tomassasovsky/segno/docs/code-review/fx-design-alignment/review.md

# FX design alignment review

Base: `6646086a5be2e7c9135b4f01fd0464e316154082`.
Scope: two presentation files and six reviewed screenshot baselines, plus plan
and this record. The implementation adds nine net production lines.

Independent review read the complete source change, traced the fixed-canvas
constraints and unchanged pages, and compared all six candidate images with
the accepted Current UX Pen frames. A separate render used the complete bundled
catalogue. No actionable finding remains in this scope. Leading controls retain
their label constraints; actions reach the right inset; only the library artwork
grid is centered. Existing scroll ownership and My presets geometry remain.

Reviewed production SHA-256 values:
- `fx_page.dart`: `600ef9a996370b7b68edfea4cb823a4cc9db3b2d040eb193032fcadd9f24305c`
- `fx_library_page.dart`: `e1b4ac0d3c2e7cbb04936d7b0df2e91ceb75f2f6224945bef6ff3045594cc11a`

Validation: 81 existing FX behavior tests and all 11 author screenshot cases
pass. The complete app suite passes 2869 tests with six skips; strict analyzer,
explicit formatter and Bloc lint (789 files) are clean. Only the six inspected
baseline images changed. CI remains a separate current-head gate; author images
depend on local fonts and do not constitute appliance validation.

The campaign's requested additional Claude review remains outstanding because
its session limit prevented a verdict. Keep that review gate pending. These
results certify the bounded horizontal correction, not a theme-wide redesign.
