tomassasovsky/segno/docs/code-review/design-midi-controls-restack/review.md

# MIDI bug-focused review

## Current correction binding

The reviewed test-only correction builds on published head
`1c7c07ebbce9ed87130e9484d259aed05cc7f616`. Its independent source and five-role
review is clean; the single timing-fixture finding was fixed with deterministic
capture timestamps. All application/native bytes below are unchanged.
The effective manifest fingerprint is
`755a00187a8e6064d218fd552e9581513249d160c9108d3dcf145dc255c3f936`.
The ordinary app run passes 2,306 tests and 90.0039% coverage, with static gates
clean. The original 89.07% CI failure remains recorded; new published-head CI
must pass before readiness. See [verification](../../reviews/design-midi-controls-restack/verification.md).

## Original application/native review

Base and current Git HEAD: `1ef7fb30abd328b86ac481ec71e72c9bbc59e83c`. Reviewed the intended working diff and untracked product files, then all repair and fixture deltas. Exact hashes, fingerprint and the complete scope are in [the source report](../../reviews/design-midi-controls-restack/source-review.md#reviewed-file-binding). A later commit must be bound to these bytes.

One independent reviewer performed source inspection and the five quality roles sequentially; this is not five independent reviewers. No tests, product edits, delegation or UI automation were performed by that reviewer. Root and the independent adversary supplied execution evidence.

The local source and quality gate is **clean** for the exact 134-path manifest fingerprint `3cb49b9c0e522f35d7275b5b58a6a30095a4f8350c161796bb48f3806c2be705`. All eleven functional findings and the final future annotation are resolved; no actionable finding remains. Final app, package, native and static evidence passes. Published-head CI and final commit binding remain separate, pending gates. No ready-to-merge, merge or deployment claim is made.

## Findings

Eleven actionable functional findings were repaired and independently reread. They covered Mixer Reset ownership, ordinary writers, pending persistence, endpoint editing, capture timing, session-crossing queued work, FX activation authoring, non-held retirement, Stage navigation, stale monitor persistence and pending confirmation disposal. See [repair traces and the removed-invariant audit](../../reviews/design-midi-controls-restack/source-review.md#findings-and-repair-verification).

Completed changed-source/enclosing-function review, cross-file tracing, deleted guard/test audit, failure and lifecycle review, native/FFI parity review, reuse/simplicity review and final fixture assertion review. No functional source finding remains unresolved. No review task was delegated or failed. Scope and physical/visual limitations are explicit in the source report.

The local gate is complete at the recorded manifest. The coordinator must bind the resulting published commit to those bytes; current-head CI is separately required for ready-to-merge. M3 catalogue follow-on and later M4–M6 owners remain incomplete campaign work.
