tomassasovsky/segno/docs/reviews/design-midi-controls-restack/pr-readiness-review.md

# MIDI PR-readiness review

Base and current Git HEAD: `1ef7fb30abd328b86ac481ec71e72c9bbc59e83c`. This is a working-tree review; a later commit requires the coordinator to bind the resulting commit to these reviewed bytes. Exact intended-path hashes and scope are in [the source review](source-review.md#reviewed-file-binding).

One independent source reviewer performed the VGV, architecture, test-quality, simplicity and readiness roles sequentially. These are five review lenses, not five independent reviewers. No delegation, product edits, test execution or UI automation was performed by this reviewer. The coordinator and separate adversarial reviewer supplied execution evidence.

The local source and quality gate is **clean** for the exact 134-path manifest fingerprint `3cb49b9c0e522f35d7275b5b58a6a30095a4f8350c161796bb48f3806c2be705`. All eleven functional findings and the final future annotation are resolved; no actionable finding remains. Final app, package, native and static evidence passes. Published-head CI and final commit binding remain separate, pending gates. No ready-to-merge, merge or deployment claim is made.

## Mechanical evidence

- Source whitespace/conflict checks: `git diff --check` passed; no newly introduced debug print, TODO/FIXME/HACK or merge marker was found in reviewed changed product source.
- Format: aggregate check reports no changes; focused final fixture check also reports five files, zero changes.
- Strict analysis: final run passed with zero issues. The tracked future removed in confirmation cleanup is explicitly `unawaited`, preserving execution without awaiting itself.
- Bloc lint: final aggregate passed with zero issues and an observed positive scan of 703 files; this was not an ignored-worktree no-op.
- Tests: unchanged native/package gates pass. Final app aggregate passed 2,433 tests with six existing explicit skips and 90.857% coverage against a 90% floor. The earlier failed/stalled run was superseded. After the sole annotation-only delta, both disposal regressions passed again.
- History: current HEAD is the External predecessor and this candidate is uncommitted. Commit/PR head binding, issue/label mechanics and current-head CI are coordinator responsibilities after publication.

Transient macOS build edits are excluded/restored. Required screenshot/Pen assets are intentional, and their visual approval belongs to the coordinator's separate evidence. No merge or deployment readiness is claimed.
