tomassasovsky/segno/docs/reviews/design-midi-controls-restack/simplicity-review.md

# MIDI simplicity review

Base and current Git HEAD: `1ef7fb30abd328b86ac481ec71e72c9bbc59e83c`. This is a working-tree review; a later commit requires the coordinator to bind the resulting commit to these reviewed bytes. Exact intended-path hashes and scope are in [the source review](source-review.md#reviewed-file-binding).

One independent source reviewer performed the VGV, architecture, test-quality, simplicity and readiness roles sequentially. These are five review lenses, not five independent reviewers. No delegation, product edits, test execution or UI automation was performed by this reviewer. The coordinator and separate adversarial reviewer supplied execution evidence.

The local source and quality gate is **clean** for the exact 134-path manifest fingerprint `3cb49b9c0e522f35d7275b5b58a6a30095a4f8350c161796bb48f3806c2be705`. All eleven functional findings and the final future annotation are resolved; no actionable finding remains. Final app, package, native and static evidence passes. Published-head CI and final commit binding remain separate, pending gates. No ready-to-merge, merge or deployment claim is made.

## Assessment

The current layers earn their roles: protocol assembly decodes messages, mapping proposals retain per-control admission/cleanup, the application ledger orders accepted targets, and shared persistence projects durable Released values. Combining them would obscure independent lifetime and storage constraints. No generic framework or compatibility path was added.

The unused exported `MidiSignalLevels` duplicate was removed, with no remaining caller/export. Obsolete mapping models, default dispatch and generic Learn UI were removed as requested. Exact holder identities, epochs and pending-save receipts are necessary to prevent reproduced races; their removal would lose behavior rather than simplify it.

No further actionable redundancy or YAGNI finding remains. No LOC reduction target is proposed. Required production fakes, `AudioEngine` interfaces, generated bindings and visual assets are explicitly preserved under project authority. The final future annotation is explicit and requires no broader refactor.
