tomassasovsky/segno/docs/code-review/design-pedal-art-restack/review.md

# M3.7 pedal artwork source review

Complete for the six-file art freeze-v1, fingerprint `447437f12e2729a08b35f081f8f77c85e1871f838af4d2581433e7155ec60ed4`. Critical: 0. Important: 0. Suggestions: 0. No unresolved actionable source finding.

One independent reviewer performed the bug-focused review and all five quality roles sequentially. These are five perspectives, not five independent agents. The author and bounded adversarial reviewer are separate. No product edits, tests, builds, Git mutations or recursive delegation were performed by this reviewer.

## Scope and source binding

Baseline: `170167520c0de2d6a480637393b19a2bda6f594c`. Original PR 1034 source: `ef50473b1704289a8a0daf3178a2368efe8dcca7`. All six frozen file hashes were checked at finalization with no mismatch. The retained setup map and physical legend source match their prior independent bindings. Parent-owned Pen/golden updates and aggregate verification are a separate packet; this source review does not predeclare their result or exact-head remote CI.

Read the full painter before and after the port, the literal JavaScript art source, geometry/label provenance, README, new raster tests, enclosing map and focus/LED ownership. The four study files originally matched the independent original hashes. Final study changes are limited to fresh white RGB FFFFFF in the decorative indicator and documentation identifying the current Flutter host; geometric and label source data remain unchanged.

## Completed review angles

The executable seven paths match the accepted 84×114 study: tapered body, both curved hinges, both rolled edges, quadratic pad and trapezoid nameplate. Exact grip grid is five columns by six rows, pitch 11.6373×12, origin y=39.47, base radius 4, top radius 3.1 lifted 0.18. Hinge, pad and grip strokes and body-before-roll paint order are restored. Selected/unselected material stops and edge widths match the source values.

The existing PedalHardwareFace is the sole renderer. Cached paths are initialized once and never transformed or otherwise mutated. Cached metal and grip shaders are reused; each translated grip has a balanced canvas save/restore inside the outer scale save/restore. The selected flag remains the repaint dependency. No speculative cache framework or public test-only API is added.

The widget's existing label, AspectRatio, layout and theme-based text are retained. Production supplies its proportional 159.16×216 face box inside the larger existing slots. Dynamic numeric labels remain 1–8 in banked editing and 1–4 in physical LED editing; accessible legends remain owned by the enclosing map. Manufacturing-outline lettering parity is intentionally not claimed. Label paint after the decorative grips has no visible ordering conflict because the fitted label remains within the nameplate above the grip rows.

Map bounds remain 1720×566, rear slots 168×216 at x=451/668, y=30 and front slots 201×216 at y=350, pitch=217. Painting adds no focus, tap, controller or repository owner. Existing full-slot hit targets, availability, group selection, warning layout and separate LED pills are unchanged. Canonical activation, local palette preview and mismatched draft-bank suppression remain exclusively in the map.

Removed behavior is limited to approximate rounded hinges and repeated path/shader construction. No guard, gesture path, persistence boundary, native API, protocol or palette behavior was removed. No new dependencies or lower-layer imports appear. The change adds bounded paint work only; no callback/thread/FFI path is involved.

## Evidence and limits

Observed author raster test log: three tests pass, checking actual interior pixel colors, all 30 grip locations and selection changes. This replaces the original PR's insufficient comment-string style of proof. The builder reports clean targeted analyzer/format/whitespace. The initial image-capture stall was a test fixture async issue, retained in its original log and corrected with tester.runAsync; no production workaround was added.

The source review is clean within the six-file freeze. Independent scale/repaint/interaction probes, sensitivity evidence, final visual inspection, Pen/goldens, broader static/tests/coverage and publication-head CI remain parent-owned separate gates. No failing reviewer was substituted by this source review.

Exact raster equivalence to the browser study is not asserted: dynamic font-rendered labels are intentional, and the retained Flutter metal shader spans the art box while SVG object-bounds gradient normalization differs slightly. Geometry, material values and paint order are the bounded parity claim. Generic forced nonproportional sizing is not a new supported requirement; production uses the existing proportional box.

No new CAD accuracy, physical display comfort, hardware touch response, appliance visibility, optical/current or device validation is claimed. `autonomy:merge-gate` remains in force. This report does not authorize merge or set ready-to-merge before exact-head CI is green.

## Coordinator closeout

The final source binding and verification record are in
`docs/reviews/design-pedal-art-restack/`. The separate adversary has completed
all four groups with no findings. The coordinator verified the nine updated
goldens, running app, saved Pen component and note, and unchanged source during
the aggregate run. All local gates above passed; remote CI remains pending
on the published head. This closes the earlier parent-owned pending local
gates without claiming additional independent reviewers or hardware proof.
