tomassasovsky/segno/docs/reviews/design-pedal-art-restack/code-simplicity-review.md

# Code simplicity review

Complete for the six-file art freeze-v1, fingerprint `447437f12e2729a08b35f081f8f77c85e1871f838af4d2581433e7155ec60ed4`. Critical: 0. Important: 0. Suggestions: 0. No unresolved actionable source finding.

One independent reviewer performed the bug-focused review and all five quality roles sequentially. These are five perspectives, not five independent agents. The author and bounded adversarial reviewer are separate. No product edits, tests, builds, Git mutations or recursive delegation were performed by this reviewer.

Purpose: improve the current hardware face's fidelity to the accepted simplified study while preserving current app behavior.

One existing painter now has seven private cached paths and three cached shaders. Small paint helpers express source layering. Shared grip-local shader translation avoids thirty equivalent shader allocations per face; no cache invalidation system or speculative abstraction is added. The current dynamic label widget is retained rather than importing static manufactured outlines that cannot label bank B.

No justified removable lines or duplicate renderer were identified. Estimated removable LOC: 0. Complexity: low; the increased path data directly implements accepted outlines and remains separated from interaction. Already minimal for this scope.
