tomassasovsky/segno/docs/code-review/design-pedal-led-restack/review.md

# M3.5 source and quality review

Bound to freeze-v2 fingerprint `57dcdae120419b771c9bf8ad43d7cd9c976ccaf39ce28a7cf18e884c78ffef2c` (69 paths); base `3e67d031148f21eb9c3ee99a961f6ca4587dbc3b`, intended merge parent `424e12d0e53a969f8887089be0ea9450404be969`. All source hashes were independently compared with the frozen packet and match. One implementation-independent reviewer performed source review and all five quality roles sequentially; the roles share a reviewer and are not five independent reviews. No implementation edits, tests, builds, staging, publishing or hardware operations by this reviewer.

## Result
No unresolved actionable source findings in the frozen diff. All source angles and all five quality roles completed. Source and local software review gates are clean. All aggregate/static/coverage checks and independent adversarial probes pass on the bound frozen candidate. Exact published-head CI and merge authorization remain owned by root.

## Reviewed scope and evidence
The complete intended working-tree diff, new test/stub files, binary fixtures, screenshot goldens, surrounding state/gesture/repository callers and removed invariants were inspected. Accepted behavior§4, the pinned PR1079 renderer architecture and frozen independent oracle governed the review. Exact reviewed paths/hashes are in source-binding.json.

Line-by-line scan, removed-behavior tracing, cross-file API/serialization/UI flow, reuse, simplification, efficiency/lifetime, mechanism depth and project conventions are complete. Exact8 HELLO admission, STATE51/frame55, all-ten raw RGB plus LE16mask, old field validation, bounded parser capacity and unchanged CTRL/HELLO formats are consistent in C/Dart. No fallback or incompatible historical layout is accepted. Frame inputs are detached, physical output follows only the mask, and goodbye dominates activation.

The renderer is directly compared with PR1079 ecea3af76fdb0708ca04632e260de5aa3fde09cd. The whole40pixel sustained ring, limits, pin map, CTRL, encoder and DMA boundary are retained. Intended differences remove Song/local-contact/idle-breathe pill inference, consume host hues/mask and change firmware metadata. NeoPixelBus2.8.4 sending/editing buffer ownership was inspected directly; stack desired colors do not escape and DMA cannot read overwritten editing data. Current limiting rebuilds from source pixels and forced refresh cannot progressively dim. No audio callback/native/FFI change is in scope.

## Findings resolved during review
- Refused Custom transport actions formerly recorded completion/contact before dispatch. Actual synchronous or awaited admission now gates identity/contact, with per-button tokens preventing delayed results from attaching to another contact or invalidated configuration/session.
- Disconnection formerly published raw held contacts before clearing them. Raw/accepted contacts and clear state now clear before projection; reconnect does not replay held LEDs.
- Accepted Layout A originally lit the selected edit pill and never consumed the frame. Repository frame publication through PedalCubit now supplies the actual map, preserving selected decoration independently and guarding draft-bank mismatch.
- During admission repair, normal Undo and supported FX Stop pathways were rechecked. FX panic/binding/Restore Hold and Mute Stop now use actual outcomes for contact LEDs, including refusal tests.

## Quality roles
See vgv-review.md, architecture-review.md, test-quality-review.md, simplicity-review.md and pr-readiness-review.md. All report Critical0/Important0/Suggestion0; readiness limits are explicit. Roles share this one implementation-independent reviewer.

## Limits
This reviewer ran no tests/builds and changed no implementation. Builder/root logs and independent adversary evidence are attributed accordingly. Desktop source/tests/Arduino compilation cannot establish electrical current, real timing or optical appearance. Palette add/edit/reuse/persistence remains1032. No flash/deployment/merge is authorized by this report.

## V2 fixture rebind
The first full run exposed one obsolete positive Clear-LED fixture using an empty rig, and strict analysis found one cascade style issue in a new repository test. Reviewed exactly two test-only changes: positive Clear now has a real48000-frame track and a separate empty-rig case asserts darkness; the repository cascade preserves call order/behavior. Every production source hash is unchanged. All69v2packet paths match. Prior failures are retained in verification-v1; complete v2 gates pass. Root's native-app author journey also confirms real Layout A live state, distinct edit selection and draft-bank isolation; it is not independent hardware evidence.

## Final observed verification
Read exact result logs and independently rechecked all69frozen hashes at finalization; no drift. Root verification-v2/dart-result.json reports complete app tests exit0/semantic pass in86.7s and pedal_repository exit0/semantic pass in4.4s. Coverage-results.json records app19860/21794=91.126% against90% and pedal563/576=97.743% against96%. Static-results.json records explicit formatter, fatal-info analyzer, Bloc and whitespace checks all exit0/semantic pass; Bloc log confirms0issues across665files, with the path alias bound to the intended checkout. These were root-run, not repeated by this reviewer.

Read the separate adversary's final review and binding: one C literal executable, one actual-sketch pixel executable, two Dart codec/value tests and eight app/repository cases pass; no unresolved findings. Production hashes remain unchanged, with the two reviewed test-only amendments rebound to v2. That reviewer discloses one corrected close-await harness issue separately from product behavior. Exact source, result and receipt hashes are in source-binding.json and verification-binding.json.

The local source/software gate is clean for this packet. Current-head remote CI is not claimed before publication; merge-gate and actual hardware limits remain unchanged.

Final test totals:2346app tests passed with6existing skips;213pedal_repository tests passed. No added skip hides the changed behavior.
