tomassasovsky/segno/docs/code-review/design-custom-runtime-restack/review.md

# M3.4 complete source bug review

Base `cce88c32d03538c61bafeb64d89369b5aef708ac`; incoming intent `27efe48a9ca3871c85b4e307e3638fd20a49b604`. Reviewed the final 46-path M3.4 working candidate bound by freeze-v2 fingerprint `db724af132b964dde4e1ee883765f05b2bdc5e65022b7ffacba77339e502db12`. All paths reconciled without drift. One independent non-author reviewer performed the five quality roles and bug pass; these are not five separate reviewers. Earlier native/package authorship is outside this delta. Product source, tests and Git were not edited by this reviewer.

Verdict: no unresolved actionable findings in the bounded final source. The full bug pass is complete for this candidate.

Completed line-by-line changed-hunk review; removed-guard/invariant tracing; cross-file UI, model, gesture, mix, repository and wire caller tracing; lifecycle/error/bounds review; reuse and simplification; allocation/queue-efficiency review; fix-depth and AGENTS convention checks. No native callback or FFI change exists in this delta. The separate adversary's 16 real-pump/shared-owner cases pass and its final binding reconciles to the frozen runtime.

Candidates resolved before completion:

- Separate all-track Solo admissions could refuse later tracks. Shared coordinator queueing now submits the group together; repeated and overlapping group toggles retain parity and ordering with GUI Solo/Clear.
- Completed selected targets could remain pinned after release. Current projection retains the fired target only through contact, then resolves selection again. Transport feedback is contact-only; Hold retains its own function identity.
- Newly exposed Custom recovery actions could collide with a long header warning. Warnings now occupy the gap between pedal rows; the combined recovery regression verifies bounds and reachable actions.
- Restoring a cleared Custom map could discard later Track-controls edits. Restore now replaces only Custom assignments; the cross-context regression preserves the newer edit.

Preserved current contracts include fresh Mute/Custom defaults, explicit saved FX doors, fixed immediate Custom Exit/Bank, inert unavailable actions, fire-time bank/selected targets, current-session cancellation, exact setup Save/rollback, normal immediate transport and existing FX held-release ownership. Unsupported later functions remain unavailable. Six setup images and the saved design annotation were independently inspected; hardware and whole-product visual acceptance remain outside this source gate.
