tomassasovsky/segno/docs/reviews/shared-record-timing/raw/architecture-f1-f4-delta-v1.md

# Architecture delta review — F1–F4 and final App retry

Sequential read-only perspective by the same reviewer as the VGV/simplicity/test-quality delta reports; no distinct-person claim. Base `8749688c51912f808c3f36d4eb5bca665ede3ade`. Runtime fingerprint `f2af6a80afaaa6b13c8b0e63881d3da8c23ad121db7b686f4cb3ee1c66eeca2d`; root App/test SHA-256 `b5b3f55449a0263109823971811559f5f367210b8f65fbb0947da0a5de04d131` / `0d0860b325f8180abfd2eda1f196a7220e7a8c6e6657d190d199fef2d2edf977`. Exact private binding: `quality-f1-f4-delta-binding-v1.json`. No execution or edits.

**No new architecture violation in the changed seams.** `ControlCubit` remains the only MIDI/External dispatch ledger; `ControlCleanupPending` is a typed result of its retirement gate, not another owner or persisted state. The App interprets that result only in its Power Off orchestration: it recovers owners then requires the same controller gate again. `RecordTimingCubit` still owns storage and native settlement; F1 corrects its flush result without moving writes to presentation. `LooperRepository.record` now refuses an ineligible fresh acquisition before composing plugin state, and the native preflight remains the final callback/producer boundary. F2 changes only a native test, not native production APIs or memory ownership.

Root's toast change reads its already-owned `PowerOffCubit` phase and leaves the error logged. It neither reaches a data client from presentation nor makes toast state authoritative for the transaction. The shared App provider graph and Session lock order are unchanged by these repairs. The separately bound App source is the final v8 toast-lifecycle revision; the earlier e3b7059e App read is superseded. Its power-state subscription is disposed with the App state. Product/native test execution and published CI remain outside this source review.
