tomassasovsky/segno/docs/reviews/design-fx-surfaces-restack/raw/architecture.md

Independent reviewer: m2_fx_native. Base: a52fe34d42a719624762f7756518a7e54cf7fd0c. Bounded scope: changed lib/** and root test/**. This reviewer authored package/native work and expressly excludes all packages, generated FFI and manifests from independent-review credit. Domain/native contracts were read only to trace UI callers. No repository edits, broad test/build runs or screenshot generation were performed in this review phase.

Final source binding: final-v4-hashes.json, SHA256 731cf62a54934b392970384f4c56545bda4c700d1f0d0227560f0ca8f4cf6486. Initial, intermediate and final source snapshots/diffs are retained; all production/test deltas were reconciled. Key hashes: Bloc 24fe22ba, FxCubit eef07fb9, FxPage 9555caad, Monitor 5169080c, Event d073149b. Broad release checks and exact-head CI are root-owned and are not implied by this bounded review.

# Architecture review

Verdict: no unresolved actionable finding in the final bounded UI architecture.

FxDestination distinguishes live input, recorded lane, whole track, All tracks and output identity. Structural edits dispatch through their established Cubit/Bloc owner; the UI does not call AudioEngine. Output startup restores complete envelopes, session mapping keeps per-bus keys, and synchronization clears obsolete destinations. Structural persistence remains gated on exact recipe settlement. Stable slot IDs drive control resolution rather than falling back to a different slot index.

The Add transaction composes from the current repository chain, refuses overflow atomically, and opens only its fresh acknowledged identity after projection. Its original projected generation remains attached to the operation; the existing Bloc exposes only a boolean liveness predicate. The temporary FxCubit repository dependency and helper are removed; original page construction remains intact. No extra stream, state store or persistence owner was introduced.

Review/ack-lifecycle/result.json supplies six independent actual-pump setChain lifecycle groups. Review/append-lifecycle/result-v2.json supplies six append groups, including the unchanged formerly failing full-chain oracle and authoritative monitor-composition neighbor. Native pump remains 31ebe531...; this reviewer inspected those reports, not reran their probes. The final lifetime amendment leaves confirmed setters, append guards and recipe receipts unchanged. Exact reconstruction hashes in final-predicate-amendment.json and final-monitor-amendment.json prove this; the predicate adds a closed-Bloc guard and Monitor amendments are comments/ignores only. FxPage is byte-identical to the passing append-probe source. Final navigation source and widget cases were separately reconciled here.

Final reconciliation: root confirmed the source freeze. All bounded production/test deltas, including the new stale-at-library-open regression, were reread and final-v4-hashes.json matches current files. Root reports the live Mac journey now opens newly added single/rack editors directly and Stage returns to Mixer with the tray closed. That is root journey evidence; an earlier pre-hot-reload 91px RenderFlex warning remains separately recorded, so this report does not claim universal viewport validation. Final static evidence is complete: explicit 649-file format check, strict analyzer, actual 649-file Bloc lint and whitespace checks all pass, with no source drift. The final focused run passed 190 tests. Root's explicit full-app reuse amendment preserves the earlier 2,229 passes, six existing skips and 91.07% coverage; no rerun of that entire suite on final bytes is claimed.
