tomassasovsky/segno/docs/reviews/design-fx-surfaces-restack/raw/common-files-review.md

# M2.6 common configuration and screenshot-fixture review

Base `a52fe34d42a719624762f7756518a7e54cf7fd0c`. Read-only review of `.github/cspell.json`, `.github/workflows/main.yaml`, root dependency manifests, app engine fake and the changed root screenshot Dart fixtures. Exact hashes and removed/golden inventory are in `common-files-source.json`. No tests, screenshots or implementation edits were performed in this pass.

No actionable finding in this bounded scope. Whole-candidate readiness remains pending final app/UI review, strict static/full app gates, root visual evidence, exact commit binding and current-head remote CI.

- The new `fx-catalogue` CI job targets `packages/fx_catalogue`, uses the same Flutter version as root/domain jobs, keeps the reusable workflow and enforces 100% coverage. Disabling Bloc lint for this data-only package is consistent with the other repository jobs; no root lint/test/coverage gate is weakened. The observed catalogue v2 result is semantic pass, 21 named tests, 88/88 covered lines; saved LCOV hash matches the result. This verifies local evidence, not the not-yet-run current-head remote job.
- Root pubspec and lock add only the local catalogue dependency. The package asset declarations already reviewed include all selector/strip/footswitch/stomp directories and the nine preset families. Added spell words are narrow terms/asset slugs; no additional file exclusion or disabled spelling rule was introduced.
- The engine fake now keys all output types/counts/params/power by bus, removing the prior silent no-op for nonzero buses. Existing separate atomic-recipe fake behavior is unchanged. This improves address fidelity; the fake remains a unit-test seam, not evidence of native rendering or admission. The independent four-output PCM probe supplies that separate evidence.
- Control-center/settings fixtures replace the old master accessor with output bus 0 and supply All-tracks/per-output state. Explicit outputBusCount keeps the fixture coherent. The obsolete chainEntriesAt mock is removed; current address-specific getters remain stubbed. No assertions for surviving controls are removed in these hunks.
- Seven deleted Signal golden cases correspond to the intentionally retired Signal destination, its stage tabs and editors. New FX goldens cover Live inputs, Recorded whole track, All tracks, Outputs, direct effect editor, racks/rack editor/options/reorder, My presets and library. Current ordinary FX widget tests cover destination switching, returning to Whole track on track change, fixed All-tracks placement and empty-chain state. This is replacement surface coverage, not a claim that eleven pictures alone preserve every old behavioral test. The other independent UI reviewer owns complete removed-behavior/caller validation.
- `settleArtwork` enumerates displayed Image providers, awaits their precache futures under runAsync, collects and asserts image errors, then pumps before capture. It is used after initial surface loading and newly opened artwork-bearing editors/library/presets. It eliminates a decode-timing assumption without swallowing missing-asset errors or changing expected pixels. New screenshots remain explicitly author-machine/font-gated, like existing suites; they are not represented as portable CI visual evidence.
- Settings recording and surviving control-center golden bytes changed. This pass records those hashes but does not certify their pixels; root visual inspection/final regenerated golden evidence remains required. No screenshots were generated or viewed during this source-only task.

## Domain gate amendment

The final narrow preset decoder catch was included in `verification-domain-final/looper_repository-result.json`: exit 0, semanticPass true, 6.9 seconds; the associated raw JSON run has successful completion and no failed test result, and source-before/source-after match. The earlier failing malformed-row probe remains preserved, followed by the unchanged passing independent replay. The package subset review may now reuse this current-input Looper aggregate. Other packages still require the root's explicit dependency/input reconciliation after the model amendment; no blanket unchanged-input claim is made here.
