tomassasovsky/segno/docs/plan/2026-10-06-feat-pitch-time-core-plan.md

# Pitch and time core: Speed, Transpose, Audio & tempo follow, import Adapt

<!-- cspell:ignore varispeed lerp lbuf wdub Signalsmith signalsmith numer SCHED untransposed sidelobe retiming Retiming retimes retimed retime reclock regrid halfband Neoverse milli fmod crossfades hujm YMPRG Bmpo -->

Status: approved with required review edits E1-E15, which are applied in this
text (the review is kept at the owner's evidence store,
`claude-published-review/1179-plan-review/review.md`). Part 1 is a measured
CPU spike whose numbers gate the rest.
Tracking: #1179 (parent #1026; gap inventory E4-1, serving E6-4 Speed, E6-5
Transpose, E4-2 Audio & tempo, E7-9 import Adapt), `autonomy:merge-gate`.
Source baseline: `origin/claude/segno-integration` at `c3714abc2`. Every
`file:line` below is on that head unless a branch is named.
Precedents: Foot Fade ([plan](2026-10-04-feat-foot-fade-plan.md)), Foot
Reverse (`origin/claude/reverse-plan-1162:docs/plan/2026-10-05-feat-foot-reverse-plan.md`),
the whole-track render boundary
(`docs/design/2026-09-10-whole-track-pre-render.md`), the stem provenance plan
(`2026-10-05-feat-stem-history-replay-plan.md`), the engine reopen plan
(`2026-10-05-feat-engine-reopen-plan.md`), and the July stretch spike
(`2026-07-22-time-stretch-spike-findings.md`).
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
