tomassasovsky/segno/assets/brand/segno-lockup.png

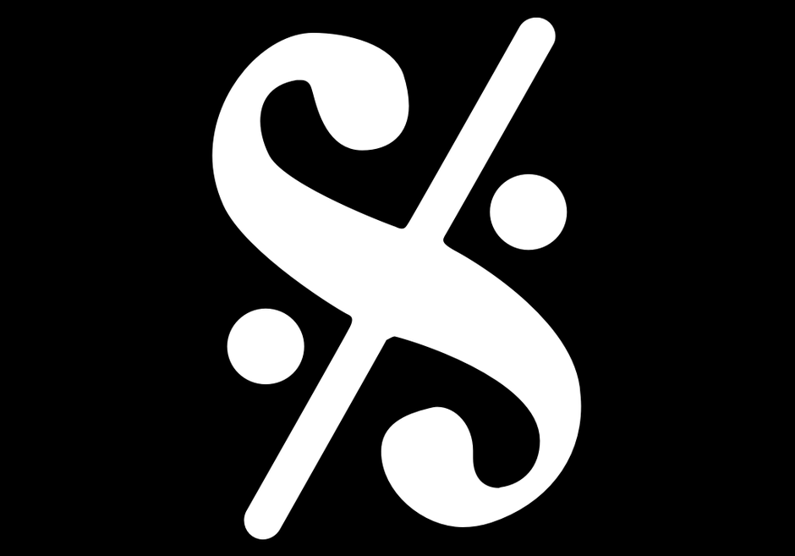
assets/brand/segno-lockup.png
