tomassasovsky/segno/assets/settings/device.png

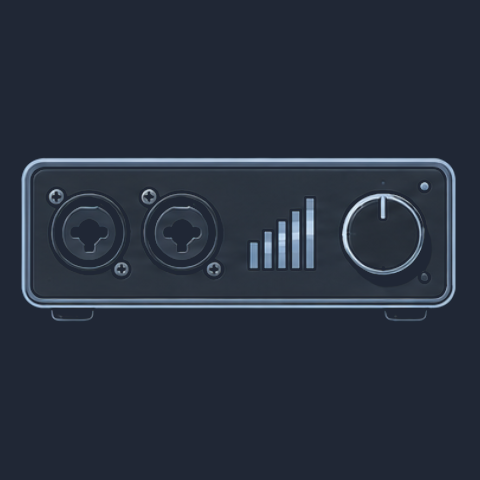
assets/settings/device.png
