tomassasovsky/segno/assets/settings/displays.png

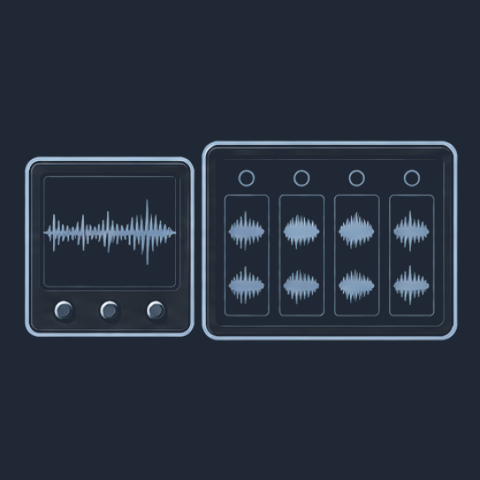
assets/settings/displays.png
