tomassasovsky/segno/assets/settings/effects.png

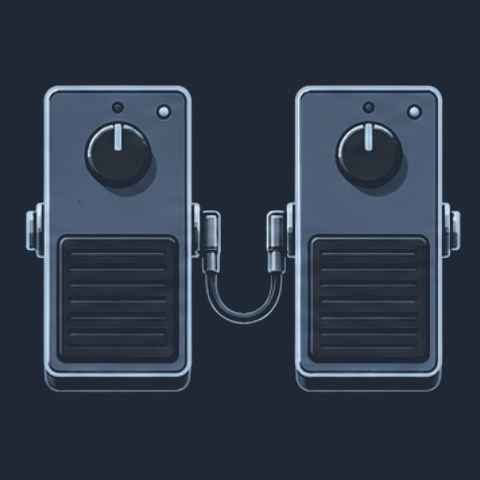
assets/settings/effects.png
