tomassasovsky/segno/assets/settings/loop.png

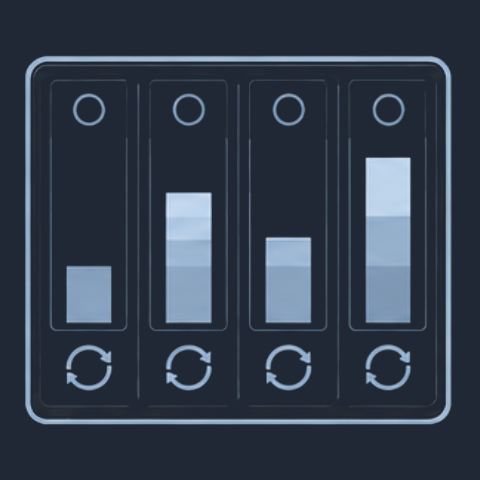
assets/settings/loop.png
