tomassasovsky/segno/assets/settings/midi.png

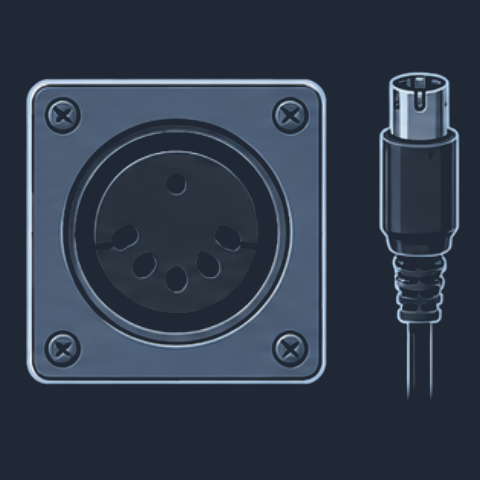
assets/settings/midi.png
