tomassasovsky/segno/assets/settings/network.png

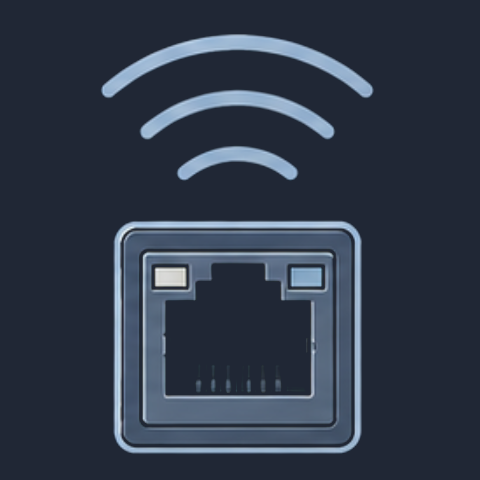
assets/settings/network.png
