tomassasovsky/segno/assets/settings/pedals.png

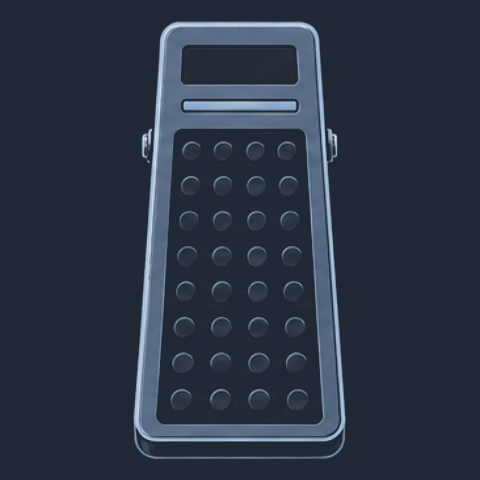
assets/settings/pedals.png
