tomassasovsky/segno/assets/settings/routing.png

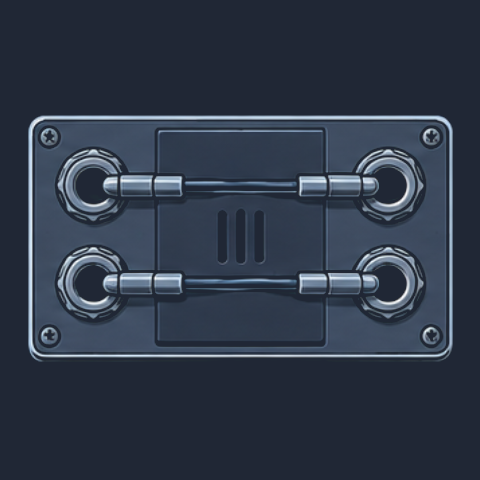
assets/settings/routing.png
