tomassasovsky/segno/assets/settings/storage.png

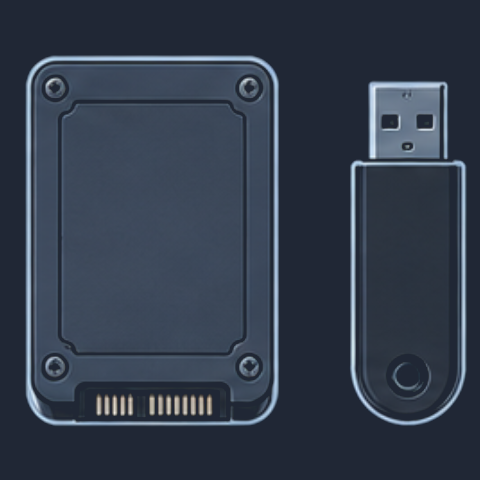
assets/settings/storage.png
