tomassasovsky/segno/assets/settings/updates.png

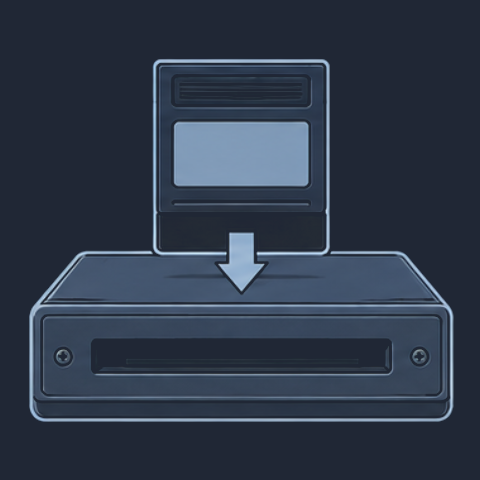
assets/settings/updates.png
