tomassasovsky/segno/docs/design/native-record-start/recording_pedal_off.png

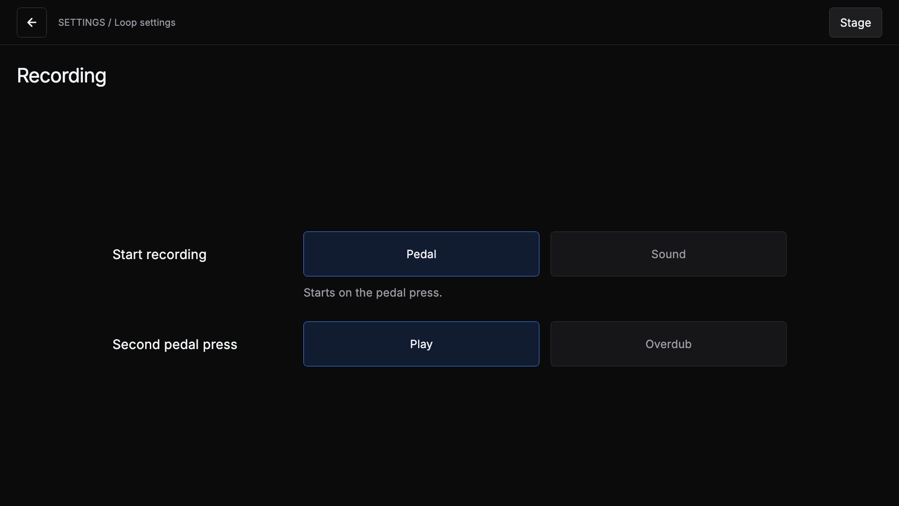
docs/design/native-record-start/recording_pedal_off.png
