tomassasovsky/segno/packages/fx_catalogue/assets/images/footswitch/drum.png

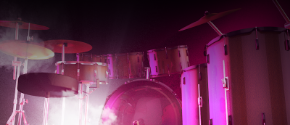
packages/fx_catalogue/assets/images/footswitch/drum.png
