tomassasovsky/segno/packages/fx_catalogue/assets/images/footswitch/dub.png

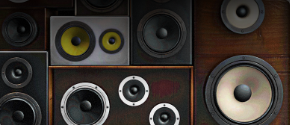
packages/fx_catalogue/assets/images/footswitch/dub.png
