tomassasovsky/segno/packages/fx_catalogue/assets/images/footswitch/edsguitar.png

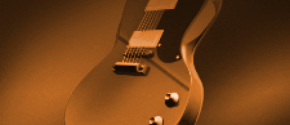
packages/fx_catalogue/assets/images/footswitch/edsguitar.png
