tomassasovsky/segno/packages/fx_catalogue/assets/images/footswitch/guitar.png

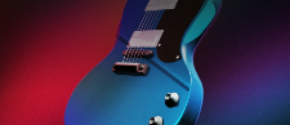
packages/fx_catalogue/assets/images/footswitch/guitar.png
