tomassasovsky/segno/packages/fx_catalogue/assets/images/footswitch/lo-fi.png

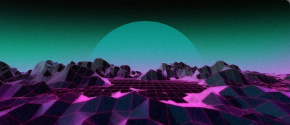
packages/fx_catalogue/assets/images/footswitch/lo-fi.png
