tomassasovsky/segno/packages/fx_catalogue/assets/images/footswitch/rhythmic.png

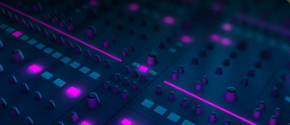
packages/fx_catalogue/assets/images/footswitch/rhythmic.png
