tomassasovsky/segno/packages/fx_catalogue/assets/images/footswitch/studio.png

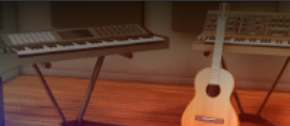
packages/fx_catalogue/assets/images/footswitch/studio.png
