tomassasovsky/segno/packages/fx_catalogue/assets/images/footswitch/vocal.png

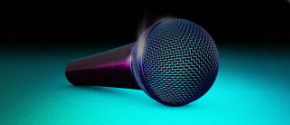
packages/fx_catalogue/assets/images/footswitch/vocal.png
