tomassasovsky/segno/packages/fx_catalogue/assets/images/footswitch/vocaltuner.png

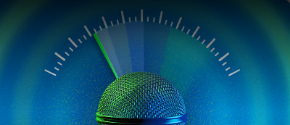
packages/fx_catalogue/assets/images/footswitch/vocaltuner.png
