tomassasovsky/segno/packages/fx_catalogue/assets/images/selector/drum.png

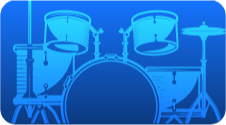
packages/fx_catalogue/assets/images/selector/drum.png
