tomassasovsky/segno/packages/fx_catalogue/assets/images/selector/dub.png

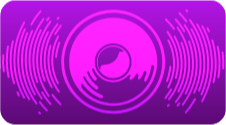
packages/fx_catalogue/assets/images/selector/dub.png
