tomassasovsky/segno/packages/fx_catalogue/assets/images/selector/edsguitar.png

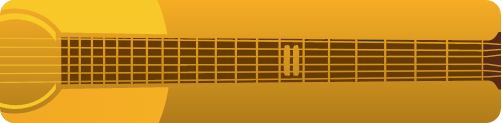
packages/fx_catalogue/assets/images/selector/edsguitar.png
