tomassasovsky/segno/packages/fx_catalogue/assets/images/selector/guitar.png

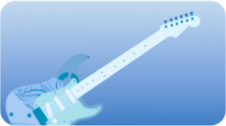
packages/fx_catalogue/assets/images/selector/guitar.png
