tomassasovsky/segno/packages/fx_catalogue/assets/images/selector/lo-fi.png

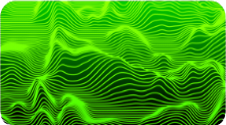
packages/fx_catalogue/assets/images/selector/lo-fi.png
