tomassasovsky/segno/packages/fx_catalogue/assets/images/selector/my-presets.png

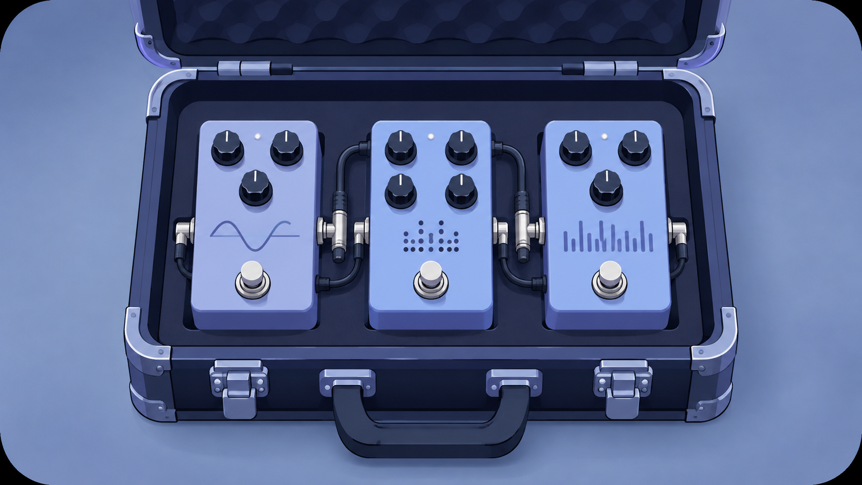
packages/fx_catalogue/assets/images/selector/my-presets.png
