tomassasovsky/segno/packages/fx_catalogue/assets/images/selector/rhythmic.png

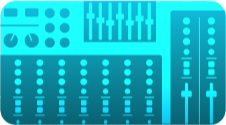
packages/fx_catalogue/assets/images/selector/rhythmic.png
