tomassasovsky/segno/packages/fx_catalogue/assets/images/selector/singlefx.png

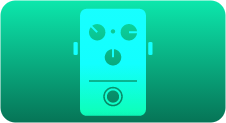
packages/fx_catalogue/assets/images/selector/singlefx.png
