tomassasovsky/segno/packages/fx_catalogue/assets/images/selector/studio.png

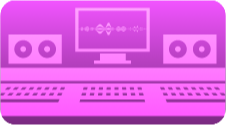
packages/fx_catalogue/assets/images/selector/studio.png
