tomassasovsky/segno/packages/fx_catalogue/assets/images/selector/vocal.png

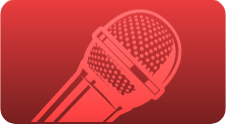
packages/fx_catalogue/assets/images/selector/vocal.png
