tomassasovsky/segno/packages/fx_catalogue/assets/images/selector/vocaltuner.png

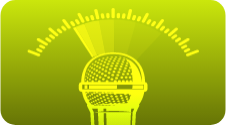
packages/fx_catalogue/assets/images/selector/vocaltuner.png
