tomassasovsky/segno/packages/fx_catalogue/assets/images/stomps/AmbiVerb2.png

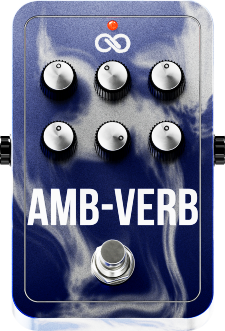
packages/fx_catalogue/assets/images/stomps/AmbiVerb2.png
