tomassasovsky/segno/packages/fx_catalogue/assets/images/stomps/Amp4.png

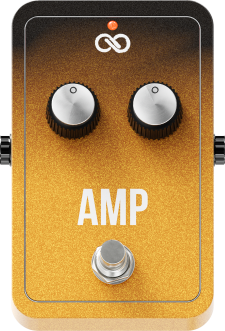
packages/fx_catalogue/assets/images/stomps/Amp4.png
