tomassasovsky/segno/packages/fx_catalogue/assets/images/stomps/Chorus3.png

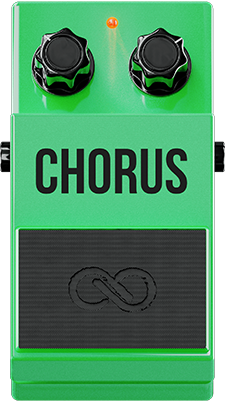
packages/fx_catalogue/assets/images/stomps/Chorus3.png
