tomassasovsky/segno/packages/fx_catalogue/assets/images/stomps/Compressor2.png

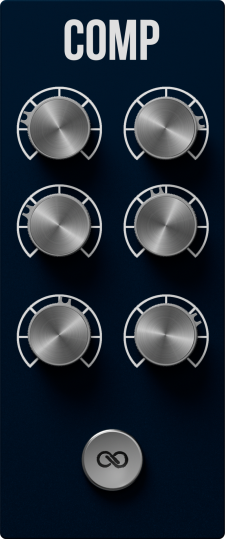
packages/fx_catalogue/assets/images/stomps/Compressor2.png
