tomassasovsky/segno/packages/fx_catalogue/assets/images/stomps/Degrade3.png

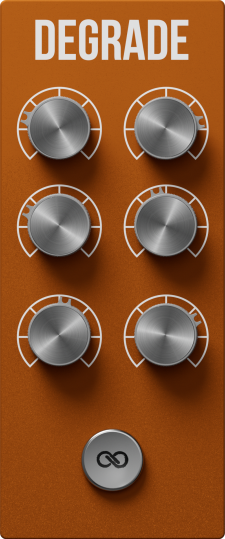
packages/fx_catalogue/assets/images/stomps/Degrade3.png
