tomassasovsky/segno/packages/fx_catalogue/assets/images/stomps/Delay6.png

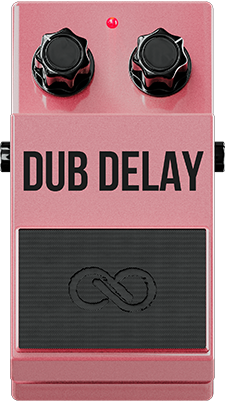
packages/fx_catalogue/assets/images/stomps/Delay6.png
