tomassasovsky/segno/packages/fx_catalogue/assets/images/stomps/Distort1.png

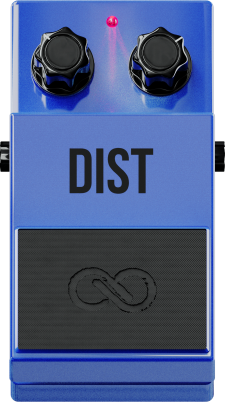
packages/fx_catalogue/assets/images/stomps/Distort1.png
