tomassasovsky/segno/packages/fx_catalogue/assets/images/stomps/Distort2.png

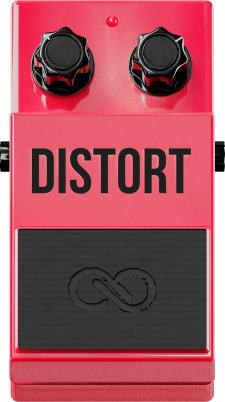
packages/fx_catalogue/assets/images/stomps/Distort2.png
