tomassasovsky/segno/packages/fx_catalogue/assets/images/stomps/Doubler1.png

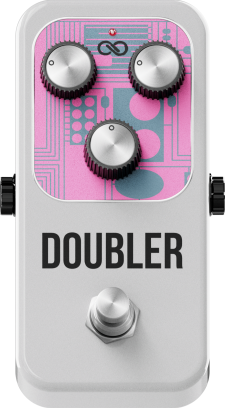
packages/fx_catalogue/assets/images/stomps/Doubler1.png
