tomassasovsky/segno/packages/fx_catalogue/assets/images/stomps/EQ4.png

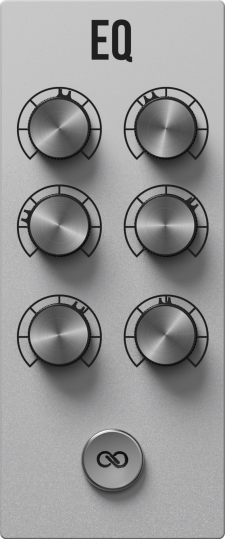
packages/fx_catalogue/assets/images/stomps/EQ4.png
