tomassasovsky/segno/packages/fx_catalogue/assets/images/stomps/EQ5.png

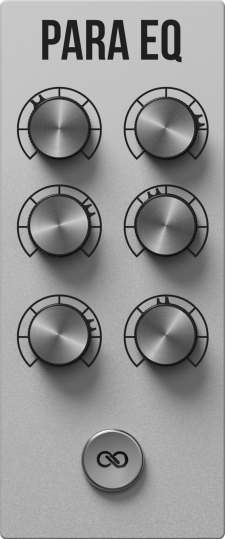
packages/fx_catalogue/assets/images/stomps/EQ5.png
