tomassasovsky/segno/packages/fx_catalogue/assets/images/stomps/Harmonise20.png

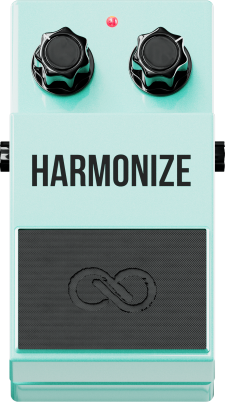
packages/fx_catalogue/assets/images/stomps/Harmonise20.png
