tomassasovsky/segno/packages/fx_catalogue/assets/images/stomps/HPFGate2.png

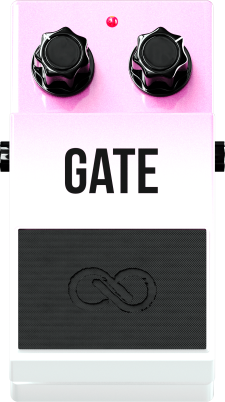
packages/fx_catalogue/assets/images/stomps/HPFGate2.png
