tomassasovsky/segno/packages/fx_catalogue/assets/images/stomps/LPF2.png

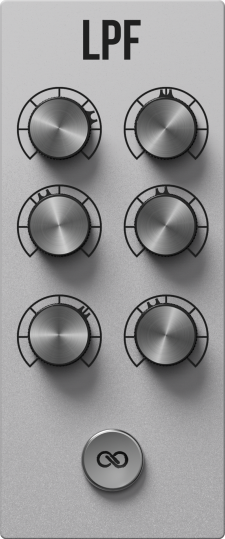
packages/fx_catalogue/assets/images/stomps/LPF2.png
