tomassasovsky/segno/packages/fx_catalogue/assets/images/stomps/Mod3.png

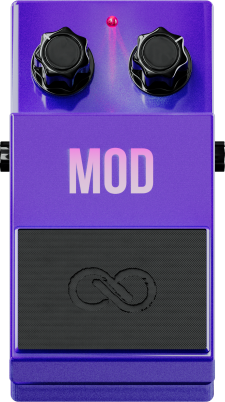
packages/fx_catalogue/assets/images/stomps/Mod3.png
