tomassasovsky/segno/packages/fx_catalogue/assets/images/stomps/Octaver3.png

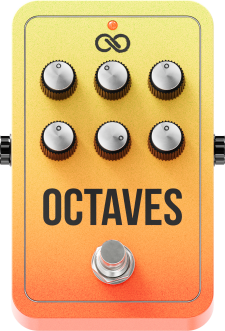
packages/fx_catalogue/assets/images/stomps/Octaver3.png
