tomassasovsky/segno/packages/fx_catalogue/assets/images/stomps/Overdrive2.png

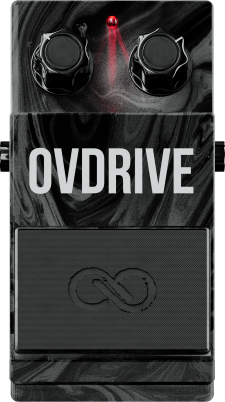
packages/fx_catalogue/assets/images/stomps/Overdrive2.png
