tomassasovsky/segno/packages/fx_catalogue/assets/images/stomps/PitchShift2.png

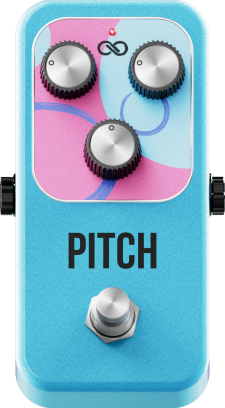
packages/fx_catalogue/assets/images/stomps/PitchShift2.png
