tomassasovsky/segno/packages/fx_catalogue/assets/images/stomps/Pumper2.png

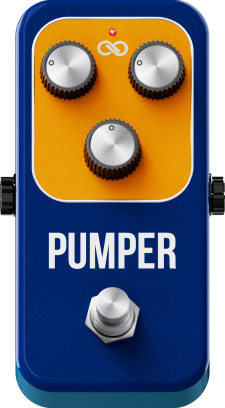
packages/fx_catalogue/assets/images/stomps/Pumper2.png
