tomassasovsky/segno/packages/fx_catalogue/assets/images/stomps/Reverb2.png

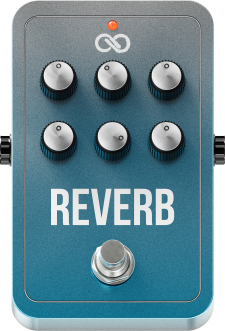
packages/fx_catalogue/assets/images/stomps/Reverb2.png
