tomassasovsky/segno/packages/fx_catalogue/assets/images/stomps/Slicer2.png

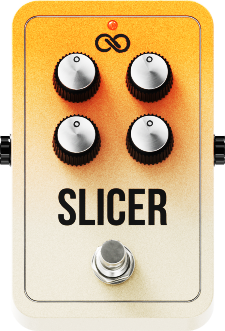
packages/fx_catalogue/assets/images/stomps/Slicer2.png
