tomassasovsky/segno/packages/fx_catalogue/assets/images/stomps/SpringRev2.png

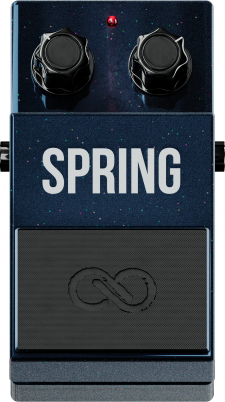
packages/fx_catalogue/assets/images/stomps/SpringRev2.png
