tomassasovsky/segno/packages/fx_catalogue/assets/images/stomps/Transient3.png

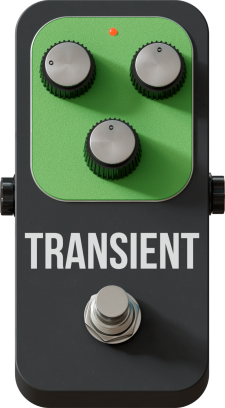
packages/fx_catalogue/assets/images/stomps/Transient3.png
