tomassasovsky/segno/packages/fx_catalogue/assets/images/stomps/Vinyl4.png

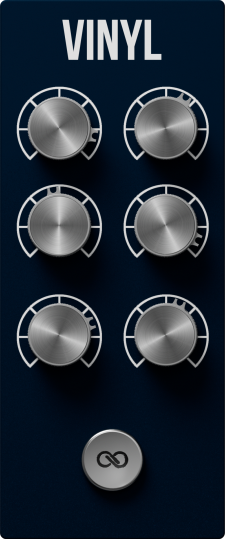
packages/fx_catalogue/assets/images/stomps/Vinyl4.png
