tomassasovsky/segno/packages/fx_catalogue/assets/images/stomps/Wah1.png

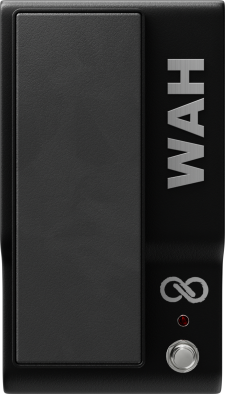
packages/fx_catalogue/assets/images/stomps/Wah1.png
