tomassasovsky/segno/packages/fx_catalogue/assets/images/stomps/Wham2.png

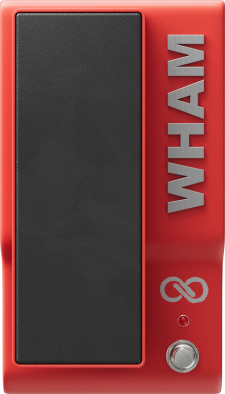
packages/fx_catalogue/assets/images/stomps/Wham2.png
