tomassasovsky/segno/packages/fx_catalogue/assets/images/strip/drum.png

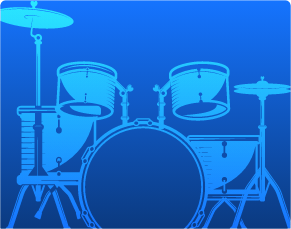
packages/fx_catalogue/assets/images/strip/drum.png
