tomassasovsky/segno/packages/fx_catalogue/assets/images/strip/dub.png

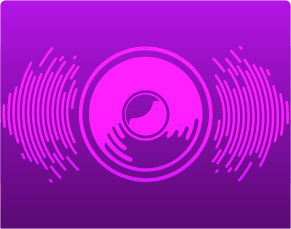
packages/fx_catalogue/assets/images/strip/dub.png
