tomassasovsky/segno/packages/fx_catalogue/assets/images/strip/edsguitar.png

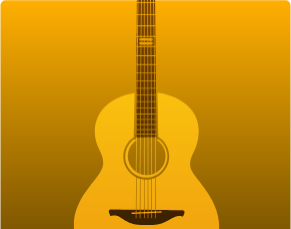
packages/fx_catalogue/assets/images/strip/edsguitar.png
