tomassasovsky/segno/packages/fx_catalogue/assets/images/strip/guitar.png

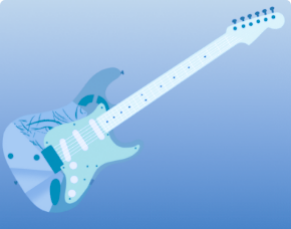
packages/fx_catalogue/assets/images/strip/guitar.png
