tomassasovsky/segno/packages/fx_catalogue/assets/images/strip/lo-fi.png

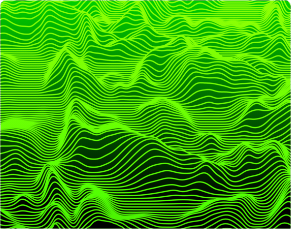
packages/fx_catalogue/assets/images/strip/lo-fi.png
