tomassasovsky/segno/packages/fx_catalogue/assets/images/strip/rhythmic.png

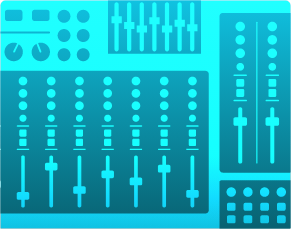
packages/fx_catalogue/assets/images/strip/rhythmic.png
