tomassasovsky/segno/packages/fx_catalogue/assets/images/strip/studio.png

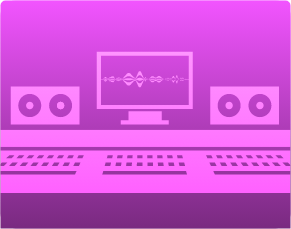
packages/fx_catalogue/assets/images/strip/studio.png
