tomassasovsky/segno/packages/fx_catalogue/assets/images/strip/vocal.png

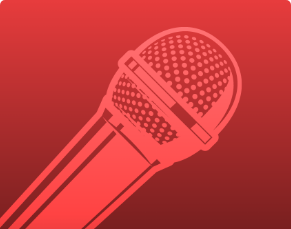
packages/fx_catalogue/assets/images/strip/vocal.png
