tomassasovsky/segno/test/screenshots/goldens/storage_overview.png

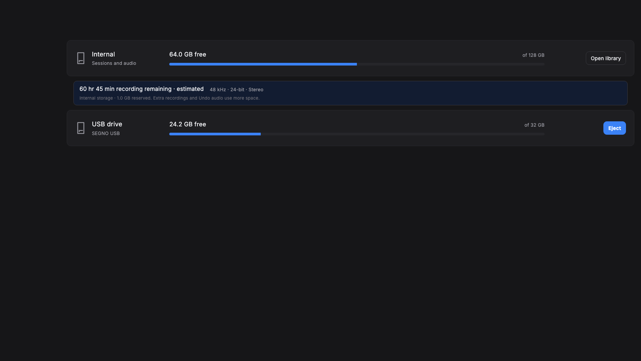
test/screenshots/goldens/storage_overview.png
