tomassasovsky/segno/hardware/enclosure/out/segno_pedal_tile_TRACK2.step

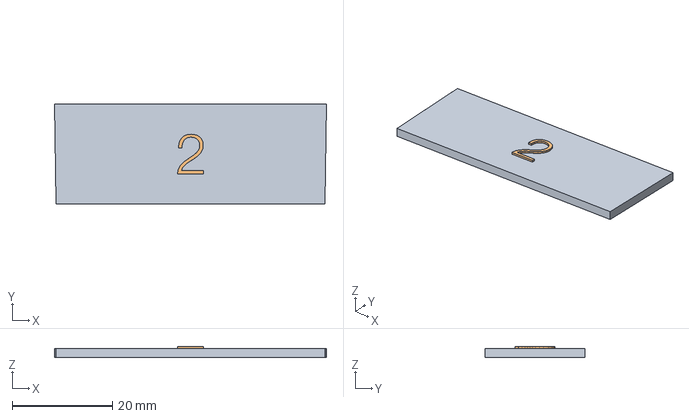
[picture p88: CAD file, 2026-09-04]
hardware/enclosure/out/segno_pedal_tile_TRACK2.step
54.4 x 19.9 x 2.20 mm
