tomassasovsky/segno/hardware/enclosure/out/segno_pedal_tile_CLEAR.step

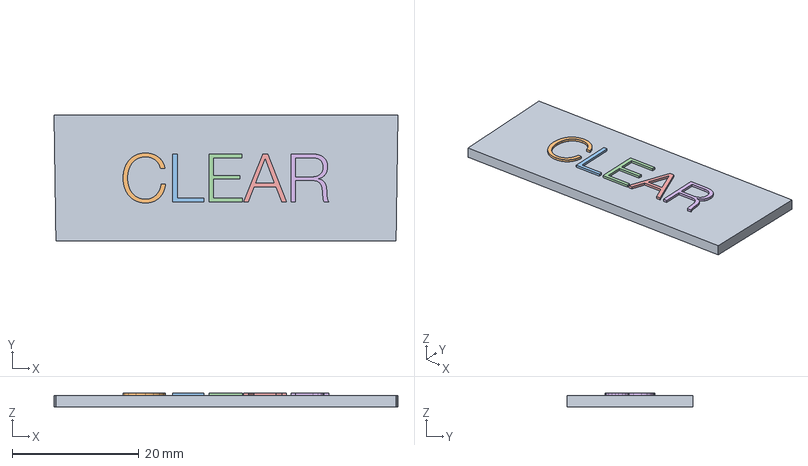
[picture p89: CAD file, 2026-09-04]
hardware/enclosure/out/segno_pedal_tile_CLEAR.step
54.4 x 19.9 x 2.20 mm
