tomassasovsky/segno/hardware/enclosure/out/segno_mini_console_tray.step

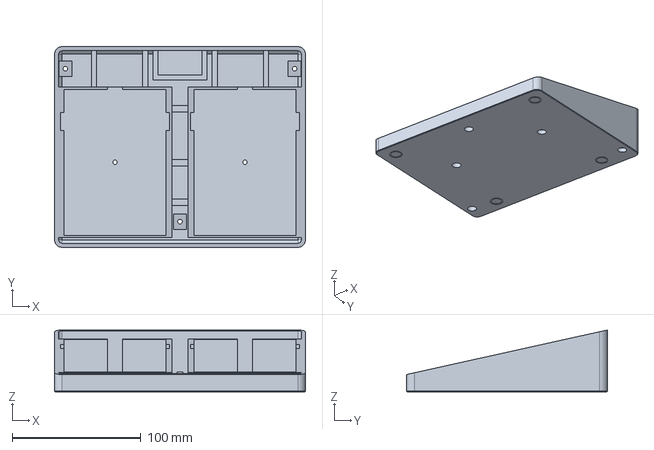
[picture p90: CAD file, 2026-09-04]
hardware/enclosure/out/segno_mini_console_tray.step
195.3 x 156.2 x 48.2 mm
