tomassasovsky/segno/hardware/enclosure/out/segno_screen16_stand_L.step

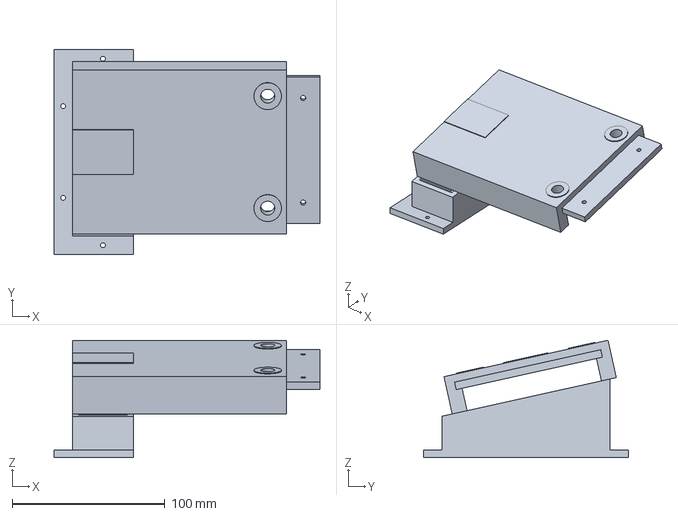
[picture p91: CAD file, 2026-09-04]
hardware/enclosure/out/segno_screen16_stand_L.step
174.0 x 134.0 x 76.8 mm
