tomassasovsky/segno/hardware/enclosure/out/segno_ring_diffuser.step

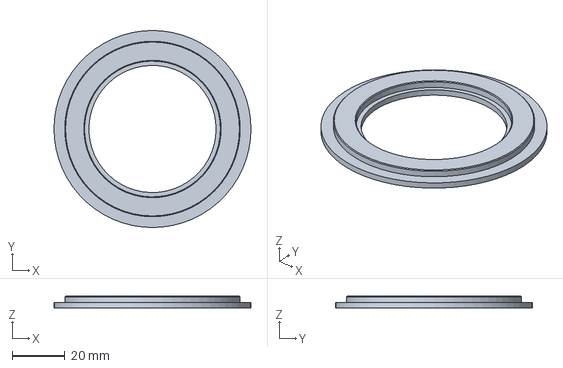
[picture p92: CAD file, 2026-09-04]
hardware/enclosure/out/segno_ring_diffuser.step
75.0 x 75.0 x 4.40 mm
