tomassasovsky/segno/hardware/enclosure/out/segno_mini_console_lid.step

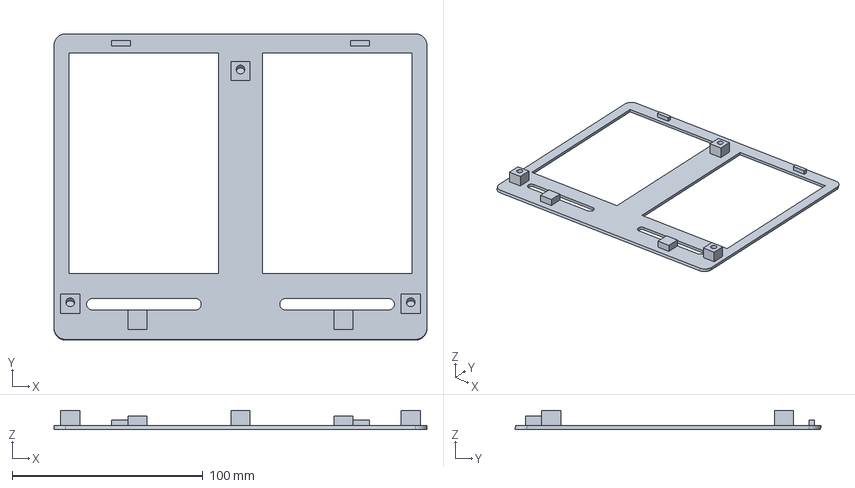
[picture p93: CAD file, 2026-09-04]
hardware/enclosure/out/segno_mini_console_lid.step
195.3 x 160.4 x 10.0 mm
