tomassasovsky/segno/hardware/enclosure/out/segno_pedal_tile_TRACK1.step

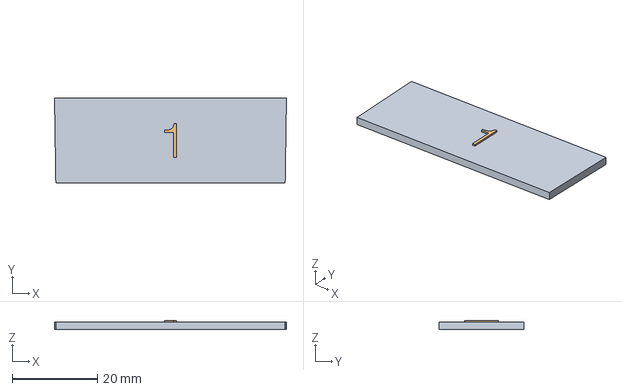
[picture p94: CAD file, 2026-09-04]
hardware/enclosure/out/segno_pedal_tile_TRACK1.step
54.4 x 19.9 x 2.20 mm
