tomassasovsky/segno/hardware/enclosure/out/segno_post.step

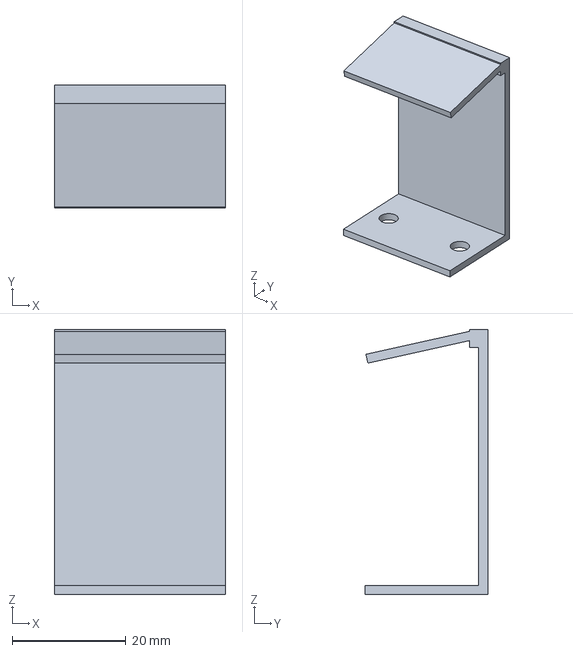
[picture p95: CAD file, 2026-09-04]
hardware/enclosure/out/segno_post.step
30.1 x 21.6 x 46.7 mm
