tomassasovsky/segno/hardware/enclosure/out/segno_ring_disc.step

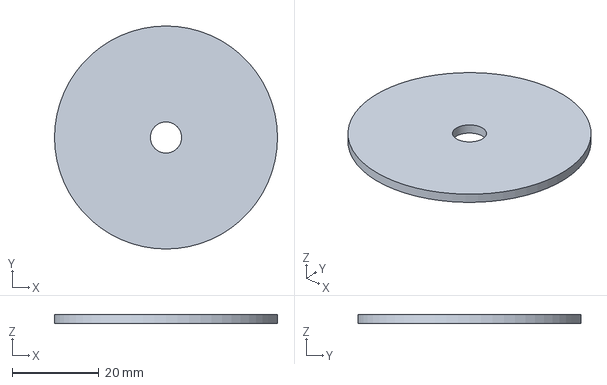
[picture p96: CAD file, 2026-09-04]
hardware/enclosure/out/segno_ring_disc.step
51.5 x 51.5 x 2.00 mm
