tomassasovsky/segno/hardware/enclosure/out/segno_encoder_knob.step

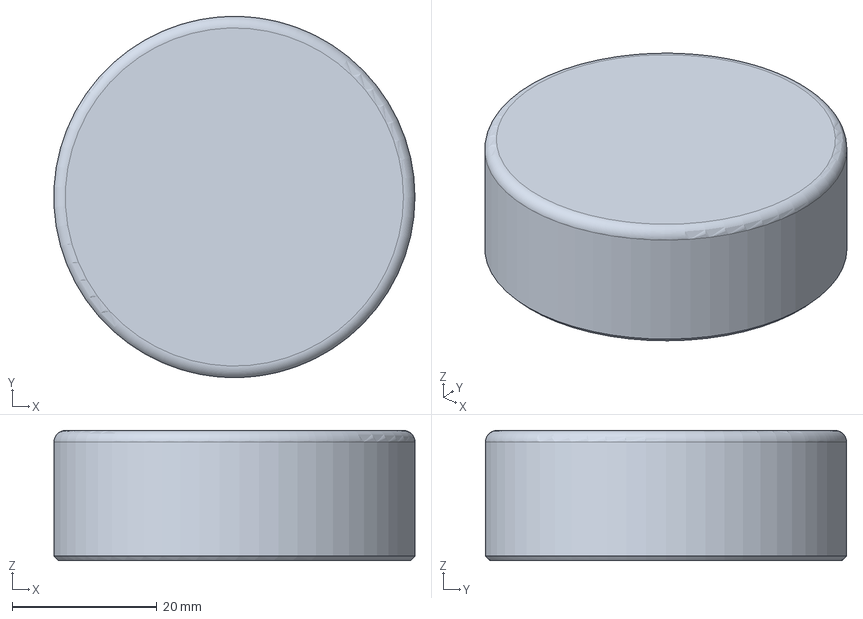
[picture p97: CAD file, 2026-09-04]
hardware/enclosure/out/segno_encoder_knob.step
50.0 x 50.0 x 18.0 mm
