tomassasovsky/segno/hardware/enclosure/out/segno_screen16_stand_R.step

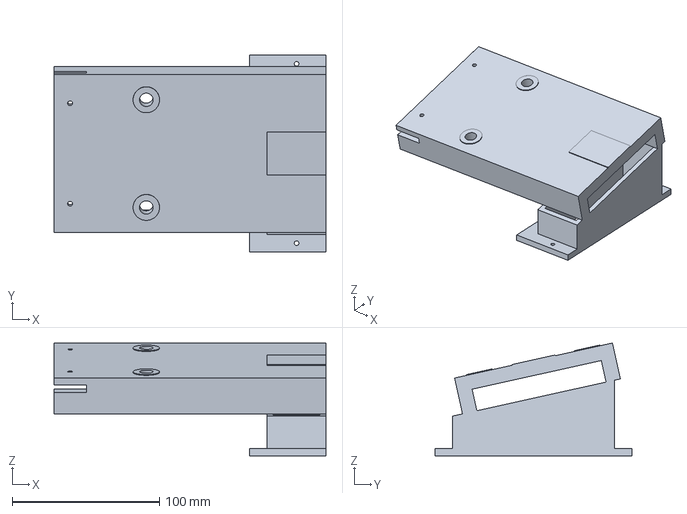
[picture p98: CAD file, 2026-09-04]
hardware/enclosure/out/segno_screen16_stand_R.step
185.0 x 134.0 x 76.8 mm
