tomassasovsky/segno/hardware/enclosure/out/segno_screen7_tower.step

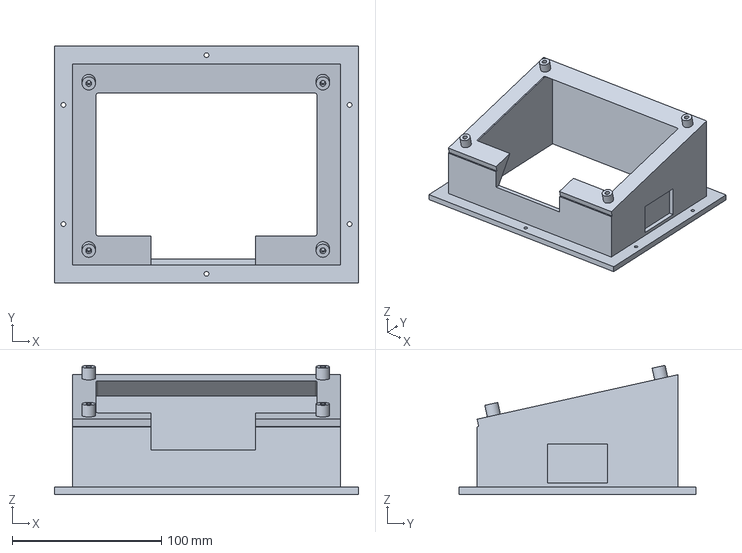
[picture p99: CAD file, 2026-09-04]
hardware/enclosure/out/segno_screen7_tower.step
204.0 x 158.7 x 86.8 mm
