tomassasovsky/segno/hardware/enclosure/out/segno_mini_console_sled.step

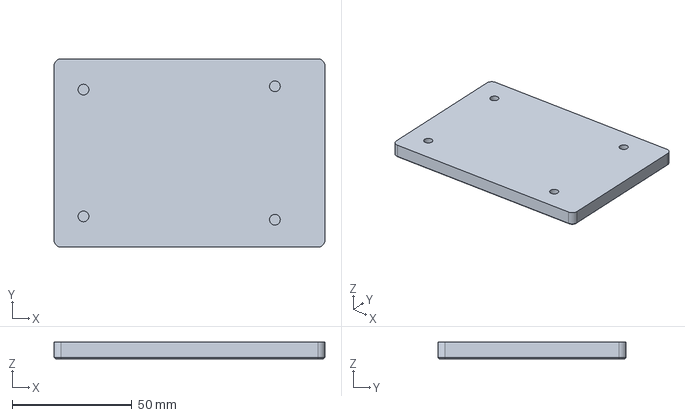
[picture p100: CAD file, 2026-09-04]
hardware/enclosure/out/segno_mini_console_sled.step
113.3 x 78.8 x 7.00 mm
