tomassasovsky/segno/hardware/enclosure/out/segno_led_diffuser.step

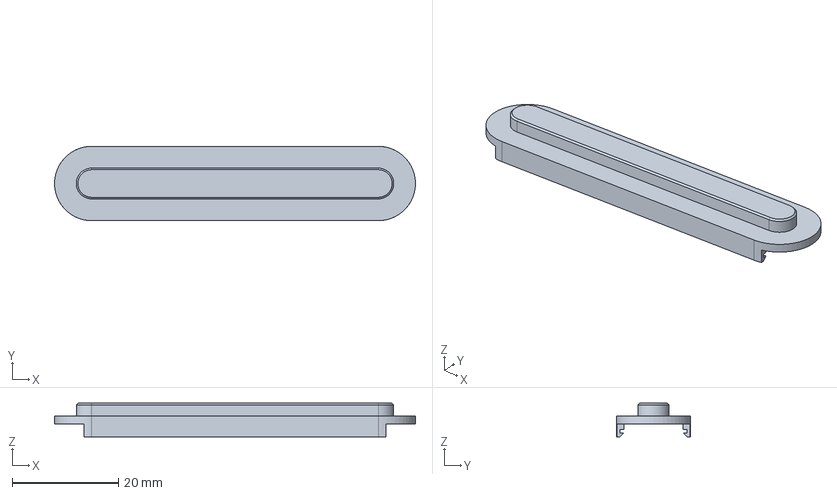
[picture p101: CAD file, 2026-09-04]
hardware/enclosure/out/segno_led_diffuser.step
68.0 x 14.0 x 6.33 mm
