tomassasovsky/segno/hardware/enclosure/out/segno_platform_mid_ring.step

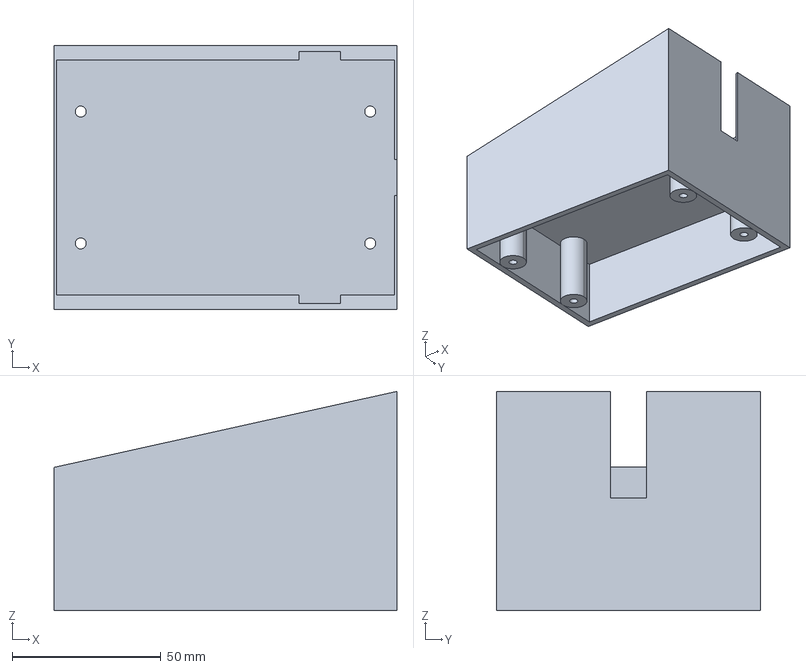
[picture p102: CAD file, 2026-09-04]
hardware/enclosure/out/segno_platform_mid_ring.step
115.4 x 88.8 x 73.7 mm
