tomassasovsky/segno/hardware/enclosure/out/segno_platform_sled.step

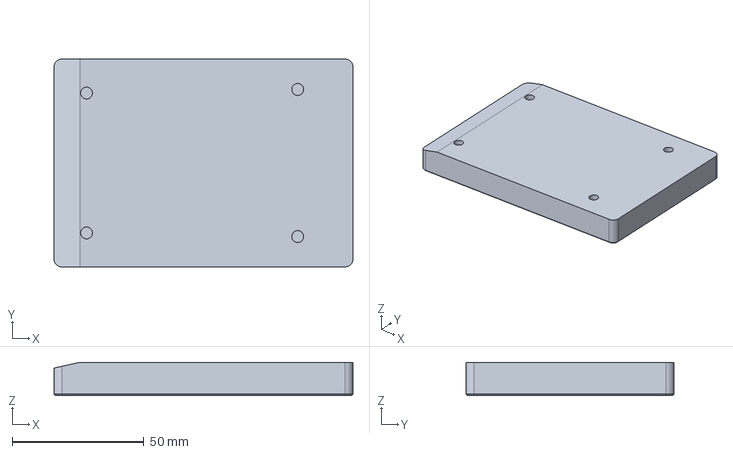
[picture p103: CAD file, 2026-09-04]
hardware/enclosure/out/segno_platform_sled.step
113.3 x 78.8 x 12.6 mm
