tomassasovsky/segno/hardware/enclosure/out/segno_platform_front_ring.step

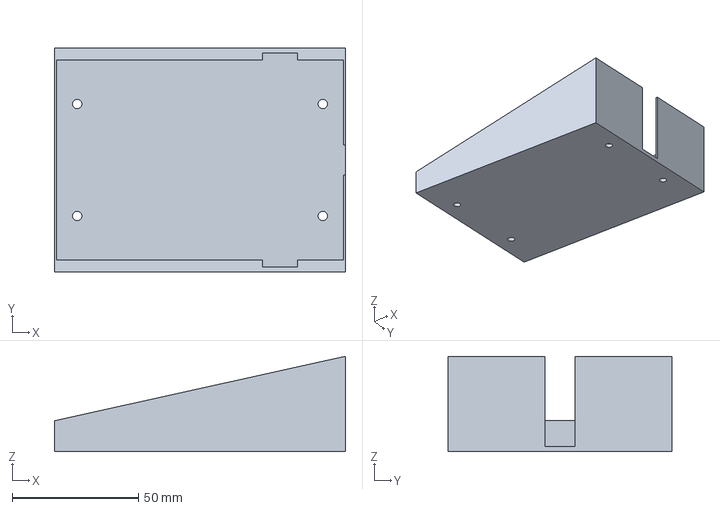
[picture p104: CAD file, 2026-09-04]
hardware/enclosure/out/segno_platform_front_ring.step
115.4 x 88.8 x 37.9 mm
