tomassasovsky/segno/hardware/enclosure/out/segno_faceplate.step

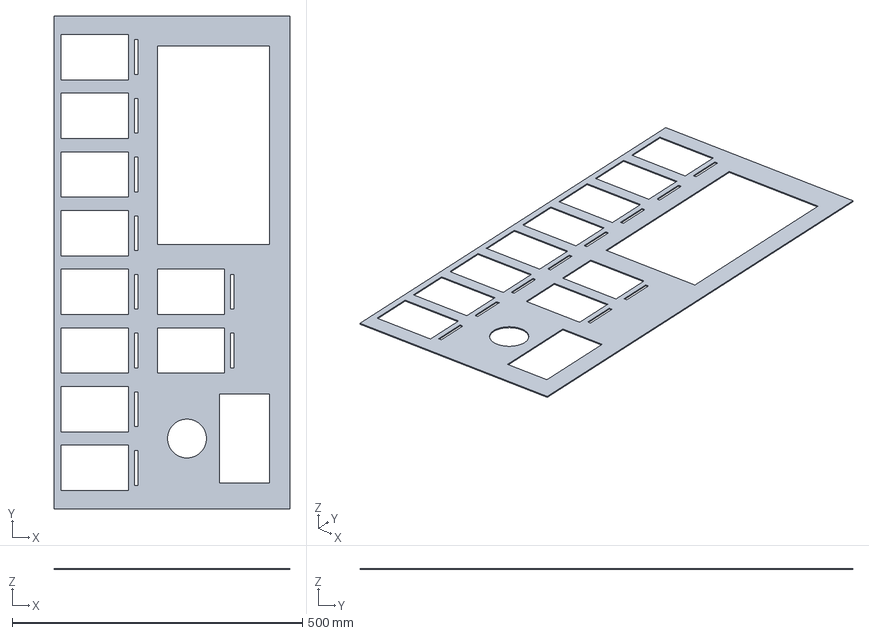
[picture p105: CAD file, 2026-09-04]
hardware/enclosure/out/segno_faceplate.step
406.6 x 849.8 x 2.00 mm
