tomassasovsky/segno/hardware/enclosure/out/segno_pedal_base_gauge.dxf

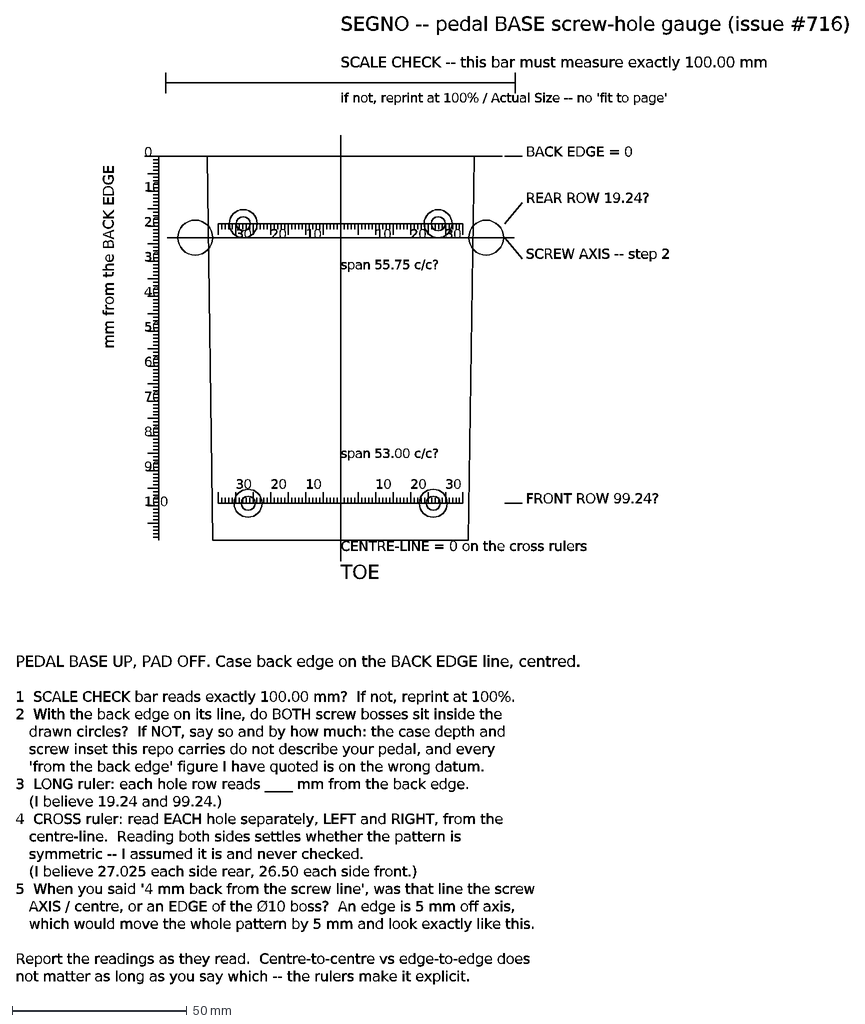
[picture p106: CAD file, 2026-08-18]
hardware/enclosure/out/segno_pedal_base_gauge.dxf
SEGNO -- pedal BASE screw-hole gauge (issue #716)
SCALE CHECK -- this bar must measure exactly 100.00 mm
if not, reprint at 100% / Actual Size -- no 'fit to page'
BACK EDGE = 0
CENTRE-LINE = 0 on the cross rulers
TOE
SCREW AXIS -- step 2
0
10
20
30
40
50
60
70
80
90
100
mm from the BACK EDGE
REAR ROW 19.24?
span 55.75 c/c?
FRONT ROW 99.24?
span 53.00 c/c?
PEDAL BASE UP, PAD OFF. Case back edge on the BACK EDGE line, centred.
1 SCALE CHECK bar reads exactly 100.00 mm? If not, reprint at 100%.
2 With the back edge on its line, do BOTH screw bosses sit inside the
drawn circles? If NOT, say so and by how much: the case depth and
screw inset this repo carries do not describe your pedal, and every
'from the back edge' figure I have quoted is on the wrong datum.
3 LONG ruler: each hole row reads ____ mm from the back edge.
(I believe 19.24 and 99.24.)
4 CROSS ruler: read EACH hole separately, LEFT and RIGHT, from the
centre-line. Reading both sides settles whether the pattern is
symmetric -- I assumed it is and never checked.
(I believe 27.025 each side rear, 26.50 each side front.)
5 When you said '4 mm back from the screw line', was that line the screw
AXIS / centre, or an EDGE of the Ø10 boss? An edge is 5 mm off axis,
which would move the whole pattern by 5 mm and look exactly like this.
Report the readings as they read. Centre-to-centre vs edge-to-edge does
not matter as long as you say which -- the rulers make it explicit.
