tomassasovsky/segno/hardware/enclosure/out/segno_pedal_base_fit_test.step

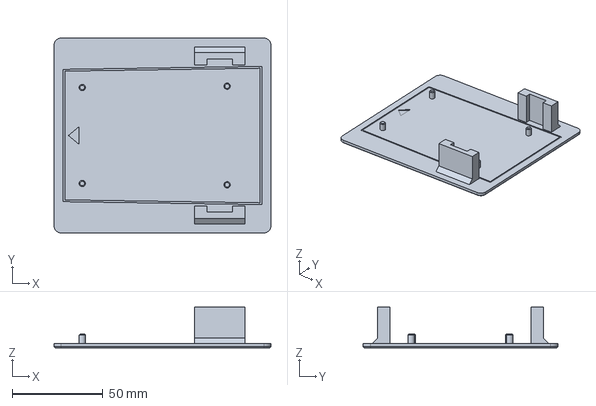
[picture p107: CAD file, 2026-08-18]
hardware/enclosure/out/segno_pedal_base_fit_test.step
119.9 x 107.7 x 22.4 mm
