tomassasovsky/segno/test/screenshots/goldens/audio_routing_input_setup.png

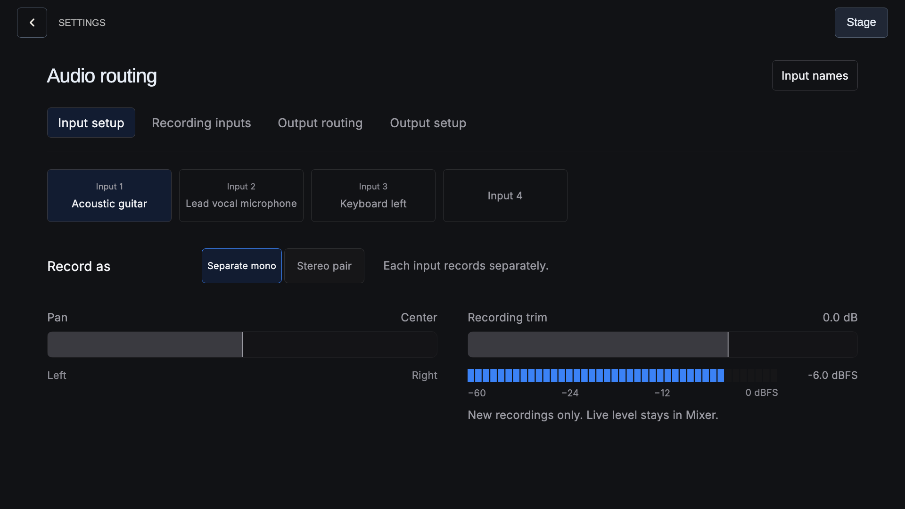
test/screenshots/goldens/audio_routing_input_setup.png
