tomassasovsky/segno/test/screenshots/goldens/audio_routing_output_setup.png

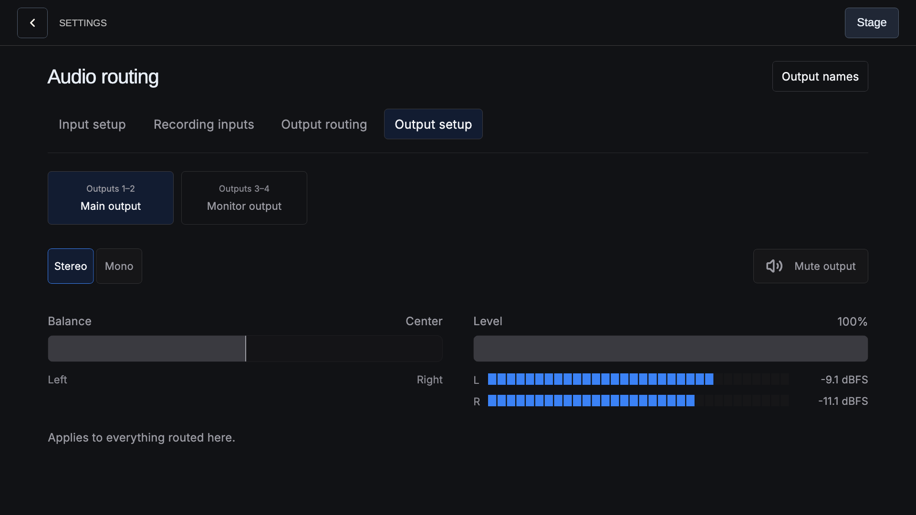
test/screenshots/goldens/audio_routing_output_setup.png
