tomassasovsky/segno/test/screenshots/goldens/pedal_setup_clear.png

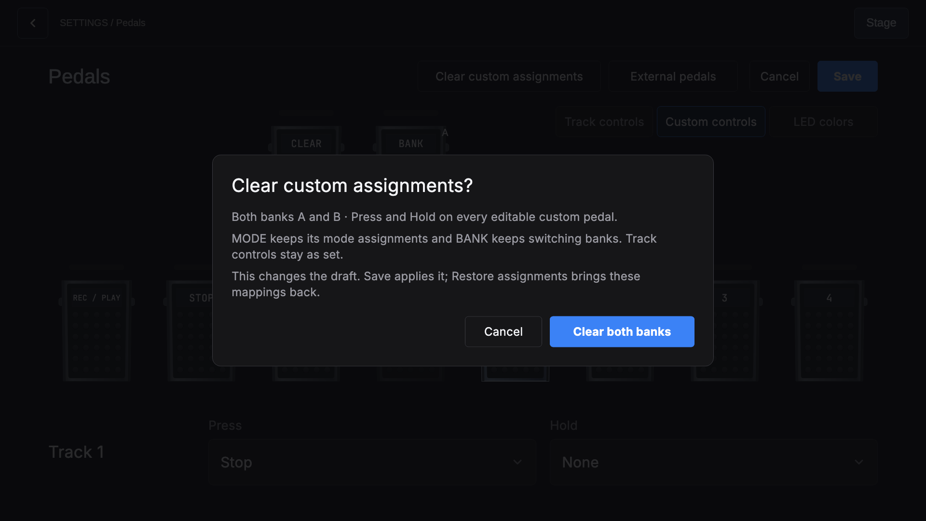
test/screenshots/goldens/pedal_setup_clear.png
