tomassasovsky/segno/test/screenshots/goldens/pedal_setup_color_editor.png

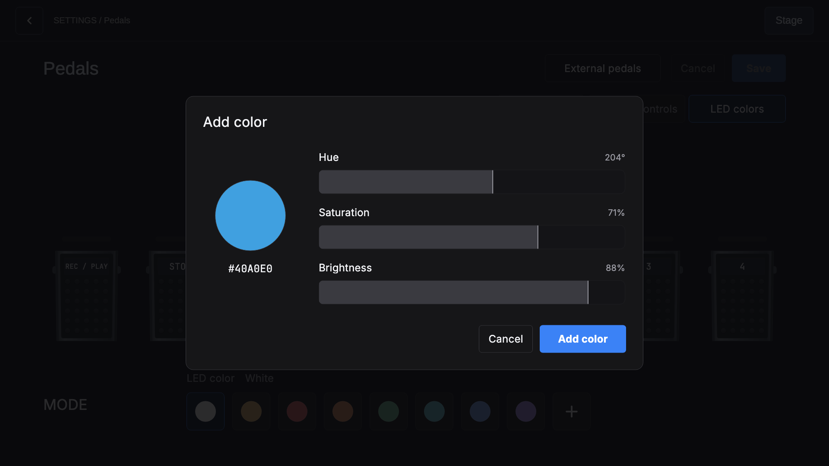
test/screenshots/goldens/pedal_setup_color_editor.png
