tomassasovsky/segno/test/screenshots/goldens/pedal_setup_custom_bank_b.png

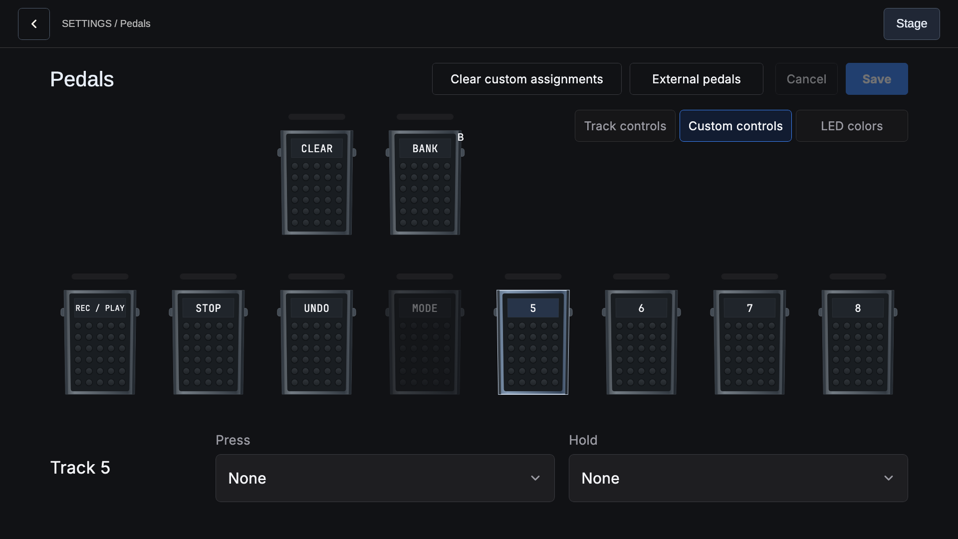
test/screenshots/goldens/pedal_setup_custom_bank_b.png
