tomassasovsky/segno/test/screenshots/goldens/pedal_setup_leds.png

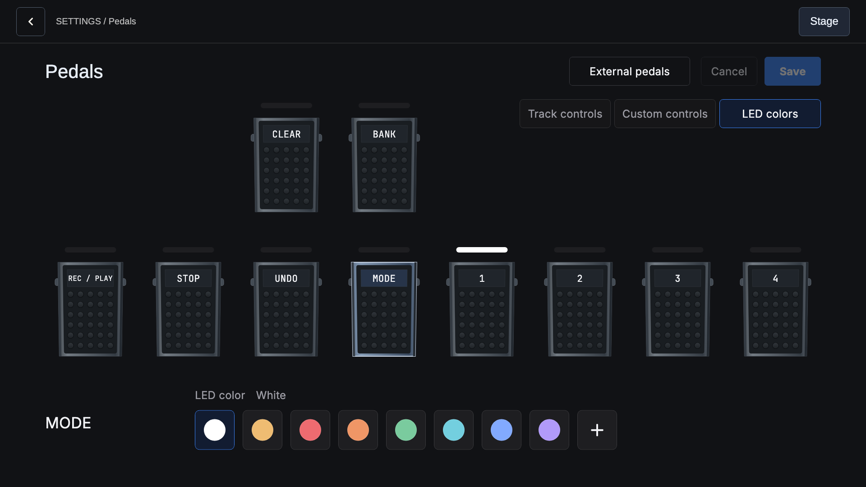
test/screenshots/goldens/pedal_setup_leds.png
