tomassasovsky/segno/test/screenshots/goldens/pedal_setup_picker.png

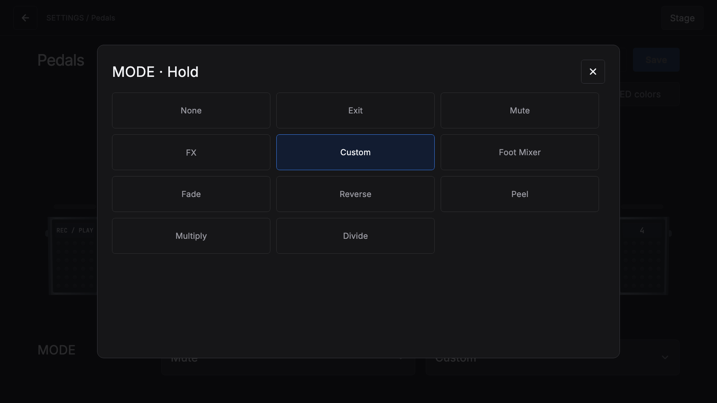
test/screenshots/goldens/pedal_setup_picker.png
