tomassasovsky/segno/test/screenshots/goldens/pedal_setup_tracks.png

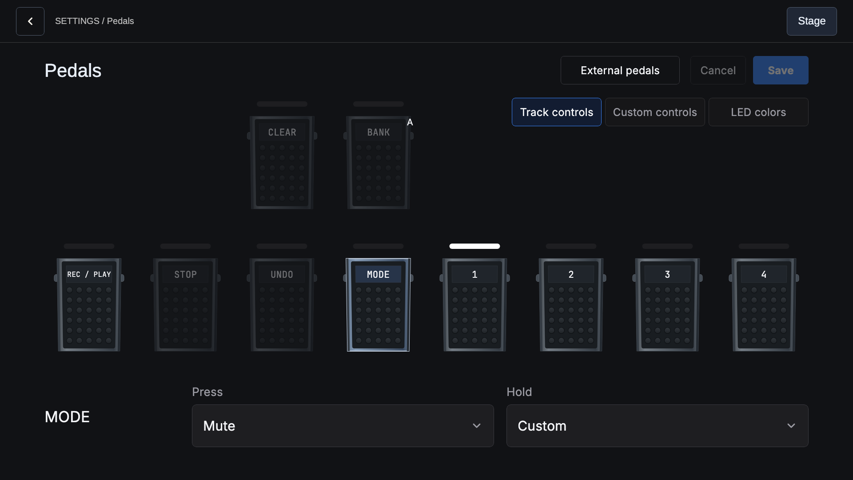
test/screenshots/goldens/pedal_setup_tracks.png
