tomassasovsky/segno/test/screenshots/goldens/pedal_setup_tracks_group.png

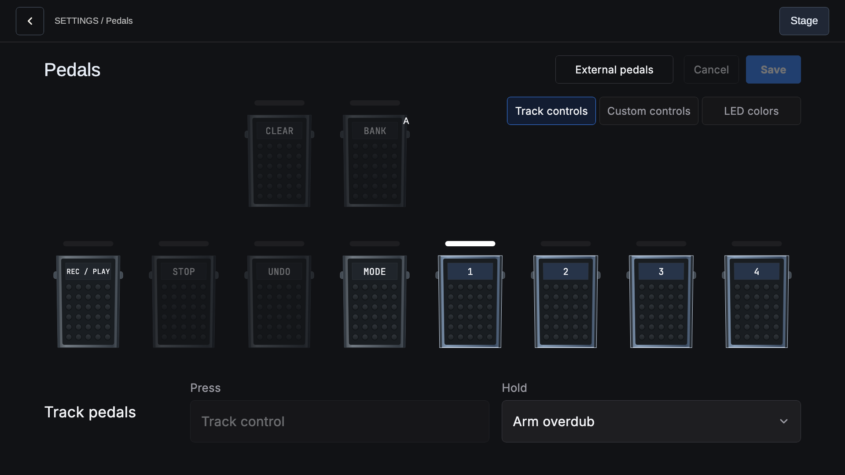
test/screenshots/goldens/pedal_setup_tracks_group.png
