tomassasovsky/segno/docs/reviews/design-midi-controls-restack/test-quality-review.md

# MIDI test-quality review

Base and current Git HEAD: `1ef7fb30abd328b86ac481ec71e72c9bbc59e83c`. This is a working-tree review; a later commit requires the coordinator to bind the resulting commit to these reviewed bytes. Exact intended-path hashes and scope are in [the source review](source-review.md#reviewed-file-binding).

One independent source reviewer performed the VGV, architecture, test-quality, simplicity and readiness roles sequentially. These are five review lenses, not five independent reviewers. No delegation, product edits, test execution or UI automation was performed by this reviewer. The coordinator and separate adversarial reviewer supplied execution evidence.

The local source and quality gate is **clean** for the exact 134-path manifest fingerprint `3cb49b9c0e522f35d7275b5b58a6a30095a4f8350c161796bb48f3806c2be705`. All eleven functional findings and the final future annotation are resolved; no actionable finding remains. Final app, package, native and static evidence passes. Published-head CI and final commit binding remain separate, pending gates. No ready-to-merge, merge or deployment claim is made.

## Behavioral coverage

The reviewed tests cover protocol boundaries and reset, immutable mapping validation and overlap, native callback epochs, rapid contact edges, accepted/refused target ownership, queued session/device replacement, delayed native timestamps, audible state after retirement, durable Released projection, shutdown waits, editor ownership and stale pickers, explicit Off recovery, malformed configuration and both Stage routes.

Failure injection uses real repository/store or native-pump boundaries where practical. Projection-only tests supplement the dispatch integration tests rather than proving dispatch themselves. R11 tests hold a real asynchronous confirmation seam, close the Cubit, verify cancellation and verify closure waits for its receipt. Root demonstrated both tests fail on the old code and 17 relevant cases pass after repair.

The final fixture repairs preserve assertions. Missing messages/getters/session stubs represent actual dependencies; the tracks fixture now carries its known sample rate. The app test explicitly removes its widget tree before disposing a borrowed device repository, avoiding a teardown deadlock instead of skipping the test.

## Supplied execution evidence

Nine relevant package suites pass. Reported package coverage is controller 82.53% (floor 82%), MIDI client 96.38%, MIDI device 91.24%, settings 89.58%, looper 95.87% (95%), engine 69.82%, session 95.77% (89%), performance 99.33% (99%) and FX catalogue 100% (100%). A missing configured floor is not invented. Native normal/ASAN/telemetry-off pass. The separate adversary reports 18 passes and a failing required negative control. The final fixture subset reports 306 passes and six explicit skips.

The final app aggregate passes: 2,433 tests, six existing explicit skips, and 90.857% coverage (23,314/25,660 lines; floor 90%) under the repository's configured coverage exclusions. The only source delta after that aggregate was an explicit `unawaited` annotation with unchanged execution; both affected disposal tests passed again and final strict checks passed. The coordinator's final binding confirms unchanged package/native inputs. Native-pump cases explicitly skip without their library; only supplied non-skipped runs support those claims. Author screenshot tests require fonts and remain separate from CI visual proof. No test was executed by this reviewer.
