tomassasovsky/segno/docs/reviews/design-fx-surfaces-restack/raw/test-quality.md

Independent reviewer: m2_fx_native. Base: a52fe34d42a719624762f7756518a7e54cf7fd0c. Bounded scope: changed lib/** and root test/**. This reviewer authored package/native work and expressly excludes all packages, generated FFI and manifests from independent-review credit. Domain/native contracts were read only to trace UI callers. No repository edits, broad test/build runs or screenshot generation were performed in this review phase.

Final source binding: final-v4-hashes.json, SHA256 731cf62a54934b392970384f4c56545bda4c700d1f0d0227560f0ca8f4cf6486. Initial, intermediate and final source snapshots/diffs are retained; all production/test deltas were reconciled. Key hashes: Bloc 24fe22ba, FxCubit eef07fb9, FxPage 9555caad, Monitor 5169080c, Event d073149b. Broad release checks and exact-head CI are root-owned and are not implied by this bounded review.

# Test-quality review

Verdict: no unresolved actionable test-quality finding in the bounded UI/root-test delta.

Reviewed behavioral coverage for destination selection, remembered strips, placement/rack boundaries, channel tuples, capacity, preset save/recall, cancellation and new-instance identity. Regression cases exercise a pedal parameter change while Reorder is open, refusal retaining the editor without success feedback, disabled chain projection, singleton rack persistence, cleared replacement art and storage refusal preserving confirmed state. Add cases assert exact new identity, no opening before receipt, refusal, late receipt under a newer route, old engine life and live-input opening. The capacity regression asserts false and no repository setter call when the current chain is already full.

Mocked Bloc event receipts prove the widget contract only. Independent actual-pump probes supply admission/acknowledgment evidence separately: six existing lifecycle groups and six append groups passed, including a fixed pre-repair failing oracle and stale-monitor projection preservation. No fixture correction weakened the capacity expectation. This review does not count authored package tests as independent evidence.

The settings_tray UART change replaces the removed transport constructor with NoopPedalLink and drops obsolete keepAliveInterval; all assertions are preserved. Its standalone log records 43 passing. fx-add-capacity-final-focused.log records 244 passing; this is inspected builder evidence at the pre-lifetime-predicate freeze, with the final lifetime amendment covered by a further 190 passing focused tests. Root reports full-app 2229 pass, six existing skips and 91.07% coverage before that amendment. Exact final focused/static evidence is bound by root and passes; no full-app rerun on final bytes is invented.

Final reconciliation: root confirmed the source freeze. All bounded production/test deltas, including the new stale-at-library-open regression, were reread and final-v4-hashes.json matches current files. Root reports the live Mac journey now opens newly added single/rack editors directly and Stage returns to Mixer with the tray closed. That is root journey evidence; an earlier pre-hot-reload 91px RenderFlex warning remains separately recorded, so this report does not claim universal viewport validation. Final static evidence is complete: explicit 649-file format check, strict analyzer, actual 649-file Bloc lint and whitespace checks all pass, with no source drift. The final focused run passed 190 tests. Root's explicit full-app reuse amendment preserves the earlier 2,229 passes, six existing skips and 91.07% coverage; no rerun of that entire suite on final bytes is claimed.
