tomassasovsky/segno/docs/reviews/design-edits-restack/validation.md

# Reversible edits reconstruction: final validation

Date: 2026-09-15. Reviewed base: `09c8e9c2` (Tracks/UART reconstruction).
Incoming original slice parent: `6cdfb9fb`. Issue: #1060, part of #1012.

The accepted recovery refusal, grouped recovery and final sibling-cancellation
repair are included in every aggregate result below. Earlier checkpoint
counts in the raw reports are historical, not the final validation result.

## Observed checks

- Full app: **2,255 passed**, six existing skipped legacy toast/banner tests
  tracked separately in #453.
- All 20 package suites: **1,610 passed** using the final rebuilt native
  library. Looper repository: 460; engine package: 282. No native-dependent
  package tests were counted as passing while skipped.
- Normal native engine, MIDI and host tests: all five suites passed.
  Address-sanitizer and telemetry-disabled runs: all five suites passed.
  Thread-sanitizer race suite passed. Each run used an isolated temporary
  directory. The runner's C sanitizer flags do not cover plugin C++ tests.
- All 150 generated lookup symbols exist in the full host library. Symbol
  checker self-tests and the non-Clang C++ atomics-shim compilation passed.
  Bindings were regenerated and explicitly formatted.
- Fatal Dart analysis: no issues. Bloc lint: 599 files, zero issues. Format:
  598 files, zero changes. Test-generated analyzer exclusions were removed
  before these final checks. Markdown spelling and diff whitespace passed.
- Independent public C and Dart regressions cover incompatible retained
  audio, pending clock/cancellation, group ordering, unchanged refusal and
  exact audio recovery after explicit Free selection.

## Coverage

Existing workflow exclusions and floors were preserved.

| Suite | Covered / measured lines | Coverage | Required |
| --- | --- | --- | --- |
| root | 15823 / 16895 | 93.65% | 90% |
| looper repository | 2097 / 2142 | 97.90% | 95% |
| session repository | 491 / 546 | 89.93% | 89% |
| performance repository | 450 / 450 | 100.00% | 99% |
| pedal repository | 512 / 524 | 97.71% | 96% |
| controller repository | 286 / 317 | 90.22% | 82% |
| daw export | 421 / 421 | 100.00% | 100% |

## Review and boundaries

All five review roles are complete with no unresolved actionable findings.
Test quality and PR readiness share a reviewer; that reviewer's authored
bridge was independently checked by the simplicity reviewer. Native changes
were independently reviewed by reviewers other than their author. Repository
and UI changes received independent review. Final aggregate validation and
temporary-file cleanup close the coordinator-owned gates in the raw reports.

No device deployment, firmware flashing, physical pedal timing test or
interface-level recording measurement was performed. This stacked PR has no
full remote CI run until its base permits the repository workflow. Local
validation and a clean review do not grant merge authority or replace CI.
