tomassasovsky/segno/docs/reviews/shared-record-timing/raw/test-quality-f1-f4-delta-v1.md

# Test-quality delta review — F1–F4 and final App retry

Sequential read-only perspective by the same reviewer as the VGV/architecture/simplicity delta reports. Base `8749688c51912f808c3f36d4eb5bca665ede3ade`; runtime freeze fingerprint `f2af6a80afaaa6b13c8b0e63881d3da8c23ad121db7b686f4cb3ee1c66eeca2d`, supplemental F2 native-test freeze and separate App/test hashes `b5b3f55449a0263109823971811559f5f367210b8f65fbb0947da0a5de04d131` / `0d0860b325f8180abfd2eda1f196a7220e7a8c6e6657d190d199fef2d2edf977` were checked on disk. Full private binding: `quality-f1-f4-delta-binding-v1.json`. This reviewer ran no test or build process.

**No new actionable test-quality finding in this delta.** The previous report's inert-image regression is closed: `test_engine_core.c:32027–32086` now supplies a nonempty Drive lane recipe, proves an allowed acquisition actually prepares/adopts it (`pending_fx_edits`, recording state and changed FX fingerprint), then proves an ineligible acquisition leaves preparation count, plugin edits, posted commands, shadows, arm and fingerprint unchanged. The author's focused native log reports PASS. The independent native matrix had already exercised a real recipe and mutant; this new test makes the behavior durable in source/CI.

F1's literal compensated-refusal test (`record_timing_cubit_test.dart:223–244`) first failed on the old owner, then passes with the edit result still rejected, exact empty checkpoint, confirmed owner readiness, clean flush and retained failure signal. F3's MIDI/External cases in `record_timing_dispatch_test.dart:330–410` had two expected red failures and then verify owed live value, durable Released value, no stop, and explicit retry settlement. The Click neighbor `click_dispatch_test.dart:506–540` asserts the exact `ControlCleanupPending` type for both input families. Root's real App cases (`app_test.dart:1230–1342`) exercise the actual provider graph and Power Off dialog: refused held release before or during shutdown keeps power on with durable Released value, hides the competing toast, leaves Retry hit-testable, then accepts the lower value before goodbye/halt. The existing Keep playing case asserts the unresolved recovery banner returns on idle. The coordinator's v8 JSONL reports `done.success=true`; this reviewer did not rerun it.

F4's repository regression (`record_timing_receipt_test.dart:41–75`) failed before the early guard because `pluginStateGet`/`preparePlugin`/record were called, then proves all are absent while timing is unsettled and present on an allowed fresh acquisition after settlement. The native F2 test supplies the lower-level real-recipe counterpart, so the repository call-list assertion is not being used alone as audible/native proof. F1/F3/F4 focused green logs and scoped static results are reported in the v3 manifest; they do not replace the final full suites after those deltas.

The final App test covers both prior-to-shutdown and during-shutdown refused releases, and the existing Keep playing recovery-banner assertion remains intact. `debugAppToastActive` checks the live toast manager and `.hitTestable()` verifies the actual Retry target, rather than only finding its key. Pending external gates: root full App/Looper aggregate, adversary 34-case matrix, final head-bound CI/static/coverage, and native appliance interaction. The model/editor tests authored by this reviewer and unchanged runtime/native areas are outside this delta read set.
