tomassasovsky/segno/docs/reviews/shared-mixer-controls/raw/test-quality-model.md

# Test quality review — model and UI

Review basis: base `06633b2b537efba4c59108e38764e58c0b2c542e` plus the exact 19 file hashes in the original model review source manifest (fingerprint `854620d05942b5d8bd5a971e4095d5a38b882ff6d46e56e3e5537861207da3ff`). One Astra reviewer applied five role definitions sequentially; these are five perspectives, not five independent people. This reviewer authored runtime/coordinator/session changes and does not independently certify them. The reviewed model, resolver, catalogue, labels, endpoint UI and tests were authored by Sol. No tests, product edits, Git changes or delegation were performed during this review.

## Result

No unresolved actionable test-quality finding in scope. Tests exercise strict target identity and malformed coordinates, live availability, excluded pair members, catalogue ordering and view units. Conversion tests include physical literal vectors: silence, half travel approximately 0.04472135955 gain, unity travel approximately 0.90880725226, and maximum gain 2; these prevent an internally consistent but wrong linear-gain reinterpretation. Bipolar boundaries and output level are covered. Existing audible expectations are not weakened to fit the corrected normalized range.

The no-FX enumeration/one-state-read assertion is appropriate for the specific snapshot-cost regression. Most other tests assert observable target lists, normalized reads, labels, drafts and saved mappings rather than source text. No new skips or mock-only production seams were introduced. Raw writer tests were removed together with the unused bypass API.

## Resolved gap and observed evidence

M310-5 was missed by the earlier isolated readout test because its endpoint callback did nothing: Escape could restore local semantics while the real parent draft remained changed. New actual page regressions press Enter/arrow/Escape, verify the parent-provided slider value and then Save. The button restores 0.4 instead of saving 0.41. Expression saves zero after cancellation and separately keeps a later committed 0.01 edit. MIDI also checks confirmed state and Save after cancellation/focus loss.

I inspected `endpoint-cancel-red.log` (prior failure), `endpoint-cancel-green-v1.log` (74 PASS), `model-freeze-v2.log` (30 PASS) and scoped clean analyzer output. Earlier frozen model/UI evidence remains in the preflight records; no reviewer test run was added. These focused results do not substitute for root aggregate coverage, independent runtime probes or published-head CI.

The separately documented live-owner session-load invariant failure reproduces on parent 06633 and is deferred to M5. The runtime author's isolated persisted-value tests are not proof that this preexisting live-owner transition works; no such claim is made here.
