tomassasovsky/segno/docs/reviews/design-pedal-art-restack/test-quality-review.md

# Test quality review

Complete for the six-file art freeze-v1, fingerprint `447437f12e2729a08b35f081f8f77c85e1871f838af4d2581433e7155ec60ed4`. Critical: 0. Important: 0. Suggestions: 0. No unresolved actionable source finding.

One independent reviewer performed the bug-focused review and all five quality roles sequentially. These are five perspectives, not five independent agents. The author and bounded adversarial reviewer are separate. No product edits, tests, builds, Git mutations or recursive delegation were performed by this reviewer.

The author test renders the actual widget into image bytes, samples literal measured interior points for hinges/rolled edges/pad/nameplate, checks all 30 grip locations against pad pixels, and compares selected material/plate output with unchanged rolled-edge colors. Three tests pass in the observed final log. The tests do not merely mirror comments or inspect constants.

This bounded authored suite does not independently establish every quadratic point, arbitrary scaling, repaint stability, hit-target edge, focus route or meaningful mutation sensitivity. Those additional oracle checks belong to the separate adversarial reviewer and parent visual/aggregate packet; no result is presumed. Existing map/page/palette tests are retained and need their normal root gate. The initial fixture capture stall and corrected tester.runAsync path are honestly retained.

No actionable test defect found within the agreed layered verification plan. Physical display comfort and CAD/metrology claims are outside these raster tests.
