tomassasovsky/segno/docs/reviews/design-external-controls-restack/test-quality-review.md

# Test quality review

Complete with no unresolved actionable finding at the [source binding and
review disclosure](source-review.md). This is one of five roles performed by
the same independent source reviewer; execution was separately owned.

Reviewed assertions cover typed round trips, immutability, whole-payload
rejection, public UI actions, persisted payloads, full-byte events, actual
sketch output and real native admission/settlement. Repair tests distinguish
accepted from refused reacquisition, retain unrelated cleanup, exercise a later
genuine release, and preserve valid unavailable identities while rejecting
structural aliases. The MIDI neighbor uses a busy recipe and same-trigger
repress rather than a source-text assertion.

All 54 final independent probes pass with stable bindings; the three previously
failing probes retain their original assertions. Six aggregate suites and
required coverage floors pass. [Verification](verification.md) carries counts,
skips and execution conditions; [adversarial review](adversarial-review.md)
records fixture corrections and bounded coverage. Screenshot checks and
historical sensitivity evidence remain distinct from current independent
behavioral execution and published-head CI.
