tomassasovsky/segno/packages/fx_catalogue/assets/images/stomps/SmartTune2.png

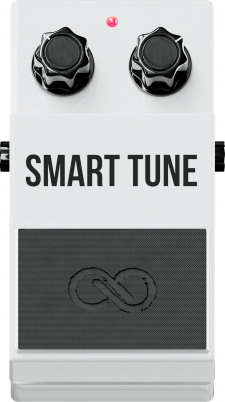
packages/fx_catalogue/assets/images/stomps/SmartTune2.png
