tomassasovsky/segno/test/screenshots/goldens/audio_routing_input_names.png

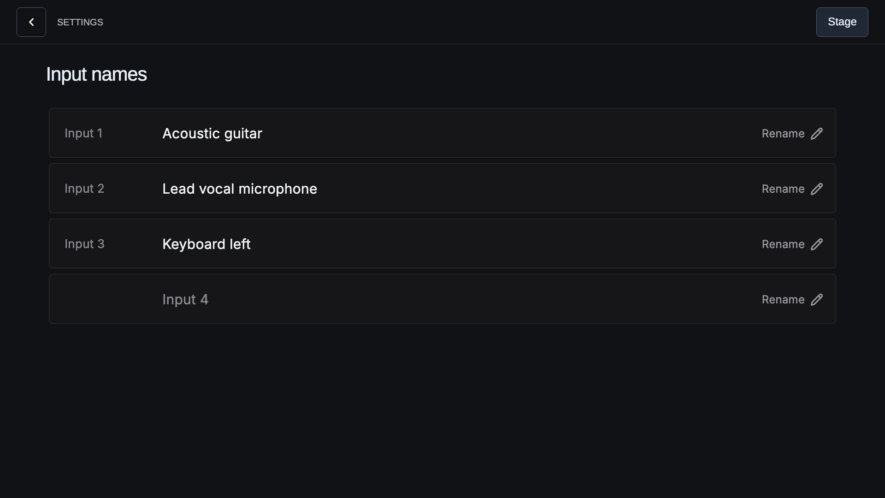
test/screenshots/goldens/audio_routing_input_names.png
