tomassasovsky/segno/test/screenshots/goldens/audio_routing_output_routing.png

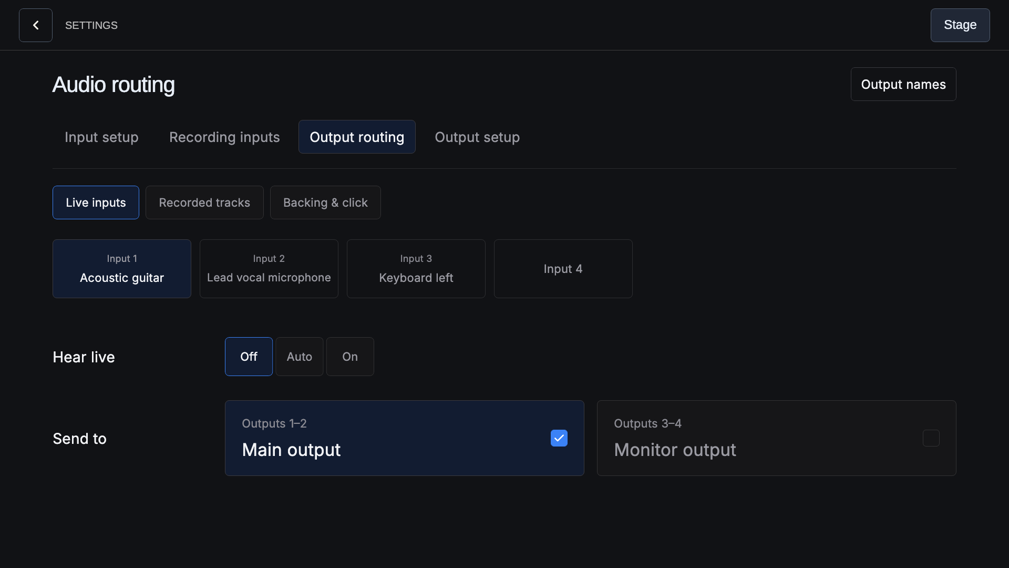
test/screenshots/goldens/audio_routing_output_routing.png
