tomassasovsky/segno/test/screenshots/goldens/audio_routing_recording_inputs.png

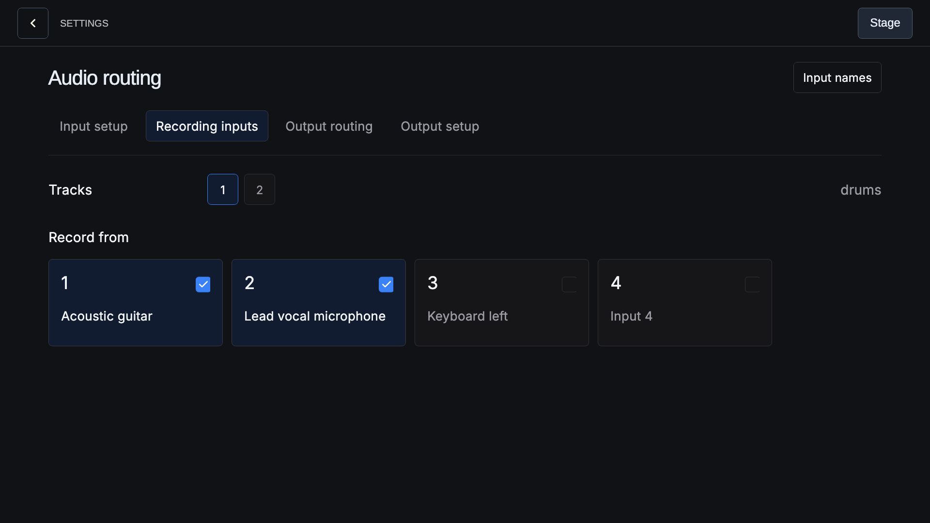
test/screenshots/goldens/audio_routing_recording_inputs.png
