tomassasovsky/segno/test/screenshots/goldens/connect_usb_sheet.png

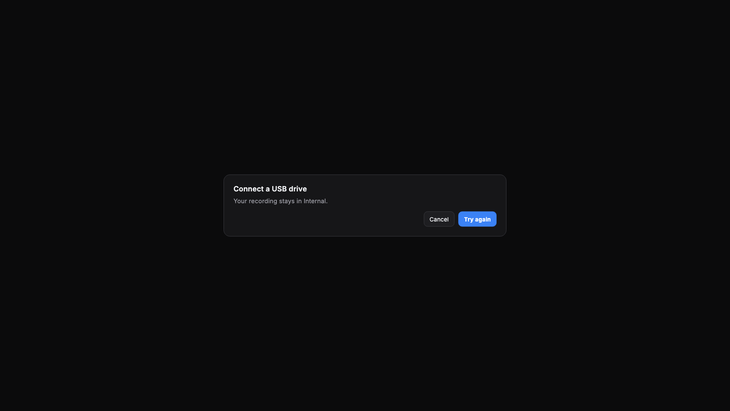
test/screenshots/goldens/connect_usb_sheet.png
