tomassasovsky/segno/test/screenshots/goldens/external_pedals_click_held_released.png

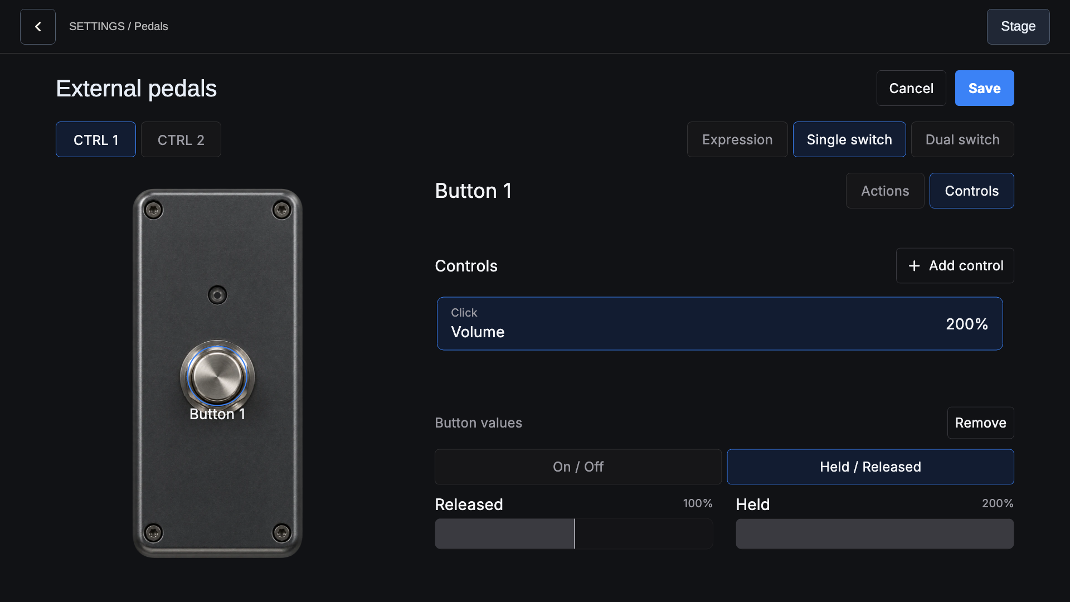
test/screenshots/goldens/external_pedals_click_held_released.png
