tomassasovsky/segno/test/screenshots/goldens/external_pedals_controls.png

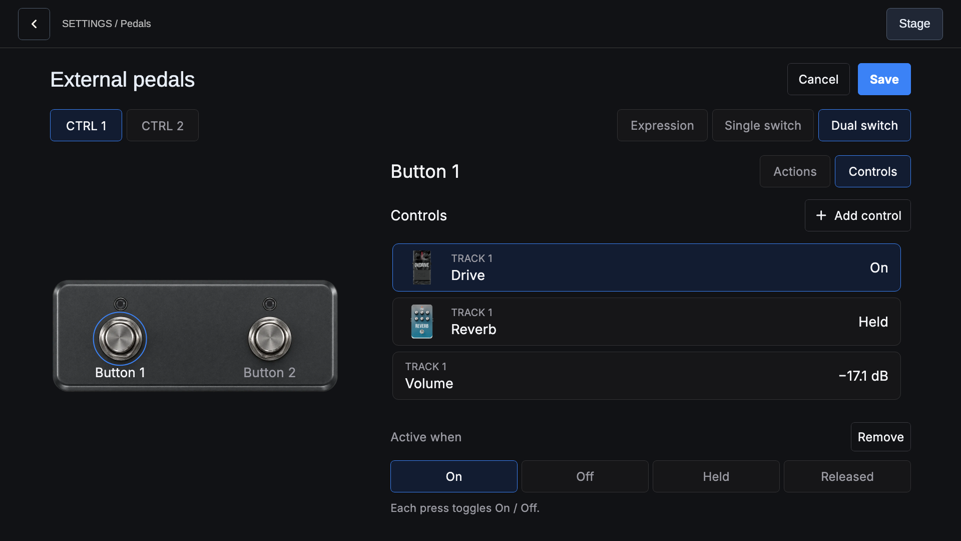
test/screenshots/goldens/external_pedals_controls.png
