tomassasovsky/segno/test/screenshots/goldens/external_pedals_controls_parameter.png

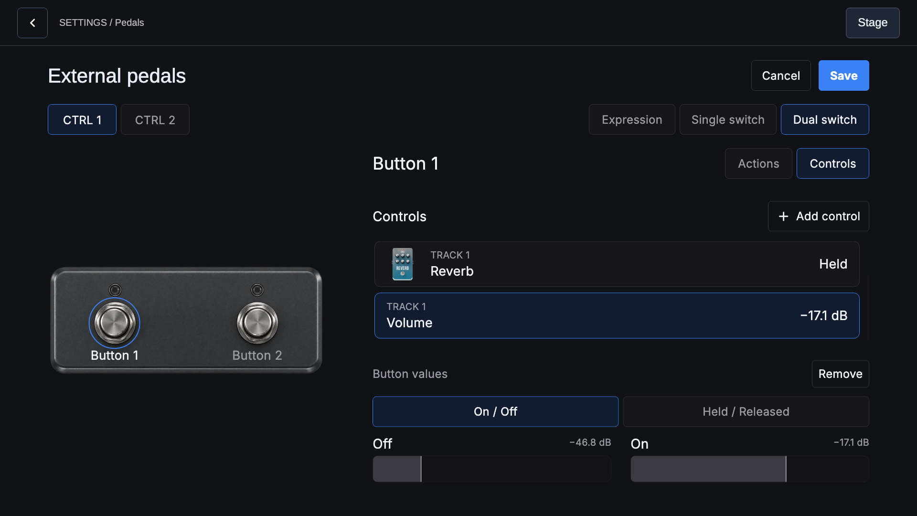
test/screenshots/goldens/external_pedals_controls_parameter.png
