tomassasovsky/segno/test/screenshots/goldens/external_pedals_controls_pick.png

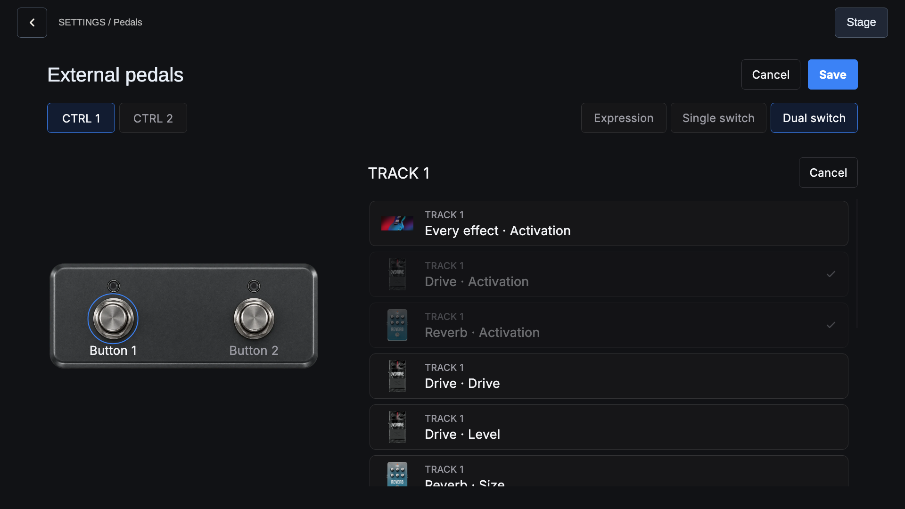
test/screenshots/goldens/external_pedals_controls_pick.png
