tomassasovsky/segno/test/screenshots/goldens/external_pedals_count_in_expression.png

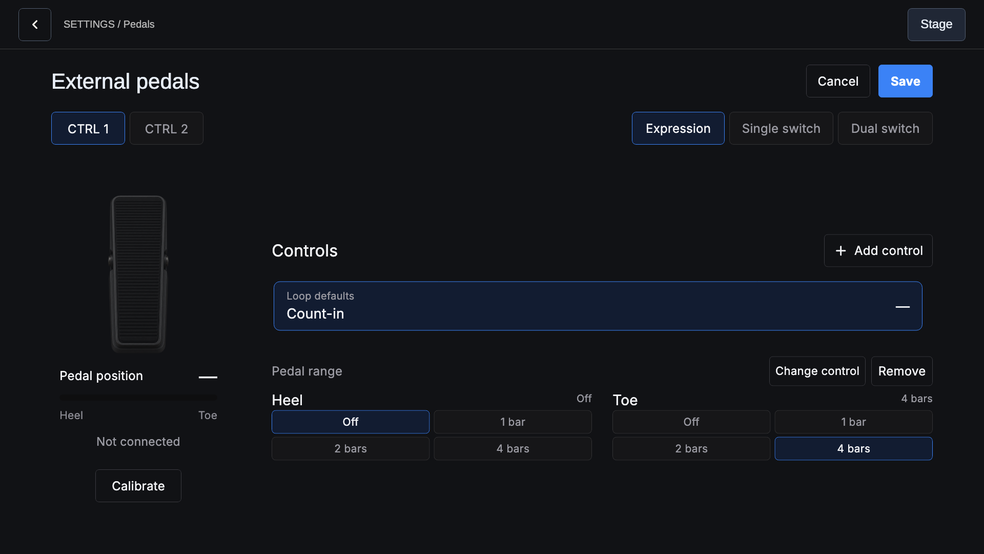
test/screenshots/goldens/external_pedals_count_in_expression.png
