tomassasovsky/segno/test/screenshots/goldens/external_pedals_count_in_held_released.png

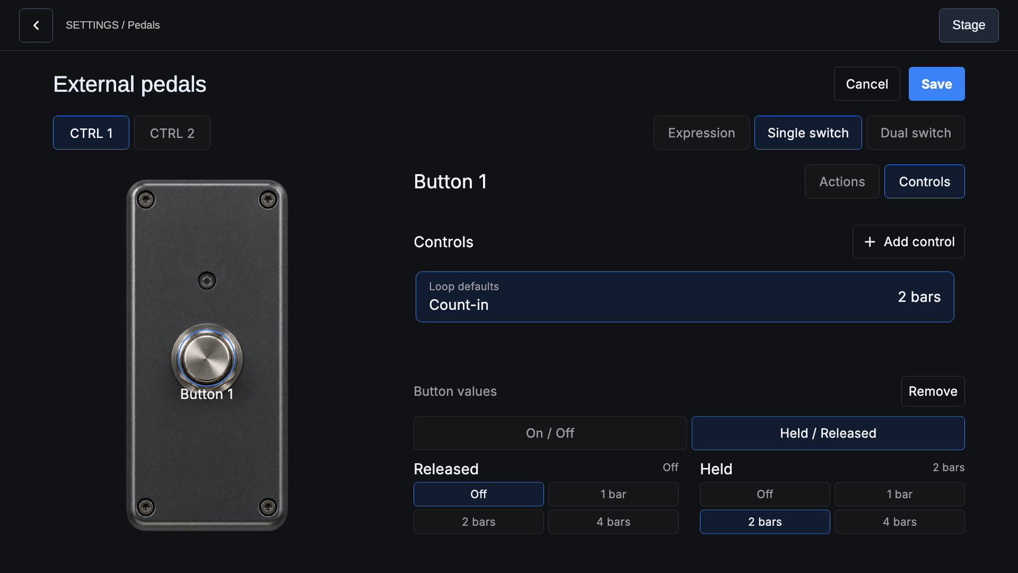
test/screenshots/goldens/external_pedals_count_in_held_released.png
