tomassasovsky/segno/test/screenshots/goldens/external_pedals_dual.png

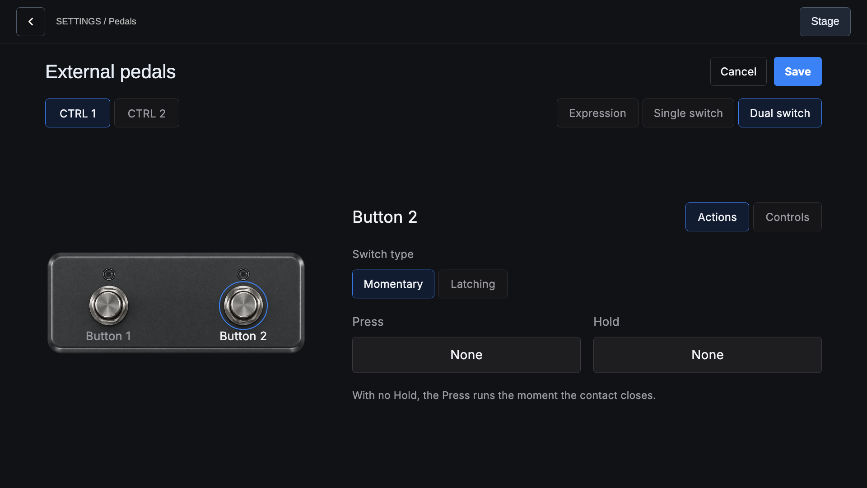
test/screenshots/goldens/external_pedals_dual.png
