tomassasovsky/segno/test/screenshots/goldens/external_pedals_expression.png

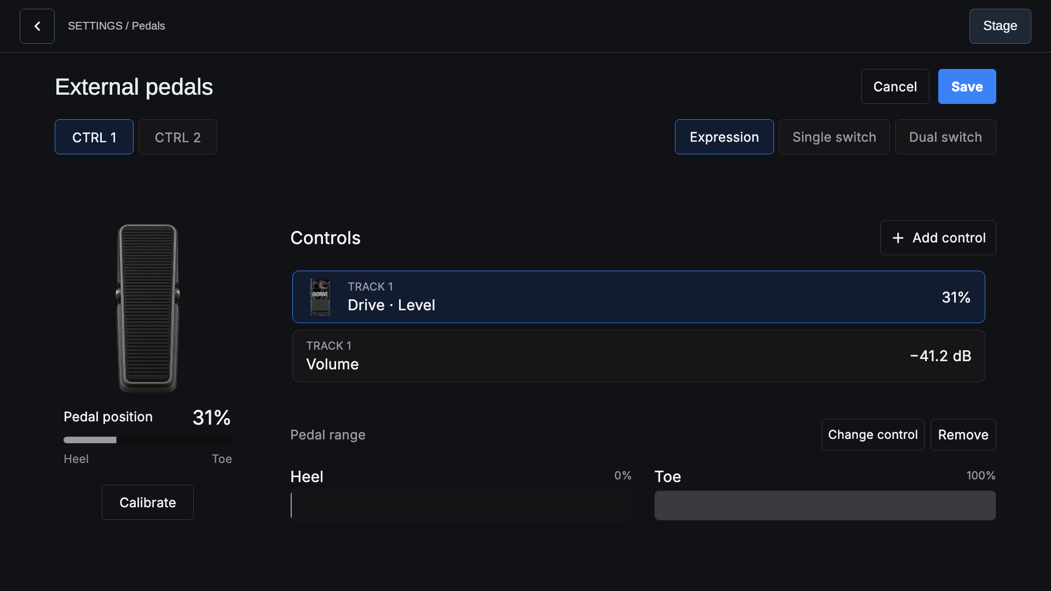
test/screenshots/goldens/external_pedals_expression.png
