tomassasovsky/segno/test/screenshots/goldens/external_pedals_expression_calibrate.png

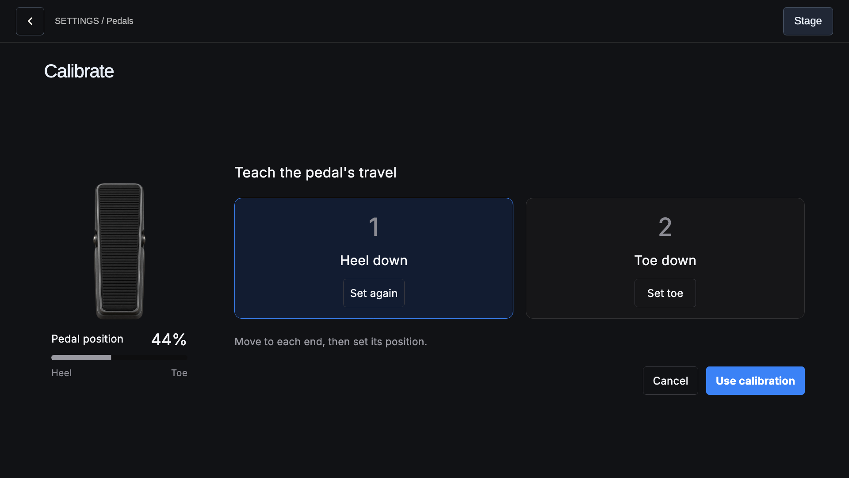
test/screenshots/goldens/external_pedals_expression_calibrate.png
