tomassasovsky/segno/test/screenshots/goldens/external_pedals_expression_controls.png

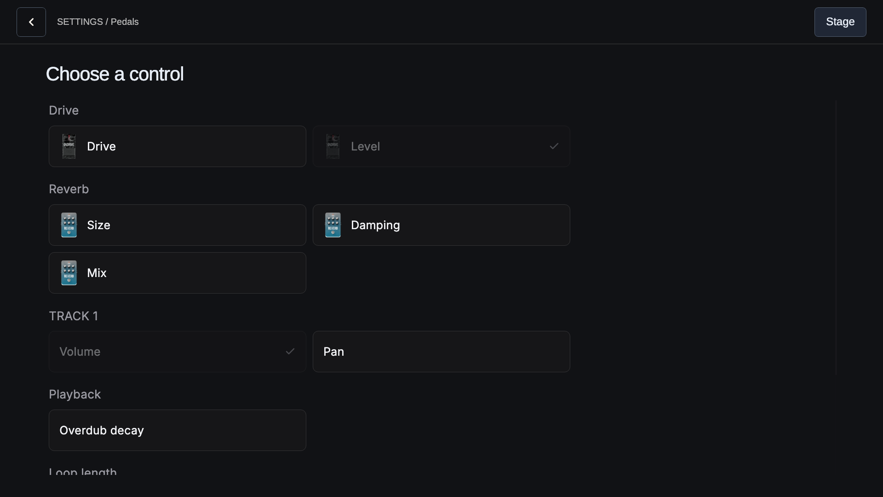
test/screenshots/goldens/external_pedals_expression_controls.png
