tomassasovsky/segno/test/screenshots/goldens/external_pedals_expression_destinations.png

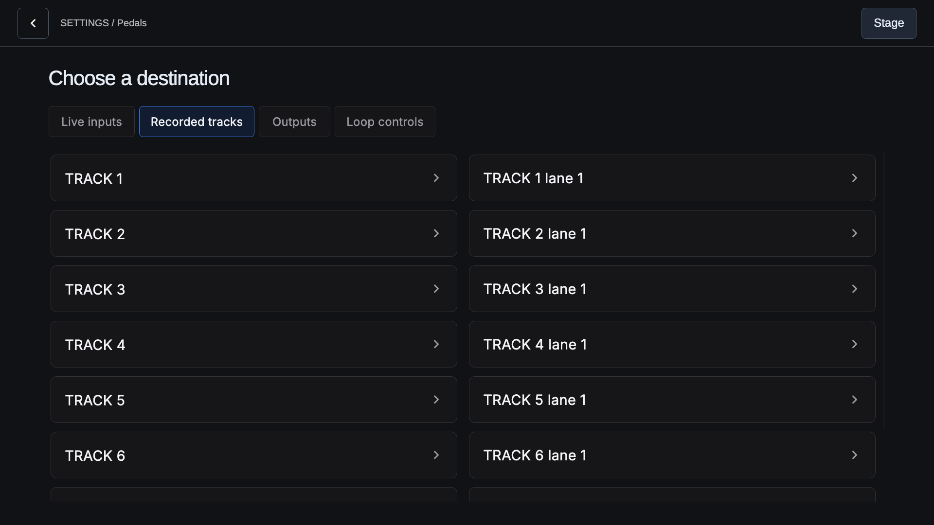
test/screenshots/goldens/external_pedals_expression_destinations.png
