tomassasovsky/segno/test/screenshots/goldens/external_pedals_expression_empty.png

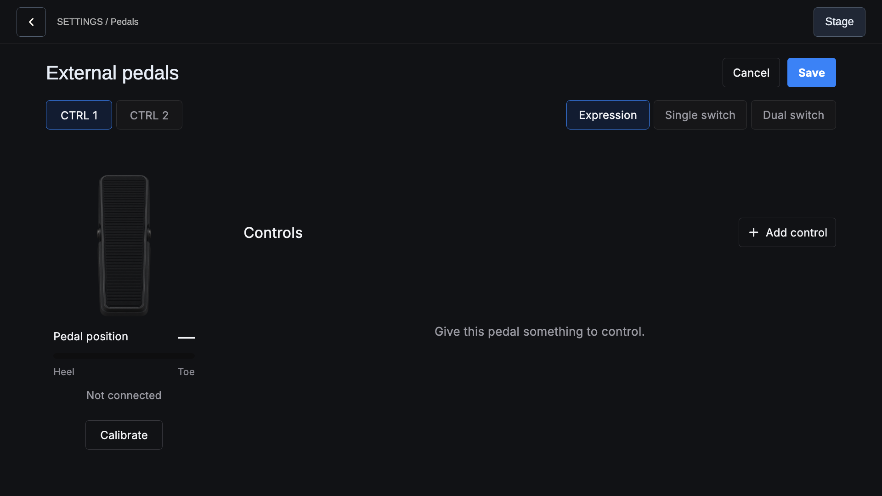
test/screenshots/goldens/external_pedals_expression_empty.png
