tomassasovsky/segno/test/screenshots/goldens/external_pedals_hear_click_held_released.png

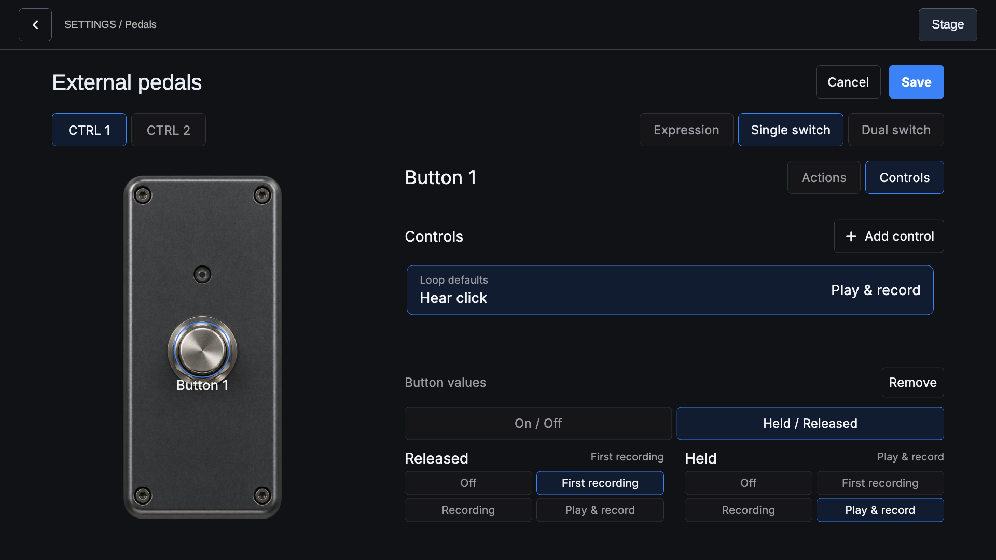
test/screenshots/goldens/external_pedals_hear_click_held_released.png
