tomassasovsky/segno/test/screenshots/goldens/external_pedals_latching.png

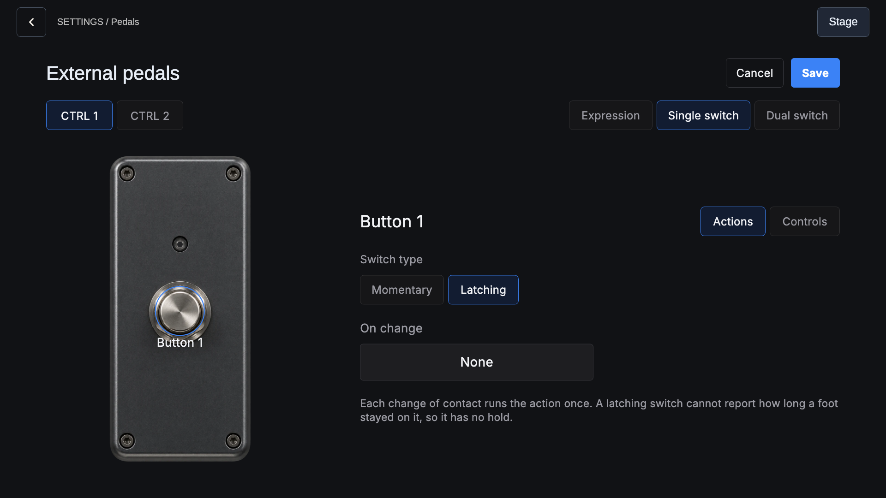
test/screenshots/goldens/external_pedals_latching.png
