tomassasovsky/segno/test/screenshots/goldens/external_pedals_mixer_expression.png

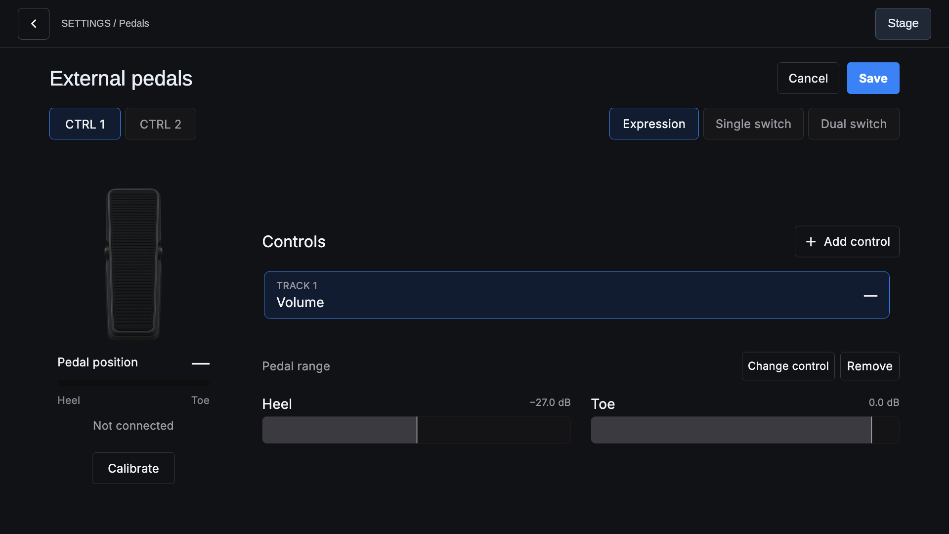
test/screenshots/goldens/external_pedals_mixer_expression.png
