tomassasovsky/segno/test/screenshots/goldens/external_pedals_mixer_pan.png

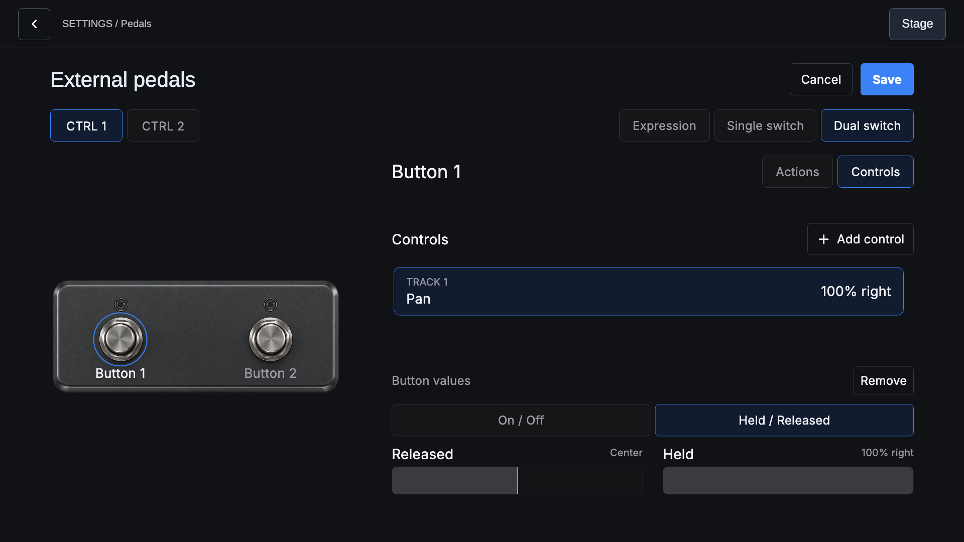
test/screenshots/goldens/external_pedals_mixer_pan.png
