tomassasovsky/segno/test/screenshots/goldens/external_pedals_record_length_held_released.png

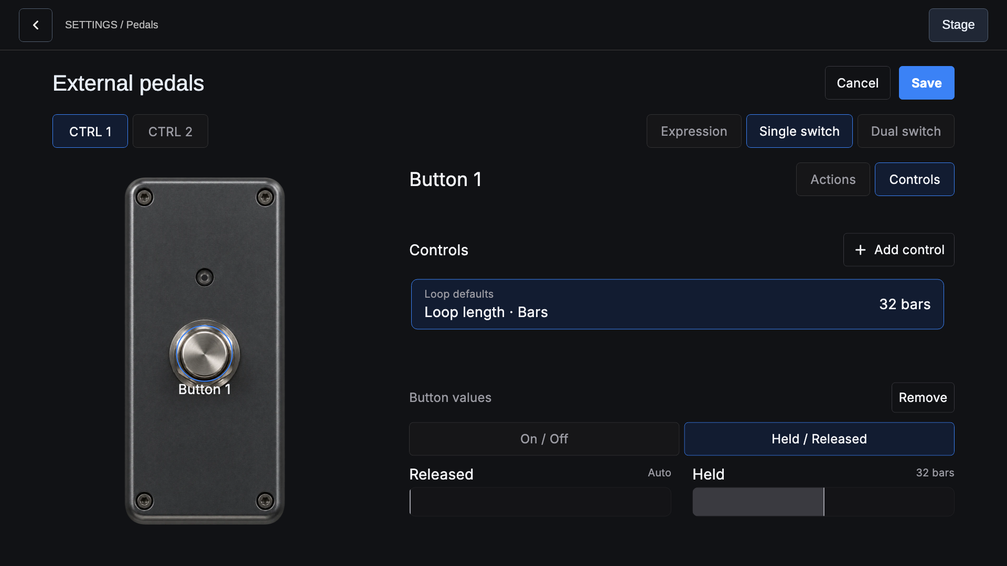
test/screenshots/goldens/external_pedals_record_length_held_released.png
