tomassasovsky/segno/test/screenshots/goldens/foot_custom.png

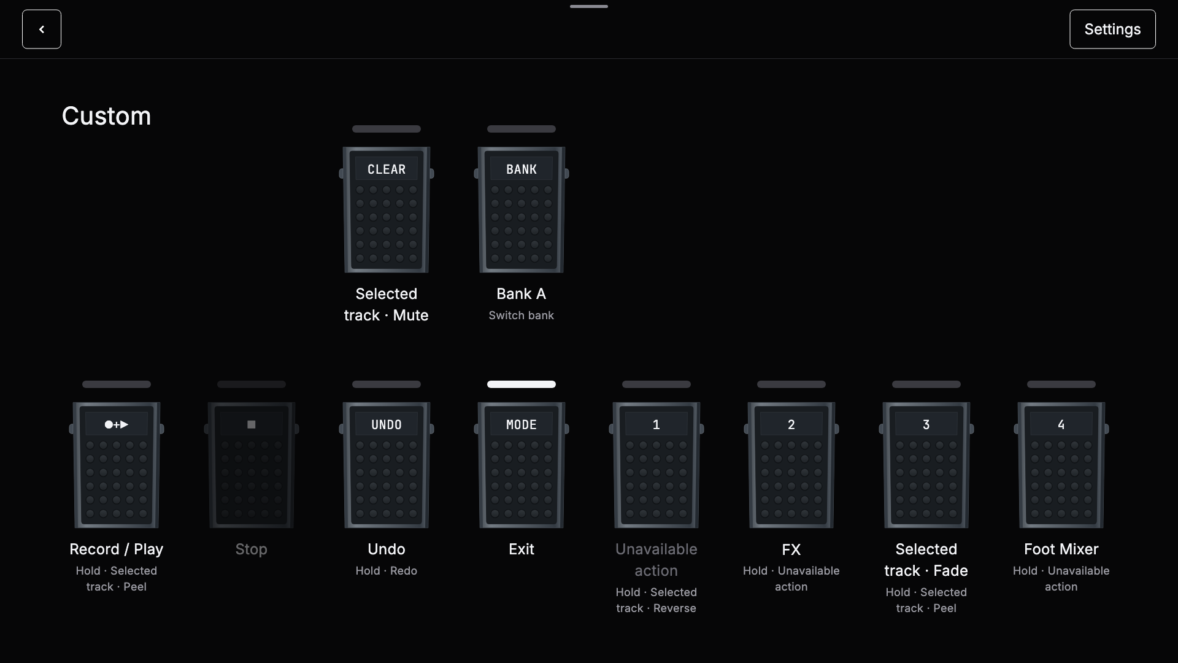
test/screenshots/goldens/foot_custom.png
