tomassasovsky/segno/test/screenshots/goldens/foot_custom_recording.png

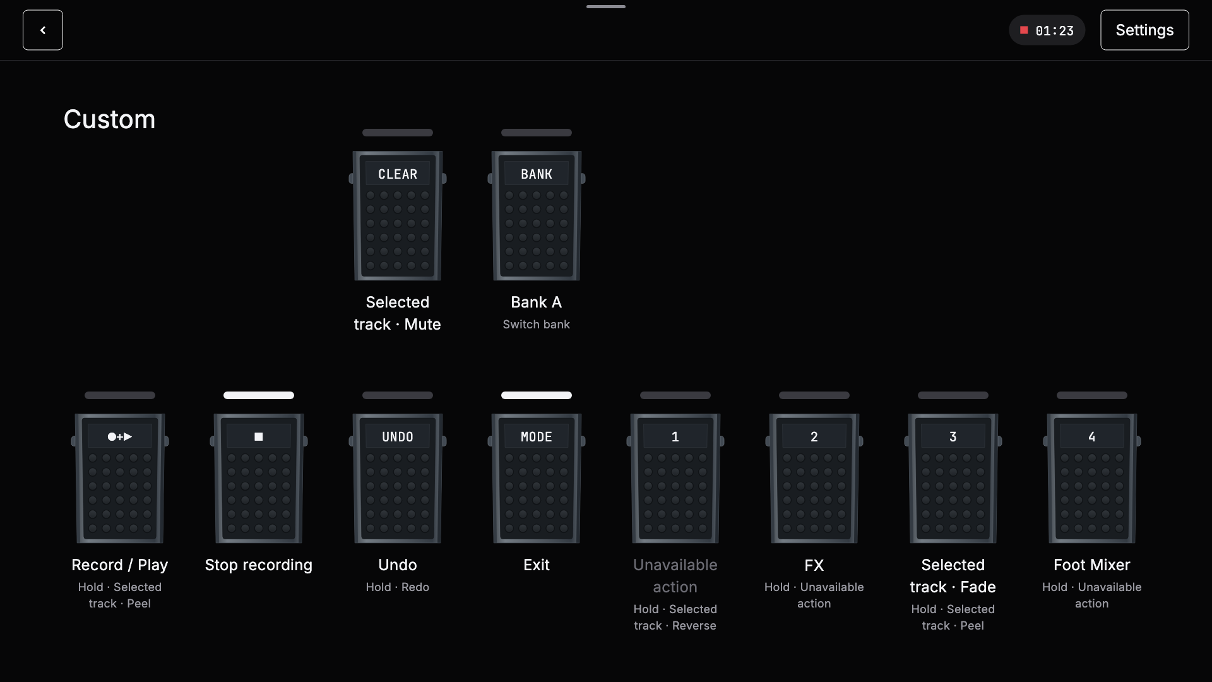
test/screenshots/goldens/foot_custom_recording.png
