tomassasovsky/segno/test/screenshots/goldens/foot_fade_bank.png

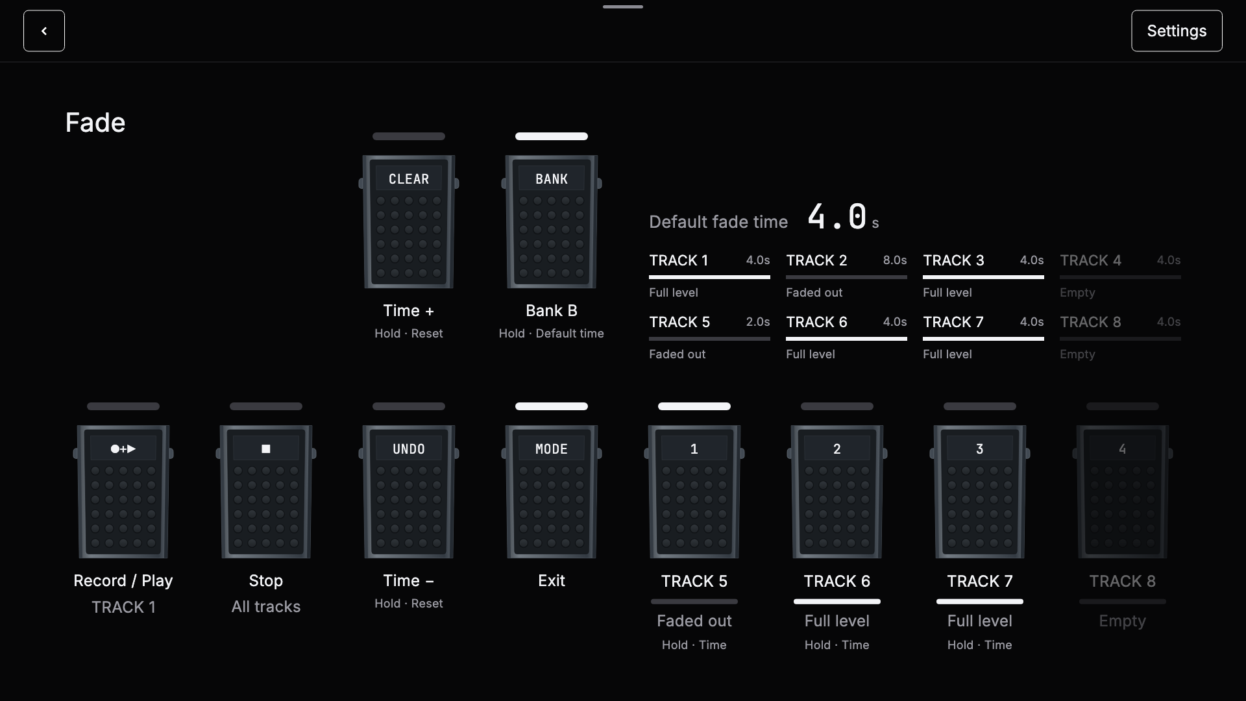
test/screenshots/goldens/foot_fade_bank.png
