tomassasovsky/segno/test/screenshots/goldens/foot_fade_custom.png

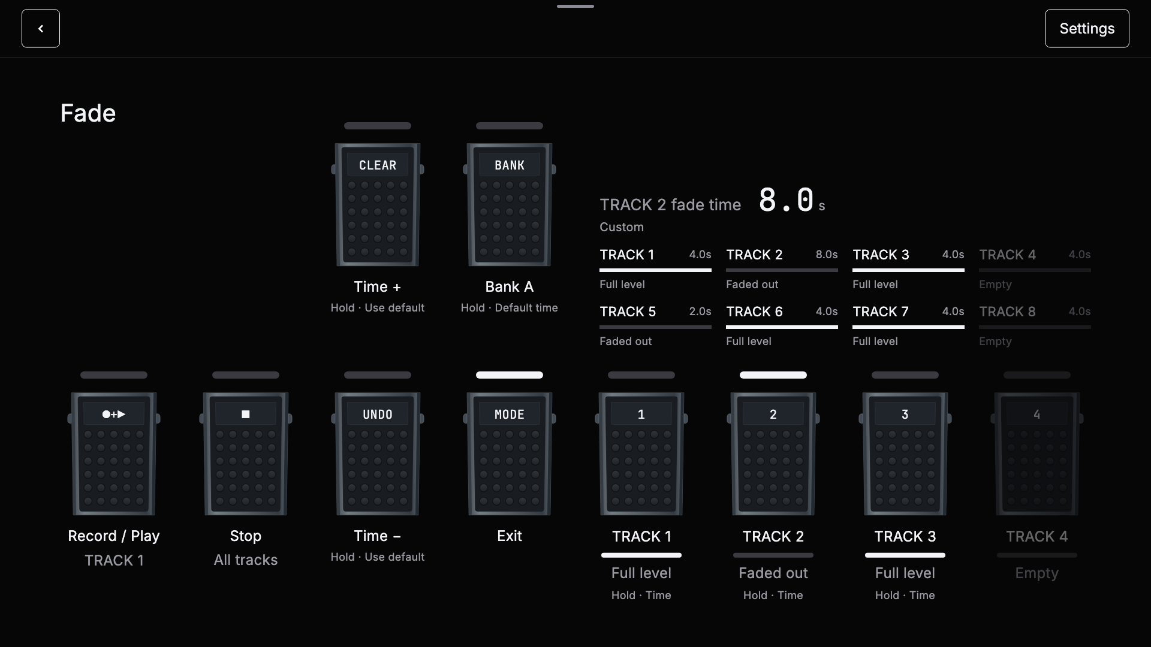
test/screenshots/goldens/foot_fade_custom.png
