tomassasovsky/segno/test/screenshots/goldens/foot_fade_spanish.png

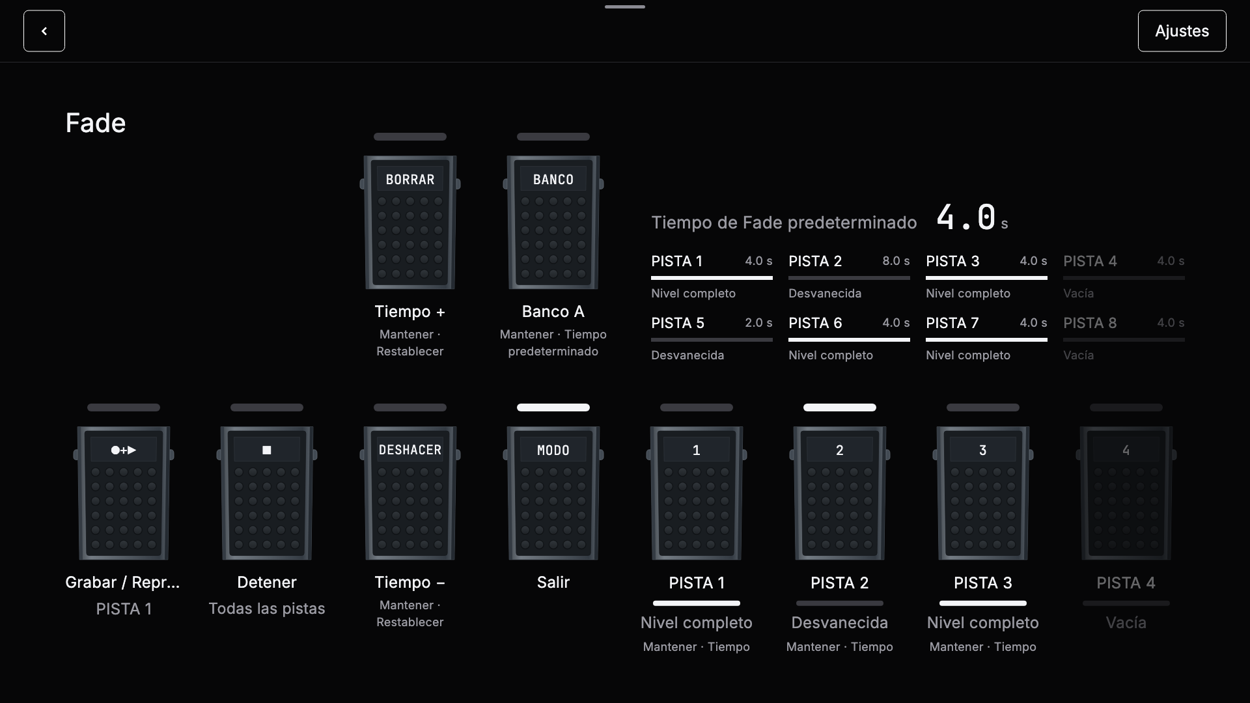
test/screenshots/goldens/foot_fade_spanish.png
