tomassasovsky/segno/test/screenshots/goldens/foot_fx_default.png

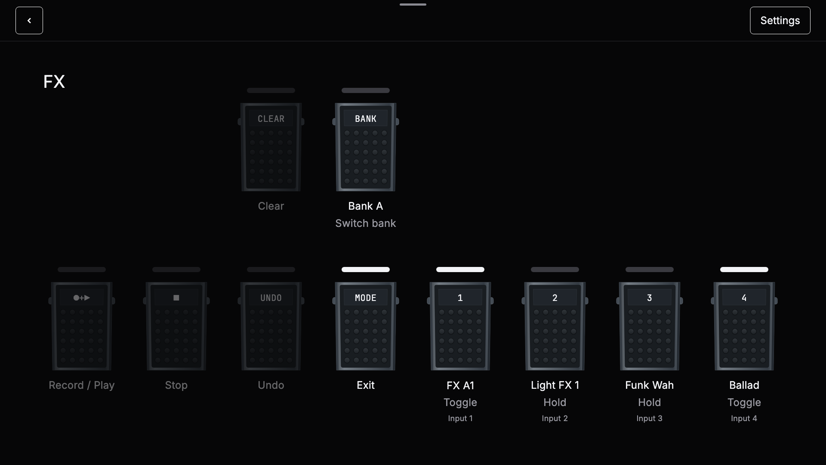
test/screenshots/goldens/foot_fx_default.png
