tomassasovsky/segno/test/screenshots/goldens/foot_length_divide.png

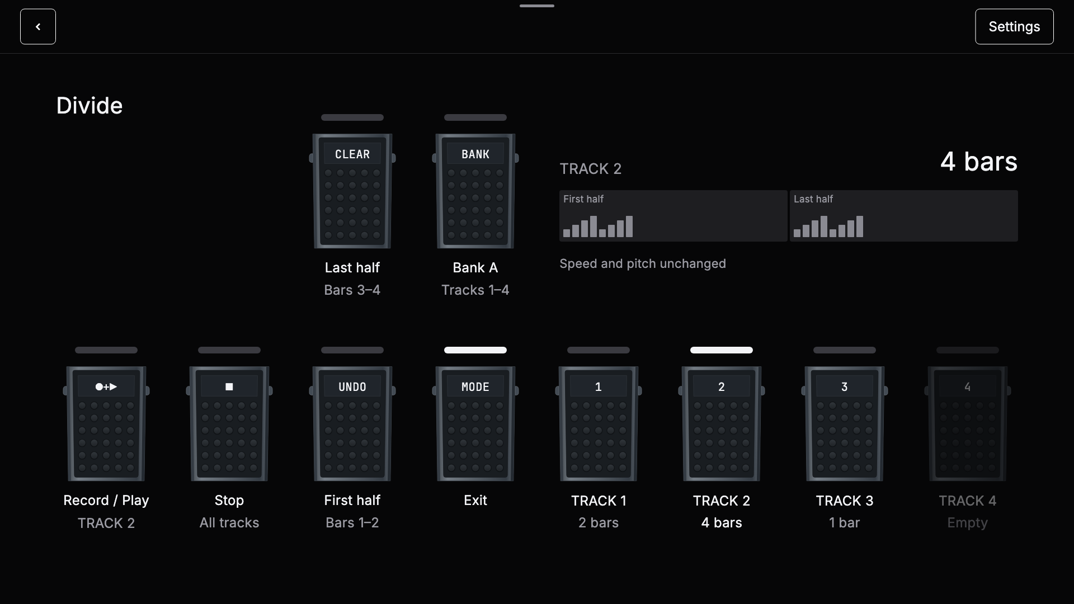
test/screenshots/goldens/foot_length_divide.png
