tomassasovsky/segno/test/screenshots/goldens/foot_length_divide_bank.png

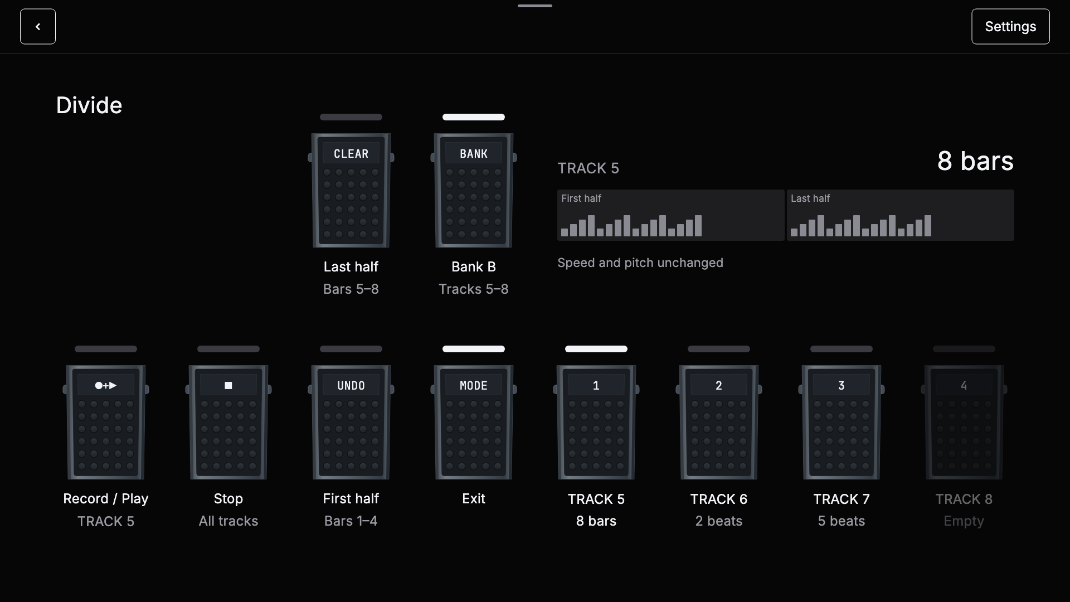
test/screenshots/goldens/foot_length_divide_bank.png
