tomassasovsky/segno/test/screenshots/goldens/foot_length_divide_empty.png

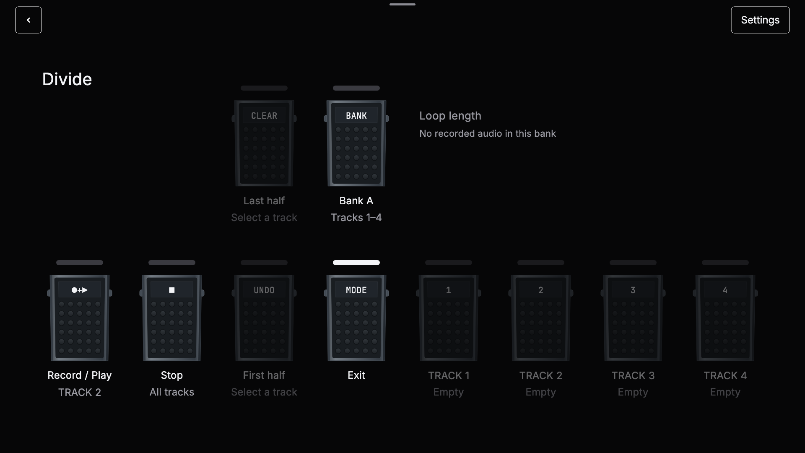
test/screenshots/goldens/foot_length_divide_empty.png
