tomassasovsky/segno/test/screenshots/goldens/foot_length_multiply.png

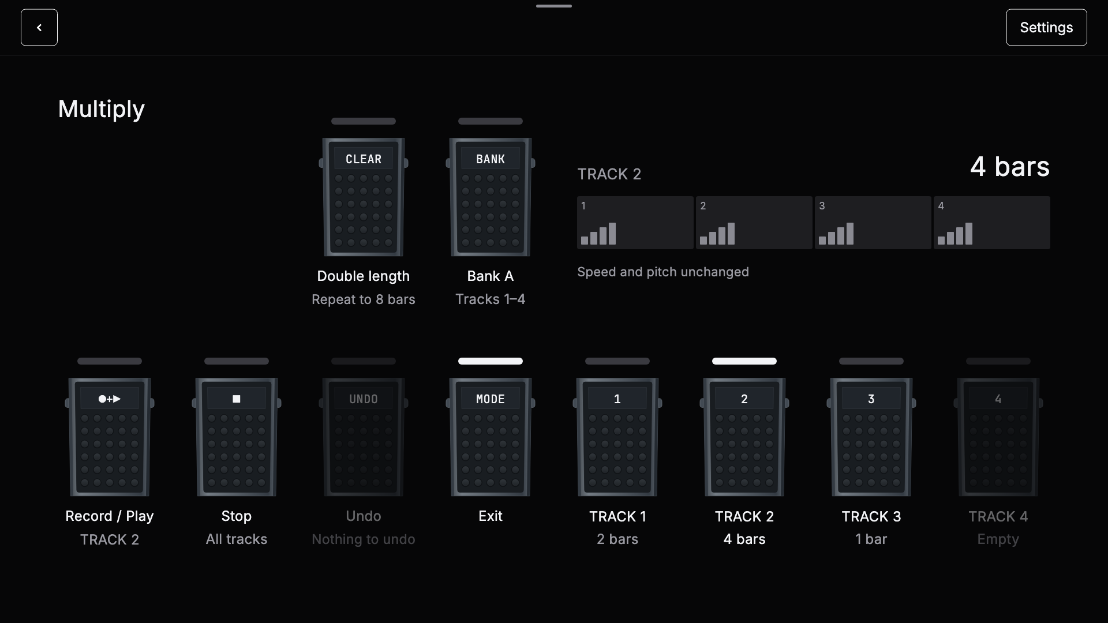
test/screenshots/goldens/foot_length_multiply.png
