tomassasovsky/segno/test/screenshots/goldens/foot_mixer_auto.png

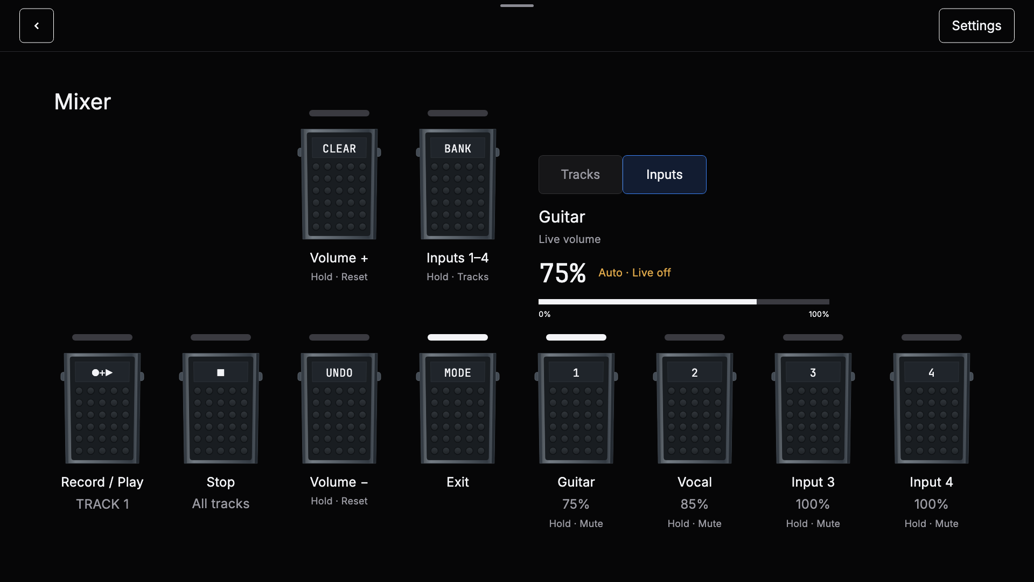
test/screenshots/goldens/foot_mixer_auto.png
