tomassasovsky/segno/test/screenshots/goldens/foot_mixer_spanish.png

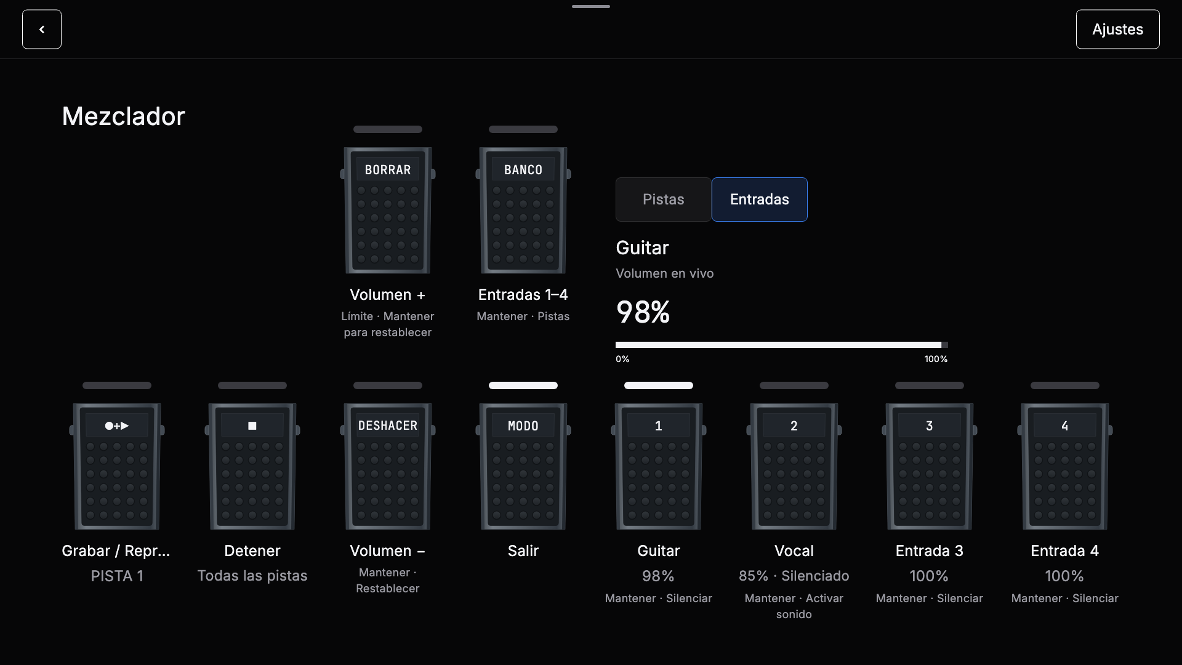
test/screenshots/goldens/foot_mixer_spanish.png
