tomassasovsky/segno/test/screenshots/goldens/foot_mixer_tracks.png

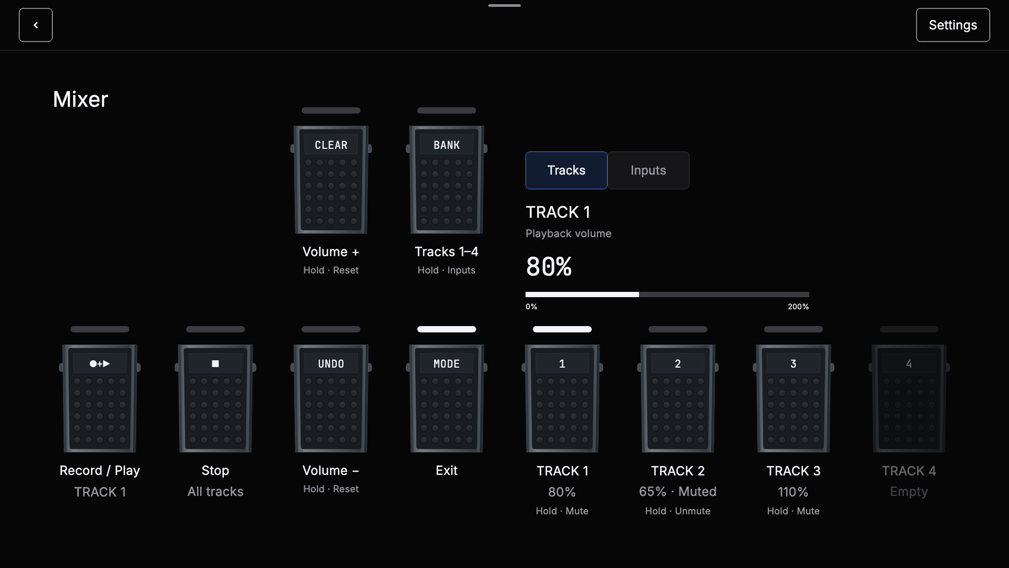
test/screenshots/goldens/foot_mixer_tracks.png
