tomassasovsky/segno/test/screenshots/goldens/foot_peel_bank.png

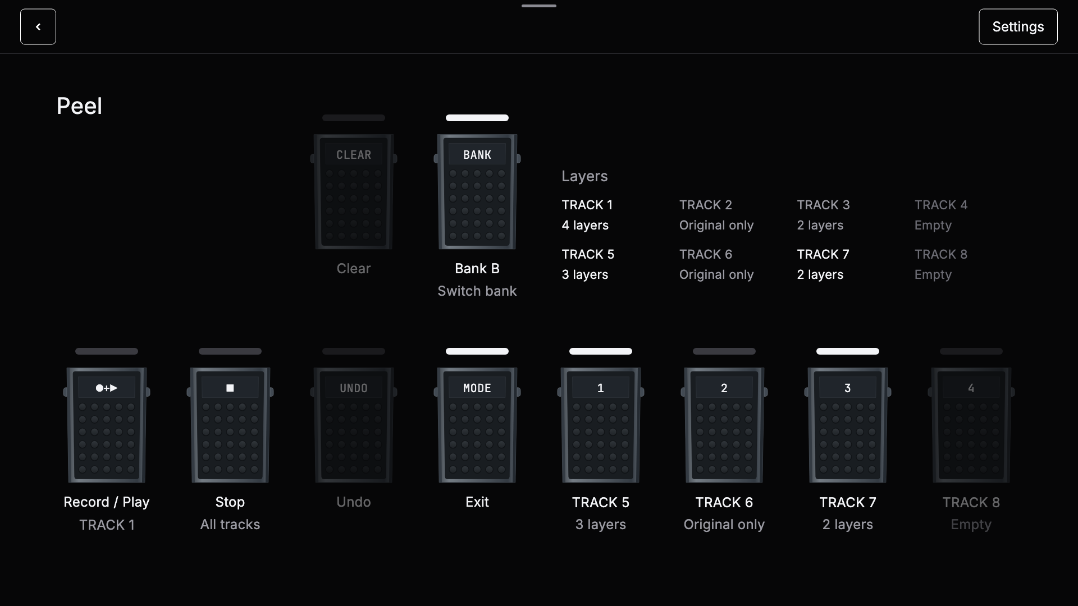
test/screenshots/goldens/foot_peel_bank.png
