tomassasovsky/segno/test/screenshots/goldens/foot_reverse_bank.png

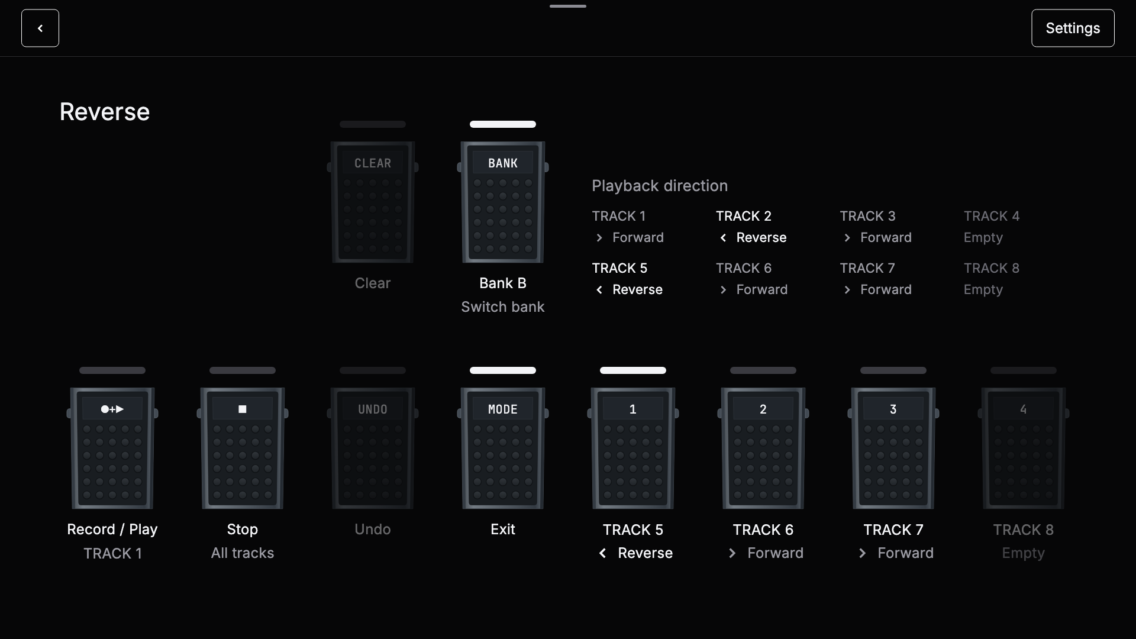
test/screenshots/goldens/foot_reverse_bank.png
