tomassasovsky/segno/test/screenshots/goldens/foot_tuner_18_inputs.png

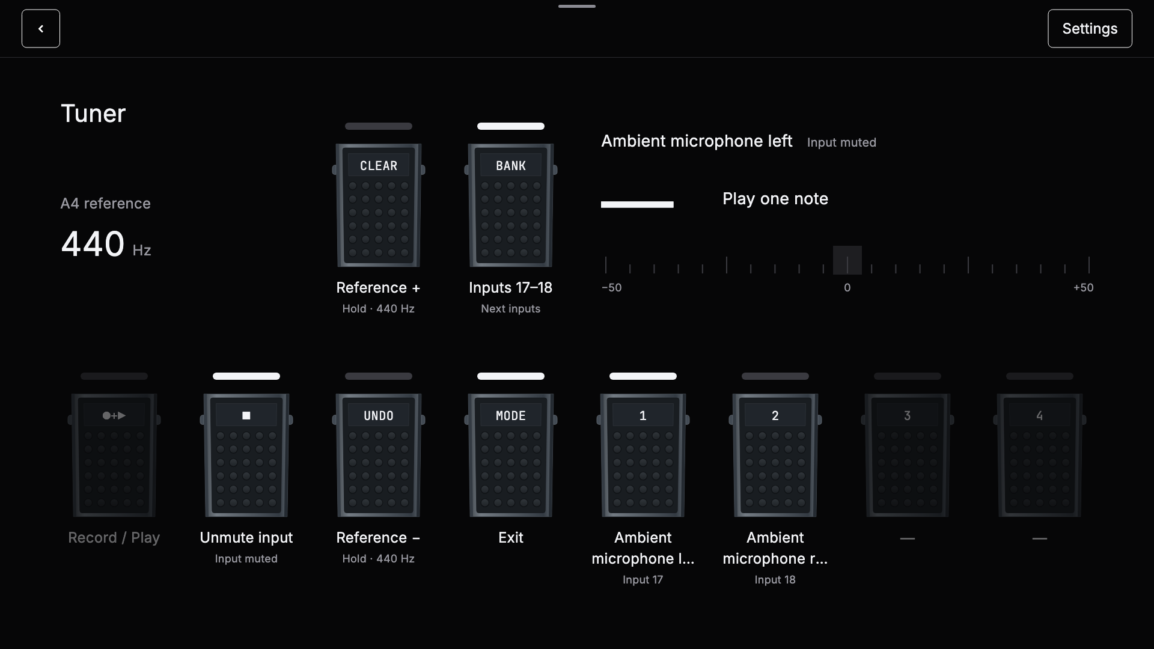
test/screenshots/goldens/foot_tuner_18_inputs.png
