tomassasovsky/segno/test/screenshots/goldens/foot_tuner_in_tune.png

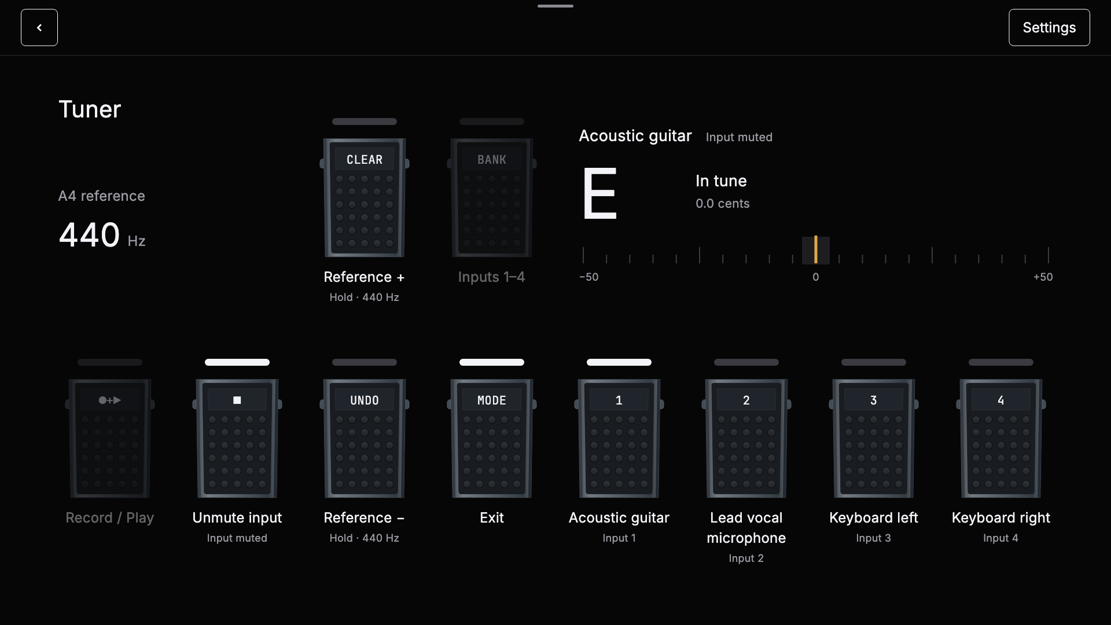
test/screenshots/goldens/foot_tuner_in_tune.png
