tomassasovsky/segno/test/screenshots/goldens/fx_all_tracks.png

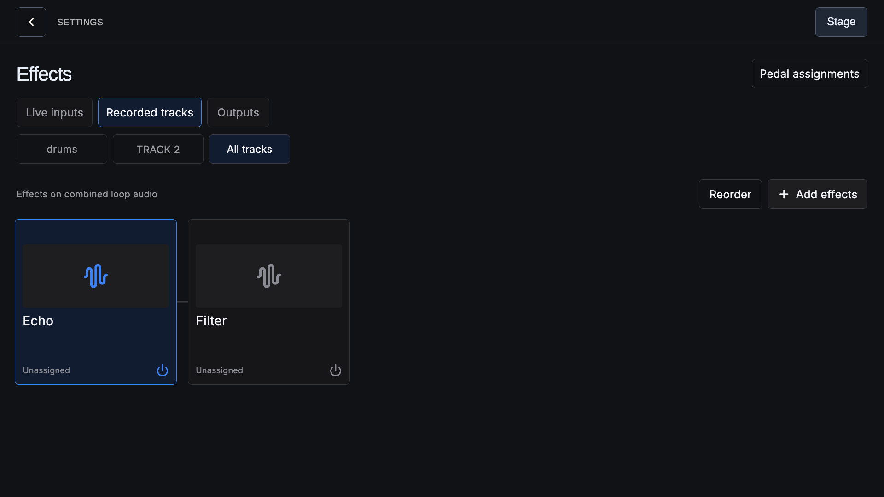
test/screenshots/goldens/fx_all_tracks.png
