tomassasovsky/segno/test/screenshots/goldens/fx_effect_editor.png

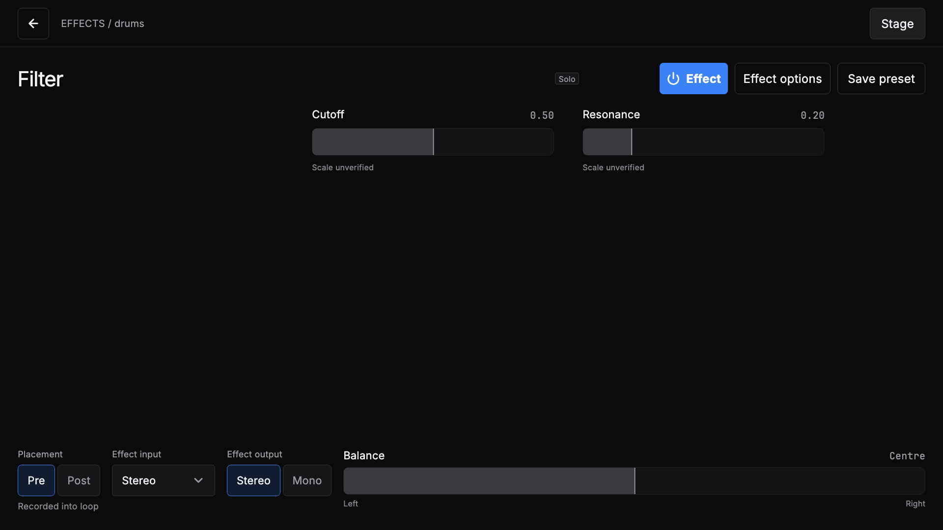
test/screenshots/goldens/fx_effect_editor.png
