tomassasovsky/segno/test/screenshots/goldens/fx_library.png

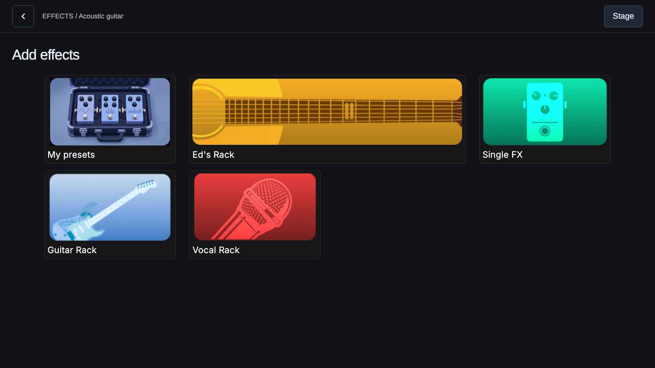
test/screenshots/goldens/fx_library.png
