tomassasovsky/segno/test/screenshots/goldens/fx_live_inputs.png

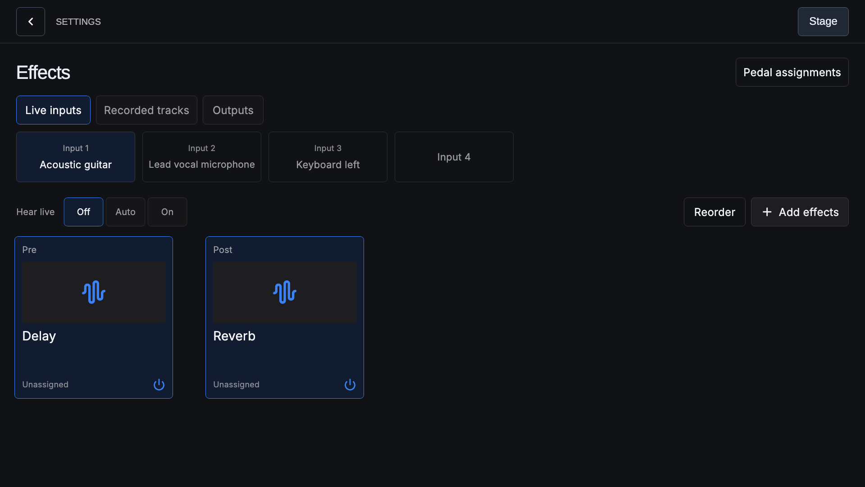
test/screenshots/goldens/fx_live_inputs.png
