tomassasovsky/segno/test/screenshots/goldens/fx_my_presets.png

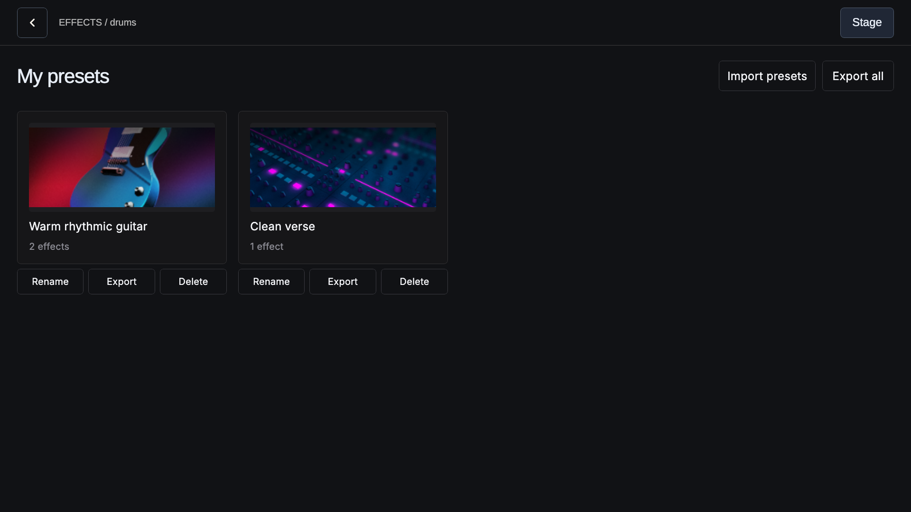
test/screenshots/goldens/fx_my_presets.png
