tomassasovsky/segno/test/screenshots/goldens/fx_outputs.png

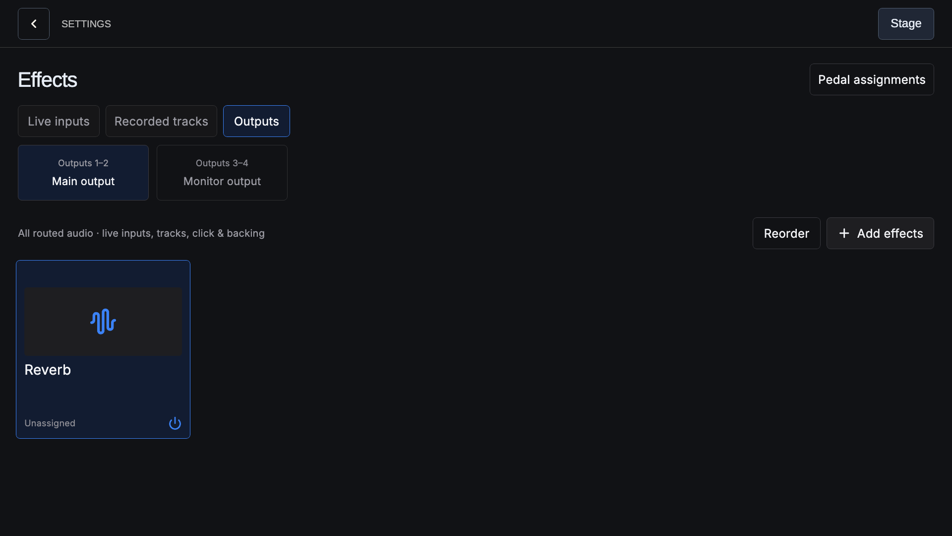
test/screenshots/goldens/fx_outputs.png
