tomassasovsky/segno/test/screenshots/goldens/fx_pedal_assignments.png

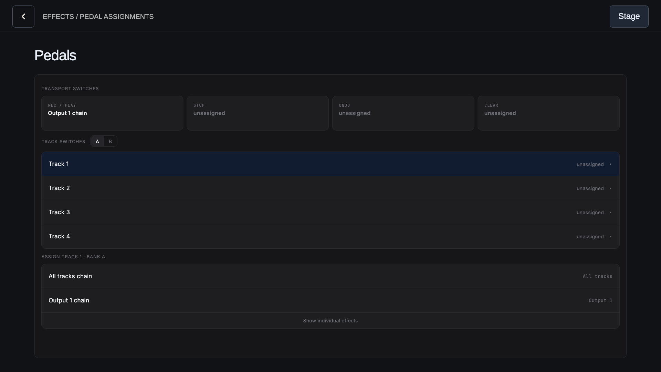
test/screenshots/goldens/fx_pedal_assignments.png
