tomassasovsky/segno/test/screenshots/goldens/fx_rack_editor.png

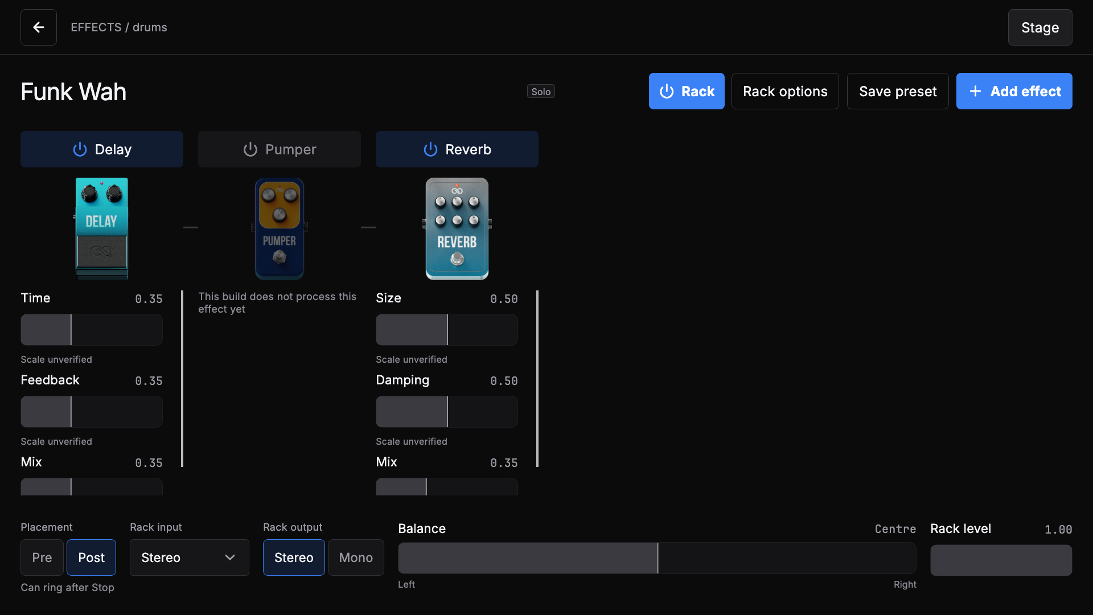
test/screenshots/goldens/fx_rack_editor.png
