tomassasovsky/segno/test/screenshots/goldens/fx_rack_options.png

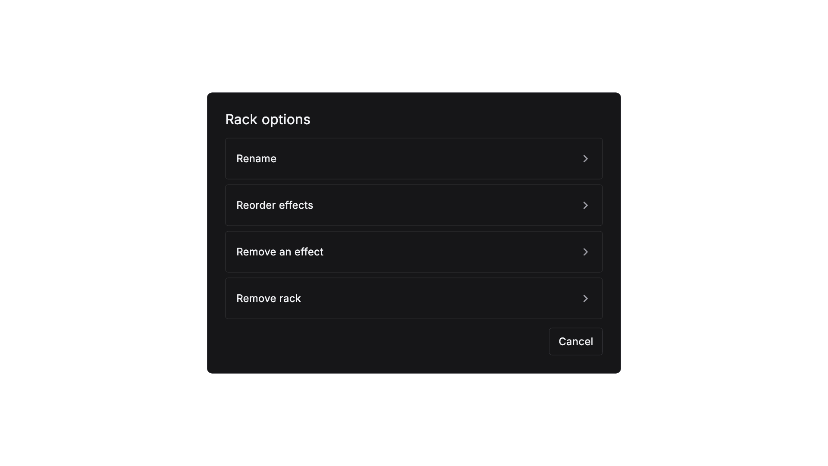
test/screenshots/goldens/fx_rack_options.png
