tomassasovsky/segno/test/screenshots/goldens/fx_racks.png

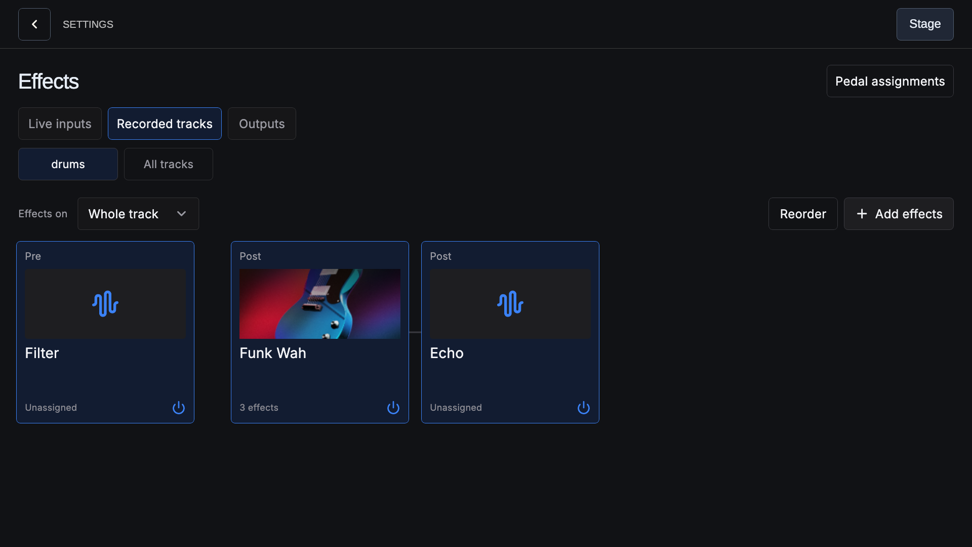
test/screenshots/goldens/fx_racks.png
