tomassasovsky/segno/test/screenshots/goldens/fx_reorder.png

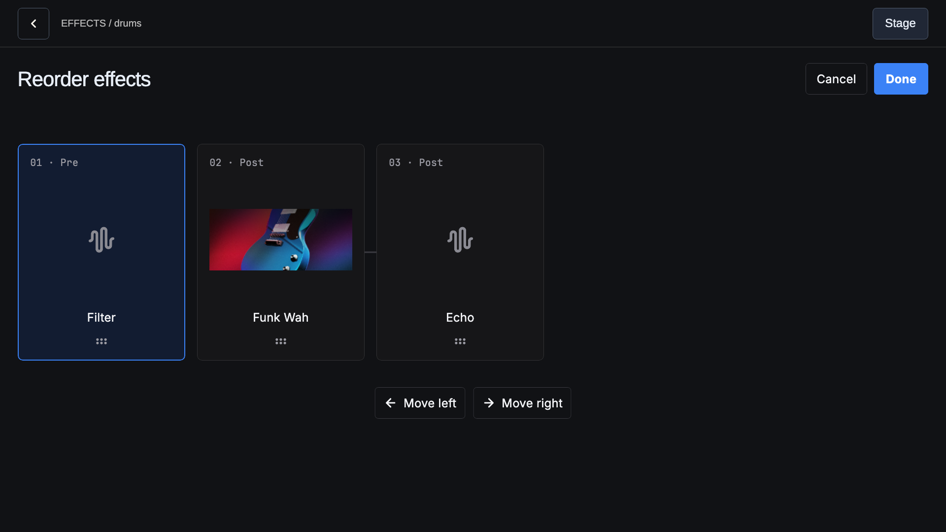
test/screenshots/goldens/fx_reorder.png
