tomassasovsky/segno/test/screenshots/goldens/library_audio_chooser.png

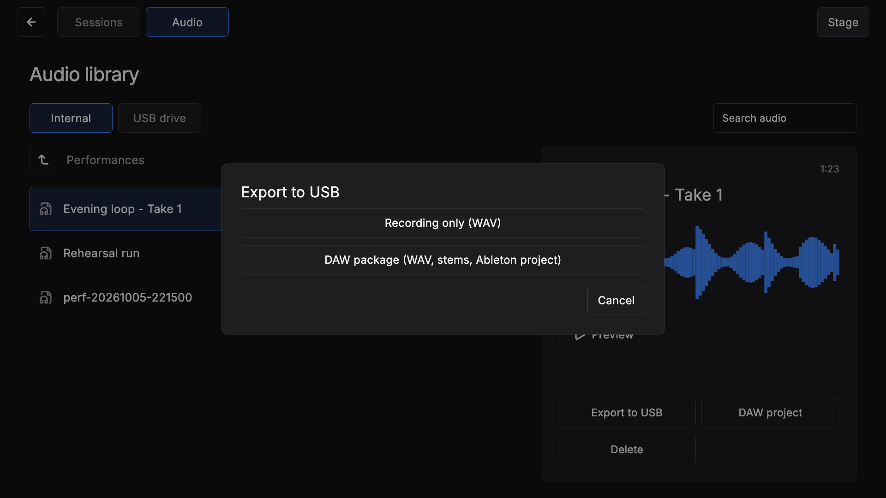
test/screenshots/goldens/library_audio_chooser.png
