tomassasovsky/segno/test/screenshots/goldens/library_audio_conflict.png

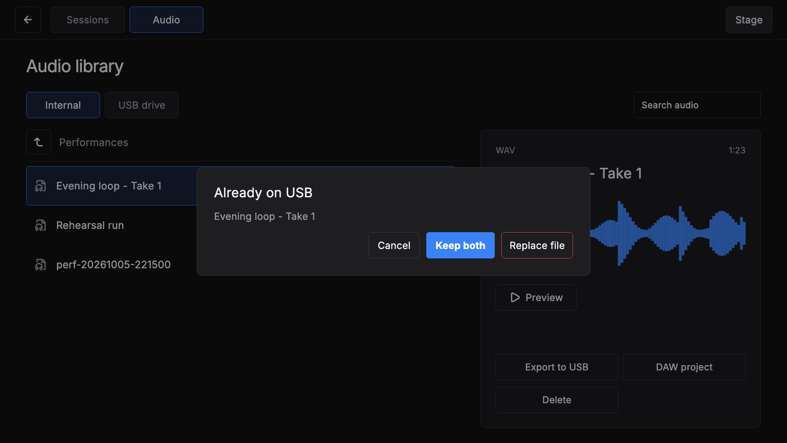
test/screenshots/goldens/library_audio_conflict.png
