tomassasovsky/segno/test/screenshots/goldens/library_audio_done.png

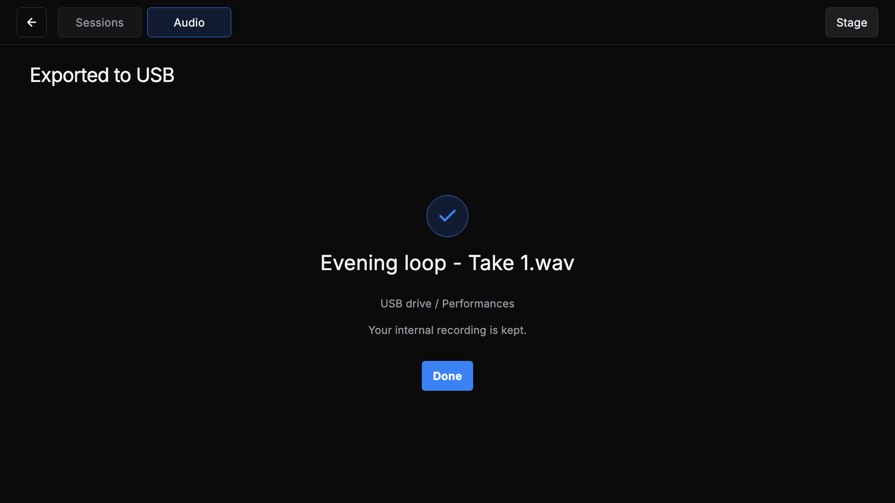
test/screenshots/goldens/library_audio_done.png
