tomassasovsky/segno/test/screenshots/goldens/library_audio_exporting.png

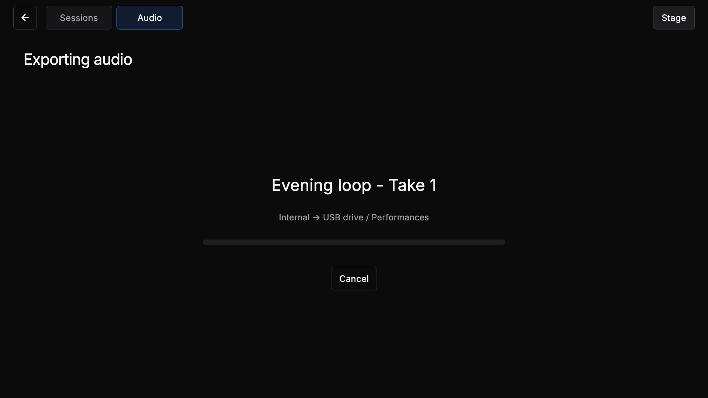
test/screenshots/goldens/library_audio_exporting.png
