tomassasovsky/segno/test/screenshots/goldens/library_audio_folders.png

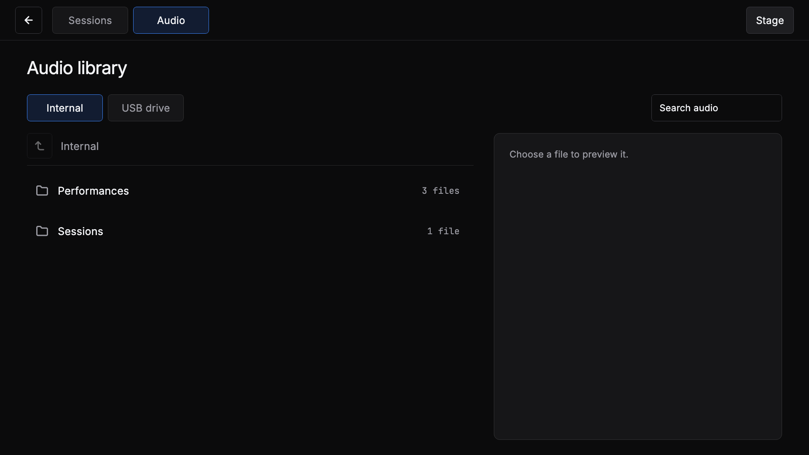
test/screenshots/goldens/library_audio_folders.png
