tomassasovsky/segno/test/screenshots/goldens/library_audio_full.png

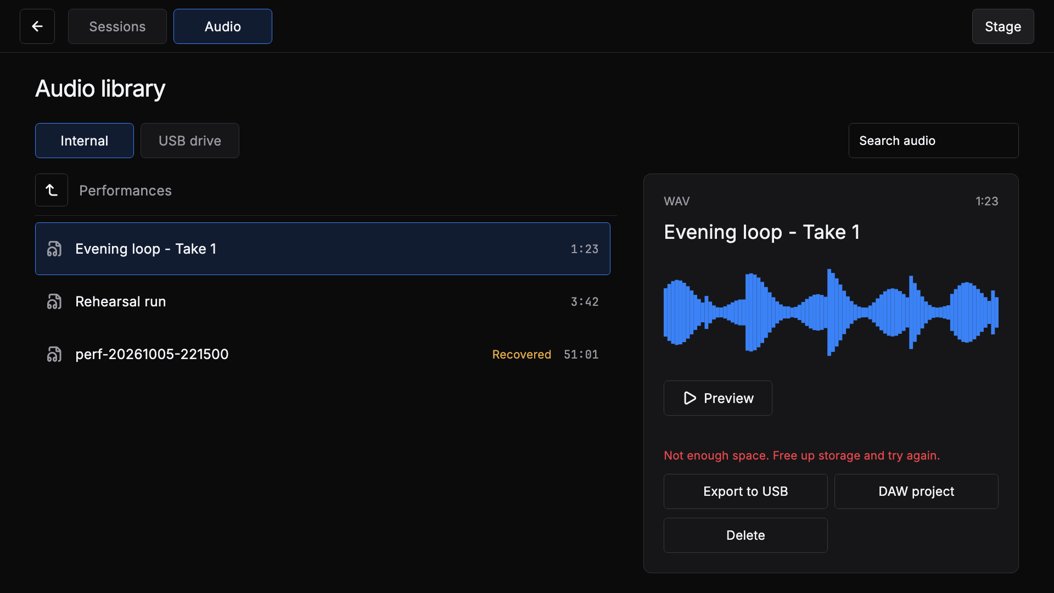
test/screenshots/goldens/library_audio_full.png
