tomassasovsky/segno/test/screenshots/goldens/library_backup_conflict.png

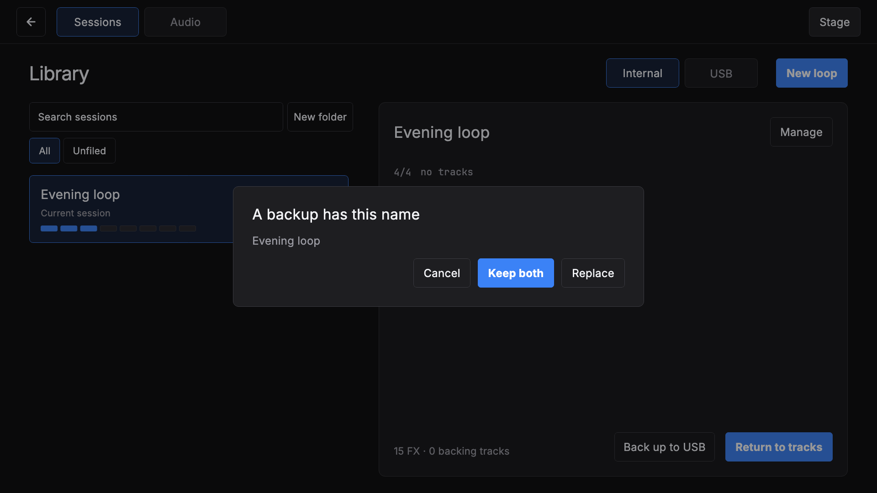
test/screenshots/goldens/library_backup_conflict.png
