tomassasovsky/segno/test/screenshots/goldens/library_backup_progress.png

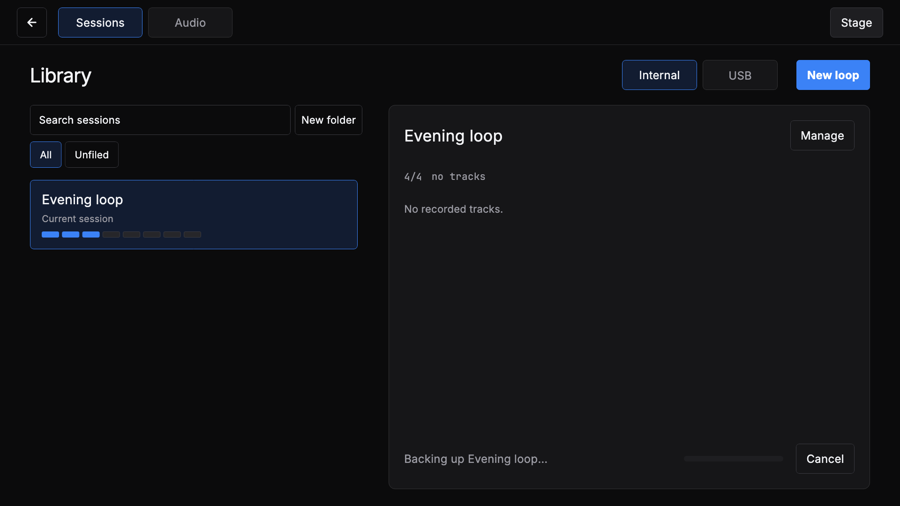
test/screenshots/goldens/library_backup_progress.png
