tomassasovsky/segno/test/screenshots/goldens/library_backup_restored.png

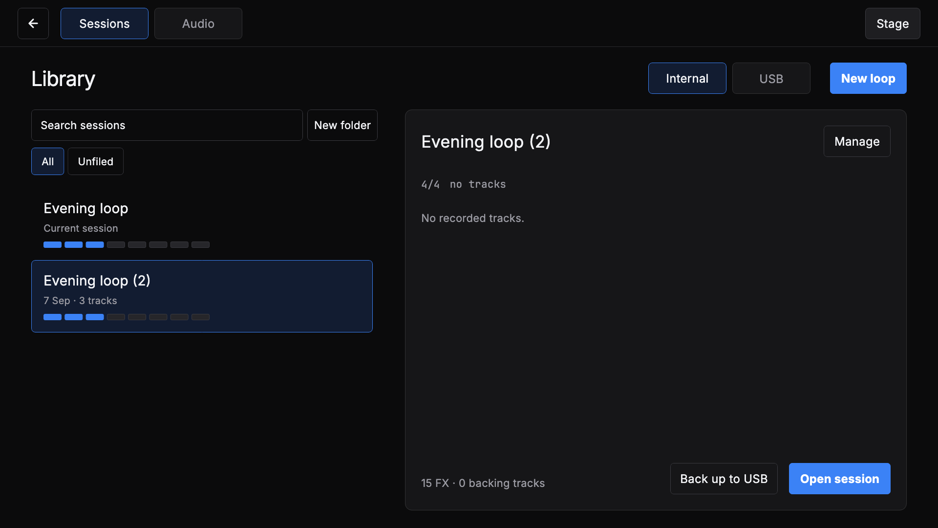
test/screenshots/goldens/library_backup_restored.png
