tomassasovsky/segno/test/screenshots/goldens/library_backup_usb_list.png

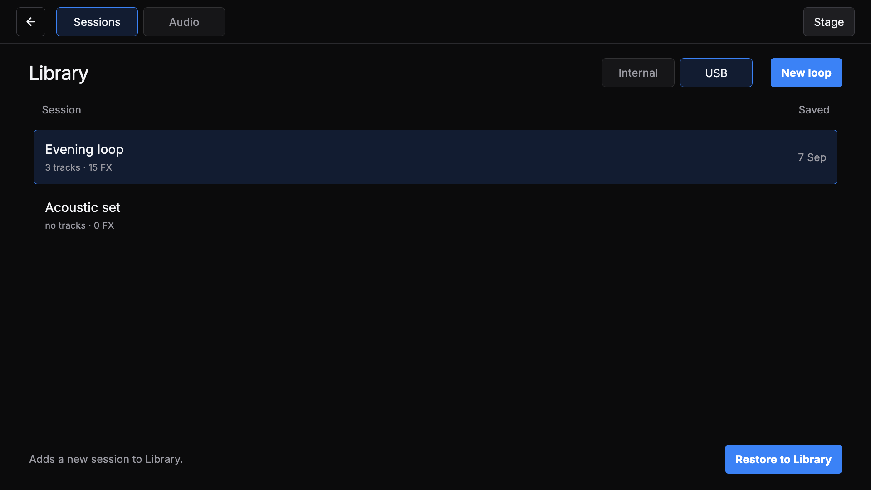
test/screenshots/goldens/library_backup_usb_list.png
