tomassasovsky/segno/test/screenshots/goldens/library_current.png

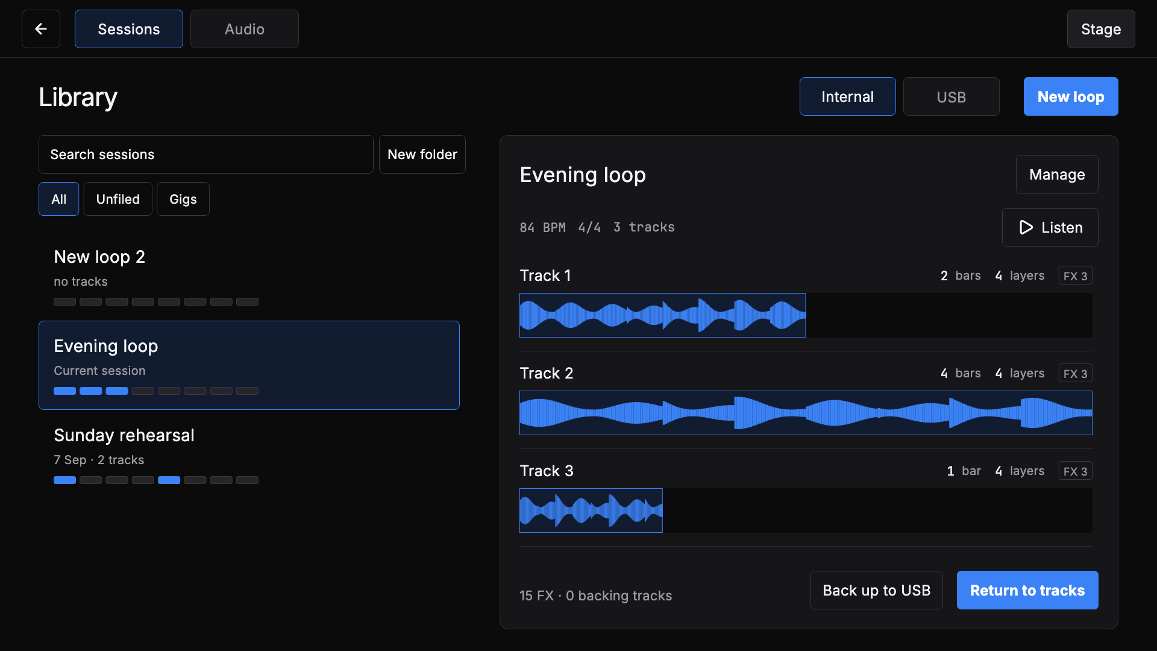
test/screenshots/goldens/library_current.png
