tomassasovsky/segno/test/screenshots/goldens/library_manage.png

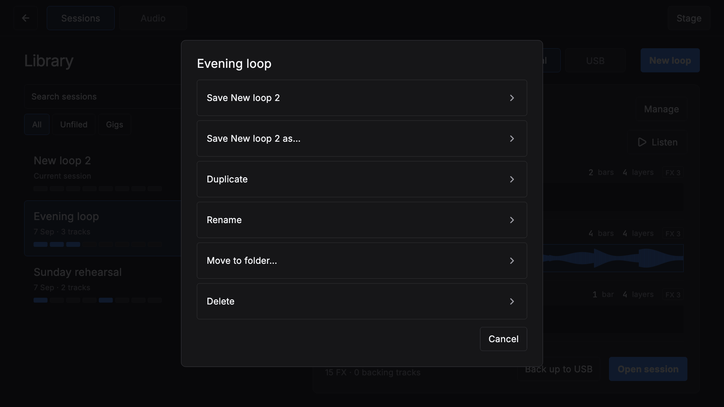
test/screenshots/goldens/library_manage.png
