tomassasovsky/segno/test/screenshots/goldens/library_move.png

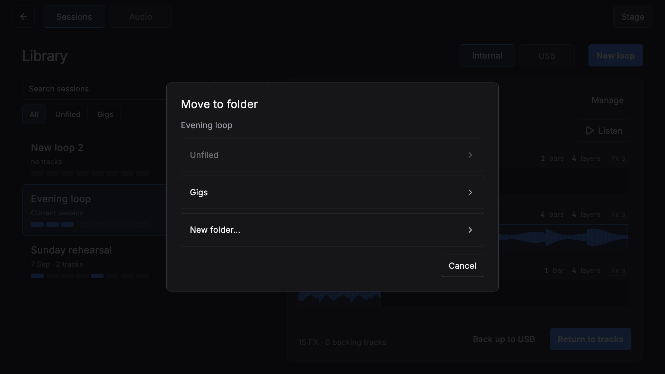
test/screenshots/goldens/library_move.png
