tomassasovsky/segno/test/screenshots/goldens/library_new_loop.png

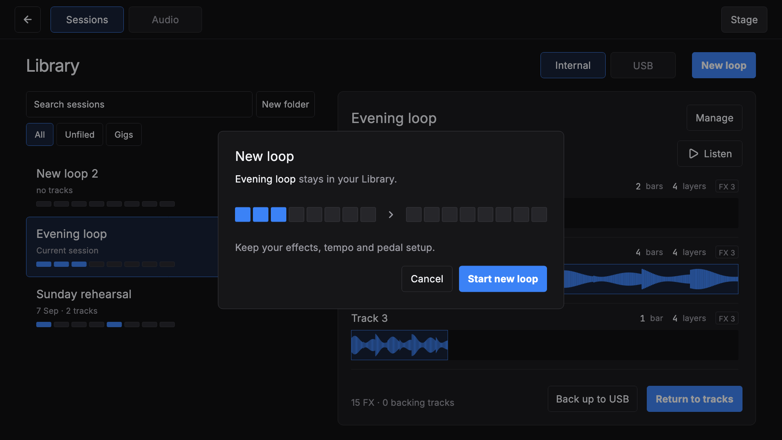
test/screenshots/goldens/library_new_loop.png
