tomassasovsky/segno/test/screenshots/goldens/library_rename.png

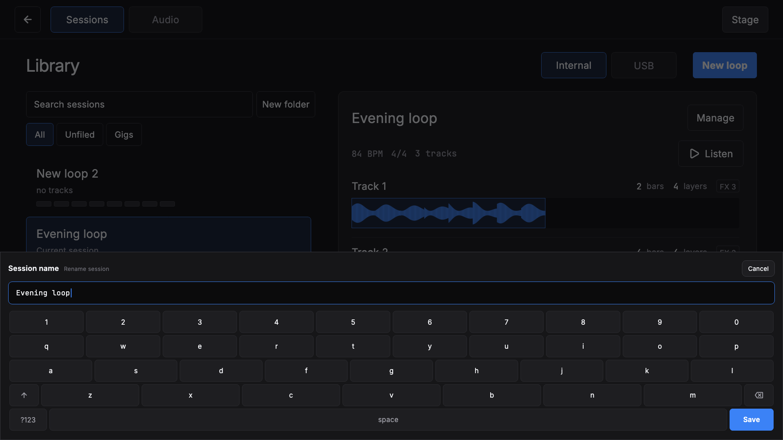
test/screenshots/goldens/library_rename.png
