tomassasovsky/segno/test/screenshots/goldens/library_save_failed.png

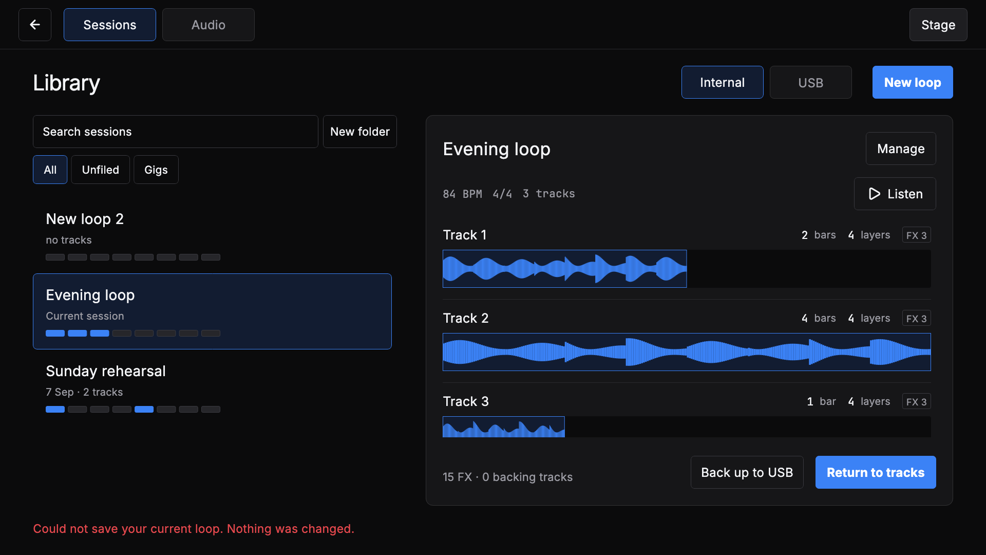
test/screenshots/goldens/library_save_failed.png
