tomassasovsky/segno/test/screenshots/goldens/library_usb_disconnected.png

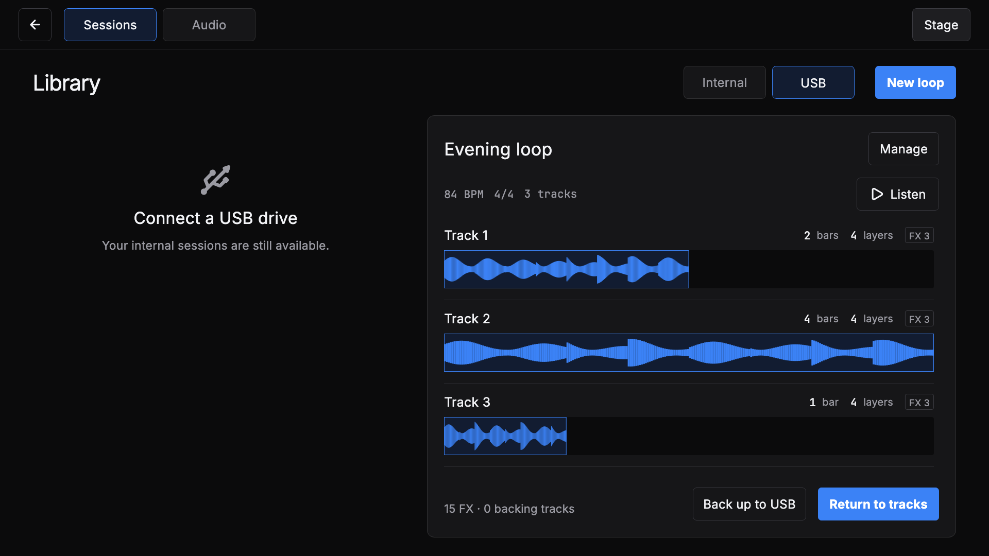
test/screenshots/goldens/library_usb_disconnected.png
