tomassasovsky/segno/test/screenshots/goldens/loop_settings_audio_tempo.png

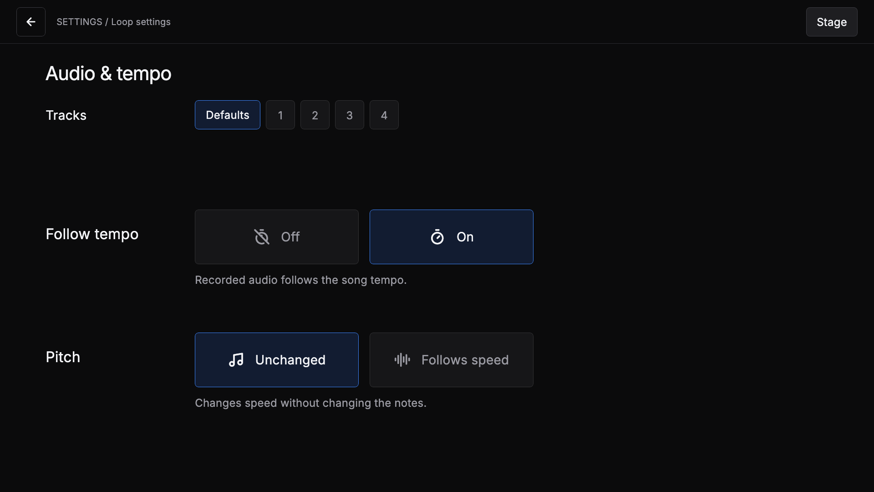
test/screenshots/goldens/loop_settings_audio_tempo.png
