tomassasovsky/segno/test/screenshots/goldens/loop_settings_audio_tempo_pitch_follows.png

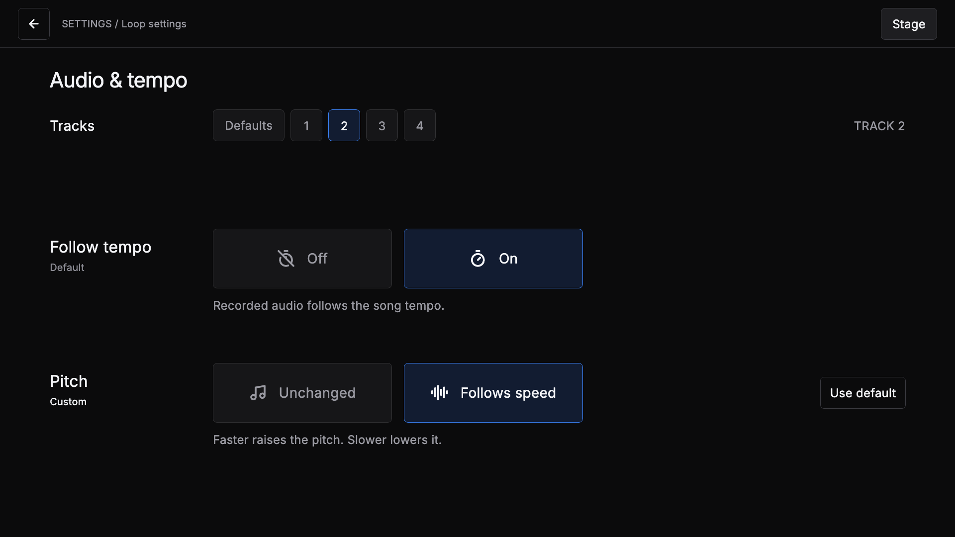
test/screenshots/goldens/loop_settings_audio_tempo_pitch_follows.png
