tomassasovsky/segno/test/screenshots/goldens/loop_settings_audio_tempo_recorded_speed.png

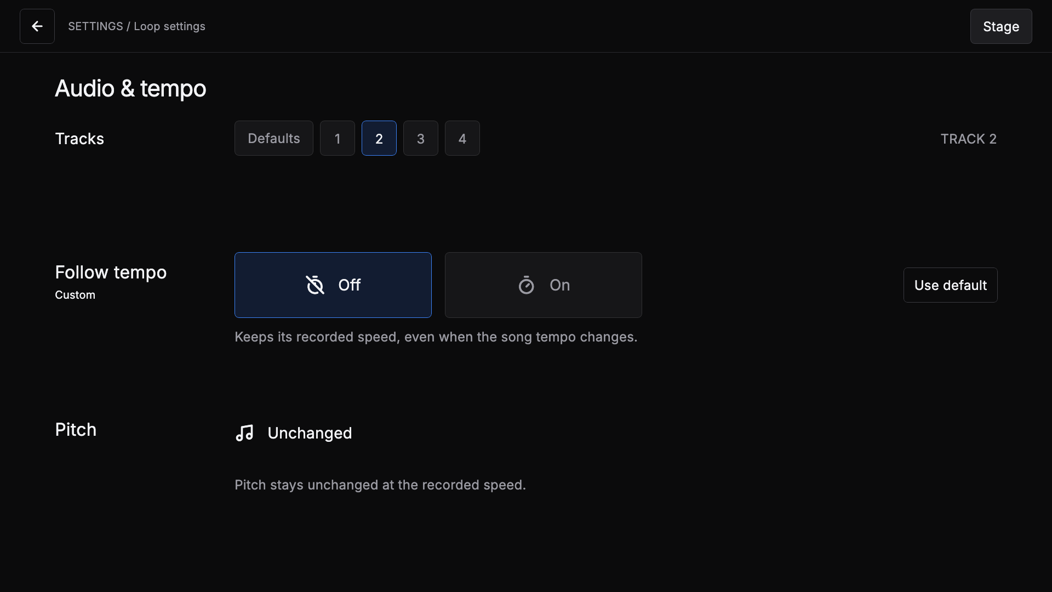
test/screenshots/goldens/loop_settings_audio_tempo_recorded_speed.png
