tomassasovsky/segno/test/screenshots/goldens/loop_settings_hub.png

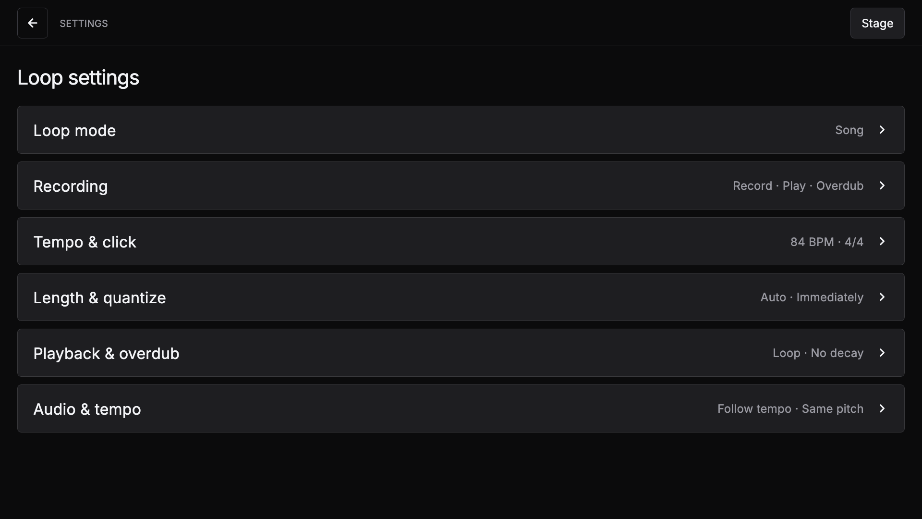
test/screenshots/goldens/loop_settings_hub.png
