tomassasovsky/segno/test/screenshots/goldens/loop_settings_length_custom.png

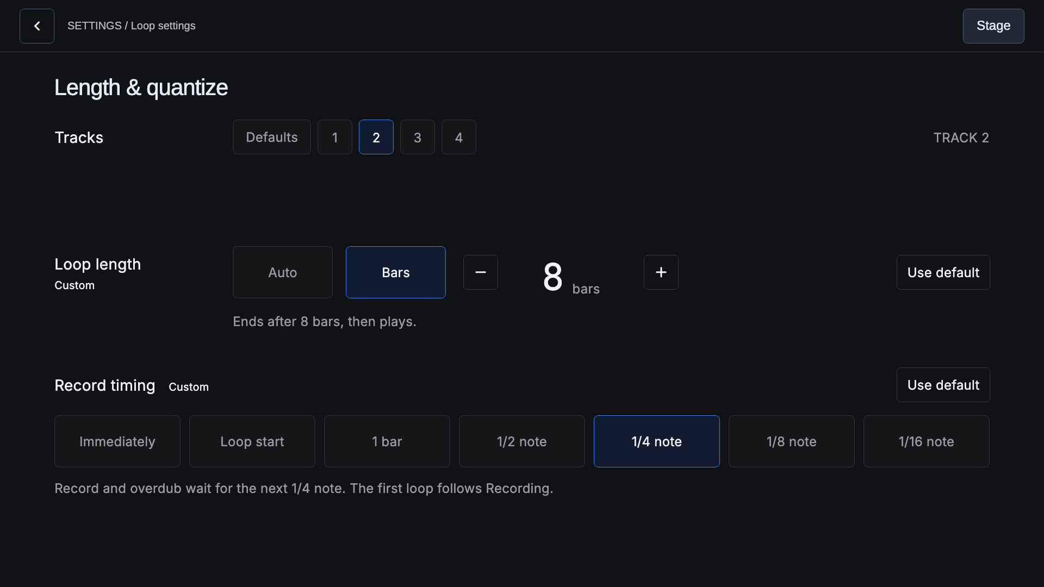
test/screenshots/goldens/loop_settings_length_custom.png
