tomassasovsky/segno/test/screenshots/goldens/loop_settings_length_defaults.png

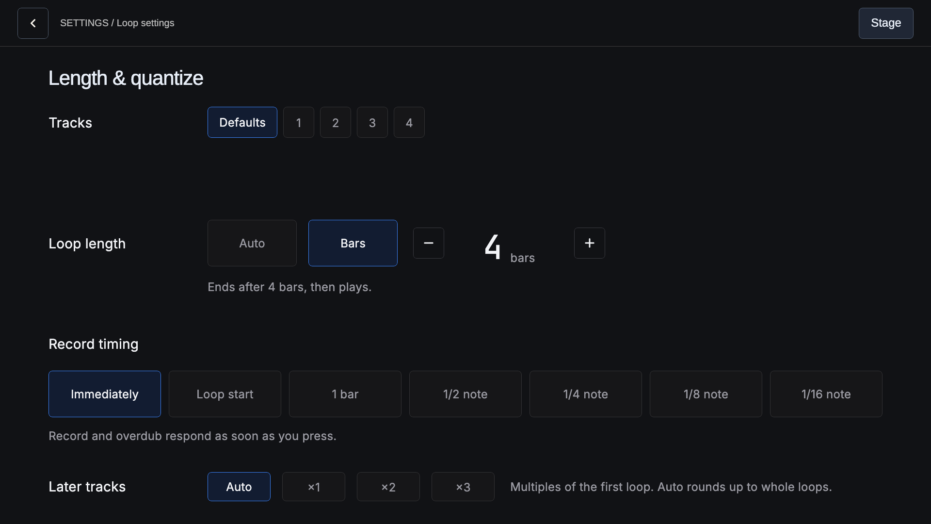
test/screenshots/goldens/loop_settings_length_defaults.png
