tomassasovsky/segno/test/screenshots/goldens/loop_settings_mode.png

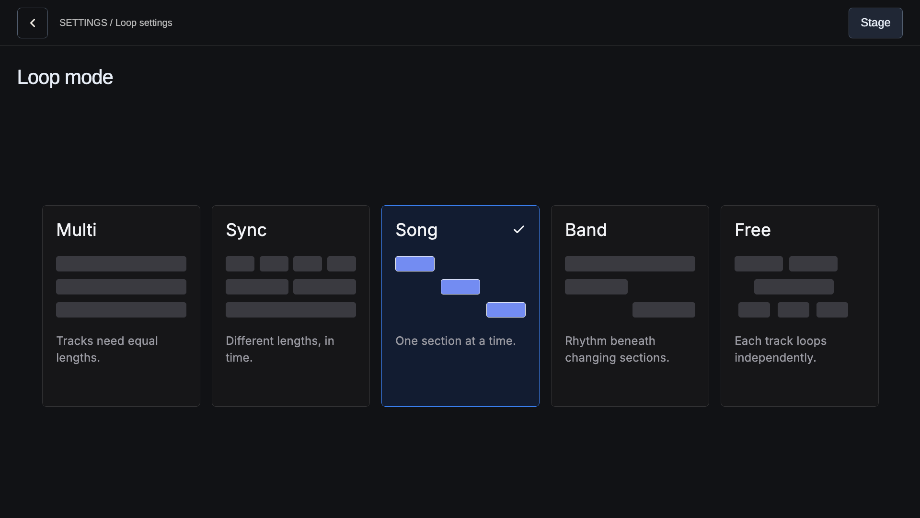
test/screenshots/goldens/loop_settings_mode.png
