tomassasovsky/segno/test/screenshots/goldens/loop_settings_mode_confirm.png

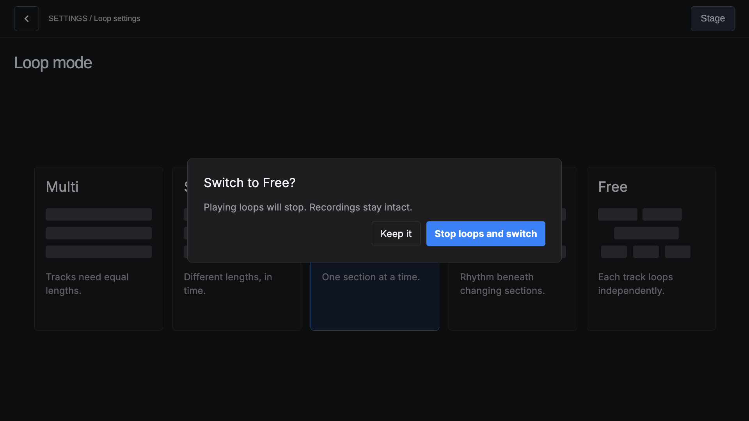
test/screenshots/goldens/loop_settings_mode_confirm.png
