tomassasovsky/segno/test/screenshots/goldens/loop_settings_playback_custom.png

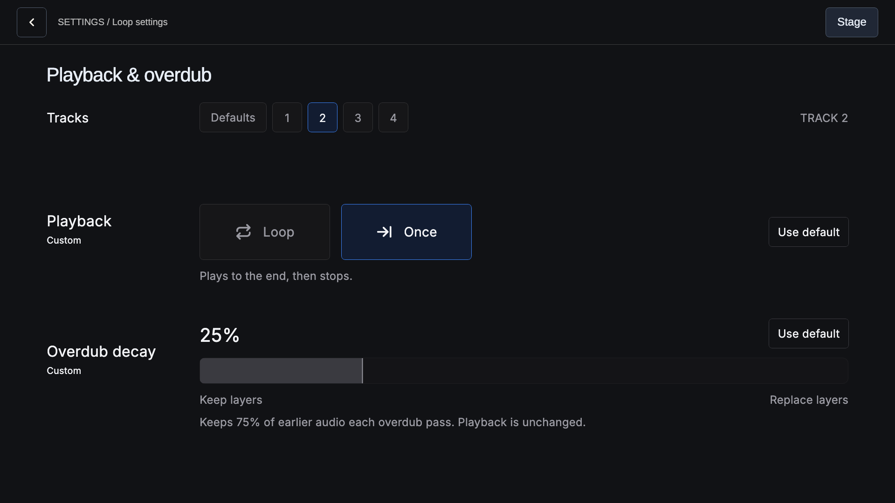
test/screenshots/goldens/loop_settings_playback_custom.png
