tomassasovsky/segno/test/screenshots/goldens/loop_settings_recording_locked.png

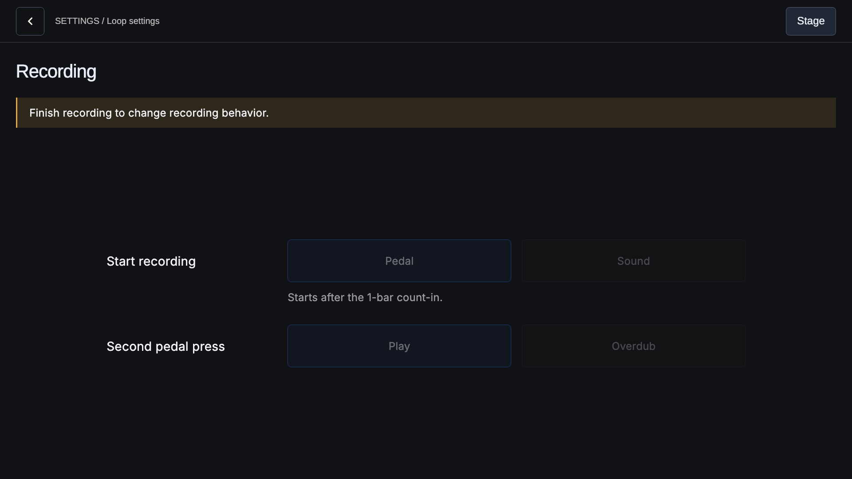
test/screenshots/goldens/loop_settings_recording_locked.png
