tomassasovsky/segno/test/screenshots/goldens/loop_settings_signature.png

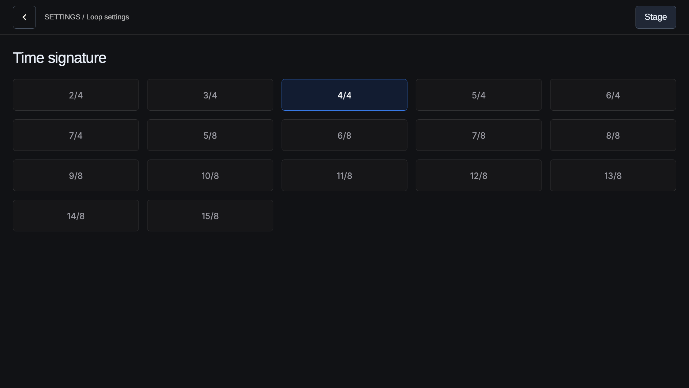
test/screenshots/goldens/loop_settings_signature.png
