tomassasovsky/segno/test/screenshots/goldens/loop_settings_tempo.png

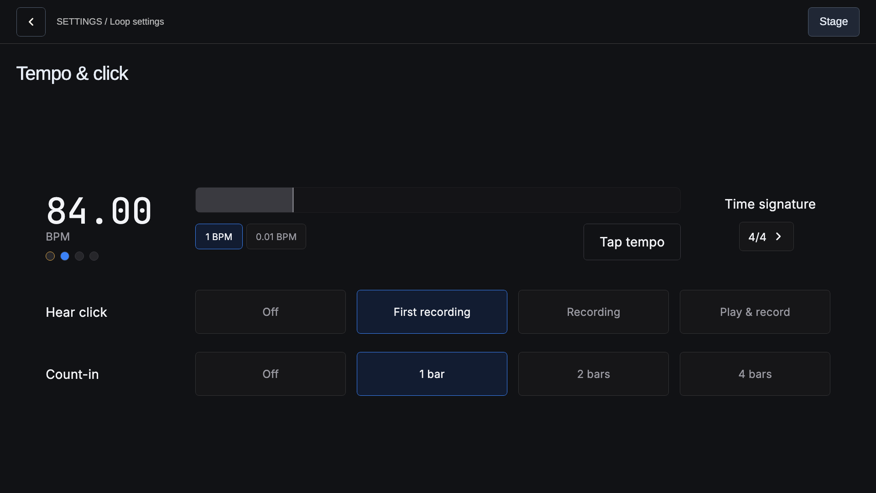
test/screenshots/goldens/loop_settings_tempo.png
