tomassasovsky/segno/test/screenshots/goldens/midi_controls_click_destination.png

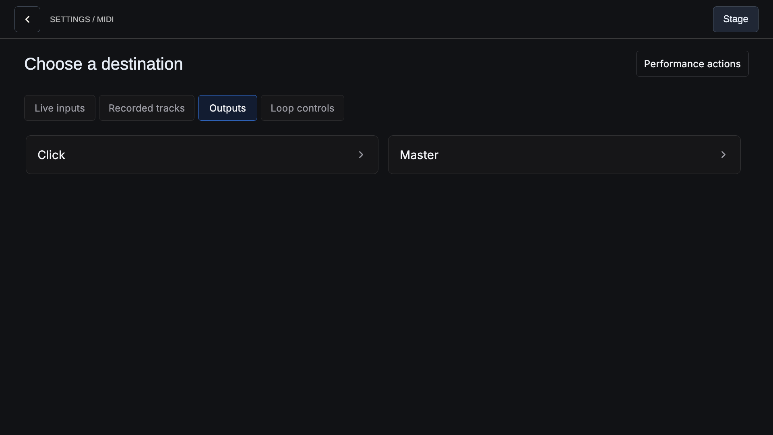
test/screenshots/goldens/midi_controls_click_destination.png
