tomassasovsky/segno/test/screenshots/goldens/midi_controls_click_range.png

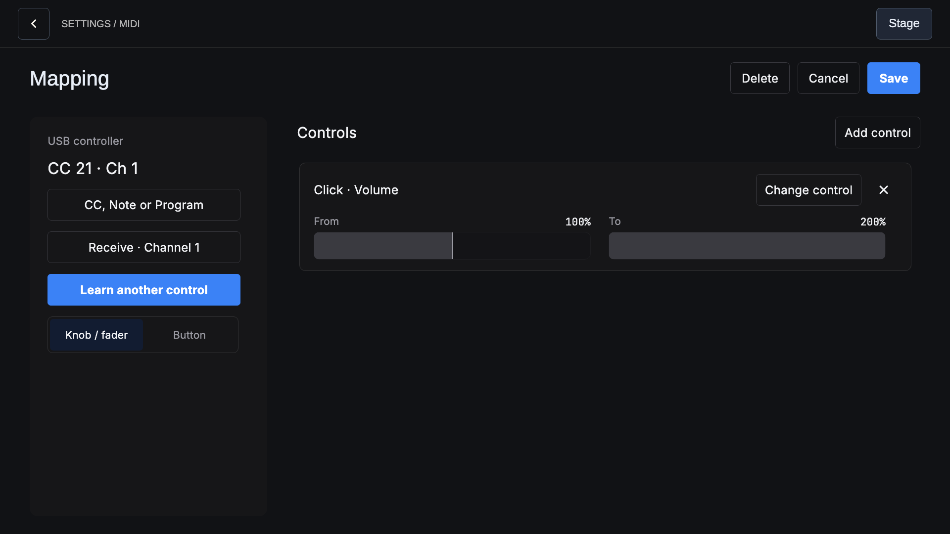
test/screenshots/goldens/midi_controls_click_range.png
