tomassasovsky/segno/test/screenshots/goldens/midi_controls_connected.png

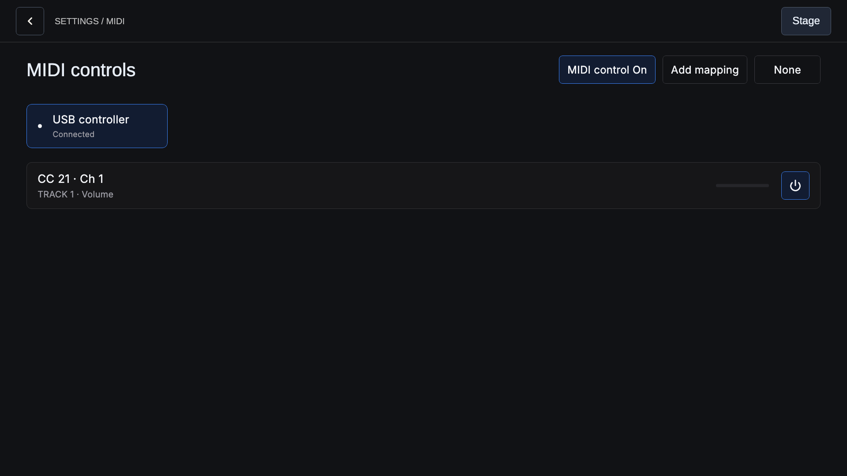
test/screenshots/goldens/midi_controls_connected.png
