tomassasovsky/segno/test/screenshots/goldens/midi_controls_count_in_range.png

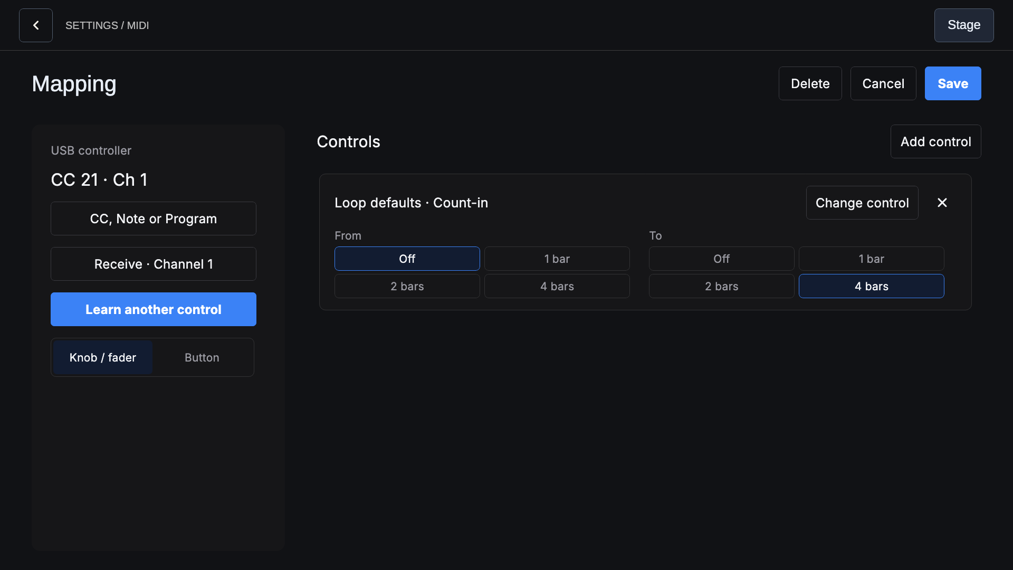
test/screenshots/goldens/midi_controls_count_in_range.png
