tomassasovsky/segno/test/screenshots/goldens/midi_controls_decay_destination.png

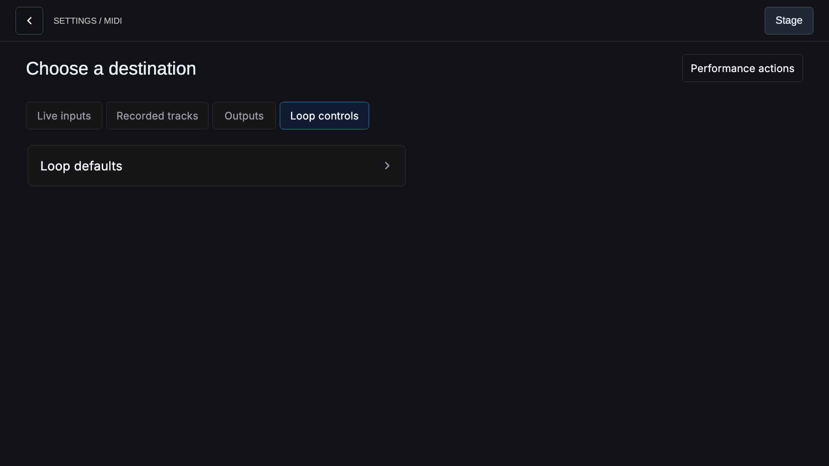
test/screenshots/goldens/midi_controls_decay_destination.png
