tomassasovsky/segno/test/screenshots/goldens/midi_controls_decay_ranges.png

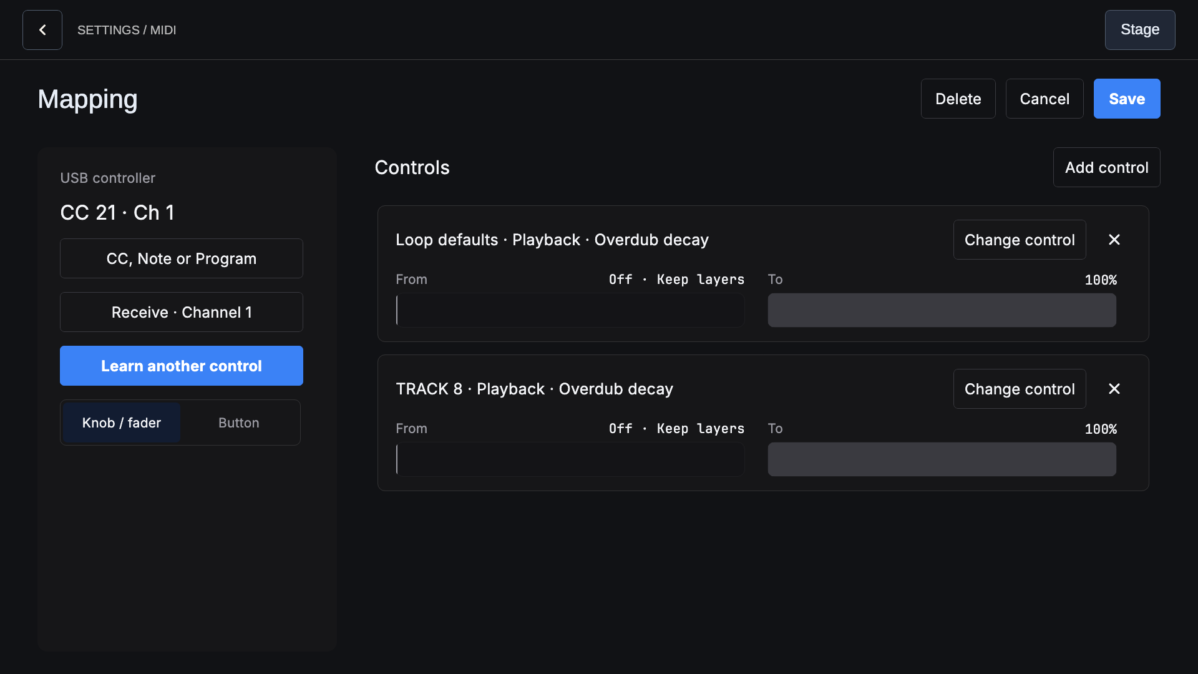
test/screenshots/goldens/midi_controls_decay_ranges.png
