tomassasovsky/segno/test/screenshots/goldens/midi_controls_formats.png

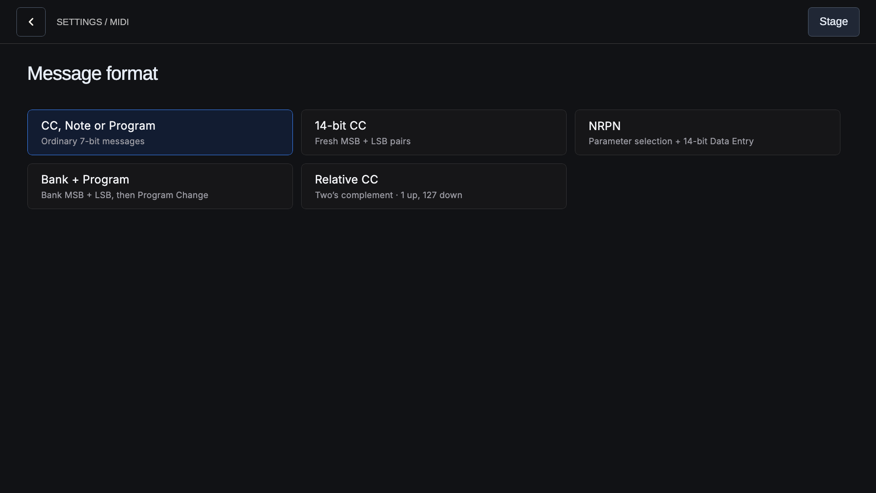
test/screenshots/goldens/midi_controls_formats.png
