tomassasovsky/segno/test/screenshots/goldens/midi_controls_listening.png

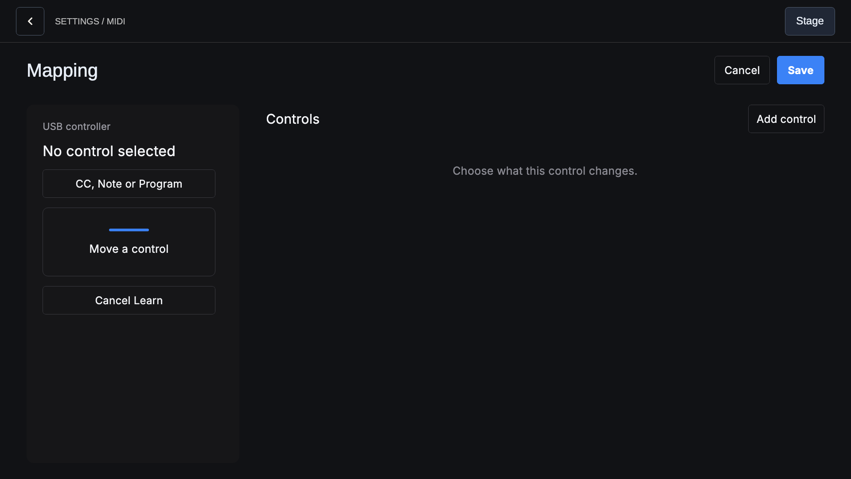
test/screenshots/goldens/midi_controls_listening.png
