tomassasovsky/segno/test/screenshots/goldens/midi_controls_mixer_gains.png

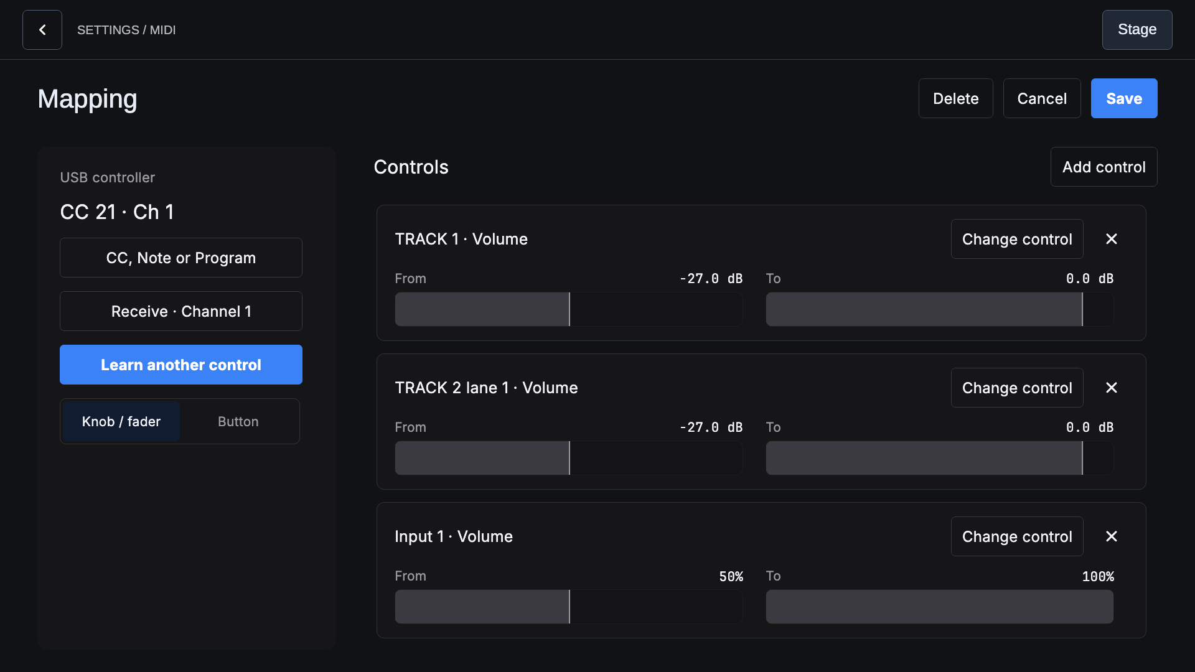
test/screenshots/goldens/midi_controls_mixer_gains.png
