tomassasovsky/segno/test/screenshots/goldens/midi_controls_momentary.png

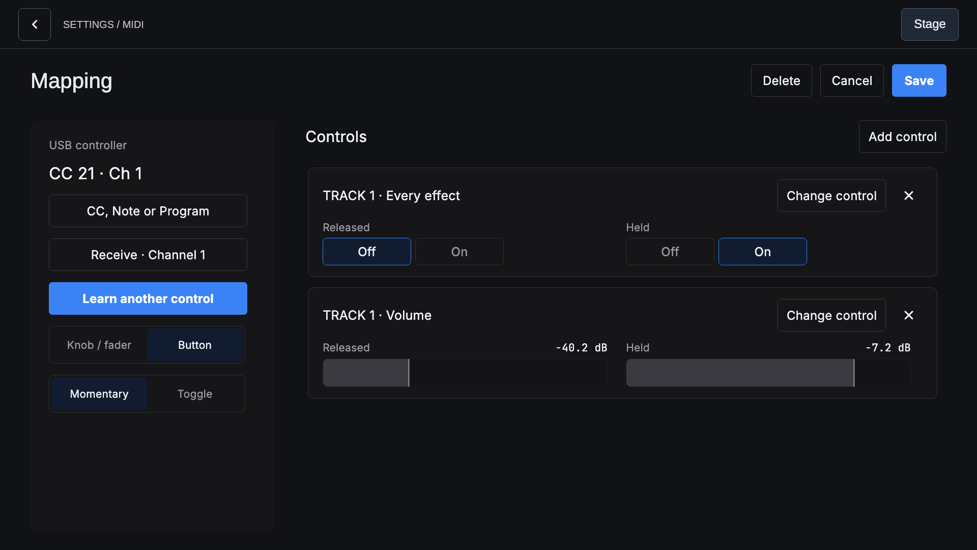
test/screenshots/goldens/midi_controls_momentary.png
