tomassasovsky/segno/test/screenshots/goldens/midi_controls_paused.png

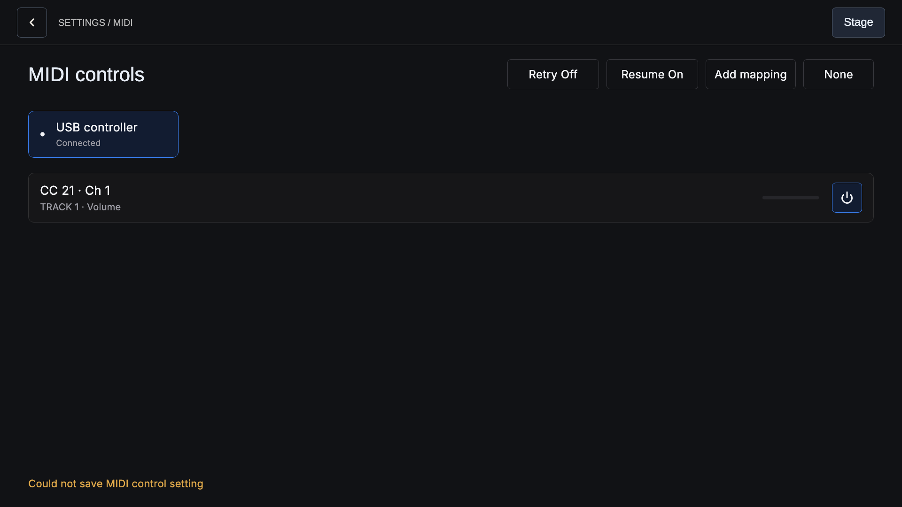
test/screenshots/goldens/midi_controls_paused.png
