tomassasovsky/segno/test/screenshots/goldens/midi_controls_unavailable.png

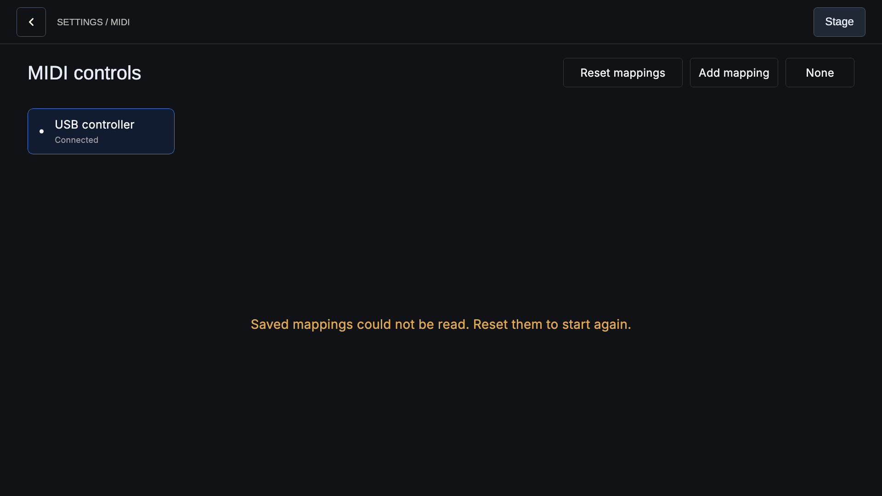
test/screenshots/goldens/midi_controls_unavailable.png
