tomassasovsky/segno/test/screenshots/goldens/save_to_choose.png

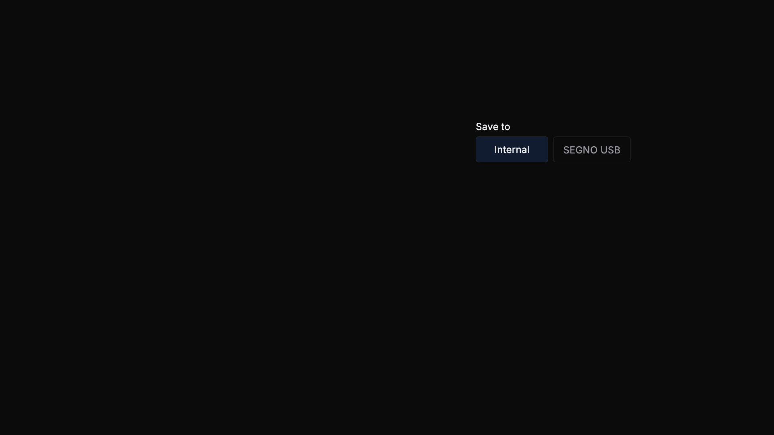
test/screenshots/goldens/save_to_choose.png
