tomassasovsky/segno/test/screenshots/goldens/settings_about.png

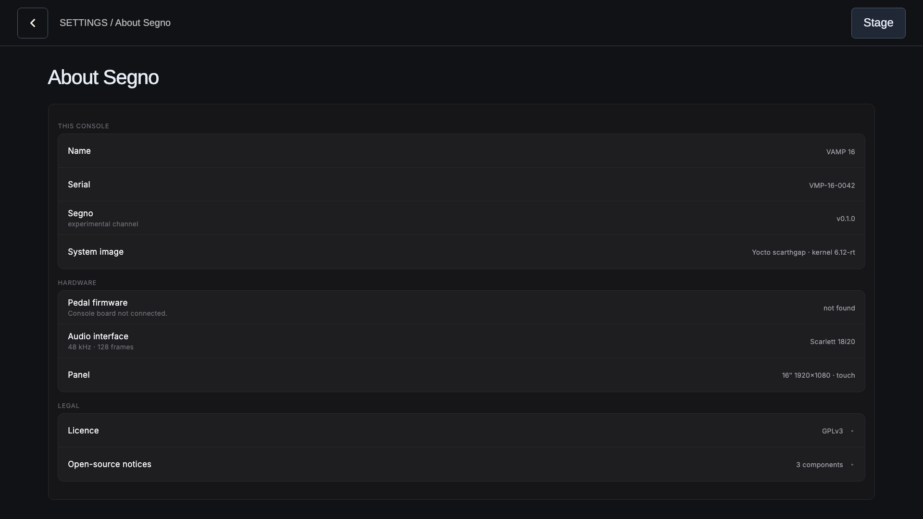
test/screenshots/goldens/settings_about.png
