tomassasovsky/segno/test/screenshots/goldens/settings_about_licences.png

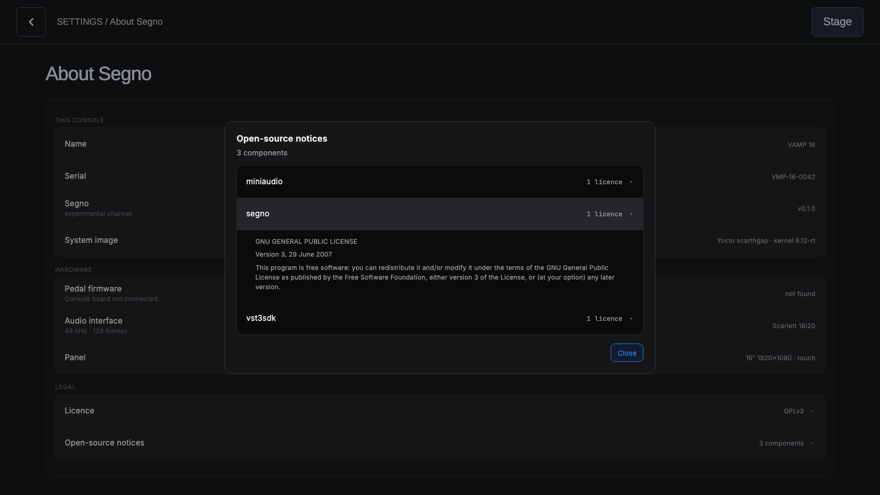
test/screenshots/goldens/settings_about_licences.png
