tomassasovsky/segno/test/screenshots/goldens/settings_device.png

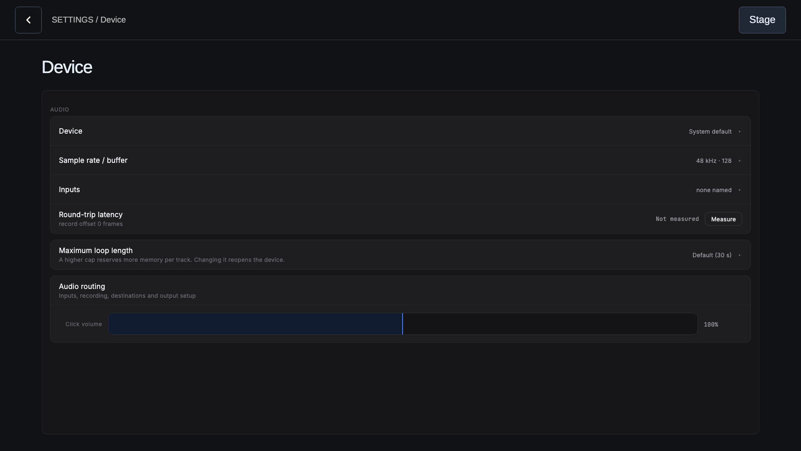
test/screenshots/goldens/settings_device.png
