tomassasovsky/segno/test/screenshots/goldens/settings_device_max_loop.png

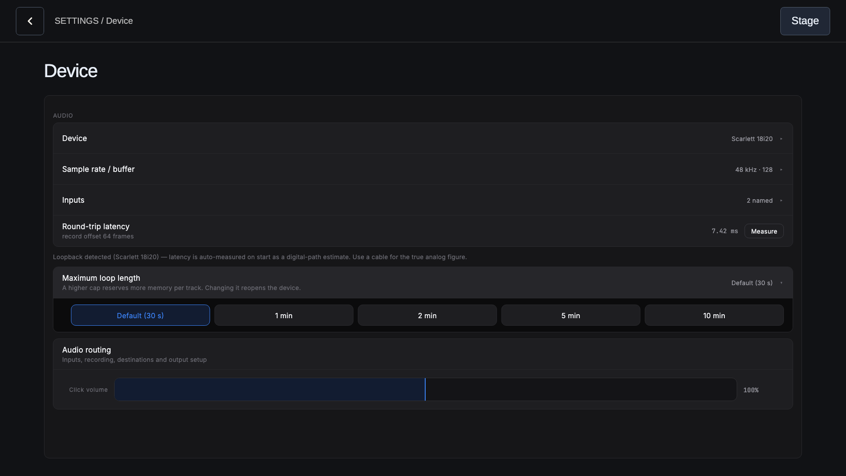
test/screenshots/goldens/settings_device_max_loop.png
