tomassasovsky/segno/test/screenshots/goldens/settings_device_rate.png

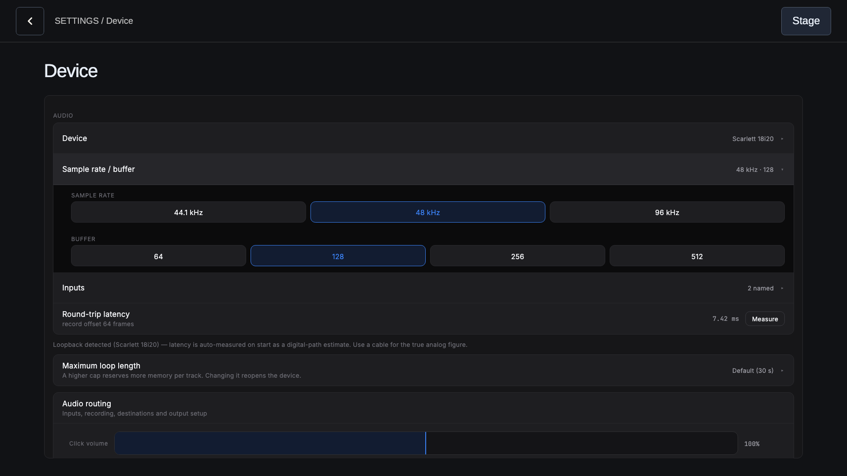
test/screenshots/goldens/settings_device_rate.png
