tomassasovsky/segno/test/screenshots/goldens/settings_device_refused.png

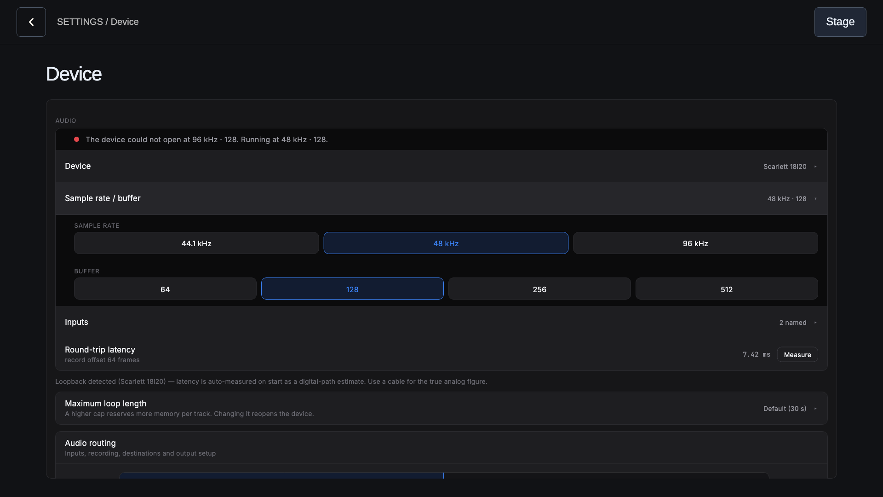
test/screenshots/goldens/settings_device_refused.png
