tomassasovsky/segno/test/screenshots/goldens/settings_displays.png

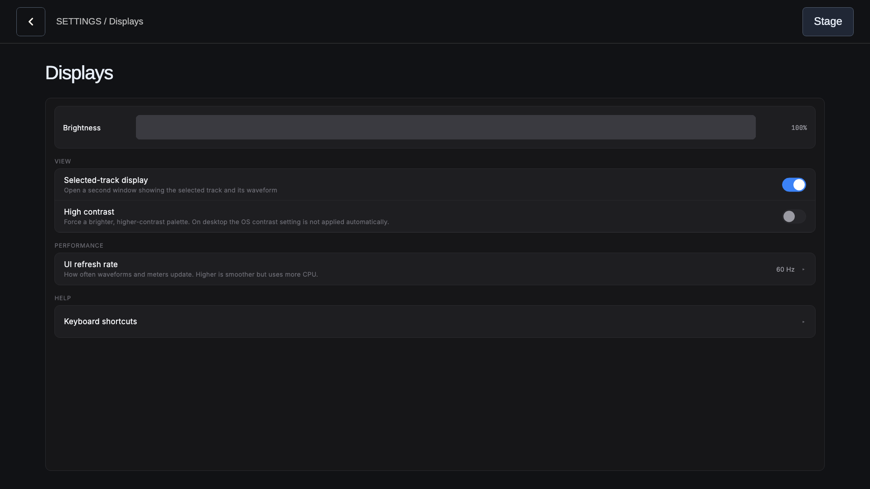
test/screenshots/goldens/settings_displays.png
