tomassasovsky/segno/test/screenshots/goldens/settings_home.png

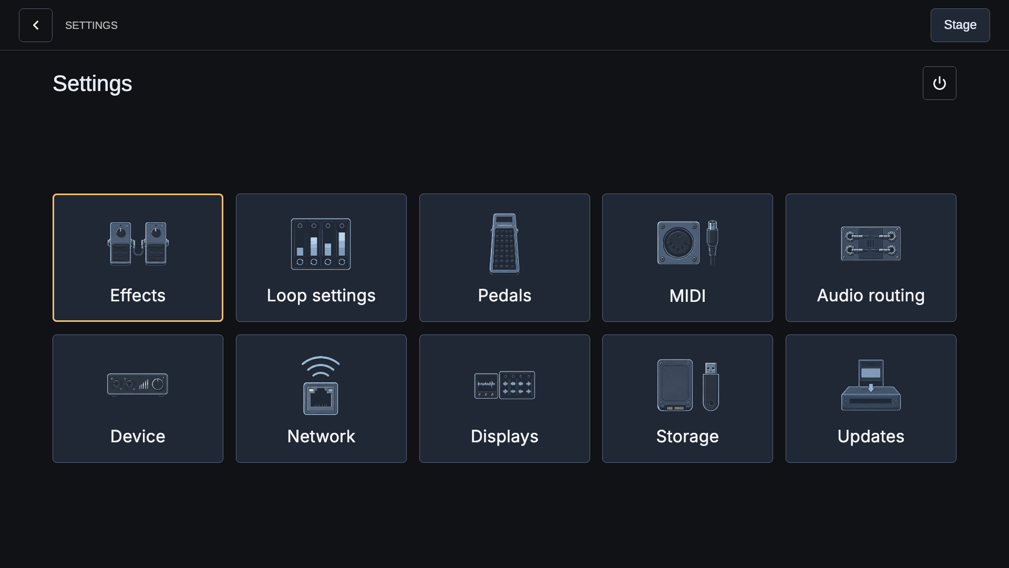
test/screenshots/goldens/settings_home.png
