tomassasovsky/segno/test/screenshots/goldens/settings_network_wifi_forget.png

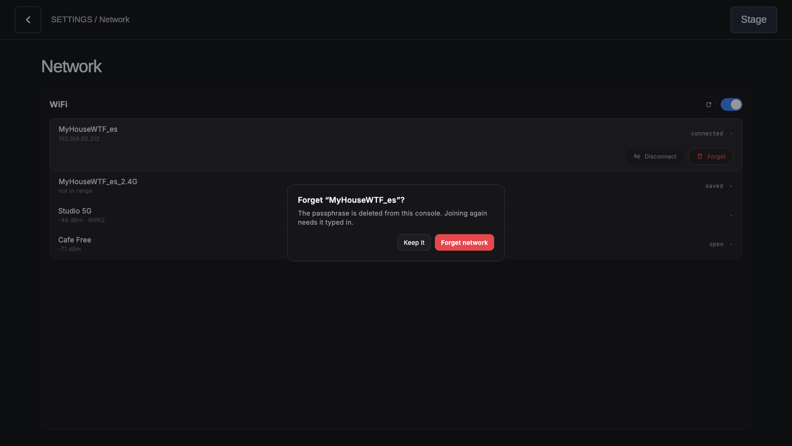
test/screenshots/goldens/settings_network_wifi_forget.png
