tomassasovsky/segno/test/screenshots/goldens/settings_network_wifi_join.png

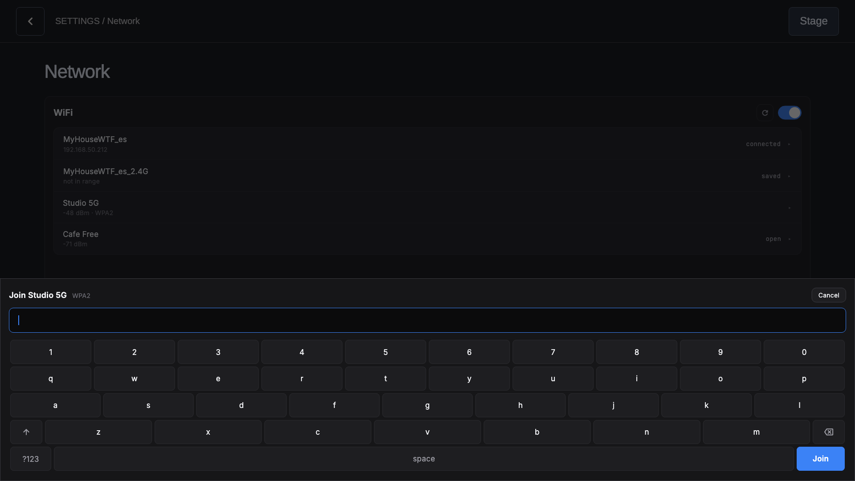
test/screenshots/goldens/settings_network_wifi_join.png
