tomassasovsky/segno/test/screenshots/goldens/storage_low_internal.png

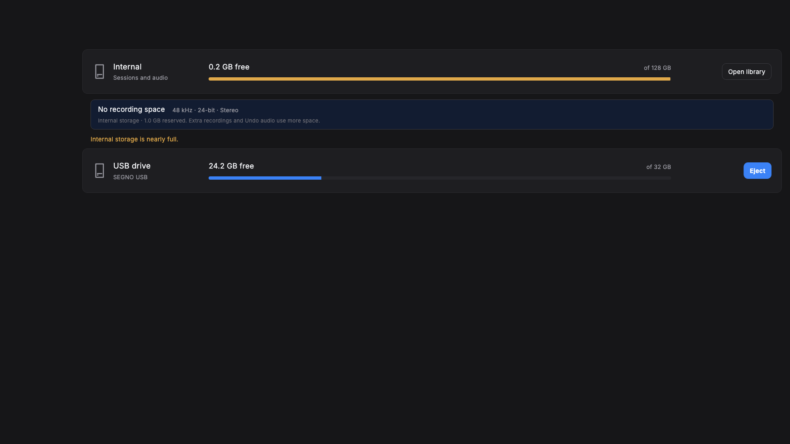
test/screenshots/goldens/storage_low_internal.png
