tomassasovsky/segno/test/screenshots/goldens/storage_no_usb.png

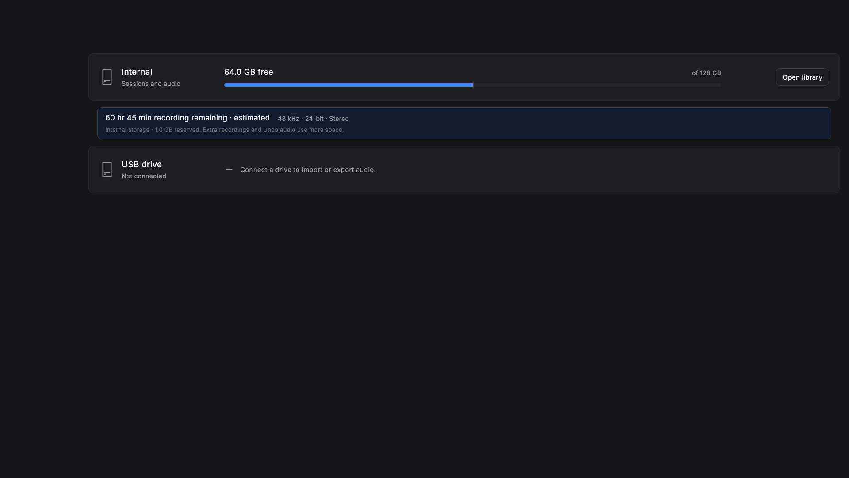
test/screenshots/goldens/storage_no_usb.png
