tomassasovsky/segno/test/screenshots/goldens/tracks_device_lost.png

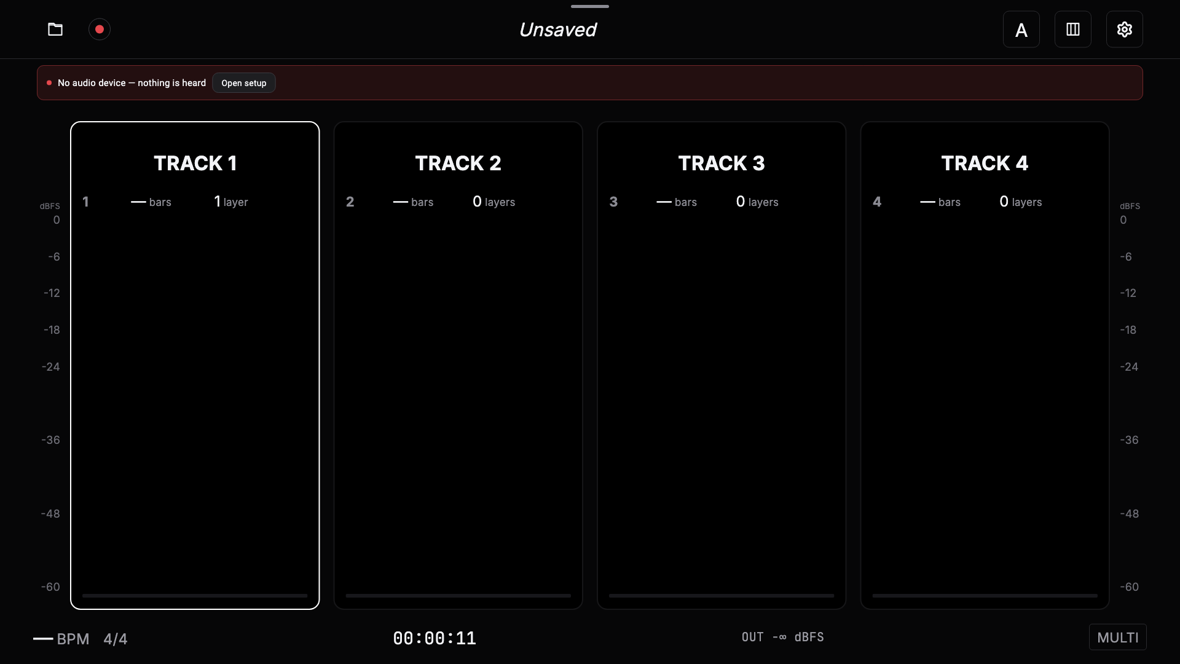
test/screenshots/goldens/tracks_device_lost.png
