tomassasovsky/segno/test/screenshots/goldens/tracks_mixer_compact_window.png

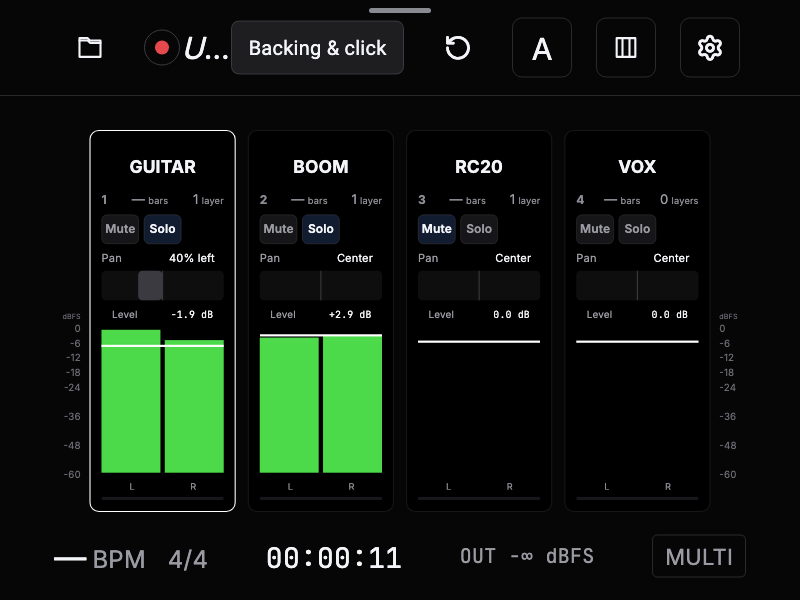
test/screenshots/goldens/tracks_mixer_compact_window.png
