tomassasovsky/segno/test/screenshots/goldens/tracks_mixer_window.png

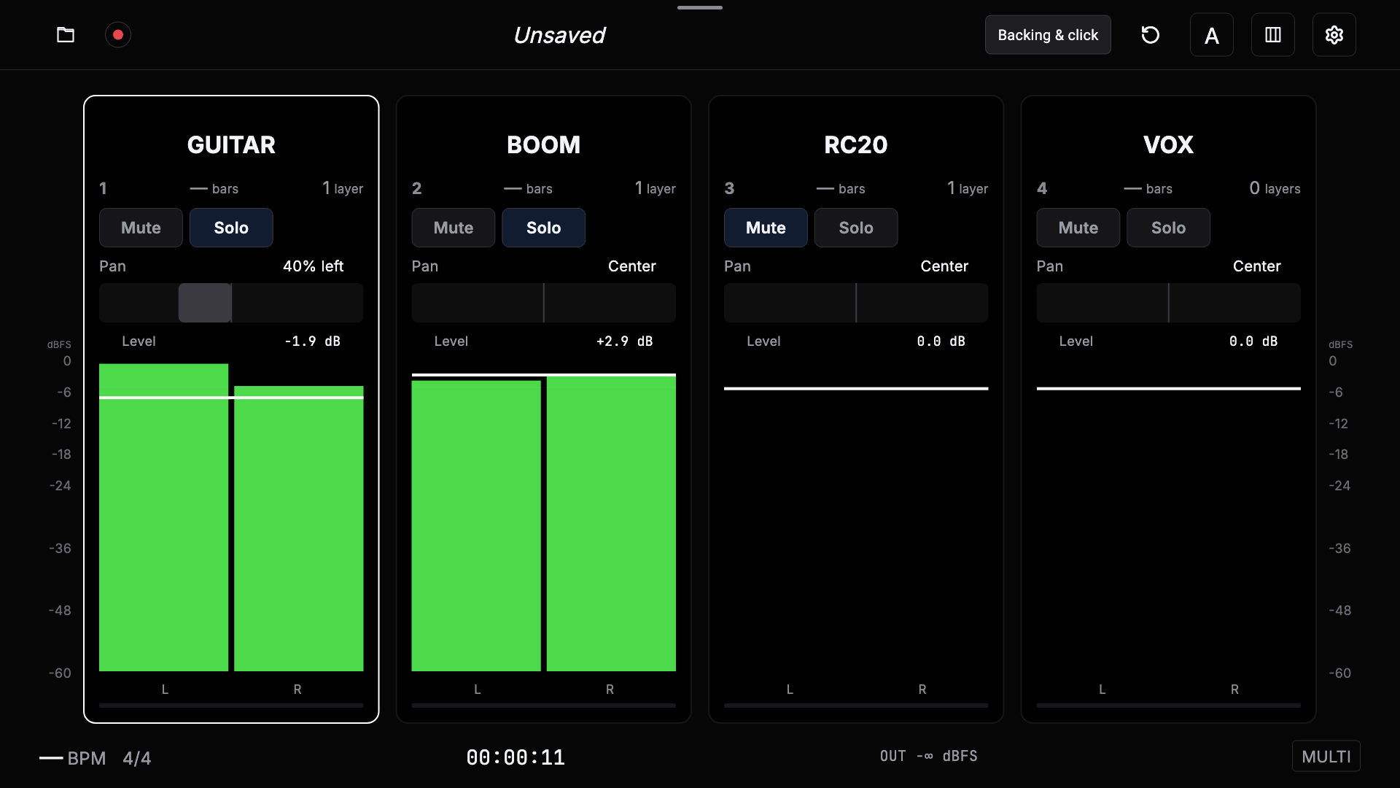
test/screenshots/goldens/tracks_mixer_window.png
