tomassasovsky/segno/docs/reviews/shared-mixer-controls/raw/runtime-repair-delta.md

# M310-7 independent runtime delta review

Read-only, 2026-10-01. Reviewed frozen base `06633b2b537efba4c59108e38764e58c0b2c542e` plus `control_midi.dart` SHA-256 `02eec3e8ed5e13c02aeb1bf4f564786524fdaa0b7403c622cbca0d05d2c4abfa` and `external_dispatch_test.dart` `a6c8ca12c64cddb20205a659a1d3ad9feee0fe615b17de6cb486bef188a642a0`. I authored neither of these two frozen files in M310-7 and made no edits or test runs in this review.

**Result: no actionable finding in the bounded M310-7 repair.** `control_midi.dart:715–727` now distinguishes three cases before calling the existing confirmed Mixer owner: a new held `MidiParameterWrite` supplies its own low; actual ending/cleanup asks for the newest surviving Released value; a new non-held write supplies no low. `MixSettingsCoordinator.setControllerValues` removes the old target's released projection in its candidate and publishes the replacement only after `_commit` succeeds (`mix_settings_coordinator.dart:208–256`). Thus a confirmed continuous/toggle value becomes both live and durable, rather than inheriting an older External held low. The MIDI proposal's accepted indices and holder tickets are recorded only after the coordinator result is OK (`control_midi.dart:729–756`), preserving refusal behavior. A failed store transaction keeps the older projection and does not advance the MIDI row. The existing `ending` branch still passes a surviving low, so momentary cleanup does not become a new durable high.

The added real-pump regression covers a held External `.75`/Released `.4`, accepted MIDI continuous and toggle physical gain `1.5`, MIDI disable/retirement, External release, fresh External press/release, and a one-shot storage refusal (`external_dispatch_test.dart:839–945`). This directly checks the original mismatch on `durableSnapshot`, not merely command calls. The author evidence reports two red failures before repair, three green cases afterward, 13 neighboring passes, analyzer clean, and Bloc positively scanning both files. I inspected those logs and hashes, but did not execute tests. The first red/green attempts are retained and explained in `m310-7-repair.md`; the bound v2 runs are the meaningful evidence.

Review limit: this is a two-file repair review, not a renewed independent certification of the entire M3.10 branch or author-only image baselines. Other source-holder behavior remains covered by the already frozen M3.10 source/adversary reviews and final integration gates.
