tomassasovsky/segno/hardware/enclosure/out/segno_pedal_tiles.pdf

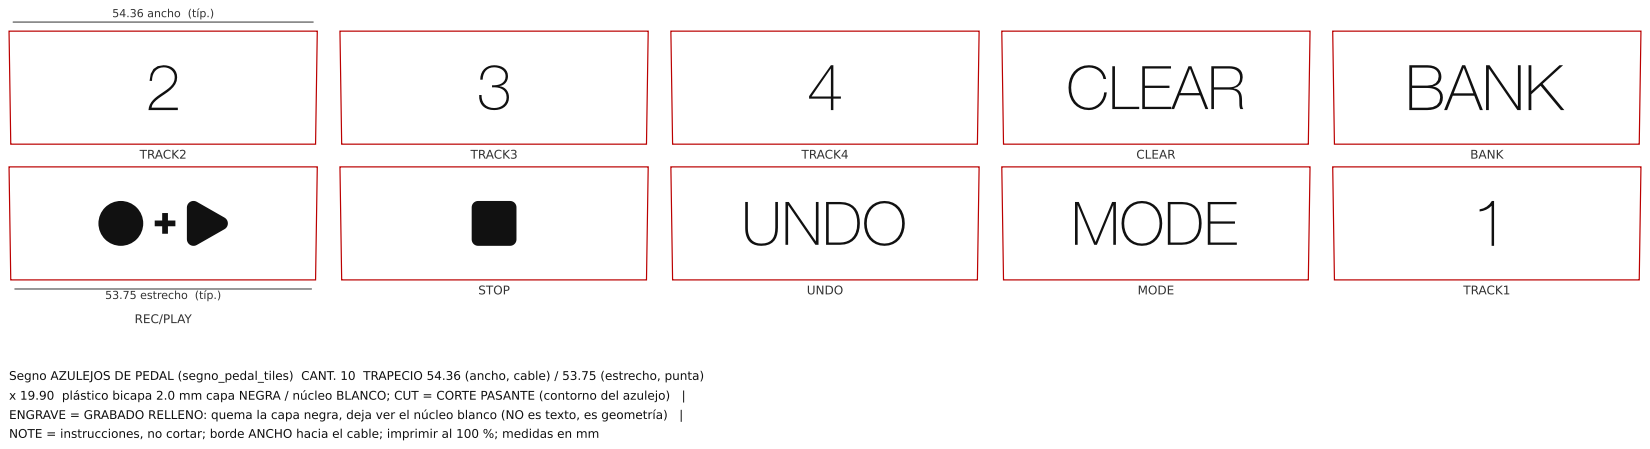
[picture p225: page 1]
REC/PLAY; STOP; UNDO; MODE; TRACK1; TRACK2; TRACK3; TRACK4; CLEAR; BANK; 54.36 ancho (típ.); 53.75 estrecho (típ.)

Segno AZULEJOS DE PEDAL (segno_pedal_tiles) CANT. 10 TRAPECIO 54.36 (ancho, cable) / 53.75 (estrecho, punta)
x 19.90 plástico bicapa 2.0 mm capa NEGRA / núcleo BLANCO; CUT = CORTE PASANTE (contorno del azulejo)
ENGRAVE = GRABADO RELLENO: quema la capa negra, deja ver el núcleo blanco (NO es texto, es geometría)
NOTE = instrucciones, no cortar; borde ANCHO hacia el cable; imprimir al 100 %; medidas en mm
