tomassasovsky/segno/hardware/enclosure/segno_enclosure.py

"""Segno — parametric sheet-metal enclosure for the segno Pi loopstation.

Generates a **manufacturing package** for a wedge-shaped floor console modelled on
the "Chewie II" / Sonnit reference (850 x 465 x 100 mm, top sloping toward the
player), housing this repo's standalone build: a Raspberry Pi 4/5 running segno,
the console board v2 (#747), ten foot pedals, the EC11 encoder + diffused LED ring,
SMD LED-strip status indicators (WS2812B segments behind diffuser slots) and a
7" + 16" touchscreen pair. Branded **Segno**.

Construction (see ../segno_enclosure_design.md and
../../docs/plan/2026-06-27-feat-segno-enclosure-rework-plan.md):

  FOLDED LOWER BODY (one rigid tray)        REMOVABLE TOP LID
  - front wall (12) + top flange (ledge)    - faceplate pan (sloped top, all cutouts)
  - rear wall (100) + I/O + vents + flange    + down-turned front/side/rear skirts
  - 2x side panel + top flange (ledge)        (lid screws on the SKIRTS, not the top)
  - bottom plate (folded, vented, Pi/board)   (screens are BONDED, no brackets)
  - 10x inner pedal platform (3D printed)

Foot controls = ten Cherub WTB-006 footswitches (109.87x76.35, 29.3 mm tall with
anti-slip pads; caliper-measured, see hardware/cherub_wtb006_pedal/) standing
toe-forward on printed pedestals, protruding through ~79x113 mm slots. No
top-face fasteners; pedal wiring stays internal. Service = back out the side +
front-lip screws and lift the lid (screens + ring PCB + LEDs go with it; pedals
stay on their platforms).

Geometry is validated by an **assertion suite** (`_check()`) run before any output,
so "the generator runs" means the geometry is valid (width budget, no overlapping
cutouts, platform head-room, screen depth, vent free-area, bezel overlap).

The DOCUMENTS are validated separately by `_verify_drawing_package()`, which runs
on the finished files at the end of a build: through-cut layers actually render,
every drawn fold is in a bend table, no sheet inherits a default material or
quantity, coating masks never sit on a cutting layer, and the sheet-metal zip
carries sheet metal only. That path used to have no checks at all, which is where
the whole RED list of the #775 DFM sweep came from.

Outputs (./out, mm): STEP (assembly + per-part), DXF flat patterns
(CUT + VENT = through-cut, BEND = fold reference, MASK = no-paint, NOTE/ENGRAVE/
SILK = lettering), PDF drawing sheets with a bend table and title block, and
the 2-ply pedal-tile pack (CUT outline + ENGRAVE fills, #946).

Run with the bundled venv (cadquery + ezdxf + matplotlib):
    .venv/bin/python segno_enclosure.py            # check + STEP + DXF + PDF
    .venv/bin/python segno_enclosure.py --report   # report + checks only
    .venv/bin/python segno_enclosure.py --no-step   # DXF + PDF only
    .venv/bin/python segno_enclosure.py --tiles-only  # 2-ply tile pack only
"""
from __future__ import annotations

import math
import os
import sys
import time

# When this run began. The packager holds every shipped file against it so a
# hand-made leftover cannot ride along in a vendor zip -- see pack().
_RUN_STARTED = time.time()

HERE = os.path.dirname(os.path.abspath(__file__))
OUT = os.path.join(HERE, "out")

# ===========================================================================
# PARAMETERS — edit here; everything downstream is derived
# ===========================================================================

W        = 850.0     # overall width
FACE_RUN = 397.0     # depth of the TOP PLATE control area (front edge -> the peak),
                     # sized so the screen block sits FRONT_GAP behind the front row
                     # with an EDGE rear margin
H_REAR   = 100.0     # peak height (rear edge of the Top plate = tallest point)
H_FRONT  = 12.0      # front lip height (low end) -- nearly at the floor. The lid front lip
                     # screws horizontally into this wall. DFM CAVEAT: at 12mm the flat wall
                     # is only ~9mm, so the M4 lands ~2.5mm from the fold -- laser the hole and
                     # tap/finish AFTER bending. A fully-clear front screw needs a taller front
                     # (~17mm); an inward screw-ledge is blocked by the front-pedal row (~8mm).

# Rear of the body steps down via an ANGLED TRANSITION SURFACE (a beveled shoulder)
# instead of the Top plate folding straight to the Rear panel. The transition is a
# flange folded forward+up from the (shortened) Rear panel's top, steeper than the
# Top plate; the Top plate's rear edge laps onto it and screws down -- so it is a
# NATURAL SUPPORT for the Top plate.
TRANS_RUN  = 22.0    # transition horizontal run (depth added behind the control area) --
                     # short, so the transition shoulder is only as deep as the lid's
                     # rear lap covers (keeps the ~25deg rake, pulls the rear panel
                     # forward, reduces the bottom-plate depth)
TRANS_DROP = 10.0    # transition vertical drop (peak -> rear-panel top)

T        = 2.0       # sheet thickness (2.0 mm 1050 aluminium -- the shop's stock, owner 2026-09-04)
RI       = 2.0       # inside bend radius (= T; 1050 is softer than 5052 and takes it easily)
KF       = 0.33      # K-factor for bend-allowance development
FLANGE   = 18.0      # return-flange depth (lid side wings + wall top flange)
# Weld-free corner join: internal L-brackets riveted through both walls. These MUST match
# between the base rivet holes, the bracket parts, and the viewer render.
CORNER_RO = 8.0      # rivet offset from the BRACKET's bend centre line, in its flat (hug the
                     # corner, clear the I/O panel). The base drills CORNER_RO + T from its
                     # bend lines -- see dxf_base for the fold-development derivation.
CORNER_LEG = 12.0    # bracket leg width (along the wall)
# REAR-corner rivets are STAGGERED between the two legs so a wall-leg rivet and a side-leg
# rivet never sit at the same height (their tips would meet at the corner). Heights are from
# the bottom-plate top.
CORNER_ZR_WALL = (8.0, 40.0, 72.0)    # rear-wall leg rivets (3)
CORNER_ZR_SIDE = (24.0, 56.0)         # side-wall leg rivets (2), interleaved with the wall leg
CORNER_HT      = 80.0                  # rear bracket height (covers the ~90 mm rear wall)
# LID_FRONT_FL (front-lip flange flat) is DERIVED below from the seam solver:
# the lip runs from the fold to the VERY BOTTOM of the base (#760).
# LID_REAR_LAP (rear-lap length) is DERIVED by the rear-seam solver below
LID_SIDE_LIP = 16.0  # inward lip at the bottom of each lid side wall (screws to the base from below)
# Lid -> body fixing scheme:
#   FRONT  : the Top plate's front lip screws horizontally into the Front panel.
#   REAR   : the Top plate's rear edge laps onto the angled TRANSITION SURFACE and
#            screws straight down into hand-tapped M3 holes there (no fixing on the
#            Rear panel). Same joint as the front lip: ONE tap, ONE screw SKU.
#   SIDES  : the Top plate has down-turned WINGS that tuck INSIDE the Side panels
#            for repeatable lateral alignment (locating only, no screws).

# --- foot pedals: Cherub WTB-006, caliper-measured 2026-07-28 (issues #358/#360)
# Reference CAD: hardware/cherub_wtb006_pedal/ + the "Cherub WTB-006 Footswitch"
# Fusion doc. The pedal is a WEDGE: wider + taller at the back (cable end),
# mounted toe toward the player (back = rear/high v). Box model uses the MAX
# cross-section; the taper only ever adds clearance.
PEDAL_W      = 76.35          # case width at the back (tapers to PEDAL_TOE_W at the toe)
PEDAL_TOE_W  = 73.08          # ...and at the toe: the case is a WEDGE IN PLAN too, not
                              # just in height. Anything that has to sit CLOSE to a side
                              # wall must ask pedal_half_width() where along the case it
                              # is; PEDAL_W alone is only honest at the back edge.
PEDAL_D      = 109.87         # case length, back to front
PEDAL_BODY_H = 24.9           # case height at the back (slopes to 22.1 at the toe)
PEDAL_PAD_T  = 2.2            # anti-slip pad thickness, bottom AND top
PEDAL_H      = PEDAL_BODY_H + 2*PEDAL_PAD_T   # 29.3 overall standing height
# One horizontal through-screw per side pins the shell halves; each end has a
# 10mm-dia boss + head protruding 3.45mm from the case wall. The bosses pass
# UNDER the faceplate beside the slot -- checked in _check() 3b.
PEDAL_SCREW_BACK   = 23.24    # boss axis, distance from the case BACK edge (v)
PEDAL_SCREW_Z      = 10.10    # boss axis height above the case bottom (excl. pad)
PEDAL_SCREW_BOSS_D = 10.0     # boss/sleeve outer dia at the wall
PEDAL_SCREW_SPAN   = 83.25    # overall width across both screw heads
# Bottom anti-slip pad footprint (from the user-refined Fusion model 2026-07-28):
# inset from the case back edge, used for the pedestal locating pocket.
PEDAL_PAD_W          = 64.61  # bottom pad width
PEDAL_PAD_D          = 90.0   # bottom pad length
PEDAL_PAD_BACK_INSET = 16.43  # pad rear edge inset from the case back edge
# Four BASE screw holes on the underside, in two rows across the case
# (user-measured 2026-08-16, issue #716). They sit UNDER the anti-slip pad, so
# both rows are dimensioned off the SIDE screw axis -- the only datum you can
# find on the case without pulling the pad. Bolting through these replaces the
# pedestal's provisional gravity+pocket retention.
PEDAL_BASE_ROW_BACK_OFF = 4.0    # rear row, rearward of the side-screw axis
PEDAL_BASE_ROW_PITCH    = 80.0   # rear row to front row, toe-ward
PEDAL_BASE_SPAN_REAR    = 55.75  # centre-to-centre across the rear pair. FOURTH reading,
                                 # and it lands back on the first: 55.75 -> 54.05 -> 54.5
                                 # -> 55.75 (all 2026-08-16). The 54.5 print read narrow,
                                 # which points the same way. Note the front pair has only
                                 # ever been measured ONCE (53.00) -- if the rear needed
                                 # four passes, the front deserves a second.
PEDAL_BASE_SPAN_FRONT   = 53.0   # ...and the front pair (the case tapers toe-ward)
PEDAL_BASE_HOLE_D       = 4.0    # INFERRED, not measured. First called M3-ish (3.0-3.4),
                                 # but the Ø3.5 pin later asked for cannot enter a 3.2 hole,
                                 # so the pin call supersedes it and the hole reads M4-ish.
                                 # Confirm with a drill shank or pin gauge before this
                                 # number reaches the pedestal decks.
PEDAL_BASE_REAR_BACK  = PEDAL_SCREW_BACK - PEDAL_BASE_ROW_BACK_OFF   # 19.24 from the back edge
PEDAL_BASE_FRONT_BACK = PEDAL_BASE_REAR_BACK + PEDAL_BASE_ROW_PITCH  # 99.24 from the back edge
FSW_SLOT_W = PEDAL_W + 2.0    # slot width (u) = 78.35, 1.0mm/side. The side screws DON'T
                              # drive this: their bosses duck ~6.6mm under the faceplate
                              # beside the slot (checked in 3b). The case governs, and its
                              # taper means the widest section crossing the plate plane is
                              # only ~76.05 -- real clearance is >=1.15mm/side. Floor is the
                              # lid-drop alignment over 10 pedals (~0.6mm tolerance stack).
FSW_SLOT_CLR_D = 3.0          # HORIZONTAL front+rear clearance target around the pedal.
# FSW_SLOT_D is defined after SLOPE_ANGLE below: the slot lives in the SLOPED
# faceplate but the pedal is HORIZONTAL, so the on-slope slot depth must be the
# horizontal envelope divided by cos(slope) -- without that the projected
# opening was only 0.16mm/side for the WTB-006 (and 0.28mm/side for the ASP-1).
# Pedal seating rule (issue #373, replaces the old FOOTPLATE_PROUD=12 constant):
# the pedal's BODY TOP (case top, under the top pad) sits FLUSH with the sloped
# faceplate surface at the slot's UPPER (rear) rim; only the pad stands above the
# metal. The plate keeps rising for half a slot past the pedal centre, so with the
# old +12 rule the pad top ended up ~0.8 mm BELOW the rear rim and the pedals read
# sunken. Flush-at-rim lands the pad ~15 mm over the slot centre-line -- taller
# front pedestals as a bonus (more insert depth).
PLATFORM_MARGIN = 2.0         # platform shelf overhang past the pedal footprint (stay within the slot)
PLATFORM_FOOT   = 18.0        # base screw inset band (holes ff/2 from the platform edge)
# The pedal platforms are 3D-PRINTED pedestals (they replaced the folded sheet
# boxes): PETG/ASA, solid walls, >=40% infill. M3 brass heat-set inserts
# (~M3 x 5.7 long x 4.6 OD) melt in from BELOW at the base's PLAT_SCR holes
# (bolted from under the floor). The WTB-006 has NO base screws (side screws
# only), so the deck instead gets a shallow LOCATING POCKET for the bottom
# anti-slip pad -- PROVISIONAL retention: gravity + pocket + foot pressure.
INSERT_PILOT_D  = 4.5         # heat-set pilot bore -- sized for M3 5x5 inserts
                              # (5.0 OD knurled, ~0.5mm interference; the old 4.0
                              # suited the 4.6-OD x 5.7 type)
INSERT_DEPTH    = 6.0         # pilot depth (5.0 insert + 1.0 melt allowance)
PLAT_WALL       = 3.0         # printed perimeter wall (cavity hollowing)
PLAT_DECK       = 8.0         # printed top deck (full insert engagement)
POCKET_DEPTH    = 1.2         # bottom-pad locating pocket depth (< PEDAL_PAD_T)
POCKET_CLR      = 0.6         # pocket clearance over the pad footprint (total)
# --- pedal SLED (issue #719): the pedestal split in two -----------------------
# The pedal is retained by M3s driven DOWN through its four base holes, so the
# screw head lands INSIDE the pedal and the pedal must be open to be fastened.
# But the shell halves are held by one ~83 mm through-pin, which needs ~91 mm of
# clear axial run to insert -- and the widest gap beside a seated pedal is
# 12.4 mm, in either enclosure. So the pedal can only be closed on the bench,
# which means it must be screwed down on the bench too. The deck therefore has
# to come OUT: a flat sled the pedal bolts to, dropped into the tub as one unit.
# Walls are not the blocker and no wall shape fixes this -- the neighbouring
# pedal is.
SLED_T       = 7.0            # >= INSERT_DEPTH 6.0 plus a 1.0 floor under it
SLED_CLR     = 0.2            # slip fit per side in the tub bore. 0.5 printed and
                              # seated but WIGGLED (2026-08-16) -- 1.0 mm of total
                              # play, and since the retention screw only clamps
                              # (its Ø3.5 bore adds +/-0.25 of its own), the bore
                              # fit is the ONLY thing locating the pedal.
                              # Deliberately on the sled, not the bore: the sled
                              # derives from SKIRT_IN_*, so tightening reprints a
                              # 19 g part instead of the tray. If 0.2 binds on a
                              # given printer, open it up -- that is another 19 g,
                              # whereas a too-tight BORE would be a tray reprint.
SLED_BOT_CHAM = 0.6           # bottom-edge lead-in. Elephant foot on the first
                              # layers is what makes a tight printed fit bind at
                              # the very bottom, exactly where it has to seat --
                              # chamfering it is what buys the tighter nominal.
# The BOTTOM anti-slip pad comes off (it has to -- the base holes are under it),
# so the metal base clamps straight onto the sled instead of through 2.2 mm of
# rubber. The tub deck drops by exactly enough to put the metal base back where
# the pad-on design had it, so EVERYTHING above the base -- case top, top pad,
# faceplate slot, the flush-at-rim rule of #373 -- is untouched.
SLED_DECK_DROP = SLED_T - (PEDAL_PAD_T - POCKET_DEPTH)   # 6.0
# --- the SAME idea on the 10-pedal console, with the ring SANDWICHED ----------
# The mini's tub is part of the tray, so it needs no fixing of its own. A console
# ring is a free part, and a ring held only by the faceplate has 0.30 mm of
# vertical play -- the buzz the SKIRT_GAP comment already warns about. So the
# ring gets a floor, the sled lands on it, and the FOUR EXISTING chassis screws
# pass up through clearance holes in that floor and thread into the sled:
# ring + sled + base plate clamped in one joint. No new fastener, and no new or
# moved hole in segno_base.dxf -- the sled footprint swallows the pattern that
# is already there.
CONSOLE_SLED_T = 12.633   # thicker than the mini's, because this sled takes M3x5
                          # from BOTH faces (pedal above, chassis below) where the
                          # mini's only takes them from one. Derived as the FRONT
                          # row's metal-base height less RING_FLOOR; _check() holds
                          # that, so the three numbers cannot drift apart.
# Reseat recalibration (#760): the lid now seats on the SEAM-SOLVER anchor, a
# plane 2.0 mm forward of the frame the 2026-07-28 platform measurements were
# taken against -- i.e. 2*tan(SLOPE_ANGLE) HIGHER. Frozen at the measured
# 3-decimal figure (= round(2*math.tan(math.radians(SLOPE_ANGLE)), 3) = 0.443,
# which lands within 0.02 mm of both rows' re-measured drops); kept a literal so
# the platform heights stay bit-for-bit what is already printed/cut. The full
# story is at FACE_SEAT. One named source now, not a constant pasted per site.
RESEAT_CAL = 0.443
RING_FLOOR = 1.6 + RESEAT_CAL  # front-row ring floor (+#760 reseat recal). The mid row's "floor" is the tall
                          # pedestal deck it already had -- same formula, and only
                          # the front row is tight enough for this to bind.
# Light-baffle TUB around the pedal: the pedestal's walls rise from the deck to
# ~1mm under the sloped faceplate with their INNER faces set back SKIRT_SETBACK
# behind the slot cut line -- from above you see ONLY faceplate, and the reveal
# reads as the slot continuing down a dark channel (the wall face), not as a
# ledge or the enclosure interior. Print BLACK (PETG/ASA).
# The side screw bosses (span 83.25) would cross the wall line, so each side
# wall gets a full-height vertical CHANNEL the boss slides down at drop-in --
# it also guides the pedal into the pad pocket.
SKIRT_SETBACK = 0.4           # wall inner face tucked behind the slot cut line
SKIRT_GAP    = 0.0            # wall top FLUSH on the REAL faceplate underside
                              # (user call 2026-08-18, #760: the 0.3 standoff read
                              # as a visible gap). Risk accepted: an FDM-proud
                              # tower can lift the lid off its flange seats -- if
                              # assembly rocks on hardware, restore 0.3 here (or
                              # sand the tub tops).
# The assembled faceplate seats ABOVE lid_top_z's bare
# slope, and by a row-dependent amount -- measured in "Segno console (populated)"
# (the manufacturing source of truth) 2026-07-28: +1.6 over row 1, +0.7 over
# row 2. Without this the skirt gap came out 2.6/1.7 instead of 1.0.
# Measured seating offset of the REAL plate above the bare geometric slope, from
# the "Segno console (populated)" doc. It used to be a two-point LINE,
# face_drift(v) = 1.96 - 0.00533*v, fitted at the row-1 and old row-2 lines.
#
# That slope was not the plate. -0.00533 is the tan/sin unit error (0.005253) to
# within 1.5 %: the fit was measuring #742's bug, not a physical taper. Re-reduce
# the same three measurements against a sin slope and they land on
# +1.955 / +1.942 / +1.939 -- a CONSTANT, to within 0.016 mm. Three independent
# points agreeing that closely is the evidence that sin is right.
#
# Correcting both together moves platform_h by -0.0003 mm at the front row and
# +0.015 mm at the mid row, so nothing already printed or cut is invalidated.
#
# 2026-08-18 (#760): the lid now seats on the SEAM-SOLVER anchor. The plane the
# 2026-07-28 measurements were taken against sat 2.0 mm rearward (the old doc
# frame), i.e. 2*tan(SLOPE) = 0.443 mm LOWER than the real seat. Re-measured in
# the reseated doc: pedals 0.46 (row 1) / 0.423 (row 2) below the slot rims --
# the uniform +RESEAT_CAL recalibration lands within 0.02 mm of both. Platforms
# printed before this are 0.44 mm short.
FACE_SEAT = 1.95 + RESEAT_CAL

SKIRT_DRIFT_ROW1 = FACE_SEAT   # was 1.6 -- the same #742 fit; see FACE_SEAT
SKIRT_DRIFT_ROW2 = FACE_SEAT   # was 0.5 -- ditto; both rows share one constant now
                         # rearward move + #373 flush-raise: 0.5 leaves 0.3 mm to the
                         # REAL plate at the tub's rear band (probed in the populated doc)
SKIRT_NOTCH_W = 12.0          # cable notch in the rear tub wall, centred (the
                              # WTB-006 cable leaves the case at the back)
SKIRT_OUT_W  = 88.75          # pedestal footprint W (unchanged from the fence rev)
SKIRT_OUT_D  = 115.37         # pedestal footprint D (rear must clear the posts)
# Tub inner opening = the slot outline (projected flat) + setback. Slot depth is
# an on-slope figure; horizontal = *cos(SLOPE_ANGLE). Defined after SLOPE_ANGLE.
SKIRT_BOSS_CH_W    = 14.0     # boss drop-in channel width (boss dia 10 + 4)
SKIRT_BOSS_CH_HALF = PEDAL_SCREW_SPAN/2 + 0.7   # channel floor: swallows the boss tip
SKIRT_BOSS_CH_X    = PEDAL_D/2 - PEDAL_SCREW_BACK   # +31.695: boss axis, rearward of centre

# --- screens (capacitive touch, mounted from BEHIND; aperture < bezel) --------
BIG_BEZEL  = (353.0, 208.0)   # 15.6" panel BODY -- UPERFECT (PROVISIONAL listing 13.9x8.2in, caliper
                              # on arrival): cased portable monitor, connectors exit the SIDE edges,
                              # bezel ~symmetric (no bottom connector strip). Replaces the old bare
                              # panel's 359.5x223.75 (glass + 17mm bottom strip) -- that strip was a
                              # fiction here and pinned the support posts 23mm too far forward.
BIG_W, BIG_H     = 342.5, 193.0   # 15.6" faceplate APERTURE -- ~0.8mm/side inside the 344.16 x 193.59
                              # ACTIVE area so the faceplate lip overlaps the active edge (no light leak).
                              # The decal (active image, 344.2x193.6) stays; the aperture reveals IT, not
                              # the full glass -- the glass bezel (up to 359.5x206.5) hides behind the lip.
BIG_DEPTH  = 8.0              # thin panel (3-6 mm); HDMI/USB driver board mounts flat inside
SMALL_BEZEL = (165.0, 100.0)  # 7" module outline (APROTII: ears 164x99)
SMALL_W, SMALL_H = 153.75, 85.5   # 7" aperture = the 153.75 x 85.5 visible (active) area; reveals it
                              # fully (mounted from behind), no lip overlap on this screen.
SMALL_DEPTH = 12.0           # 7" panel body 9 mm + connectors (APROTII sheet)

# --- 7" screen cradle (3D print, #762) -----------------------------------------
# Floor-anchored printed stand for the APROTII 7": a flat FRAME the module screws
# onto by its corner-ear holes, on two wedge LEGS whose top face is cut at
# SLOPE_ANGLE so the frame lies parallel to the faceplate underside. The glass is
# pressed against the lid by a 2 mm FELT layer on the frame rim (the user's
# compliance call: felt absorbs the height tolerance, the leg slots absorb the
# rest). The screens do NOT lift with the lid on this scheme: service = lift the
# lid, screens + cables stay put.
# All 7"-cradle geometry is DISPLAY-WINDOW-CENTRED. Source of truth: the vendor
# STEP ("lcd 7inch cap 1024 600.stp", user-supplied 2026-08-19). The model's
# front face decomposes into the cover GLASS (164 x 100.1, centred on the
# model origin -- the datasheet's "164x99" was the glass, not the module) and
# a CLEAR DISPLAY WINDOW of 154.5 x 89.1 centred at model (-1.75, +2.5): that
# window is the hard optical boundary, so the aperture centres on IT and it is
# the origin here. STEP-derived window-to-module-edge margins L3.55 / R8.0 /
# B22.6 / T12.6 (user calipers said L4.3/R7.3/B21.8/T16.3 -- top differs by
# 3.7 mm; the powered-screen FIT TEST is the final referee on where the lit
# pixels sit inside the window). FIT-TEST VERDICT (printed 2026-08-19): the
# lit area sits 2.75 mm LOWER than the STEP's window centre (2.75 black strip
# at the aperture top, bottom flush) -- consistent with the calipers. The
# frame origin is therefore re-anchored to the LIT area: every window-centred
# y below carries +2.75 vs the raw STEP values. Reprint the fit test after
# any further change here. Module body over-all: 166.1 x 124.3 (the PCB
# hangs ~22 below the glass). The four M3 TABS (O3.1, 1.7 thick) live
# S7C_GLASS_TO_TABF (5.6, user-measured) BEHIND the glass front, protruding
# above/below the glass -- screws come from the module's front side into
# bosses that rise to the tab plane.
S7C_HOLES = ((-76.80, 55.25), (80.30, 55.25),
             (-76.80, -59.75), (80.30, -59.75))   # tab holes, lit-centred
S7C_MOD_BB   = (-80.80, -64.40, 85.25, 59.90)     # module outline, lit-centred
S7C_TAB_T    = 1.7     # tab thickness
S7C_GLASS_TO_TABF = 5.6   # glass front -> tab FRONT face. USER-MEASURED
                          # 2026-08-19: the vendor STEP said 6.7, but the
                          # round-1 fit test held the glass 1.1 off the plate
                          # ("lower the standoffs by 1.1"). Physical unit wins.
                          # (Glass altitude in the tower is invariant to this:
                          # deck + boss_h + TAB_T + GLASS_TO_TABF collapses to
                          # deck + MOD_DEPTH + GAP.)
S7C_MOD_DEPTH = 14.8      # glass front -> module back (PCB) plane
S7C_GAP      = 0.5     # deck sits this far behind the module back --
                       # only the bosses touch the module (PCB never contacts)
S7C_FRAME_W  = 180.0   # tower outline (centred on the module body)
S7C_FRAME_H  = 138.0
# --- one-piece support TOWER (v3, "more beefy" -- user call 2026-08-19) -------
# A closed wedge box: 4 mm perimeter walls, sloped deck carrying the window +
# tab bosses, wide floor flange with SIX M3 anchors into the base floor (the
# #762 stations). Touch loads on the screen go tabs -> bosses -> deck -> four
# walls -> floor; no slender columns, no bolted joints in the load path.
S7T_WALL   = 4.0       # wall thickness
S7T_DECK   = 5.0       # deck thickness (along the deck normal)
S7T_FLANGE = 12.0      # floor flange width (outward)
S7T_H0     = 66.06     # deck-top height (mm, above the base floor TOP) under the
                       # display-window centre. From the MEASURED underside plane
                       # in Fusion (world: z = 12.43 + tan(SLOPE)*y mm): glass
                       # kisses the lid with ZERO shim; if the print lands low,
                       # M3 washers under the module tabs take up the gap.
S7C_FRAME_T  = 5.0     # frame plate thickness
S7C_WIN_W    = 146.0   # open window: PCB + connectors + backlight switch live
S7C_WIN_H    = 96.0    # here untouched (ports point rearward through the window)
S7C_LEG_SEP  = 158.0   # leg centres, symmetric about COL_U -- ON the frame's side
                       # rails (u +-70..88), clear of the open window
S7C_LEG_W    = 30.0    # leg web width (along u)
S7C_LEG_T    = 6.0     # leg web thickness (along v)
S7C_FOOT_L   = 40.0    # foot flange (along v), 2x M3 to floor anchors (#762)
S7C_FOOT_GAUGE = 24.0  # foot hole spacing along v
S7C_ADJ      = 6.0     # height regulation budget: felt compression (~1) + up to
                       # ~5 of M3 washer shims between leg pad and frame
# (nominal leg height is computed in build_screen7_cradle_steps -- it needs
#  SCREEN_TOP_V, which is defined further down)

# --- LEDs / encoder -----------------------------------------------------------
# Status indicators = SMD LEDs (WS2812B), NOT through-hole: a WHITE PLA pill
# diffuser insert sets into each slot and glows through, and an EIGHT-LED
# segment cut from bare 144 LEDs/m strip snaps into a channel on its back (#927,
# #930). It is NOT the 16 x 8 puck PCB in hardware/led_strip/ and not VHB tape --
# see the LED_STRIP_* block below for the source and how it is retained.
# Segments daisy-chain pedal-to-pedal with 3 wires (5V/data/GND).
LED_SLOT_H = 6.0          # diffuser-slot height (v); corner r = H/2 -> full round ends
LED_SLOT_W = 60.0         # pill window per indicator pedal (one 5050 diffused behind it)
LED_INS_CLR   = 0.2       # diffuser-insert lateral clearance in the slot (total)
LED_INS_PROUD = 0.4       # lens stands this far above the outer skin
LED_INS_FLANGE = 4.0      # shoulder overhang past the slot, all around (seats on the
                          # faceplate UNDERSIDE -- the insert pushes in from INSIDE).
                          # 3.0 until #930: a 12 mm-wide 144/m strip cannot live in the
                          # 12 mm flange that gave. 4.0 makes it 14 and restores the
                          # same 0.7 wall. There is room -- the pill centre is LED_GAP
                          # (12) behind the pedal slot, so the wider shoulder still
                          # stops ~5 clear of the aperture.
LED_INS_FL_T  = 1.5       # shoulder thickness
# --- a cut WS2812B strip segment sits in the back of the diffuser (#927) -----
# Owner call 2026-08-28: the light source is a **bare non-waterproof WS2812B
# strip**, cut to one segment per pill -- NOT the 16 x 8 puck PCB in
# hardware/led_strip/. The density landed on 144 LEDs/m in #930 (see
# LED_STRIP_PITCH); segno_console_shopping_list.md orders to that.
#
# It used to be a 6 x 6 x 0.8 "nest" with the module VHB-taped over it, which
# registered the 5 x 5 PACKAGE rather than anything the size of the source -- and
# did not even seat: a 1.6-tall PLCC4 in a 0.7-deep recess holds the source 0.9
# clear of the flange, with tape spanning the gap.
#
# THE STRIP IS THE SPRING. Its own 3M tape is useless here -- the LEDs must face
# the lens, which turns the adhesive to face away into the console -- so the strip
# is trapped mechanically instead. That is what makes this work where a rigid
# board could not: at LED_STRIP_T of flex PCB you bow the segment slightly, drop it
# past the lips, and let it flatten. Nothing in the PRINTED part ever has to
# deflect, so none of it has to be springy.
LED_PKG       = 5.0       # WS2812B PLCC4 body, 5.0 x 5.0
LED_PKG_H     = 1.6       # ...and its height -- the number the old nest ignored
LED_PKG_CLR   = 0.3       # per side, package to its recess
# 144 LEDs/m, IP20, 12 mm wide (owner call 2026-08-28, #930). The density is
# picked for EVENNESS, not brightness: light only has LED_WEB + the lens to
# spread through, and a bar reads continuous when the LED pitch is within about
# twice that. 144/m is 6.94 against 3.2 -- 2.2:1. 60/m would be 5.2:1, which is
# three visible blobs per pill.
LED_STRIP_W   = 12.0      # *** MEASURE BEFORE PRINTING THE DIFFUSERS (#930) ***
                          # 144/m is 12 wide where 30 and 60/m are 10 -- but the
                          # chosen part's listing CONTRADICTS ITSELF: its product
                          # image says 12, its compare-with-similar row says
                          # "PCB Board Width: IP30/65 - 10mm; IP67 - 12mm". 12 is
                          # taken because the image is specific to this part and
                          # agrees with the reference sheet. It is NOT verified.
                          # The lips grip 0.4 per side, so a 2 mm error either
                          # jams the strip or drops it straight through.
LED_STRIP_OA  = 2.13      # OVERALL thickness, off the reference sheet for IP20.
                          # The chosen part's image says 0.5 mm of PCB, which
                          # corroborates this within 0.03 (2.13 - 1.6 = 0.53).
                          # The PCB is derived FROM the overall rather than
                          # guessed -- an earlier 0.35 "flex PCB" guess was 0.18
                          # thin and would have jammed under the lips.
LED_STRIP_T   = LED_STRIP_OA - LED_PKG_H   # 0.53 of PCB; the rest is the 5050
LED_STRIP_PITCH = 1000.0 / 144.0               # 6.944 by definition at 144/m.
                          # The chosen part's image labels 6.5, which cannot be
                          # right (6.5 x 144 = 936, not 1000) -- marketing art,
                          # not a dimension. Worth confirming on the real strip
                          # anyway, since it sets the cut length.
LED_STRIP_N_MAX = int(LED_SLOT_W // LED_STRIP_PITCH)  # 8 is all that fits the 60 pill
# 8 or 7 is OPEN, deferred to when the strip is in hand (owner, 2026-08-28).
# The pill is rendered as a CENTRE-BRIGHT GRADIENT falling off to both ends, and
# an EVEN count has no centre pixel -- with 8 the middle two sit 3.47 either side
# of centre. They are 6.94 apart against 3.2 mm of diffusion, so they should read
# as one bright centre, and 8 fills the pill to within 2.2 mm of each end where 7
# leaves 5.7. That is a judgement about how it LOOKS, which is why it waits for
# the real part rather than being settled here.
#   8 -> no centre pixel, better fill      (current)
#   7 -> a true centre pixel at 0, dimmer ends
# Changing it re-cuts the channel, so it changes the print -- nothing is printed
# yet, which is exactly why now is the cheap time to still be undecided.
LED_STRIP_N   = LED_STRIP_N_MAX                       # <- the one number to flip
LED_STRIP_SEG = LED_STRIP_N * LED_STRIP_PITCH         # 55.56 cut length
LED_STRIP_CLR = 0.3       # per side, across the width
LED_STRIP_T_CLR = 0.15    # ...and ACROSS THE THICKNESS. Without it the channel is
                          # exactly LED_STRIP_T deep, off a LED_STRIP_OA the block
                          # above flags as unverified -- a strip 0.1 over nominal
                          # then cannot flatten, so it stays bowed and pushes on
                          # the lips, which is the one thing the design says the
                          # printed part never has to take. Every other axis had a
                          # clearance; this one did not.
LED_CH_L      = LED_STRIP_SEG + 1.4   # cut segment plus slop -- scissors land
                          # +-0.5 either way. DERIVED now: a fixed 18.0 silently
                          # stopped fitting the moment the segment went from one
                          # LED to eight.
LED_WEB       = 0.8       # white PLA left between package and lens base. This is
                          # the diffusing wall: thinner reads as a hot spot, and
                          # it sets how deep the package recess can go.
LED_LIP       = 0.7       # lip overhang past the channel wall -> 0.4 of grip on
                          # each strip edge NOMINALLY, i.e. with the strip centred.
                          # It is not centred by anything: the channel gives it
                          # +-LED_STRIP_CLR of lateral play, so a strip against one
                          # wall has 0.7 of grip on that side and 0.1 on the other.
                          # 0.1 is inside one layer line, and nothing else retains
                          # the strip -- its adhesive faces away by design.
                          # *** OWNER CALL (#930): live with 0.1 worst case, or buy
                          # it back. The levers are LED_LIP (1.0 makes the worst
                          # case 0.4, but then the strip has to bow past 0.7 of
                          # interference instead of 0.4) and LED_STRIP_CLR (a
                          # tighter channel has less play, but LED_STRIP_W is the
                          # unverified number in this file, so tightening it now is
                          # betting on a width the vendor listing contradicts).
                          # Settle it with the strip in hand, not here.
LED_SHOULDER  = 0.75      # ledge the strip's LED-side face lands on. Without it
                          # the up-stop is the LED package bottoming in its recess
                          # -- i.e. the fitting force lands on the part, not the LED.
LED_PKG_Z_CLR = 0.15      # ...and the shoulder is only really the stop if the
                          # package top stops SHORT of the recess ceiling. At zero
                          # the two contacts are line-to-line, so a package on the
                          # high side of its height tolerance lands the fitting
                          # force on the LED after all -- the very thing
                          # LED_SHOULDER exists to prevent. 0.15 of air makes the
                          # order unambiguous and is nothing optically.
LED_WALL_MIN  = 0.6       # channel wall floor; the flange edge caps the outside
# Neither of the next two is a manufacturing allowance -- they are CAD tripwires
# set just under what the layout delivers, so that moving a constant fails the
# build. As-printed is a separate question nobody has answered: a 14 mm FDM
# shoulder can come out 0.2 over, and with a glue bead that eats most of the 0.39
# to the post pad. Check the first printed diffuser against a post before gluing
# ten of them.
LED_POST_MIN  = 0.3       # gap from the shoulder's REAR edge to the support-post
                          # top pad, checked only where the two share u. Since
                          # POST_PW is derived to fit BETWEEN the pill shoulders
                          # (2026-09-04) they share none, and this gate is a
                          # tripwire that stays armed for whoever widens the post
                          # or the flange again. Before that, at POST_PW = 40, it
                          # held a 0.39 mm gap and pinned LED_GAP to a 0.09 mm
                          # window.
LED_LAND_MIN  = 2.4       # faceplate metal left between the shoulder's front edge
                          # and the pedal aperture behind it -- the land the flange
                          # is glued to, MEASURED OFF THE EMITTED CUTS (the aperture
                          # is cut PEDAL_AP_DEV rearward of v + FSW_SLOT_D/2 for the
                          # fold development, #760). The land is LED_GAP -
                          # LED_SLOT_H/2 - LED_INS_FLANGE - PEDAL_AP_DEV: 2.41 at
                          # LED_GAP = 12 (a tripwire, #930), 6.41 at the 16 of the
                          # 2026-09-04 trial. A 12 mm strip needs LED_INS_FLANGE >=
                          # 3.9 (channel wall + LED_WALL_MIN), so with LED_GAP back
                          # at 12 the 3.0 a glue bead wants cannot hold -- that is
                          # what the trial also buys. Anything that eats into the
                          # land past this floor fails the build.
D_ENC     = 7.2      # EC11 encoder bush (M7 thread; 7.0 was nominal-tight,
                     # the vendor STEP shows the thread OD needs the 0.2, #762)
# EC11 anti-rotation tab: NO keyway in the disc (user call 2026-08-19: the
# slot looked bad -- the tab gets snapped off the EC11 instead; the nut alone
# clamps the disc).
# Encoder knob -- a PURCHASED part: O50 x 18 x O6 bore, black aluminium, plain
# barrel (the owner's chosen knob). These are the VENDOR's numbers, not design
# freedom: KNOB_D is what the ring window was sized around and KNOB_BORE_D is the
# EC11's 6 mm shaft. The only modelled guess is the nut relief -- see
# build_encoder_knob_step.
KNOB_D        = 50.0
KNOB_H        = 18.0
KNOB_BORE_D   = 6.0
KNOB_BORE_TOP = 12.0   # blind bore: stops 6 mm short of the top face
KNOB_NUT_D    = 22.0   # underside relief over the EC11 mounting nut (assumed)
KNOB_NUT_H    = 4.5
KNOB_TOP_FILLET = 1.6
RING_OD   = 67.0     # diffused-annulus ring window, sized over the NeoPixel
RING_ID   = 51.5     # RING 24 (O65.5 / O52.3 / 3.2) -- the ring the owner fitted,
                     # mounted ON the ring board around the EC11. It replaced a
                     # Ring 16 (44.5/31.7) in 2026-08-22; the ring BOARD has not
                     # caught up (it is O60 with its module pads on a O42.1
                     # circle, both Ring-16 numbers) -- see #794.
IND_PITCH = 50.0     # indicator LED pitch

# --- rear I/O -----------------------------------------------------------------
# Issue #743. The Pi moved inboard and its port WINDOW came out, so there is no
# opening in the rear wall and no swappable I/O sub-panel any more: every
# connector is a panel-mount part fitted straight into the FOLDED rear wall
# (segno_base is ONE blank -- floor + 4 walls, weld-free, corner brackets rivet).
# Losing HDMI / Ethernet / SD access from outside is deliberate.
#
# EVERY dimension below carries a provenance in REAR_IO_PROVENANCE. Cutting a
# panel against a number nobody checked is how a 850 mm blank becomes scrap, so
# the unchecked ones are listed by name on the drawing and in the build summary
# rather than hidden behind an optimistic comment.
# Power button: APIELE 19 mm HIGH ROUND momentary (B079HTQ7XD). Stainless, IP65,
# M19x1, 1e6 mechanical cycles, screw terminals, 3-year warranty. MOMENTARY, which
# the soft-shutdown wiring requires -- it drives the Pi's own PWR pads (not a
# GPIO; a Pi 5 cannot wake from one), it does not break power.
#
# Chosen over the UL+CE ZJWZJH (B09CCPDC1C) at HALF the price: that listing's
# UL/CE and IP67 buy nothing here -- this is a dry contact to a 3.3 V logic pad,
# not a mains switch on a wet deck -- while APIELE has 1039 reviews at 4.7 against 9 at
# 3.9, and a TALLER head. Both ship dimension drawings and both land inside the
# constants below, so the choice does not touch the panel.
#
# NOT ILLUMINATED, deliberately. An LED ring forces a flat waterproof face with
# almost no travel, which is exactly the dead "touch pad" feel we were rejecting;
# the domed head is what buys real travel and a positive click. Nothing is lost:
# the button faces AWAY from the player, and a 7" and a 16" screen are far better
# "it is on" indicators than a lamp nobody can see from the playing position.
# faceplate_holes()'s "power state shows on the rear power button" no longer
# holds -- see the note there.
# Both constants deliberately BRACKET the two candidates rather than tracking one,
# so swapping switch does not re-cut the panel:
D_PWRBTN      = 19.5  # M19x1 needs >19.0 to pass. APIELE says "19", ZJWZJH's
                      # drawing says Ø19.5 -- 19.5 accepts both, and a Ø25 bezel
                      # covers the slop. Cutting 19.0 would jam the ZJWZJH thread.
PWRBTN_HEAD_D = 25.2  # hex bezel ACROSS CORNERS: ZJWZJH 25.2, APIELE 25.0. The
                      # corners are what has to clear a neighbour, not the flats.
# Fuse: a GENERIC 5x20 screw-cap panel holder, by decision -- it is a small black
# cap on a rear panel, the one station where generic costs nothing to look at.
# That class is consistently Ø12.0, NOT the Ø12.5 the SCI R3-11 wants, and the
# error is not symmetric: a 12.5 hole around a 12.0 thread sits loose and lets the
# holder spin when the cap is turned. Plastic body with a metal cap -- which is
# also right, since an insulating body around a live fuse in an earthed metal
# chassis beats a metal one. Rated 10 A / 250 V AC, far above this job.
#
# These holders ship FAST-BLOW fuses. See the T5A slow-blow note in the design
# doc: the two bucks' inrush will nuisance-blow a fast fuse at switch-on.
D_FUSE    = 12.0     # NeoLum B0GF33P9FF: "12 mm diameter aperture"; B0DLKJ813T:
                     # "Installation Hole 12mm". Two independent listings agree.
D_GND     = 6.5      # M6 earth / bond stud
# The inlet is USB-C PD (#754): one 20 V PD contract feeds the whole console and
# two bucks make 5 V at the load. It replaces a 9 V barrel because the barrel was
# only ever the buck's input -- nothing in the design uses 9 V -- and because a
# USB-C panel coupler takes the SAME D punch as the TRS jacks, so the inlet stops
# being a hole type of its own. Part: QIANRENON D-type USB-C F/F, 100 W, 10 Gbps
# (Amazon B0CQ4VD2N2). 10 Gbps matters: it means all 24 ways are wired, so CC
# passes and PD can negotiate. A charge-only coupler drops CC and nothing works.
# The chosen TRS is a D-SERIES jack (MEIRIYFA B0G5GHCCHM, "fits standard D Series
# panel mount designs"), NOT a threaded-bushing jack -- so it takes the Neutrik D
# punch, a Ø24 bore with two M3 fixings, not a Ø10 round hole.
D_TRS_BORE       = 24.0  # Neutrik: "standardized D sized 24 mm panel cutout"
D_TRS_SCREW_D    = 3.2   # M3 clearance
# The D-series flange carries its two M3 on DIAGONALLY OPPOSITE corners, not a
# horizontal pair. Pattern SOURCED 2026-08-18: the QIANRENON PD coupler states
# "XLR panel / D-type panel mounting dimensions (19mm*24mm)" on its listing --
# 19 across, 24 vertical, one hole per diagonal corner: centres at
# (+-9.5, -+12) about the bore. Screw centre sits sqrt(9.5^2+12^2)=15.3 from
# the bore centre, 1.7 clear of the Ø24 bore edge + M3 radius, so _check()'s
# bore-edge rejection passes. A D shell is point-symmetric about the bore, so a
# part whose holes run the other diagonal mounts by turning it 180 deg -- one
# cut diagonal fits every D shell.
D_TRS_SCREW_DIAG = (19.0, 24.0)   # (du, dz) between the two diagonal M3 centres
D_TRS_KEEPOUT    = 30.4  # bore + the M3 pair
D_PD_BORE = D_TRS_BORE   # the PD coupler keeps the D-series punch (bore + M3 pair)
# CTRL_1 / CTRL_2 are Neutrik NJ6FD-V since 2026-09-04 (owner call, #993): a
# 6-pole switching 1/4" jack, vertical PCB pins, REAR-mounted through a plain
# round hole and held by its snap-on POM cap. Neutrik's drawing (nj6fd-v-3.dxf,
# "Panel cut out (rear side)") gives Ø12.00 and a panel of 1.20-1.50 mm; the
# STEP shows the snout is only 3.5 mm long, so a 2.0 mm panel leaves the cap
# nothing to snap to. Hence REAR_PANEL_T below. The old D-series TRS constants
# stay for the PD coupler. The station keep-out is deliberately still
# D_TRS_KEEPOUT: shrinking it would re-spread the stations and move the base's
# rear-wall window, and the spare air costs nothing.
D_CTRL_HOLE  = 12.0      # NJ6FD-V panel hole
REAR_PANEL_T = 1.5       # the rear panel is a separate flat: 1.5 mm for the NJ6FD-V cap
USB3_SQ       = 22.1 # USB 3.0 panel coupler: square across flats
USB3_CORNER_D = 24.1 # ...corners on this circle -> corner radius derived below
USB3_FLANGE_D = 28.5 # flange OD. This, not the cutout, is the real keep-out
MIDI_BODY_D      = 15.1  # REAN NYS325 panel cutout (distributor spec)
MIDI_SCREW_PITCH = 22.2  # RS attribute "Mounting Hole Distance 0.874 in" = 22.2
MIDI_SCREW_D     = 3.2   # M3 clearance

# What each rear-I/O dimension actually rests on. "measured" = the user's own
# calipers or dimensioned photo; "datasheet" = manufacturer or distributor
# figure, with the source named; "UNCONFIRMED" = nobody has checked it.
REAR_IO_PROVENANCE = {
    "D_PWRBTN":          "datasheet: APIELE + ZJWZJH drawings, M19x1; 19.5 brackets both",
    "PWRBTN_HEAD_D":     "datasheet: APIELE 25.0 / ZJWZJH 25.2 across hex corners; 25.2 brackets both",
    "D_FUSE":            "datasheet: two generic 5x20 screw-cap listings, 12 mm aperture",
    "D_GND":             "design: M6 stud clearance",
    "D_PD_BORE":         "datasheet: QIANRENON B0CQ4VD2N2 states D-type/XLR panel "
                         "dimensions 19x24 mm; the 24 mm bore is the D standard",
    "D_TRS_BORE":        "datasheet: neutrik.com NC3FD-L-1, 'standardized D sized 24 mm panel cutout'",
    "D_TRS_SCREW_DIAG":  "datasheet: QIANRENON B0CQ4VD2N2 'D-type panel mounting "
                         "dimensions (19mm*24mm)'; MEIRIYFA B0G5FZNH49 is the same "
                         "standard D shell (photos show the diagonal pair + screws)",
    "D_TRS_KEEPOUT":     "design: bore + the M3 pair (kept as the CTRL station width too)",
    "D_CTRL_HOLE":       "datasheet: Neutrik nj6fd-v-3.dxf 'Panel cut out (rear side)' Ø12.00 "
                         "[0.472\"], panel 1.20-1.50 mm; NJ6FD-V datasheet 'Chassis shape 12 mm'",
    "REAR_PANEL_T":      "datasheet: NJ6FD-V panel thickness 1.20-1.50 mm; snout 3.5 mm in the STEP",
    "D_TRS_SCREW_D":     "datasheet: D-series fixings are M3",
    "USB3_SQ":           "measured: user, coupler BODY across flats (PENGLIN B09VGK59XQ: "
                         "a round M24 barrel with two anti-rotation flats; NUT-mounted, "
                         "no screws -- the square cut grips the flats)",
    "USB3_CORNER_D":     "measured: user, coupler BODY across corners (= thread OD)",
    "USB3_FLANGE_D":     "measured: user, flange OD",
    "MIDI_BODY_D":       "datasheet: REAN NYS325, Ø15.1 panel cutout (Farnell/CPC)",
    "MIDI_SCREW_PITCH":  "datasheet: RS 70088596 attribute 'Mounting Hole Distance "
                         "0.874 in' = 22.2 (cutout attr 0.595 in = 15.1 anchors the template)",
    "MIDI_SCREW_D":      "datasheet: DIN-5 chassis sockets take M3",
}

def rear_io_unconfirmed():
    """Rear-I/O dimensions that rest on nothing yet, name -> value. Non-empty is
    NOT a build failure -- it is a do-not-cut-the-panel-yet list."""
    return {k: globals()[k] for k, v in REAR_IO_PROVENANCE.items()
            if v.startswith("UNCONFIRMED")}

# 22.1 / 24.1 are the coupler's BODY, so the hole has to be bigger than both or
# the part will not enter at all. 0.2 per side is deliberately the TIGHT end of a
# panel fit: the errors are not symmetric. Too tight is one hole eased with a file
# in a minute; too loose either rattles under the Ø28.5 flange or, if the coupler
# turns out to be a snap-in, never grips and cannot be undone on a cut blank.
USB3_FIT = 0.2

def _rr_from_corner_circle(side, corner_d):
    """Corner radius of a rounded square of `side` whose corner arcs are tangent
    to a circle of diameter `corner_d` -- i.e. that circle passes through the
    corners. Solves (side/2 - r)*sqrt(2) + r = corner_d/2 for r."""
    a, rr = side/2.0, corner_d/2.0
    r = (a*math.sqrt(2) - rr) / (math.sqrt(2) - 1.0)
    assert 0.0 < r <= a, (
        f"USB3: corner circle {corner_d} is not compatible with a {side} square "
        f"(derived corner radius {r:.2f})")
    return r

USB3_CUT_SQ = USB3_SQ + 2*USB3_FIT
USB3_CORNER_R = _rr_from_corner_circle(USB3_CUT_SQ, USB3_CORNER_D + 2*USB3_FIT)

# The old REAR_WIN_U did two jobs -- it placed the window AND anchored the board,
# Pi and buck inside. Those are now separate: the internal layout keeps its 175
# anchor (nothing inside moves because of a rear-panel change), and the connector
# cluster is free to use as much of the wall as it needs. It needs it: swapping
# the TRS to D-series took its keep-out from 16 to 30.4 and squeezed the gaps to
# 7.2 mm on the old 290 strip. The vents give the width back -- they run at 4x the
# free-area minimum, and _check() holds that.
BOARD_ANCHOR_U = 175.0  # main board / buck datum. NOT the connector cluster,
                        # and since #743 not the Pi either -- see pi_mount().
REAR_IO_SPAN   = 360.0  # cluster width; REAR_IO_Z set below (= wall mid-height)
REAR_IO_U      = None   # set to SCREEN_16_U below -- the panel is CENTRED ON THE
                        # 16" SCREEN, which is the thing a player lines it up with
                        # by eye. It was RIGHT-justified against EDGE. It used to be left-justified
                        # at 210, from when the console board lived under the 7"
                        # screen: the board terminates five of these stations, so the
                        # cluster follows the board. Both boards now sit under the
                        # 16" screen (see BOARD_U / pi_mount), which took the Pi
                        # ribbon from 402 mm to 30 mm. _check() asserts the
                        # right-justified form, so this constant cannot drift.

# --- rear I/O sub-panel (#751) ------------------------------------------------
# The cluster is DISMOUNTABLE: the wall carries a window, and a bolt-on panel
# carries the nine connectors. It was folded straight into the wall for one
# revision (77e0ef9b) on the grounds that the Pi's port window had gone away and
# the sub-panel had no home -- but that reasoning was about the WINDOW, not about
# the connectors. Cut into the wall, the loom can only be worked on inside a
# 850x423 box through a 46 mm slot, and a single stripped thread scraps the base.
# On a panel it lifts out, gets soldered on a bench, and a mis-drilled panel costs
# a panel. It is NOT a folded face of the base; it needs its own bond -- see
# docs/design/console-grounding-and-bonding.md.
REAR_WIN_CLR        = 3.0   # window clearance around the outermost station cutouts (v)
REAR_WIN_SIDE_CLR   = 6.0   # window side padding BEYOND the outermost station KEEP-OUTS
                            # (u). The window used to clear only the cutouts, which let
                            # the PD coupler's keep-out poke 0.2 past the opening's edge
                            # -- the flange visually kissed the window and there was no
                            # room to offer it up square (user call, 2026-08-18). Sides
                            # clear what has to PASS (flanges, nuts), not just the holes.
REAR_WIN_H_MIN      = 46.0  # minimum window height. Derived tight, the opening came
                            # out 30 mm on a 90 mm wall -- a letterbox that makes
                            # every connector a knuckle-scrape to reach and looks
                            # like a mistake next to the panel around it. 46 is the
                            # height the sub-panel carried before it was retired.
REAR_PANEL_OV       = 15.0  # panel overlap past the window, every side
REAR_PANEL_BOLT_OFF = 9.0   # bolt centres past the window edge (>=4 mm inside the
                            # panel edge at OV 15, and clear of every flange)
MASK_BOND_D         = 12.0  # bare bonding land around ONE panel bolt, both faces.
                            # The panel carries the TRS sleeves (which ARE board
                            # GND) and both USB coupler flanges, and it bolts to a
                            # powder-coated wall through four painted holes -- so
                            # without this it is a floating metal plate holding
                            # every shield in the machine. ONE land, not four:
                            # a single defined path, same rule as H1 on the board.

# --- ventilation / mounting ---------------------------------------------------
VENT_SLOT   = (40.0, 4.0)     # one louvre slot (l x w)
VENT_PITCH  = 8.0             # slot row pitch (web = pitch - slot = 4mm = 2T)
VENT_FREE_AREA_MIN = 4000.0   # mm^2 minimum open area (bottom + rear), ~40 cm^2
STANDOFF_H  = 15.0            # under-board gap: the THT leads + buck-module header pins
                              # hang ~4.5mm below the PCB, so 10mm left ~5mm of real
                              # airflow; 15mm (standard M3 brass) restores the margin
PI_STACK_MID = 9.7            # USB/RJ45 stack centreline above the Pi PCB BOTTOM
                              # (1.6 PCB + ~8.1 to the middle of the 16mm-tall stack);
                              # PI_RISER_H is derived from it below REAR_IO_Z
PI_HOLES    = (58.0, 49.0)    # Raspberry Pi 4/5 mounting-hole rectangle (M2.5)
# The board on this plate is the CONSOLE BOARD v2 (#747) -- the RP2350 board that
# carries the MIDI front end and a header for every rear-panel connector. It replaced
# the V1 THT board of the retired standalone pedal.
#
# These two numbers are NOT measured or copied. They are checked in _check() against
# hardware/kicad/out_console/console_board_mount.json, which the board generator
# writes -- the mirror of the rear_io_stations.json handoff going the other way. The
# plate spent a while drilling 85 x 87 for a board whose holes had moved to 89.5 x
# 89.5, and neither part had been ordered only by luck.
BOARD_HOLES = (89.5, 89.5)    # M3 mount rectangle (console board v2, 5 mm inset)
BOARD_SIZE  = (99.5, 99.5)    # board outline (for the 3D render + clearance gates)
BOARD_MOUNT_JSON = os.path.join(HERE, "..", "kicad", "out_console",
                                "console_board_mount.json")
# What actually stacks up at the Pi, bottom to top (#743):
#   plate -> STANDOFF_H -> N07 NVMe bottom board -> its SSD -> standoffs -> Pi PCB
#   -> the tallest thing on top (the USB-A double stack beats the Active Cooler).
# GeeekPi N07 (B0CWD266XR) is a BOTTOM board on an FPC: it costs height, not
# footprint. The official Active Cooler is ~10 above the PCB, so the USB-A stack
# still sets the number.
PI_N07_H    = 7.6             # what sits between the riser top and the Pi: the N07
                              # PCB (1.6) + the 6 mm male/female extender that
                              # threads into the riser through it
PI_TALLEST  = 16.0            # USB-A double stack above the Pi PCB
BOARD_STACK_H = 16.0          # PCB + the tallest thing on it (Pico 2 on its
                              # headers, JST shrouds). Same 16 the 3D render
                              # blocks it out at. #743 made this load-bearing:
                              # moving the Pi forward slid it OVER the board, so
                              # PI_RISER_H - (STANDOFF_H + this) is the only gap
                              # between them, and _check() holds it >= 3.
# --- rubber feet (issue #743) -------------------------------------------------
# Screw-on, M4 from inside the case. The head therefore lands on the plate's TOP
# face, so no fixing may sit under a pedestal -- the rings have to seat flat on
# that same face.
# At the old x=45 the two front fixings landed squarely under REC/PLAY and
# TRACK4, and the first fix was to relieve the ring floor and pocket the sled.
# Unnecessary: the front corners are CLEAR. The corner brackets are at the REAR
# (y 405..419), not the front, so the 24.6 mm margin outboard of the end tubs is
# free. Moving the fixings into it removes the interference instead of
# accommodating it -- and widens the stance from 756 to 817 mm as a bonus.
D_FOOT       = 4.5   # M4 clearance for the foot screw. The foot is a uxcell
                     # buffer foot, Ø18 (chassis face) x Ø15 (floor) x 5 tall,
                     # rubber with a metal washer insert; the screw is NOT
                     # supplied and goes DOWN from inside, so the head sits on
                     # the plate's top face -- hence the clear-of-every-pedestal
                     # rule below rather than a countersink, which a 2.0 mm
                     # plate cannot take without leaving a knife edge.
FOOT_INSET_X = 14.3  # from each side. Window is 8.2..20.4: bend relief (RI+T) +
                     # hole radius at the low end, tub edge 24.6 at the high end.
                     # _check() holds it inside that, and holds every fixing clear
                     # of every pedestal.
FOOT_INSET_Y = 45.0  # from front and rear

# --- fasteners ----------------------------------------------------------------
D_M3      = 3.2      # M3 clearance (Pi/board standoffs)
D_RIVET   = 3.3      # 3.2 mm (1/8") pop rivets: the usual 3.3 drill. Was D_M3 = 3.2,
                     # zero clearance on a rivet that also has to find its hole while
                     # the bracket sits tangent to the wall fillet (re-review 2026-09-04)
D_M2      = 2.4      # M2 clearance (external buck standoffs)
D_M4      = 4.3      # M4 clearance (bottom plate -> shell)
# The whole lid fixes with ONE screw SKU: M3 into hand-tapped Ø2.5 pilots (front
# lip AND rear lap seam -- user call 2026-08-18, no clinch nuts anywhere). Taps
# are cut AFTER powder-coat, so no thread masking is needed.
# --- powder-coat masking (annotation only; issue #396) ---
# The earth stud needs a bare land on both faces or the ring terminal bonds to paint.
MASK_GND_D = 20.0    # bare bonding land around the M6 earth stud
PEM_EDGE  = 8.0      # min centre-to-edge distance (named for the retired PEM
                     # scheme; KEPT as the seam-row solver input so the 9 hole
                     # stations stay exactly where every doc and model has them)
R_FILLET  = 3.0      # inside corner radius on rectangular cutouts

# ===========================================================================
# DERIVED GEOMETRY
# ===========================================================================

D           = FACE_RUN + TRANS_RUN + 2*T  # overall depth: +2T so the bottom plate
                                          # BD (= D-2T) = FACE_RUN+TRANS_RUN, i.e. the side
                                          # wall's rear edge spans TRANS_RUN at TRANS_ANGLE,
                                          # matching the transition flap exactly
# Profile A: the Top plate rises to the PEAK at its rear edge (H_REAR), then the angled
# transition DROPS from the peak down to the shorter Rear panel at the very back.
REAR_WALL_H = H_REAR - TRANS_DROP     # Rear panel height (reduced; below the peak)
REAR_IO_Z   = REAR_WALL_H / 2.0       # connector cluster centreline up the rear wall
# The Pi used to ride bespoke 35.3 mm risers, sized so its rear port stack centred
# in the old I/O window. #743 deleted the window, and moving the Pi under the 16"
# screen (see pi_mount) took away the second reason -- it no longer has to clear
# the main board either. So it drops to the SAME plain M2.5 standoffs the board
# uses: one fastener kind instead of two, a lower stack, and more air over it.
# The Pi does NOT ride the same 15 mm standoff as the board. Its stack is
# 12 mm standoff -> N07 NVMe board -> 6 mm male/female extender -> Pi, so the first
# standoff is 12 and the Pi PCB ends up 12 + 1.6 + 6 = 19.6 above the plate. It was
# tied to STANDOFF_H when the N07 was a guess; it is a bought part now.
PI_RISER_H  = 12.0
PI_STACK_H  = PI_RISER_H + PI_N07_H + 1.6 + PI_TALLEST   # plate -> tallest on the Pi
SLOPE_DROP  = H_REAR - H_FRONT
L_SLOPE     = math.hypot(FACE_RUN, SLOPE_DROP)            # Top-plate sloped length
SLOPE_ANGLE = math.degrees(math.atan2(SLOPE_DROP, FACE_RUN))
# Pedal slot depth ON THE SLOPE: horizontal envelope / cos(slope) (see pedal block).
FSW_SLOT_D = (PEDAL_D + FSW_SLOT_CLR_D) / math.cos(math.radians(SLOPE_ANGLE))
# Tub inner opening (see the pedal block): slot outline projected flat + setback.
SKIRT_IN_W = FSW_SLOT_W + 2*SKIRT_SETBACK                                    # 79.15
SKIRT_IN_D = FSW_SLOT_D * math.cos(math.radians(SLOPE_ANGLE)) + 2*SKIRT_SETBACK  # 113.67
TRANS_LEN   = math.hypot(TRANS_RUN, TRANS_DROP)          # transition facet length
TRANS_ANGLE = math.degrees(math.atan2(TRANS_DROP, TRANS_RUN))   # transition rake (from horizontal)

def bend_allowance(angle_deg, t=T, ri=RI, k=KF):
    return math.radians(angle_deg) * (ri + k * t)

BA90 = bend_allowance(90.0)

def dev_deduct(angle_deg):
    """Per-flap development deduction for a fold of the given rotation angle
    (exact K-factor development, bend line on the mold line, centre-line
    convention): flap flat = target outer length - dev_deduct(angle)."""
    a = math.radians(angle_deg)
    return (RI + T) * math.tan(a / 2.0) - bend_allowance(angle_deg) / 2.0

DEV90 = dev_deduct(90.0)              # = 1.911 for T2/RI2/K0.33 (issue #237: the old
                                      # T + K*T = 2.66 over-deducted every 90 deg bend
                                      # ~0.75mm, leaving all walls short of nominal)
# Front-lip screw HEIGHT on the flat pattern, shared by both encodings of the
# joint: the base's front wall (tap pilot, dxf_base._fscrew_flat) and the lid's
# front lip (clearance, dxf_faceplate). One tap, one screw SKU, one height --
# it centres the hole on the developed 9 mm front wall. Was written twice, once
# as (H_FRONT-bdd)*0.5 and once as (H_FRONT-DEV90)/2.0 (bdd == DEV90, so bit-
# identical); the assert pins it so the next H_FRONT change is a conscious one.
FRONT_SCREW_Z = (H_FRONT - DEV90) / 2.0
assert abs(FRONT_SCREW_Z - 5.045) <= 0.01, \
    f"FRONT_SCREW_Z {FRONT_SCREW_Z:.4f} drifted from the frozen 5.045 mm"
# The lap must STOP SHORT of the wall->flange bend knuckle: the flange's outer
# surface starts curving (RI+T)*tan(fold/2) = 2.58 before the outside mold
# corner, so the lap tip stops there plus a margin -- as LONG as possible while
# still lying flat on the flange.
KNUCKLE_CLEAR = 3.5
FP_W = W - 2.0 * T                    # control-area width (schedule coordinate frame)
LID_W = W - 0.2                       # lid blank full outer width: covers the wall tops,
                                      # flush with the side skins (issue #237)
LID_OX = (LID_W - FP_W) / 2.0         # schedule content offset inside the wider blank
FP_V = L_SLOPE                        # faceplate length up the slope (control area)

# --- rear-seam development solver (issue #237) --------------------------------
# Side view of the FOLDED part: Z = depth from the front wall OUTER face,
# Y = height above the bottom plate OUTER face. Every position is derived from
# the flats' own developed geometry (bend lines + dev_deduct), NOT from the
# idealized design polygon -- development shifts the real planes a couple of mm
# from the polygon, and the seam must close on the planes the flats actually
# produce.
_ra, _rth = math.radians(SLOPE_ANGLE), math.radians(TRANS_ANGLE)
DD_LIP = dev_deduct(90.0 - SLOPE_ANGLE)         # lid front-lip fold (77.5 deg)
DD_LAP = dev_deduct(SLOPE_ANGLE + TRANS_ANGLE)  # lid rear-lap fold (36.9 deg)
DD_TR  = dev_deduct(90.0 - TRANS_ANGLE)         # wall -> flange fold (65.6 deg)
_bd  = D - 2.0 * T                              # bottom plate flat depth (= BD)
# lid front mold corner (lip outer face x lid outer skin), lip hugging the wall.
#
# MEASURED 2026-08-21 (#775): "hugging" is literal -- in the folded assembly the
# lip's inner face and the front wall's outer face are COINCIDENT, lid<->base
# minimum distance 0.0000 mm at mid-wall height. Both are OUTSIDE faces, so both
# take powder coat (~0.06-0.10 mm each): the joint is ~0.16 mm interference
# before a single tolerance is counted, on the one seam that cannot be reworked
# once the part is finished.
#
# NOT fixed by moving this corner. _cfy sets the flange LENGTH, not its standoff
# (raising it just drops the lip tip below the base floor -- tried, reverted).
# The standoff would have to come from shifting the floor's front bend line,
# which re-bases every feature on the base flat, or from lengthening the lid
# plate, which moves all the faceplate content. Both are large ripples through a
# solver whose two halves currently agree to 15 decimals, for a 0.3 mm gap that
# press-brake tolerance (+/-0.5 deg over a 12.19 mm lip = +/-0.11 mm) swamps
# anyway. So this is specified as a FIT, not carried as a CAD dimension:
# LIP_FIT_CLEAR is the number the drawing asks the shop to hold, and the owner's
# call (2026-08-21) is a tight fit with everything coated -- no masking.
LIP_FIT_CLEAR = 0.3    # mm, lip inner face -> wall outer face, AFTER coating
_cfy = H_FRONT - T * math.tan(_ra) + T / math.cos(_ra)
_cfz = -DEV90 - T
# Front-lip flange: the lip TIP lands flush with the base's bottom face (z=0),
# covering the whole front -- wall, floor edge and all (user call 2026-08-18,
# #760; the old 9mm flange stopped ~3.2mm short). A flat point f past the bend
# line lands at station f + DD from the mold corner, so tip-at-zero needs
# flat = corner height - DD_LIP.
LID_FRONT_FL = _cfy - DD_LIP
_mtop   = FP_V + DD_LIP + DD_LAP                # lid top-plate mold length
RIDGE_Z = _cfz + _mtop * math.cos(_ra)          # lid rear mold corner (the ridge)
RIDGE_Y = _cfy + _mtop * math.sin(_ra)
_zw  = _bd + DEV90                              # rear wall OUTER plane depth
_y90 = RIDGE_Y - (_zw - RIDGE_Z) * math.tan(_rth)   # lap outer  x  wall outer
YC_TRANS = _y90 - T / math.cos(_rth)            # transition OUTSIDE mold corner: the
                                                # flange outer sits ONE SHEET below
                                                # the lap outer so the lap rests ON it
HR_FLAT = YC_TRANS - DEV90 - DD_TR              # rear wall web, developed flat
RIDGE_CLEAR = 2.0                               # flange tip stops this short of the
                                                # ridge mold corner (lap-bend zone)
# along-facet axis d: from the ridge mold corner DOWN the lap/flange facet.
# A point at flat distance f beyond a bend line lands at facet station f + DD
# from that bend's mold corner (the straight flap starts sb past the corner but
# only BA/2 past the line) -- so a target station d needs flat = d - DD.
D_WALL    = (_zw - RIDGE_Z) * math.cos(_rth) + (RIDGE_Y - YC_TRANS) * math.sin(_rth)
HT_FLAT   = (D_WALL - RIDGE_CLEAR) - DD_TR      # transition flange, developed flat:
                                                # as LONG as possible (to the ridge
                                                # clearance, NOT just TRANS_LEN --
                                                # development stretches the facet)
D_FL_TIP  = D_WALL - (HT_FLAT + DD_TR)          # flange tip (= RIDGE_CLEAR)
D_LAP_TIP = D_WALL - KNUCKLE_CLEAR              # lap tip: clear of the wall knuckle
# screw row: centred on the lap/flange overlap, pushed down-facet if needed to
# keep PEM_EDGE from the flange tip (solved for the retired PEM scheme; frozen --
# generous for a tapped hole, and every model carries these stations)
D_SEAM_SCREW = max((D_FL_TIP + D_LAP_TIP) / 2.0, D_FL_TIP + PEM_EDGE)
LID_REAR_LAP = D_LAP_TIP - DD_LAP               # lap developed flat length
LRL = LID_REAR_LAP
SEAM_LAP_V = LID_FRONT_FL + FP_V + (D_SEAM_SCREW - DD_LAP)     # lap screw row (lid flat v)
SEAM_TAP_V = HR_FLAT + (D_WALL - D_SEAM_SCREW) - DD_TR         # flange tap-pilot row (base
                                                               # flat, from the rear
                                                               # wall bend line)
# hard DFM guards: a parameter tweak must not silently collapse the lap/flange
# overlap or push the screw row off the lap (holes in air pass no other check)
assert HR_FLAT > 0 and LID_REAR_LAP > 0, "seam solver: degenerate rear seam"
assert D_FL_TIP + PEM_EDGE <= D_SEAM_SCREW <= D_LAP_TIP - (3.4 / 2.0 + 2.0), (
    f"seam screw row d={D_SEAM_SCREW:.2f} outside the lap/flange overlap "
    f"[{D_FL_TIP:.2f}, {D_LAP_TIP:.2f}] with edge margins")
assert HR_FLAT - BA90 / 2.0 > CORNER_HT + T + RI - DEV90 + 0.5, (
    "rear web too short: the corner bracket's TOP edge runs into the transition fold's bend zone")
assert HR_FLAT > max(CORNER_ZR_WALL) + T + RI + 2.0, (
    "rear web too short: corner-bracket rivet holes cross the transition fold")

def lid_top_z(v):
    """Z of the Top-plate surface at control-area depth v (0..FP_V).

    v is measured ALONG THE SLOPE, not in plan: FP_V == L_SLOPE (406.64), which is
    the faceplate's own length, not FACE_RUN (397). Rising a distance v along a
    plane inclined at SLOPE_ANGLE lifts you by v*sin -- so sin, not tan.

    This used to divide by FACE_RUN, i.e. treat an along-slope v as a horizontal
    run, overstating the height by v*(tan - sin) = 0.00525*v -- 0.36 mm at the
    front row, 1.42 mm at the mid row, 1.95 mm at the back of the 16in aperture
    (issue #742). face_drift's docstring already named the bug ("lid_top_z uses
    the tan-slope shortcut, the real plate follows sin") and a two-point fit was
    used to cancel it; see FACE_SEAT for why that fit collapses to a constant now.
    """
    return H_FRONT + min(v, L_SLOPE) * math.sin(math.radians(SLOPE_ANGLE))

def lid_under_z(v):
    """Z of the faceplate UNDERSIDE at depth v."""
    return lid_top_z(v) - T

# ===========================================================================
# CUTOUT SCHEDULE  (faceplate local: u=0..FP_W L->R = player's left->right,
#                   v=0..FP_V front->rear)
# ===========================================================================

# Two pedal rows, faithful to the reference: a FRONT row of 8 (4 transport |
# 4 tracks, with a centre gap) and an upper CENTRE pair (CLEAR/BANK). Each pedal
# is a whole Cherub WTB-006 on a printed pedestal; a status LED sits directly ABOVE each
# (aligned in u). CLEAR/BANK ride centre so the 16" screen still fits depth-wise.
EDGE         = 30.0      # uniform edge margin (sides / rear)
FRONT_PEDAL_MARGIN = 10.0 # front-row pedals sit this close to the front edge
LED_GAP      = 16.0      # status-LED offset behind a pedal (toward rear): pill
                         # centre above the slot's rear edge. 12.0 until 2026-09-04;
                         # 16 was tried in Fusion and CONFIRMED by the owner the
                         # same day -- the pill's bottom edge sits 13 mm behind
                         # the slot instead of 9. Everything downstream follows
                         # (legends, ring line, mini console); the support posts
                         # no longer care, see POST_PW.
SILK_H       = 25.0      # silkscreen cap height -- SAME for every label (a too-wide word
SILK_CW      = 0.66      # gets squished horizontally). bold char advance / cap height.
PEDAL_ROW1_V = FRONT_PEDAL_MARGIN + FSW_SLOT_D / 2.0   # front row pulled to the edge
# The platform stack (platform_foot_holes and everything on it) converts lid-v
# to plan as v*cos(SLOPE) -- but the DEVELOPED lid's content v=0 does NOT land
# at plan 0: the lip hugs the wall at -(DEV90+T) and the flat starts DD_LIP past
# the front mold corner (rear-seam solver, #237). Net: raw-v apertures cut
# ~2.6mm forward of where the floor actually puts the pedals, and the pedal rear
# edge fouls the slot. The slot cut ALONE carries the correction (#760): labels,
# LED pills, screens and the platform stack keep the frozen approved layout.
PEDAL_AP_DEV = (DEV90 + T) / math.cos(_ra) - DD_LIP
# The slot grows FORWARD only, back to the APPROVED front gap of 1.93mm: the
# pedal's front lip carries the case screws and needs that room, but on the
# sloped plate a bigger gap drops the slot's front rim BELOW the pedal floor
# (each mm of gap lowers the lip by tan(SLOPE)). At 1.93mm the floor sits
# +0.16mm on the lip -- visually flush, exactly the approved relation now that
# the pedal rides +RESEAT_CAL on the reseated plate. Rear clearance stays nominal. (#760)
# NOTE: this front-gap term is the SAME reseat concept, but frozen at 2-decimal
# 0.43, not RESEAT_CAL's 0.443. Folding it in would shift the slot's front rim
# ~0.013 mm and is a real geometry change -- out of scope for this zero-delta
# dedup. Reconcile 0.43 vs RESEAT_CAL in the #762 caliper batch, not here.
FSW_FRONT_EXTRA = 0.43 / math.cos(_ra)
# 7" screen, LED ring and encoder share ONE vertical centre-line (COL_U, defined
# with the pedal layout below): the gap between pedals 1 and 2.
# SCREEN_TOP_V is FROZEN at the value the console was built around (the screens,
# decals and the Fusion "Segno console (populated)" doc all embody it). When the
# pedal slot deepened for the Cherub WTB-006 (103 -> 112.87), the front gap
# absorbed the change instead of growing the console: FRONT_GAP is now DERIVED
# and asserted >= 40 in _check().
SCREEN_TOP_V = 371.0
FRONT_GAP    = SCREEN_TOP_V - BIG_H - (PEDAL_ROW1_V + FSW_SLOT_D / 2.0)
# SILK_CAP is the cap-height/em ratio of the label font as it actually renders
# (measured in the "Segno console (populated)" doc; Arial-class bold ~0.717): the
# silk `h` parameter is an em size, so glyph caps top out at v_lbl + SILK_H*SILK_CAP.
SILK_CAP     = 0.7168
# Play-triangle height as a fraction of SILK_H. Named because ROW1_LEGEND_TOP
# below depends on it: the triangle is the tallest glyph in row 1, so the ring
# placement moves if this changes. Don't inline it back into the glyph.
SILK_TRI_H   = 0.82
# Vertical offset of a pedal label above its slot, measured from the slot's rear
# edge. Pedals WITH a pill clear the pill first; pedals without one sit on the
# pill's BOTTOM LINE, so the whole row shares one baseline -- that line is what
# the eye follows across the row, and at the old 8.0 the plain labels floated
# 1 mm under it and the row read as two bands (owner call 2026-08-22).
#
# DERIVED, not a literal: the pill centre is LED_GAP above the slot and the pill
# is LED_SLOT_H tall, so its bottom edge is LED_GAP - LED_SLOT_H/2. Write 9.0
# here and it silently stops matching the moment either of those changes.
LABEL_DV_LED   = LED_GAP + 12.0
LABEL_DV_PLAIN = LED_GAP - LED_SLOT_H / 2.0
# CLEAR/BANK (row 2) are anchored on a HARD edge: the FRONT edge of their
# footswitch slot sits ON the 16" aperture's front edge, so the two pedals and
# the big screen share one bottom line (issue #796, owner call 2026-08-23; the
# #366 layout anchored the row off its label cap top, a soft glyph edge that
# lined up with nothing else on the plate). Both sides are cut edges in the same
# flat pattern, so this is an exact equality. The slot is NOT centred on the row
# -- faceplate_holes() opens it at v - FSW_SLOT_D/2 + PEDAL_AP_DEV -
# FSW_FRONT_EXTRA to meet the pedal across the fold development -- so those two
# terms come back out of the anchor here, or the alignment misses by ~2.15 mm.
PEDAL_ROW2_V = (SCREEN_TOP_V - BIG_H + FSW_SLOT_D / 2.0
                - PEDAL_AP_DEV + FSW_FRONT_EXTRA)
# The encoder + LED ring do NOT follow the pedals rearward: the ring would hit the
# 7" screen. It used to be pinned to the OLD row-2 centre (the 16"-screen-bottom
# line), which held while the ring was the Ring 16's O46 -- that left 26.7 mm of
# air under the 7" aperture. The Ring 24's O67 grew the radius by 10.5 mm and ate
# the gap down to 16.2 (12.2 to the diffuser's glue land), which is why the ring
# started reading as crowded up against the screen.
#
# So the ring is placed off the CLEARANCE now, not off a line that has nothing to
# do with it: the gap is the number that actually matters, it is stated once, and
# the ring re-places itself if RING_OD ever changes again.
# The rule is CENTRED, not clearance-from-one-side: the ring sits midway between
# the top of the row-1 legend band and the bottom of the 7" aperture, so the air
# above and below it is equal and stays equal when either bound moves. Hanging it
# off a single gap to the screen (what this was) leaves the other side to chance,
# and by eye it still sat high (owner call 2026-08-22).
#
# The band top is the play triangle's tip -- it is the tallest thing in row 1,
# taller than the cap height of UNDO/MODE, so it is what the eye reads as the
# edge of the legend band.
# ROW1_LEGEND_TOP / ENC_V are defined further down, once NO_LED_PEDALS and _ROW1
# exist -- the band top depends on WHICH label offset row 1 actually uses, and
# that is a function of the tuple. Writing LABEL_DV_PLAIN here was what made this
# go stale twice (see there).

# Front row of 8, EVENLY spaced across the faceplate (no 4+4 grouping).
_ROW1 = ["REC/PLAY", "STOP", "UNDO", "MODE", "TRACK1", "TRACK2", "TRACK3", "TRACK4"]
# Pedal centres are FROZEN at the layout the console was built around (originally
# EDGE + slot/2 .. FP_W - EDGE - slot/2 with the 78mm ASP-1 slot). Everything
# downstream hangs off these: COL_U (7" screen/ring/encoder), the 16" aperture
# centre, LED slots, LED-strip PCBs and the Fusion doc. The wider Cherub slot
# (79.35) just eats 0.675mm of the side margin instead of shifting all of that.
ROW1_U_FIRST = 69.0
ROW1_U_LAST  = 777.0
def _row1_u(i):
    """Evenly spaced across the faceplate (frozen span, see above)."""
    return ROW1_U_FIRST + (ROW1_U_LAST - ROW1_U_FIRST) * i / (len(_ROW1) - 1)

# Shared vertical centre-line for the LEFT control column (7" screen + LED ring +
# encoder): the gap between pedals 1 and 2, so the whole column sits above that gap.
COL_U = (_row1_u(0) + _row1_u(1)) / 2.0

# Centre-line of the 16" screen: over the four TRACK pedals (row-1 right group).
# Hoisted out of faceplate_holes() because the Pi now mounts under it (#743).
SCREEN_16_U = (_row1_u(4) + _row1_u(7)) / 2.0
# The rear I/O cluster (and so the window and the bolt-on panel) is centred on the
# 16" screen. Right-justifying it against EDGE put the panel 11 mm off that centre
# for no reason a player could see, and the panel is the one rear feature anyone
# looks at while plugging in.
REAR_IO_U = SCREEN_16_U

# CLEAR/BANK ride row 2, aligned in u with UNDO (i=2) and MODE (i=3).
PEDALS = [(_ROW1[i], _row1_u(i), PEDAL_ROW1_V) for i in range(8)] + [
    ("CLEAR", _row1_u(2), PEDAL_ROW2_V), ("BANK", _row1_u(3), PEDAL_ROW2_V)]

# Front-lip screws: ONE PER PEDAL GAP plus one OUTBOARD of each end pedal at the
# mirrored half-pitch (9 total; was 3 -- #760). The knuckle trim left the front
# wall 10.09 tall with the screw row at ~6.95, so each hole keeps only ~1.0mm of
# metal above its edge; spreading the lid load over every station cuts the
# per-screw pull ~3x. All 9 land clear of every foot-plate by construction.
# Shared by the lid lip and the front wall.
_FS_HP = (_row1_u(1) - _row1_u(0)) / 2.0
FRONT_SCREW_U = ([_row1_u(0) - _FS_HP]
                 + [(_row1_u(i) + _row1_u(i + 1)) / 2.0 for i in range(len(_ROW1) - 1)]
                 + [_row1_u(len(_ROW1) - 1) + _FS_HP])

# Status-LED pedals. #366 gave a pill to ALL ten; #792 then took the four
# TRANSPORT pills away again (fixed functions with nothing to report). Owner call
# 2026-08-28 REVERSES #792 and restores all ten (#930) -- so this tuple is empty,
# and it stays a tuple rather than being deleted because the argument has now gone
# both ways once and may again. Emptying it also moves those four labels from
# LABEL_DV_PLAIN to LABEL_DV_LED, which changes the plate AND the vinyl overlay.
NO_LED_PEDALS = ()

def _has_led(label):
    return label not in NO_LED_PEDALS

# Row 1's legend band top, and the encoder that is centred against it. The offset
# is READ OFF the pedals rather than written: a row-1 label sits at LABEL_DV_LED
# or LABEL_DV_PLAIN depending on NO_LED_PEDALS, and that tuple has now changed
# twice (#792 emptied row 1 of pills, #930 refilled it). Both times this line
# still said LABEL_DV_PLAIN while every row-1 label had moved, which left ENC_V
# 7.5 mm low and quietly broke the centred rule above -- the legends moved in the
# DXF and the ring did not.
_ROW1_LABEL_DV = max(LABEL_DV_LED if _has_led(lb) else LABEL_DV_PLAIN
                     for lb in _ROW1)
ROW1_LEGEND_TOP = (PEDAL_ROW1_V + FSW_SLOT_D / 2.0 + _ROW1_LABEL_DV
                   + SILK_H * (SILK_CAP / 2.0 + SILK_TRI_H / 2.0))
ENC_V        = (ROW1_LEGEND_TOP + (SCREEN_TOP_V - SMALL_H)) / 2.0

# Legends. Two transport controls read as SYMBOLS rather than words (owner call
# 2026-08-21): "REC/PLAY" was a two-line block eating the tallest label slot on
# the plate for what is one button, and a record dot beside a play triangle says
# it in a fraction of the space; STOP becomes the universal square. Symbols are
# emitted as GEOMETRY (see SILK_SYMBOLS / _silk_symbol_geometry), not glyphs --
# the legend is a printed vinyl overlay, and a filled shape is unambiguous where
# a font substitution on the vendor's RIP would not be.
SILK_SYMBOLS = {"REC/PLAY": "rec_play", "STOP": "stop"}
SILK_ICON_R  = 0.10   # fillet radius as a fraction of h -- play + stop (owner)


def _fillet_closed(pts, r, n=10):
    """Closed ring with a circular fillet of radius r at every vertex.

    Used for the play triangle and the stop square so they read as the same
    family of icons (rounded, not knife-cut). n is arc segments per corner.
    """
    pts = list(pts)
    m = len(pts)
    if m < 3 or r <= 0.0:
        return pts
    out = []
    for i in range(m):
        p0 = pts[(i - 1) % m]
        p1 = pts[i]
        p2 = pts[(i + 1) % m]
        v1 = (p0[0] - p1[0], p0[1] - p1[1])
        v2 = (p2[0] - p1[0], p2[1] - p1[1])
        l1 = math.hypot(*v1)
        l2 = math.hypot(*v2)
        if l1 < 1e-9 or l2 < 1e-9:
            out.append(p1)
            continue
        u1 = (v1[0] / l1, v1[1] / l1)
        u2 = (v2[0] / l2, v2[1] / l2)
        dot = max(-1.0, min(1.0, u1[0] * u2[0] + u1[1] * u2[1]))
        theta = math.acos(dot)
        if theta < 1e-6 or theta > math.pi - 1e-6:
            out.append(p1)
            continue
        trim = r / math.tan(theta / 2.0)
        trim = min(trim, l1 * 0.45, l2 * 0.45)
        rr = trim * math.tan(theta / 2.0)
        a = (p1[0] + u1[0] * trim, p1[1] + u1[1] * trim)
        b = (p1[0] + u2[0] * trim, p1[1] + u2[1] * trim)
        bis = (u1[0] + u2[0], u1[1] + u2[1])
        bl = math.hypot(*bis)
        if bl < 1e-9:
            out.append(p1)
            continue
        bis = (bis[0] / bl, bis[1] / bl)
        c = (p1[0] + bis[0] * (rr / math.sin(theta / 2.0)),
             p1[1] + bis[1] * (rr / math.sin(theta / 2.0)))
        a0 = math.atan2(a[1] - c[1], a[0] - c[0])
        a1 = math.atan2(b[1] - c[1], b[0] - c[0])
        # Interior angle is < 180, so the fillet is the minor arc (central
        # angle π-θ). The long way around bites a concave chunk out of the
        # corner -- that is how stop looked like a square with four bites.
        ccw = (a1 - a0) % (2.0 * math.pi)
        if ccw <= math.pi:
            sweep, sign = ccw, 1.0
        else:
            sweep, sign = (2.0 * math.pi - ccw), -1.0
        for j in range(n + 1):
            ang = a0 + sign * sweep * j / n
            out.append((c[0] + rr * math.cos(ang), c[1] + rr * math.sin(ang)))
    return out


def _silk_symbol_geometry(kind, u, v, h):
    """Filled legend symbols, returned as {"kind": "poly"/"disc"} entries in the
    ENGRAVE stream. u,v = centre; h = cap height, so a symbol sits on the same
    optical baseline as the word labels it replaces.

    rec_play: record DOT + play TRIANGLE, side by side, reading left to right in
              the order the one button cycles. Triangle corners are filleted
              (SILK_ICON_R) so they match the stop square.
    stop:     the universal filled square, drawn slightly smaller than h because
              a square reads visually larger than a circle of the same height.
              Corners filleted to the same SILK_ICON_R.
    """
    out = []
    if kind == "rec_play":
        d = h * 0.78                       # dot diameter
        tw, th = h * 0.72, h * SILK_TRI_H  # triangle width / height
        gap = h * 0.20                     # tighter than the old 0.34 -- the plus
        pw = h * 0.36                      # goes BETWEEN the two, and the group
        pt = h * 0.10                      # still has to fit inside the pedal
        # Fillet first, then scale the triangle back to `th` so the rounded
        # tips do not shrink it under the record dot (they read as one pair).
        tri = _fillet_closed([(0.0, -th / 2.0), (0.0, th / 2.0), (tw, 0.0)],
                             h * SILK_ICON_R)
        ys = [p[1] for p in tri]
        xs = [p[0] for p in tri]
        # Same bbox height as the dot. 1.16 overshot (play read larger);
        # unscaled after the fillet undershot (dot read larger).
        s = d / (max(ys) - min(ys))
        cx, cy0 = (min(xs) + max(xs)) / 2.0, (min(ys) + max(ys)) / 2.0
        tri = [(cx + s * (x - cx), s * (y - cy0)) for x, y in tri]
        tw = max(p[0] for p in tri) - min(p[0] for p in tri)
        total = d + gap + pw + gap + tw
        x0 = u - total / 2.0
        out.append({"kind": "disc", "u": x0 + d / 2.0, "v": v, "d": d})
        # The PLUS is deliberately smaller than the dot and the triangle: it is a
        # conjunction between them, not a third transport symbol competing with
        # them (owner call 2026-08-22). One 12-point cross, not two overlapping
        # bars -- the overlap would be a self-intersecting fill boundary.
        px = x0 + d + gap + pw / 2.0
        a, b = pw / 2.0, pt / 2.0
        out.append({"kind": "poly", "pts": [
            (px - b, v - a), (px + b, v - a), (px + b, v - b),
            (px + a, v - b), (px + a, v + b), (px + b, v + b),
            (px + b, v + a), (px - b, v + a), (px - b, v + b),
            (px - a, v + b), (px - a, v - b), (px - b, v - b)]})
        tx = x0 + d + gap + pw + gap - min(p[0] for p in tri)
        out.append({"kind": "poly",
                    "pts": [(x + tx, y + v) for x, y in tri]})
    elif kind == "stop":
        a = h * 0.70
        sq = [(u - a/2, v - a/2), (u + a/2, v - a/2),
              (u + a/2, v + a/2), (u - a/2, v + a/2)]
        out.append({"kind": "poly", "pts": _fillet_closed(sq, h * SILK_ICON_R)})
    else:
        raise ValueError("unknown silk symbol: %r" % (kind,))
    return out


def _silk_lines(label):
    if label in SILK_SYMBOLS:
        return []                 # drawn as geometry, not text
    if label.startswith("TRACK"):
        return []                 # tracks are identified by the meter screen, no silk text
    return [label]

def pedal_half_width(x):
    """Half the case width at depth x in the PEDESTAL frame (+X toward the case
    BACK). The WTB-006 tapers in PLAN as well as in height -- PEDAL_W at the back
    edge down to PEDAL_TOE_W at the toe -- so a clearance quoted off PEDAL_W is
    understated everywhere except the back edge."""
    t = (PEDAL_D/2.0 - x) / PEDAL_D          # 0 at the back edge, 1 at the toe
    return (PEDAL_W - t * (PEDAL_W - PEDAL_TOE_W)) / 2.0

def pedal_base_holes():
    """The four base screw holes in the PEDESTAL frame: X = depth with +X toward
    the case BACK (cable end), Y = width, origin at the pedal centre. Rear pair
    first. Anything that bolts a pedal down from below reads this."""
    return [(PEDAL_D/2.0 - back, side * span/2.0)
            for back, span in ((PEDAL_BASE_REAR_BACK, PEDAL_BASE_SPAN_REAR),
                               (PEDAL_BASE_FRONT_BACK, PEDAL_BASE_SPAN_FRONT))
            for side in (-1, 1)]

def platform_h(v):
    """Platform shelf height that lands the pedal's BODY TOP (case top, under the
    top pad) FLUSH with the faceplate surface at the slot's UPPER (rear) rim --
    pad above the metal (issue #373). The pedal sinks POCKET_DEPTH into the
    deck's locating pocket, so the deck compensates. face_drift closes the gap
    between the bare lid_top_z frame and the REAL plate seating (flush was still
    1.4 mm short at row 1 without it -- measured in the populated doc)."""
    v_rim = v + FSW_SLOT_D / 2.0
    return lid_top_z(v_rim) + face_drift(v_rim) + PEDAL_PAD_T - PEDAL_H + POCKET_DEPTH


def face_drift(_v=None):
    """Kept as a call so the intent stays greppable; the offset is CONSTANT now."""
    return FACE_SEAT

# ---------------------------------------------------------------------------
# FACEPLATE SUPPORT POSTS  (base-anchored props -- issue #292)
# ---------------------------------------------------------------------------
# The shop's STD aluminium is soft 1050 (yield ~105 vs 193 MPa for 5052). The
# faceplate's own perimeter folds already stiffen its edges (~70x at a fold line),
# so the pedal band (close to the front lip) is fine. The ONE zone the perimeter
# folds do NOT reach is the interior just in front of the big 16in aperture: bare
# 2 mm 1050 there dents at only ~11 kg (issue #292). Rather than a rib on the
# VISIBLE top face, TWO vertical posts rise from the base floor to just under that
# zone -- load runs faceplate -> post -> base -> floor. The posts anchor to the
# BASE only; the faceplate bears on their felt caps, so the lid still lifts off and
# NOTHING shows on the top face. Cut+bend only.
POST_V     = 165.0                 # web depth (user call 2026-08-19: "move the screws back, make the
                                   # posts taller"): the pad now sits 13mm in front of the 16in aperture
                                   # edge (178) -- the actual dent zone -- instead of jammed at 146.5
                                   # against the OLD panel's fictitious connector strip. Rear limit is
                                   # the UPERFECT body's bottom edge (~170.5 plan, PROVISIONAL, VESA
                                   # float +/-2.5); the intake vent field below yields instead (slots
                                   # under the feet are skipped, see _bottom_vents_local).
POST_U     = [625.0, 726.0]        # in the TRACK LED-slot GAPS (T2-T3 @625, T3-T4 @726) so the pad also
                                   # clears the LED slots; still under the 16in aperture, clear of the vent
POST_U_CLR = 1.5                   # u clearance, pad edge to the neighbouring pill
                                   # shoulder (LED_SLOT_W + 2*LED_INS_FLANGE), each side
POST_PW    = ((_row1_u(1) - _row1_u(0)) - LED_SLOT_W - 2*LED_INS_FLANGE
              - 2*POST_U_CLR)      # post width (u): 30.1, DERIVED so the pad sits
                                   # BETWEEN the two pill shoulders it lands among and
                                   # shares no u with either. At the old literal 40 it
                                   # overlapped each shoulder by ~3.7 mm in u, so the
                                   # shoulder-rear-vs-pad-front gate pinned LED_GAP to a
                                   # 0.09 mm window; decoupled, the pill depth is free
                                   # and the post stays where the dent zone wants it.
                                   # 30 mm on a 20 mm-deep web is still not the weak axis.
POST_PAD   = 20.0                  # top pad length (v) -- bears on the faceplate underside
POST_FOOTL = 20.0                  # foot flange length (v) -- bolts to the base floor
                                   # (briefly 17 while the post was wedged against the v375 platforms
                                   # at POST_V=146.5; restored to 20 when POST_V moved to 165 -- the
                                   # foot front now clears the platform rear wall by ~17 mm)
POST_FELT  = 1.0                   # ASSEMBLED metal gap: a thicker (2-3 mm) felt/foam cap on the
                                   # pad compresses into this ~1 mm when the lid seats -> preloaded,
                                   # firm, rattle-free contact without jacking the lid.
POST_TILT  = SLOPE_ANGLE           # pad tilt (deg) so it beds FLUSH on the sloped faceplate underside
POST_BOLT_DU = POST_PW / 2.0 - 5.0 # M4 foot bolts at +/- this in u: 5.0 in from the foot's
                                   # side edge (2.85 mm of web past the O4.3, an M4 head
                                   # inside the foot). Was a literal 12 for the 40 mm post;
                                   # the base anchors derive from it, so both move together
# The shell is soft 1050 aluminium, but the posts are made in STEEL 1.6 mm: ~3x stiffer
# (E 200 vs 69 GPa), tougher, and only ~+60 g for the pair -- rigidity where it costs no
# weight (issue #292). Felt cap isolates the steel pad from the soft-Al faceplate.
POST_T     = 1.6                   # post sheet thickness (cold-rolled steel), NOT the shell's 2.0 Al
# foot + pad both extend FORWARD of the web (a C, all in the clear strip in front of the
# aperture); nothing sits under the display.
# web height: derived from the MEASURED faceplate-underside plane of "Segno
# console (populated)" (the MANUFACTURING source of truth) -- the same plane
# build_screen16_stand_steps seats the monitor deck against:
#   z_underside(y_world) = 12.437 + tan(SLOPE)*y_world   (above the base floor TOP)
#   y_world              = cos(SLOPE)*v_plan - 2.093
# The pad TOP (hinge line, at web top + pad-sheet POST_T) sits POST_FELT below
# that plane; the foot rests ON the base floor top, and build_post_step() measures
# the web from that same face -- so the bottom-plate T is already inside the datum
# and must NOT be subtracted again (the old stack subtracted it because lid_top_z
# is referenced to the floor's OUTER face). Earlier revisions stacked
# lid_top_z(POST_V) - POST_FACEDRIFT + POST_DOC_CAL instead: a constant-drift
# model that needed a fresh SINGLE-POINT doc probe at every POST_V move (the
# 1.5+0.443 FACE_SEAT-style drift, then a 3.85 mm patch at v=165). The plane
# derivation RETIRES both constants (#767): it reproduces the v=165 doc probe
# to 0.026 mm and generalizes to any POST_V.
_POST_Y_WORLD = math.cos(math.radians(SLOPE_ANGLE)) * POST_V - 2.093
_POST_UNDER_Z = 12.437 + math.tan(math.radians(SLOPE_ANGLE)) * _POST_Y_WORLD
POST_H     = _POST_UNDER_Z - POST_T - POST_FELT
POST_RI = POST_T                   # inside radius for the 1.6 mm steel post (= T, as its sheet says)

def post_deduct(angle_deg):
    """Per-flap development deduction for the STEEL post (its own T/Ri, same
    K): flap flat = outer length - post_deduct(rotation). Until 2026-09-04 the
    post flat was nominal segments with NO deduction (the sheet said so), which
    would have folded ~1.5 mm taller per bend and eaten the felt's 1 mm."""
    a = math.radians(angle_deg)
    return (POST_RI + POST_T) * math.tan(a / 2.0) - a * (POST_RI + KF * POST_T) / 2.0

POST_DD_PAD  = post_deduct(90.0 + POST_TILT)   # apoyo -> alma, 102.5 deg
POST_DD_FOOT = post_deduct(90.0)               # alma -> pie
# OUTER mold-line lengths of the folded C, read off build_post_step's solid:
# the foot runs from its free end to the web's OUTER (rear) face = foot + t;
# the web from the floor to where the tilted pad's TOP face meets the web's
# rear plane = POST_H + t*tan(theta/2); the pad from that point to its free
# end = pad + t*tan(theta/2). Deducting from the nominal legs (re-review
# 2026-09-04) folded the post 2 mm short and left the felt unloaded.
_POST_TP     = POST_T * math.tan(math.radians(90.0 + POST_TILT) / 2.0)
POST_FOOT_OUT = POST_FOOTL + POST_T
POST_WEB_OUT  = POST_H + _POST_TP
POST_PAD_OUT  = POST_PAD + _POST_TP
POST_PAD_F   = POST_PAD_OUT - POST_DD_PAD                   # flat flap lengths, from the bend centre lines
POST_WEB_F   = POST_WEB_OUT - POST_DD_PAD - POST_DD_FOOT
POST_FOOT_F  = POST_FOOT_OUT - POST_DD_FOOT
# PIN to the doc probe: at POST_V=165 the populated doc gave web 45.107 mm at
# exactly the 1.0 mm felt gap (2026-08-19). This pin moves ONLY with a fresh
# doc probe -- if it trips, the plane model and the doc have drifted apart;
# re-probe the doc before cutting posts.
assert abs(POST_H - 45.107) <= 0.05, (
    f"POST_H {POST_H:.3f} drifted from the doc-probed 45.107 +/- 0.05 -- "
    "re-probe the populated doc before cutting posts")
_POST_VP   = POST_V * math.cos(math.radians(SLOPE_ANGLE))   # projected web depth on the flat base
_POST_FOOT_VP = _POST_VP - POST_FOOTL/2.0                   # foot-bolt depth (forward of the web)

def faceplate_holes():
    """All faceplate features. Pedal slots have NO mounting holes (the pedals
    stand on internal printed platforms). u=player L->R, v=front->rear."""
    cuts, engr = [], []
    # --- 10 pedal slots (two rows); a status LED pill above EVERY pedal --------
    for label, u, v in PEDALS:
        cuts.append({"kind": "rect", "u": u - FSW_SLOT_W/2,
                     "v": v - FSW_SLOT_D/2 + PEDAL_AP_DEV - FSW_FRONT_EXTRA,  # development offset:
                     "w": FSW_SLOT_W, "h": FSW_SLOT_D + FSW_FRONT_EXTRA,        # meet the pedals where the
                     "r": 0.0, "ref": label})                                   # floor puts them (#760)
        led = _has_led(label)   # (slot cutouts below replace the old per-pedal LED holes;
                                #  the flag still sets the label offset, unchanged)
        # silkscreen label ABOVE the pedal (rear side); every line is drawn at
        # EXACTLY the pill width (LED_SLOT_W) so labels and LED pills read as one
        # family of bars: common cap height, width factor forces the advance.
        lines = _silk_lines(label)
        if label in SILK_SYMBOLS:                      # transport symbol, drawn as geometry
            v_sym = v + FSW_SLOT_D/2 + (LABEL_DV_LED if led else LABEL_DV_PLAIN) + SILK_H*SILK_CAP/2.0
            engr.extend(_silk_symbol_geometry(SILK_SYMBOLS[label], u, v_sym, SILK_H))
            continue
        if not lines:                                  # tracks carry no silk text
            continue
        v_lbl = v + FSW_SLOT_D/2 + (LABEL_DV_LED if led else LABEL_DV_PLAIN)
        infos = []                                     # (text, width-factor, displayed width)
        for ln in lines:
            est_w = SILK_H * len(ln) * SILK_CW         # natural width at the common height
            infos.append((ln, LED_SLOT_W / est_w, LED_SLOT_W))
        left_x = u - max(d for _, _, d in infos) / 2.0   # multiline: flush-left, block centred
        for k, (ln, wf, disp_w) in enumerate(infos):
            vpos = v_lbl + (len(lines)-1-k)*(SILK_H*0.95)   # tight 2-line stack (issue #366)
            if len(lines) > 1:                         # multiline (REC/PLAY) -> left-aligned
                engr.append({"u": left_x, "v": vpos, "h": SILK_H, "s": ln, "wf": wf, "halign": "left"})
            else:                                      # single line -> centred on the pedal
                engr.append({"u": u, "v": vpos, "h": SILK_H, "s": ln, "wf": wf, "halign": "center"})
    # --- LED diffuser slots: ONE pill window per pedal, on the old status-LED
    #     centre-line. Behind each is a white-PLA diffuser pushed in from inside,
    #     with an LED_STRIP_N-LED segment of bare 144/m strip snapped into its
    #     back (#927/#930 -- not the VHB-taped single-LED board this used to say).
    #     Full-round ends: corner r = LED_SLOT_H/2.
    for label, u, v in PEDALS:
        if not _has_led(label):
            continue
        vc = v + FSW_SLOT_D/2 + LED_GAP              # same centre-line the LED holes used
        cuts.append({"kind": "rect", "u": u - LED_SLOT_W/2, "v": vc - LED_SLOT_H/2,
                     "w": LED_SLOT_W, "h": LED_SLOT_H, "r": LED_SLOT_H/2,
                     "ref": label + "_LEDSLOT"})
    # --- screens: top edges aligned on SCREEN_TOP_V ------------------------
    cuts.append({"kind": "rect", "u": COL_U - SMALL_W/2.0, "v": SCREEN_TOP_V - SMALL_H, "w": SMALL_W, "h": SMALL_H, "ref": "SCREEN_7IN"})
    s16_uc = SCREEN_16_U                        # centre over the 4 track pedals (row-1 right group)
    cuts.append({"kind": "rect", "u": s16_uc - BIG_W/2.0, "v": SCREEN_TOP_V - BIG_H, "w": BIG_W, "h": BIG_H, "ref": "SCREEN_16IN"})
    # --- encoder + diffused ring: on the OLD row-2 centre line (ENC_V -- it does
    #     NOT follow CLEAR/BANK rearward, see the PEDAL_ROW2_V note), and on
    #     COL_U -- the SAME vertical centre-line as the 7" screen (pedal 1/2 gap) -
    enc_v = ENC_V
    enc_u = COL_U                        # shared left-column centre-line (7" screen + ring)
    cuts.append({"kind": "ring",   "u": enc_u, "v": enc_v, "od": RING_OD, "id": RING_ID, "ref": "RING"})
    cuts.append({"kind": "circle", "u": enc_u, "v": enc_v, "d": D_ENC, "ref": "ENCODER"})
    # NOTE: no LEDs flank the encoder -- like the reference, the ring stands alone.
    # There is NO power indicator anywhere on this machine (#743): the rear
    # button is deliberately unlit, and two lit screens say "on" from the side
    # the player actually stands on.
    # The lid bolts to the body through its DOWN-TURNED SKIRT FLANGES (front lip +
    # sides + rear), NOT through this top face -- those screw holes live on the
    # flanges, added in dxf_faceplate / the render. So nothing more on the top here.
    # NOTE: the faceplate is reinforced by base-anchored SUPPORT POSTS (issue #292)
    # that bear on the underside -- they add NO holes here, keeping the top face clean.
    return cuts, engr

# Rear I/O stations, LEFT to RIGHT along the wall, with the KEEP-OUT width each
# one needs -- the nut, bezel or flange a fitter has to get a spanner around, NOT
# the hole. That distinction matters for the USB 3.0 coupler, whose flange (28.5)
# is 6.4 wider than its own 22.1 cutout; spacing on cutouts alone would have the
# two couplers' flanges fouling each other.
REAR_IO_STATIONS = [
    ("PD_IN",    D_TRS_KEEPOUT),                         # power first, at the far
    ("POWER",    PWRBTN_HEAD_D + 4.0),                   # left, away from signal.
                                                         # Sized off the HEAD, not the
                                                         # hole -- the head is what
                                                         # has to clear its neighbour
    ("FUSE",     D_FUSE + 6.0),                          # screw cap + a spanner
    ("MIDI_IN",  MIDI_SCREW_PITCH + 2*MIDI_SCREW_D),     # DIN-5 fixings set the
    ("MIDI_OUT", MIDI_SCREW_PITCH + 2*MIDI_SCREW_D),     # width, not the bore
    ("CTRL_1",   D_TRS_KEEPOUT),                         # D-series: the M3 pair is
    ("CTRL_2",   D_TRS_KEEPOUT),                         # wider than the Ø24 bore
    ("USB3_1",   USB3_FLANGE_D),
    ("USB3_2",   USB3_FLANGE_D),
]

def rear_io_layout():
    """Centre u of every connector station, spread across REAR_IO_SPAN with EQUAL
    clear gaps between keep-outs (not equal centres -- the stations are different
    widths). Returns {ref: (centre_u, keepout_w)}."""
    total = sum(w for _r, w in REAR_IO_STATIONS)
    gap = (REAR_IO_SPAN - total) / (len(REAR_IO_STATIONS) - 1)
    out, x = {}, REAR_IO_U - REAR_IO_SPAN/2.0
    for ref, w in REAR_IO_STATIONS:
        out[ref] = (x + w/2.0, w)
        x += w + gap
    return out

def rear_io_cutouts():
    """The nine panel-mount connector cutouts, in WALL coords (u=0..W, z=0..REAR_WALL_H).

    They are cut in the bolt-on sub-panel, not in the wall -- but they are laid out
    against the wall's own u so the panel, the window and the wall all agree without
    anyone converting coordinates by hand. rear_panel_holes() shifts them to
    panel-local; nothing else re-derives them."""
    z = REAR_IO_Z
    at = rear_io_layout()
    cuts = []
    for ref, d in (("POWER", D_PWRBTN), ("FUSE", D_FUSE)):     # nut-mounted: bore only
        cuts.append({"kind": "circle", "u": at[ref][0], "v": z, "d": d, "ref": ref})
    # DIN-5 stations: a bore with a HORIZONTAL M3 pair straddling it (the panel
    # is 46 tall; across the panel there is room to spare).
    for ref in ("MIDI_IN", "MIDI_OUT"):
        cu = at[ref][0]
        cuts.append({"kind": "circle", "u": cu, "v": z, "d": MIDI_BODY_D, "ref": ref})
        for s in (-1, 1):
            cuts.append({"kind": "circle", "u": cu + s*MIDI_SCREW_PITCH/2.0, "v": z,
                         "d": MIDI_SCREW_D, "ref": ref + "_SCR"})
    # D-series stations (both TRS jacks AND the PD coupler -- same D shell): the
    # Ø24 bore plus the DIAGONAL M3 pair, 19 across x 24 vertical (see
    # D_TRS_SCREW_DIAG provenance). One diagonal fits every D shell: the flange
    # is point-symmetric about the bore, so an opposite-diagonal part mounts by
    # turning it 180 deg.
    ddu, ddz = D_TRS_SCREW_DIAG
    for ref in ("PD_IN",):
        cu = at[ref][0]
        cuts.append({"kind": "circle", "u": cu, "v": z, "d": D_TRS_BORE, "ref": ref})
        for s in (-1, 1):
            cuts.append({"kind": "circle", "u": cu + s*ddu/2.0, "v": z - s*ddz/2.0,
                         "d": D_TRS_SCREW_D, "ref": ref + "_SCR"})
    # CTRL jacks: Neutrik NJ6FD-V, one round Ø12 hole each, no fixings (rear
    # body + front snap cap, see D_CTRL_HOLE)
    for ref in ("CTRL_1", "CTRL_2"):
        cuts.append({"kind": "circle", "u": at[ref][0], "v": z, "d": D_CTRL_HOLE, "ref": ref})
    for ref in ("USB3_1", "USB3_2"):                       # square, heavily radiused
        cu = at[ref][0]
        cuts.append({"kind": "rect", "u": cu - USB3_CUT_SQ/2.0, "v": z - USB3_CUT_SQ/2.0,
                     "w": USB3_CUT_SQ, "h": USB3_CUT_SQ, "r": USB3_CORNER_R, "ref": ref})
    return cuts

def _feat_extent(f):
    """(u_lo, u_hi, z_lo, z_hi) of one cutout feature."""
    if f["kind"] == "circle":
        r = f["d"] / 2.0
        return (f["u"] - r, f["u"] + r, f["v"] - r, f["v"] + r)
    return (f["u"], f["u"] + f["w"], f["v"], f["v"] + f["h"])

def rear_window():
    """The I/O WINDOW in the rear wall: (u_lo, z_lo, w, h).

    Derived from the cutouts it has to pass, not typed. The window used to be a
    290x46 constant while the cluster it framed was laid out by rear_io_layout(),
    so the two could drift apart silently -- and did, when the cluster moved right
    to follow the boards (#743). Now the wall opening is whatever the connectors
    need plus REAR_WIN_CLR, and a station that grows drags the window with it."""
    ext = [_feat_extent(f) for f in rear_io_cutouts()]
    # u: the opening must pass the station KEEP-OUTS (flanges, nuts), not just the
    # holes -- the panel mounts from the inside, so every connector's widest part
    # crosses the window plane. See REAR_WIN_SIDE_CLR.
    lay = rear_io_layout()
    u_lo = min(cu - kw/2.0 for cu, kw in lay.values()) - REAR_WIN_SIDE_CLR
    u_hi = max(cu + kw/2.0 for cu, kw in lay.values()) + REAR_WIN_SIDE_CLR
    z_lo = min(e[2] for e in ext) - REAR_WIN_CLR
    z_hi = max(e[3] for e in ext) + REAR_WIN_CLR
    if z_hi - z_lo < REAR_WIN_H_MIN:            # open it up about the cluster centreline
        z_mid = (z_lo + z_hi) / 2.0
        z_lo, z_hi = z_mid - REAR_WIN_H_MIN/2.0, z_mid + REAR_WIN_H_MIN/2.0
    return (u_lo, z_lo, u_hi - u_lo, z_hi - z_lo)

def rear_panel_bolts():
    """Bolt centres (u, z) in WALL coords -- drilled in the wall AND the panel from
    this one list, so they cannot disagree."""
    u0, z0, w, h = rear_window()
    cu, cz = u0 + w/2.0, z0 + h/2.0
    return [(cu + su*(w/2.0 + REAR_PANEL_BOLT_OFF), cz + sz*(h/2.0 + REAR_PANEL_BOLT_OFF))
            for su in (-1, 1) for sz in (-1, 1)]

def rear_panel_outline():
    """Panel blank (u_lo, z_lo, w, h) in WALL coords: the window plus an overlap wide
    enough that the bolts clear its edge."""
    u0, z0, w, h = rear_window()
    return (u0 - REAR_PANEL_OV, z0 - REAR_PANEL_OV, w + 2*REAR_PANEL_OV, h + 2*REAR_PANEL_OV)

def rear_panel_holes():
    """Sub-panel features in PANEL-LOCAL coords (origin = panel centre)."""
    u0, z0, w, h = rear_panel_outline()
    cu, cz = u0 + w/2.0, z0 + h/2.0
    out = []
    for f in rear_io_cutouts():
        g = dict(f)
        g["u"] = f["u"] - cu
        g["v"] = f["v"] - cz
        out.append(g)
    _bond = rear_panel_bolts()[0]
    for bu, bz in rear_panel_bolts():
        out.append({"kind": "circle", "u": bu - cu, "v": bz - cz, "d": D_M3,
                    "ref": "PANEL_BOLT"})
        if (bu, bz) == _bond:
            out.append({"kind": "circle", "u": bu - cu, "v": bz - cz,
                        "d": MASK_BOND_D, "ref": "PANEL_BOND", "layer": "MASK"})
    return out

def rear_holes():
    """Rear WALL features: the I/O WINDOW and its four bolt holes, the fixed exhaust
    vents and the earth stud. The connectors themselves are NOT here -- they are in
    the bolt-on sub-panel (segno_rear_panel), so the whole connector loom lifts out
    as one assembly instead of being trapped in a folded face of the base.
    u=0..W, z=0..REAR_WALL_H."""
    u0, z0, w, h = rear_window()
    cuts = [{"kind": "rect", "u": u0, "v": z0, "w": w, "h": h, "ref": "IO_WINDOW"}]
    _bond = rear_panel_bolts()[0]                          # the one nearest the stud
    for bu, bz in rear_panel_bolts():
        cuts.append({"kind": "circle", "u": bu, "v": bz, "d": D_M3, "ref": "PANEL_BOLT"})
        if (bu, bz) == _bond:
            cuts.append({"kind": "circle", "u": bu, "v": bz, "d": MASK_BOND_D,
                         "ref": "PANEL_BOND", "layer": "MASK"})
    # Vents fill the wall to the LEFT of the panel: the wall's EDGE margin to the
    # panel's left edge - EDGE, columns evenly pitched to land exactly on both.
    # (Mirror of the original rule, which had them to the RIGHT -- they swapped when
    # the cluster moved right to follow the boards.)
    sl = VENT_SLOT[0]
    cl_l = rear_panel_outline()[0]                         # panel LEFT edge
    v_l = EDGE                                             # first vent column
    v_r = cl_l - EDGE                                      # last column's right edge
    ncol = max(2, round((v_r - v_l - sl) / (sl + 8.0)) + 1)
    cp = (v_r - v_l - sl) / (ncol - 1)
    cuts.append({"kind": "circle", "u": (v_r + cl_l)/2.0, "v": REAR_WALL_H/2.0,
                 "d": D_GND, "ref": "EARTH_STUD"})         # centred in that gap
    vr = 7                                                 # rows, centred on mid-height
    vz0 = REAR_WALL_H/2.0 - ((vr-1)*VENT_PITCH + VENT_SLOT[1])/2.0
    cuts += _vent_array(u0=v_l, z0=vz0, cols=ncol, rows=vr, cp=cp)
    return cuts

def _vent_array(u0, z0, cols, rows, cp=None):
    """A block of louvre slots in BRICK BOND; returns rect features on the VENT
    layer. cp = column pitch. Odd rows are phase-shifted half a period like
    running bond (user call, 2026-08-18) and their edge slots clip to the same
    envelope as the even rows, so the block keeps its rectangular outline. The
    stagger keeps every web the same size while breaking the continuous cut
    lines of an aligned grid -- better looking AND stiffer."""
    sl, sw = VENT_SLOT
    if cp is None:
        cp = sl + 8.0
    u_hi = u0 + (cols - 1) * cp + sl                       # block envelope, right edge
    min_sl = sl * 0.3                                      # drop stubs, keep half-bricks
    out = []
    for r in range(rows):
        phase = cp / 2.0 if r % 2 else 0.0
        u = u0 + phase - cp                                # a period early: clipped heads
        while u < u_hi:
            lo, hi = max(u, u0), min(u + sl, u_hi)
            if hi - lo >= min_sl:
                out.append({"kind": "rect", "u": lo, "v": z0 + r * VENT_PITCH,
                            "w": hi - lo, "h": sw, "ref": "VENT", "layer": "VENT"})
            u += cp
    return out

def _vent_free_area(feats):
    sl, sw = VENT_SLOT
    return sum(f["w"] * f["h"] for f in feats if f.get("ref") == "VENT")

# ===========================================================================
# ASSERTION SUITE — the real acceptance gate (raises on bad geometry)
# ===========================================================================

def _bbox(f):
    """(umin, vmin, umax, vmax) of a faceplate feature in schedule coords."""
    if f["kind"] == "rect":
        return (f["u"], f["v"], f["u"] + f["w"], f["v"] + f["h"])
    r = (f["od"] if f["kind"] == "ring" else f["d"]) / 2.0
    return (f["u"] - r, f["v"] - r, f["u"] + r, f["v"] + r)

def _overlap(a, b, clr=2.0):
    return not (a[2] + clr <= b[0] or b[2] + clr <= a[0] or
                a[3] + clr <= b[1] or b[3] + clr <= a[1])
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
