tomassasovsky/segno/packages/segno_engine/src/core/segno_engine_api.h

/*
 * segno_engine_api.h — the C ABI exposed to Dart via FFI.
 *
 * This is the single header consumed by ffigen. Everything here is POD or an
 * opaque handle; no C++; no callbacks into Dart. The audio callback that backs
 * this API performs no allocation, locking, or I/O (see engine.c).
 *
 * Scope: device lifecycle, per-input live monitoring, level metering, a loopback
 * round-trip latency harness, the lock-free command ring, and a multi-track,
 * multi-lane looper. Each track owns up to LE_MAX_LANES lanes; a lane records
 * one hardware input into its own clean mono buffer (never merged with sibling
 * lanes) with per-lane routing / volume / mute / effects, while the track owns
 * the shared transport (record / master-loop length / overdub / loop playback /
 * loop multiples / clear) and one undo span across all its lanes.
 */
#ifndef SEGNO_ENGINE_API_H
#define SEGNO_ENGINE_API_H

#include <stdint.h>

/* Maximum number of hardware input/output channels the engine opens and routes.
 * Per-track buffers are mono; tracks record from one input channel and play to
 * any subset of the output channels (see le_track_snapshot.output_mask). */
#define LE_MAX_CHANNELS 32

#ifdef __cplusplus
extern "C" {
#endif

#if defined(_WIN32)
#define LE_EXPORT __declspec(dllexport)
#else
#define LE_EXPORT __attribute__((visibility("default"))) __attribute__((used))
#endif

/* Result codes returned by lifecycle calls. */
typedef enum le_result {
  LE_OK = 0,
  LE_ERR_INVALID = -1,       /* null handle or bad argument */
  LE_ERR_ALREADY_RUNNING = -2,
  LE_ERR_NOT_RUNNING = -3,
  LE_ERR_DEVICE = -4,        /* miniaudio failed to init/start the device */
  LE_ERR_UNSUPPORTED = -5,   /* a plugin's bus topology is not a stereo (or
                              * mono-adaptable) effect — instrument / multi-bus /
                              * sidechain / wrong channel count (D-BUS); an
                              * audio file outside the decoder's whitelist
                              * (#1200) */
  LE_ERR_CAPACITY = -6,      /* a requested allocation would exceed engine
                              * capacity (A6, D17): N bars of the current
                              * signature at the slowest possible tempo (30
                              * BPM) would not fit in max_loop_frames */
  LE_ERR_MODE_MISMATCH = -7, /* history would not fit the current mode/clock */
  LE_ERR_NOT_READY = -8,     /* a pending command/report prevents a safe decision */
  LE_ERR_REVERSED = -9,      /* a punch-in on a reversed track (#1162): overdub
                              * is unavailable while Reverse is on */
  LE_ERR_TRANSFORMED = -10,  /* a record or overdub while Speed is not 1x,
                              * or a punch-in on a transposed track or one
                              * playing at another span than its take's
                              * (#1179): capture never writes under playback
                              * it does not hear */
  /* -11 belongs to pitch/time (#1179); -12 and -13 to the backing
   * player (#1200); -14 and -15 to instruments (#1197; the numbering
   * ledger). */
  LE_ERR_TOO_LONG = -12, /* a backing file over LE_BACKING_MAX_SECONDS (#1200) */
  LE_ERR_NO_INSTRUMENT = -14, /* a note for an instrument slot with no patch
                               * (#1197); returned only by the single-event
                               * API, never by a batch */
  LE_ERR_UNKNOWN_PATCH = -15, /* a patch index this build does not define */
  LE_ERR_NO_COMMON_CYCLE = -16, /* render recipe (#1202): the selected tracks'
                                 * lengths share no common cycle within the
                                 * cap; a chosen length is required */
  LE_ERR_TRACKS_CHANGED = -17,  /* render recipe (#1202): a source's material
                                 * changed after the render froze it */
  LE_ERR_NOT_FOUND = -18,    /* the file (or a directory on its path) does not
                              * exist (#1198) */
  LE_ERR_TRUNCATED = -19,    /* the file exists but is shorter than the range
                              * it must hold (#1198) */
  LE_ERR_EXTERNAL_CLOCK = -20, /* tempo is owned by an external MIDI clock
                                * source (#1228); select Internal first */
  LE_ERR_SYNC_LOCKED = -21,    /* the clock source cannot change while a track
                                * records, overdubs, is armed or counting in */
} le_result;

/* Latency-harness phase, mirrored in le_snapshot.latency_state. */
typedef enum le_latency_state {
  LE_LATENCY_IDLE = 0,
  LE_LATENCY_MEASURING = 1, /* impulse emitted, waiting for it to return */
  LE_LATENCY_DONE = 2,      /* measured_latency_ms is valid */
  LE_LATENCY_TIMEOUT = 3,   /* no loopback detected within the window */
} le_latency_state;

/* Per-track state machine, mirrored in le_snapshot.track_state. */
typedef enum le_track_state {
  LE_TRACK_EMPTY = 0,
  LE_TRACK_RECORDING = 1,    /* capturing the first pass (defines the loop) */
  LE_TRACK_OVERDUBBING = 2,  /* summing input into the existing loop */
  LE_TRACK_PLAYING = 3,
  LE_TRACK_STOPPED = 4,      /* buffer retained, playback halted */
} le_track_state;

/* Where the current tempo came from, mirrored in le_snapshot.tempo_source
 * (D7 precedence). MANUAL and TAPPED are last-writer-wins; DERIVED is set only
 * when a defining loop finalizes with sync on and the source was NONE (a set
 * tempo is never re-derived); EXTERNAL is reserved for the Phase E MIDI-clock
 * follower (#1228): written once per beat while an external clock source is
 * selected and the tempo is not locked. A DERIVED tempo survives clearing the loop that
 * produced it (the "dead tempo" lesson): only an explicit reset returns the
 * source to NONE. */
typedef enum le_tempo_source {
  LE_TEMPO_SOURCE_NONE = 0,     /* no tempo set; tempo_bpm reads 0 */
  LE_TEMPO_SOURCE_MANUAL = 1,   /* LE_CMD_SET_TEMPO */
  LE_TEMPO_SOURCE_TAPPED = 2,   /* LE_CMD_TAP_TEMPO */
  LE_TEMPO_SOURCE_DERIVED = 3,  /* derived from a defining loop (D7) */
  LE_TEMPO_SOURCE_EXTERNAL = 4, /* the selected MIDI clock source (#1228) */
} le_tempo_source;

/* Click (metronome) audibility mode, mirrored in le_snapshot.click_mode — a
 * 4-value mode per the Sheeran manual §5.9.1, replacing the old boolean
 * metronome (D5). It gates WHEN the click voice sounds; WHERE it sounds is the
 * click output mask (le_engine_set_click_output — default no outputs).
 * Count-in clicks are audible in every mode except OFF while counting. */
typedef enum le_click_mode {
  LE_CLICK_OFF = 0,       /* never audible (count-ins still run, silently) */
  LE_CLICK_REC = 1,       /* while any track records or overdubs */
  LE_CLICK_REC_FIRST = 2, /* only during the DEFINING first-layer recording
                           * (incl. its count-in) */
  LE_CLICK_PLAY_REC = 3,  /* whenever the transport plays or records */
} le_click_mode;

/* The five architectural looper modes (B2a, D4/D10), mirrored in
 * le_snapshot.looper_mode. MULTI is today's behavior — independent per-track
 * loops, the whole engine as it exists before this series — and stays the
 * default. Sync/Band (primary-track sync + multiples/divisions, B3/B3b),
 * Free (independent per-track clocks, B2b), and Song (independent per-track
 * sections, B4) all have their full behavior as of this part; B2a itself was
 * only the field plus a content gate; the accepted content rules (slice 2)
 * engine_process.c) that guards switching it, with every value's audio path
 * staying MULTI behavior until its own part landed. This is a DIFFERENT axis
 * from InteractionMode (Dart-only: record/mute, what a track press does) —
 * the two never coexist under the same name (D10) and must not be
 * confused. */
typedef enum le_looper_mode {
  LE_LOOPER_MODE_MULTI = 0, /* default: independent per-track loops (today's
                             * behavior, unchanged by this part) */
  LE_LOOPER_MODE_SYNC = 1,  /* primary-track sync + multiples/divisions (B3) */
  /* Song (B4): a "section" IS a track (song-mode-spec.md §2 Q1) — up to
   * LE_MAX_TRACKS independent sections, each started/stopped directly via
   * its OWN track press (record/play/stop), exactly like every other mode's
   * per-track controls. No separate section object, no advance gesture (the
   * plan's original `advanceSection` was explicitly dropped once the manual
   * research showed no such gesture exists on the Sheeran — see the spec's
   * six B1 answers). Structurally IDENTICAL to Free's transport (independent
   * lengths, no primary, no shared grid obligation): B4 reuses B2b's
   * per-track clock machinery outright by broadening every FREE-only gate to
   * also cover SONG (see free_clock's doc, engine_private.h) rather than
   * inventing a parallel mechanism. */
  LE_LOOPER_MODE_SONG = 2,
  LE_LOOPER_MODE_BAND = 3,  /* primary + independently-quantized sections
                             * (B3) */
  LE_LOOPER_MODE_FREE = 4,  /* independent per-track clocks (B2b) */
} le_looper_mode;

/* Why a looper-mode change is refused, or what it will do first — the answer
 * of le_engine_looper_mode_gate. Codes are >= 0 so they never collide with
 * the LE_ERR_* results that function can also return. */
typedef enum le_mode_gate {
  LE_MODE_GATE_OPEN = 0,      /* the change applies as posted */
  LE_MODE_GATE_CAPTURING = 1, /* a take or an overdub pass is being captured
                               * (or a count-in runs): finish it first */
  LE_MODE_GATE_QUEUED = 2,    /* an armed action has neither fired nor been
                               * cancelled: let it land or cancel it first */
  LE_MODE_GATE_SPANS = 3,     /* the recorded spans do not fit the target
                               * mode (see le_engine_looper_mode_gate) */
  LE_MODE_GATE_PLAYING = 4,   /* loops are playing: le_engine_set_looper_mode
                               * stops every playing track before switching */
} le_mode_gate;

/* MIDI clock sync state (#1228), mirrored in le_snapshot.clock_state.
 * INTERNAL: Segno's own tempo; incoming clock is ignored. With an external
 * source selected (le_engine_set_clock_sync): WAITING until six consecutive
 * valid pulse intervals arrive, then SYNCED; LOST when a Synced clock goes
 * silent for max(6 pulse periods, 250 ms) or its device goes away. Silence
 * after a received Stop reads WAITING, not LOST. */
typedef enum le_clock_state {
  LE_CLOCK_STATE_INTERNAL = 0,
  LE_CLOCK_STATE_WAITING = 1,
  LE_CLOCK_STATE_SYNCED = 2,
  LE_CLOCK_STATE_LOST = 3,
} le_clock_state;

/* What happens to the loops when an external clock is lost (#1228 D5). The
 * setting is stored now; the engine acts on it from #1228 Part 5. */
typedef enum le_clock_loss_policy {
  LE_CLOCK_LOSS_KEEP_PLAYING = 0,
  LE_CLOCK_LOSS_STOP_LOOPS = 1,
} le_clock_loss_policy;

/* Atomic recording-start edits retain their distinct transient semantics. */
typedef enum le_record_start_edit_kind {
  LE_RECORD_START_COUNT_IN = 0,
  LE_RECORD_START_SOUND = 1,
  LE_RECORD_START_RESTORE = 2,
} le_record_start_edit_kind;

/* Supported count-in lengths are exactly 0, 1, 2 and 4 bars. */
#define LE_COUNT_IN_MAX_BARS 4

/* Maximum track length preset in bars (A6, D17;
 * le_engine_set_track_length_preset). 0 is AUTO, not a bar count. */
#define LE_LENGTH_PRESET_MAX_BARS 64

/* Classification of a cable-free loopback path used to auto-measure latency.
 * All of these capture the *digital* round-trip (output → OS mixer → capture);
 * they exclude DAC/ADC converter latency, so they under-report the true analog
 * round-trip. A physical loopback cable remains the only true analog measure. */
typedef enum le_loopback_kind {
  LE_LOOPBACK_NONE = 0,
  LE_LOOPBACK_BACKEND = 1,   /* device backend's built-in output loopback */
  LE_LOOPBACK_MONITOR = 2,  /* PulseAudio "Monitor of ..." source (Linux) */
  LE_LOOPBACK_VIRTUAL = 3,  /* named virtual driver (BlackHole, VB-Cable, ...) */
} le_loopback_kind;

/* Result of loopback detection. `device_name` is the capture device to open for
 * an auto-measurement (empty for the backend's built-in loopback, which the
 * duplex engine does not auto-route). */
typedef struct le_loopback_info {
  int32_t available; /* 0/1 */
  int32_t kind;      /* le_loopback_kind */
  char device_name[256];
} le_loopback_info;

/* Command codes posted into the engine's SPSC ring. */
typedef enum le_command_code {
  LE_CMD_NONE = 0,
  LE_CMD_MEASURE_LATENCY = 1,
  LE_CMD_RECORD = 2,    /* record / finalize-loop / toggle overdub */
  LE_CMD_STOP = 3,      /* halt playback (retain buffer) */
  LE_CMD_PLAY = 4,      /* resume playback */
  LE_CMD_CLEAR = 5,     /* erase the track, back to empty */
  LE_CMD_UNDO = 6,      /* remove the last overdub layer */
  LE_CMD_SET_VOLUME = 7,/* arg_f = 0..LE_MAX_GAIN */
  LE_CMD_SET_MUTE = 8,  /* arg_f = 0 (unmute) or 1 (mute) */
  /* ---- tempo grid (D6/D7). SET_TEMPO / SET_TIME_SIGNATURE / TAP_TEMPO are
   * REJECTED (no-op) while the tempo is locked: any track has content AND a
   * grid exists (loop_bars > 0 or tempo_source != none). Only clearing every
   * track releases the lock. */
  LE_CMD_SET_TEMPO = 9,  /* arg_f = bpm, clamped to 30..300; sets
                          * tempo_source = manual (last writer wins) */
  LE_CMD_SET_TIME_SIGNATURE = 10, /* arg_i = numerator, arg_f = denominator
                                   * (4 or 8); validated to the 17 supported
                                   * signatures (le_grid_signature_valid,
                                   * tempo_grid.h) — others are dropped */
  LE_CMD_TAP_TEMPO = 11, /* two taps set the tempo from their interval; sets
                          * tempo_source = tapped (last writer wins) */
  LE_CMD_SET_SYNC_TEMPO = 12, /* arg_f = 0/1: whether finalizing a defining
                               * loop establishes the loop<->grid relationship
                               * (bar count / tempo derivation — see
                               * le_engine_set_sync_tempo) */
  LE_CMD_SET_RECORD_OFFSET = 13, /* arg_i = round-trip latency in frames */
  LE_CMD_SET_INPUT_MASK = 14,    /* route a track's record sources (arg_f =
                                  * track, arg_i = input bitmask) */
  LE_CMD_SET_OUTPUT_MASK = 15,   /* route a track's playback destinations
                                  * (arg_f = track, arg_i = output bitmask) */
  LE_CMD_ARM = 16,    /* arg_i = track: arm a quantized record (fire at loop
                       * top). arg_f selects the trigger: 0 = grid/loop-top
                       * (quantize), 1 = input level (auto-record), 2 = Band
                       * section transport (B3b) -- a play/stop TOGGLE on a
                       * content-bearing non-primary track, deferred to the
                       * next primary-track loop top rather than a record
                       * action; see le_engine_toggle_section. */
  LE_CMD_DISARM = 17, /* arg_i = track: cancel a pending quantized record
                       * (any trigger). */
  /* ---- click + count-in (A2, D5/D9). The click is its own routable source:
   * since slice 3b it sums into the channels of its output mask BEFORE the
   * output buses, so a destination's chain, level and mute, the master gain,
   * the limiter and metering all apply, and a performance capture contains it
   * when it is routed to the captured bus. None of these commands is
   * perf-logged, so stems and the offline master never contain it. */
  LE_CMD_SET_CLICK_MODE = 19, /* typed mode + revision; raw posts rejected. */
  LE_CMD_SET_LANE_FX = 20, /* set a lane chain entry's type (and reset its DSP
                            * state). arg_i = (channel << 16) | (lane << 8) |
                            * index, arg_f = le_fx_type. */
  LE_CMD_SET_LANE_FX_COUNT = 21, /* set a lane's active chain length.
                                  * arg_i = (channel << 16) | (lane << 8) |
                                  * count. */
  LE_CMD_SET_CLICK_OUTPUT = 22,  /* click output routing. trackmask arm:
                                  * channel unused, mask = output bitmask
                                  * (default 0 = no outputs). */
  LE_CMD_COMMIT_SESSION = 23,    /* session commit: base_frames and loop_beats;
                                  * publish grid with imported tracks stopped */
  LE_CMD_SET_CLICK_VOLUME = 24,  /* arg_f = 0..LE_MAX_GAIN (the click's ONLY
                                  * gain stage — master gain never applies). */
  LE_CMD_SET_RECORD_START = 25, /* typed pair + edit kind + callback receipt */
  /* ---- multi-lane recording (a track owns an array of lanes) ----
   * Each lane records one hardware input into its own clean mono buffer; all
   * lanes of a track share one transport and one undo span. Count activation
   * and these RT-concurrent lane edits go through the ring; control-side
   * preparation allocates before activation. Argument packing differs per
   * command so a 32-bit mask / a negative channel / a float volume each
   * round-trips exactly (see the lane setters). */
  LE_CMD_SET_LANE_INPUT = 26,  /* lane records this input channel (-1 = none).
                                * arg_f = channel*LE_MAX_LANES + lane,
                                * arg_i = input channel (or -1). */
  LE_CMD_SET_LANE_OUTPUT = 27, /* lane playback destinations.
                                * arg_f = channel*LE_MAX_LANES + lane,
                                * arg_i = output bitmask. */
  LE_CMD_SET_LANE_VOLUME = 28, /* lane playback gain.
                                * arg_i = channel*LE_MAX_LANES + lane,
                                * arg_f = 0..LE_MAX_GAIN. */
  LE_CMD_SET_LANE_MUTE = 29,   /* lane mute.
                                * arg_i = channel*LE_MAX_LANES + lane,
                                * arg_f = 0/1. */
  /* ---- per-input live monitor (one slot per hardware input) ----
   * Each hardware input has a SINGLE live-monitor chain: input-level enable gates
   * the whole input, then the input's live signal runs through its own effect
   * chain / routing / volume / mute. An empty chain is the clean (dry) path. Never
   * recorded, independent of all track state. The chain you monitor live is the
   * chain that is snapshot-copied onto a track lane when you record into it (a
   * clean monitor chain leaves the lane's own staged chain untouched). The
   * monitor commands are keyed by input only (no per-lane index): the FX commands
   * carry (input, index, type) in the typed `fx` arm (lane unused), the count in
   * `fxcount` (lane unused); output rides the `trackmask` arm (channel = input);
   * volume/mute use the generic { arg_i = input, arg_f = value } arm. */
  LE_CMD_SET_MONITOR_INPUT = 30, /* enable/disable a hardware input's monitor.
                                  * arg_i = input, arg_f = enabled (0/1). */
  LE_CMD_SET_MONITOR_INPUT_FX = 31, /* set the input's chain entry type (and reset
                                     * its DSP state). fx arm: channel = input,
                                     * index, type (lane unused). */
  LE_CMD_SET_MONITOR_INPUT_FX_COUNT = 32, /* set the input's active chain length.
                                           * fxcount arm: channel = input, count
                                           * (lane unused). */
  LE_CMD_SET_MONITOR_INPUT_OUTPUT = 33, /* input monitor playback destinations.
                                         * trackmask arm: channel = input, mask. */
  LE_CMD_SET_MONITOR_INPUT_VOLUME = 34, /* input monitor gain.
                                         * arg_i = input, arg_f = 0..LE_MAX_GAIN. */
  LE_CMD_SET_MONITOR_INPUT_MUTE = 35,   /* input monitor mute.
                                         * arg_i = input, arg_f = 0/1. */
  LE_CMD_SET_MASTER_GAIN = 36, /* global post-mix output gain. arg_f = 0..1. */
  LE_CMD_SET_OUTPUT_ENABLED = 37, /* structural output gate (preserves routes).
                                   * arg_i = output index, arg_f = enabled (0/1).
                                   * A disabled output is skipped in the mix
                                   * fan-out regardless of any lane/monitor mask
                                   * pointing at it; masks are untouched. */
  LE_CMD_DUB_SHADOW = 38, /* supply a shadow pool slot for per-pass overdub
                           * layer capture. lanei arm: channel, value = slot
                           * (lane unused). Lane buffers are allocated by the
                           * control thread before the push. */
  LE_CMD_UNDO_TO_EMPTY = 39,   /* undo past the base layer: track to EMPTY,
                                * len 0, master grid kept. arg_i = track. */
  LE_CMD_REDO_FROM_EMPTY = 40, /* reinstate an undone-to-empty track. lanei
                                * arm: channel, value = restored length. The
                                * control thread already swapped a_live. */
  LE_CMD_RESTORE_CLEAR = 43,   /* undo of an undoable clear: reinstate a cleared
                                * track. `restore` arm. Distinct from REDO_FROM_
                                * EMPTY because it restores the pre-clear STATE
                                * (which may be STOPPED) and re-establishes the
                                * master grid a whole-rig clear reset — REDO_
                                * FROM_EMPTY only ever reads the clock. The
                                * control thread already swapped a_live. */

  /* ---- performance-recording capture (arm/disarm the RT taps) ----
   * Zero-payload commands: the control thread allocates the capture rings and
   * writes the frozen config (master.perf_master_out_ch / .perf_input_mask,
   * struct le_engine.perf, engine_private.h) directly into engine state BEFORE
   * pushing the command, then the ring's release/acquire ordering makes that
   * state visible to the audio thread once it pops — the same
   * control-allocates/publish pattern as le_post_dub_shadows and the FX delay
   * lines, so no payload is needed. */
  LE_CMD_PERF_ARM = 41,    /* begin publishing to the perf capture rings */
  LE_CMD_PERF_DISARM = 42, /* stop; control frees the rings after a quiescent
                            * handshake once the audio thread acks this */

  /* ---- track length presets (A6, D17) ----
   * A per-track DEFINING-recording length preset, orthogonal to the existing
   * fixed-multiple machinery (le_effective_multiple / target_multiple,
   * engine_private.h): the multiple mechanism fixes a NON-defining track's
   * length in whole BASE loops once a master already exists; this preset
   * governs the DEFINING (first/master) recording itself — before any base
   * loop length exists — and drives whether tempo, bar count, or both are
   * derived from it (see le_arm_length_preset_target / finalize_master,
   * engine_process.c). Values 0 (AUTO) or 1..LE_LENGTH_PRESET_MAX_BARS
   * (fixed N bars) round-trip identically; anything else is clamped by the
   * audio thread on apply, matching every other per-track setter. Inert on
   * an already-recorded track until it is re-recorded. */
  LE_CMD_SET_LENGTH_PRESET = 44, /* arg_i = channel, arg_f = bars (0 = AUTO,
                                  * 1..LE_LENGTH_PRESET_MAX_BARS = fixed). */

  /* ---- looper mode (B2a, D4) ----
   * The five-mode axis (le_looper_mode). LOCKED (silently rejected, no-op)
   * over capture, pending arms, playing takes or incompatible spans —
   * le_looper_mode_switch_blocked,
   * the audio-thread twin of le_engine_looper_mode_gate. See the looper-mode
   * section of the control API for the content rules. */
  LE_CMD_SET_LOOPER_MODE = 45, /* arg_i = le_looper_mode (0..4) */

  /* ---- primary track / Sync + Band (B3, D16/D18) ----
   * Designates track [arg_i] the "crowned" primary track for Sync/Band's
   * multiple-or-division sync (a_primary_track) — the explicit TIMING
   * HANDOFF. Accepted in ANY mode (the crown is a persistent per-session
   * designation per D18 — it simply has no effect outside Sync/Band);
   * rejected only for an out-of-range channel. There is no "un-crown"
   * command: the engine itself clears the designation when every track is
   * empty, and crowns the first completed take while nothing is crowned
   * (le_primary_reconcile, engine_process.c — the accepted-design rule
   * that supersedes D18's never-auto-assign reading). See
   * le_sync_quantize_active (engine_private.h) for how this gates Sync/Band's
   * finalize + section-transport behavior. */
  LE_CMD_CROWN_PRIMARY = 46, /* arg_i = channel */

  /* One Shot: a per-track setting in every mode. Finishes the current
   * playback pass; explicit launch after automatic end starts at frame zero
   * without moving the shared musical clock. See le_engine_set_one_shot. */
  LE_CMD_SET_ONE_SHOT = 47, /* arg_i = channel, arg_f = 0/1 */

  /* ---- MIDI clock (Phase C, D15; #1228) ----
   * Not perf-logged, for the same reason as LE_CMD_SET_LOOPER_MODE above
   * (clock output is a routing/sync concern, not a captured audible source).
   * Code 48 was the tri-state clock mode; receive moved to
   * LE_CMD_SET_CLOCK_SYNC (124), and the send switch keeps 48 until the
   * per-output send table (#1228 Part 6) replaces it. */
  LE_CMD_SET_CLOCK_SEND = 48, /* arg_i = 0/1 */

  /* ---- Track-stage chains (FX v3 part 1b) ----
   * The bus twins of the lane / monitor FX commands: type/count ride the ring
   * so the audio thread resets the entry's DSP state in lockstep, while
   * params and the enable flags are direct atomic stores (no command). They
   * reuse the typed `fx` / `fxcount` arms with the lane field unused. NONE of
   * these are perf-logged: track chains are manifest-only (part 9's stems
   * decision — the arm manifest carries them from part 3; nothing replays
   * them). The output-bus chains (65, 66) follow the same rules. */
  LE_CMD_SET_TRACK_FX = 49, /* set a track's Track-stage chain entry type (and
                             * reset its DSP state). fx arm: channel, index,
                             * type (lane unused). */
  LE_CMD_SET_TRACK_FX_COUNT = 50, /* set a track's Track-stage active chain
                                   * length. fxcount arm: channel, count
                                   * (lane unused). */

  /* Arm the chromatic tuner on one hardware input, or -1 to disarm. arg_i =
   * channel. The gate is the contract, not an optimization: a disarmed tuner
   * runs no detection at all. Not perf-logged — the tuner changes no
   * output. (51 and 52 were the Master insert family, retired in slice 3b
   * when that insert became output bus 0's chain; the codes stay
   * unallocated so an old event log can never be misread.) */
  LE_CMD_SET_TUNER_INPUT = 53,

  /* ---- per-input conditioning stage (input conditioning, S1) ----
   * A fixed utility stage per hardware input — HPF + mains-hum notches +
   * downward expander — applied ONCE per block into a conditioned copy of the
   * input buffer, upstream of BOTH the lane fan-out and the monitor split
   * (WYSIWYG: what you monitor is what records). Deliberately NOT an
   * le_fx_type chain entry: it cannot be reordered or removed per-chain, it
   * does not enter chain fingerprints, and its params are real units (Hz, dB,
   * ms), not normalized 0..1. Metering, the clip detector, and the latency
   * harness keep reading the RAW device buffer; the sound-activated record
   * trigger deliberately reads the CONDITIONED magnitude so mains hum cannot
   * false-arm a threshold recording. Zero added buffering latency by design
   * (IIR biquads + a no-lookahead envelope follower — no FIR, no lookahead),
   * so record_offset semantics are untouched. Loopback-excluded inputs are
   * never conditioned. Both commands ride the ring (like the monitor-input
   * commands, `channel` = input index, bounds vs LE_MAX_MONITORED_INPUTS) so
   * the audio thread resets/recomputes its thread-local DSP state in lockstep
   * with the config change. Neither is perf-logged: conditioning is upstream
   * of capture, so recorded PCM already embodies it (nothing replays it). */
  LE_CMD_SET_INPUT_COND = 54,       /* enable/disable input conditioning.
                                     * arg_i = input, arg_f = enabled (0/1).
                                     * An enable EDGE resets the stage's DSP
                                     * state (no stale filter ring). */
  LE_CMD_SET_INPUT_COND_PARAM = 55, /* set one conditioning parameter.
                                     * lanef arm: channel = input,
                                     * lane = le_cond_param, value = real-unit
                                     * value (clamped by the audio thread on
                                     * apply). */

  /* Immediate finalize (#405): ends track arg_i's live RECORDING take NOW —
   * or does nothing. Unlike LE_CMD_RECORD, whose meaning depends on the state
   * it lands on (start / finalize / punch-in / punch-out), this command
   * re-checks its precondition on the audio thread and is a strict no-op
   * anywhere else, so a state change in the one-block window between
   * le_engine_finalize_take's control-side guards and the apply can never
   * turn it into a capture start or a punch-in/out. Pending Count-in members
   * use explicit cancellation instead. Not itself perf-logged (the resulting
   * LE_PLOG_RECORD_END is logged by the actual finalization). */
  LE_CMD_FINALIZE_TAKE = 56,
  /* Cancel a take in progress on arg_i (le_engine_undo while RECORDING): the
   * take is finalized at its captured length exactly as a press would end
   * it — grid, tempo derivation and loop span included — and the track then
   * reads EMPTY with that finalized content held for redo, which plays it
   * immediately (LE_CMD_REDO_FROM_EMPTY). LE_EVT_TAKE_CANCELLED carries the
   * finalized length back so the control thread can file the redo entry. */
  LE_CMD_CANCEL_TAKE = 57,
  /* Exact musical tempo restoration on a stopped rig. arg_i = tempo source,
   * arg_f = BPM (0 only with NONE). Rechecked by the callback. */
  LE_CMD_RESTORE_TEMPO = 58,
  /* One queued command updates a subset of tracks together. arg_i = track
   * bitmask, arg_f = 0/1; uses the same pass semantics as SET_ONE_SHOT. */
  LE_CMD_SET_ONE_SHOT_MASK = 59,
  /* Named bounded payload: all configured tracks' future length presets. */
  LE_CMD_SET_LENGTH_PRESETS = 61,
  /* Lane pan (accepted design, slice 3). lanef arm: channel, lane, value in
   * -1..1 (clamped). Placement of the lane's stereo pair across its first two
   * masked outputs, applied after the lane's chain: a unity-centre balance
   * law (see le_engine_set_lane_pan). Perf-logged like volume. */
  LE_CMD_SET_LANE_PAN = 62,
  /* Track solo. Generic arm: arg_i = channel, arg_f != 0 = soloed. While any
   * track is soloed, only soloed tracks route (mute is untouched and still
   * gates on its own). Perf-logged. */
  LE_CMD_SET_TRACK_SOLO = 63,
  /* Monitor pan. lanef arm: channel = input, value in -1..1. The monitor
   * mirror of LE_CMD_SET_LANE_PAN. Perf-logged. */
  LE_CMD_SET_MONITOR_INPUT_PAN = 64,
  LE_CMD_SET_MIX = 65, /* one bounded, atomic mix transaction */
  LE_CMD_RECORD_IMAGE = 66, /* RECORD/ARM plus its frozen input image */
  /* Output bus facts (slice 3b). lanef arm: channel = bus, value. Level
   * 0..1, mute/mono as 0/1 in value, balance -1..1. Perf-logged. */
  LE_CMD_SET_OUTPUT_LEVEL = 67,
  LE_CMD_SET_OUTPUT_MUTE = 68,
  LE_CMD_SET_OUTPUT_MONO = 69,
  LE_CMD_SET_OUTPUT_BALANCE = 70,
  /* Output bus chain entry type / active length: fx / fxcount arms with
   * channel = bus; bus 0's chain is what the app calls the Master insert. */
  LE_CMD_SET_OUTPUT_FX = 71,
  LE_CMD_SET_OUTPUT_FX_COUNT = 72,
  /* Cut all sound (accepted design): stops every audible recorded track and
   * the count-in, and clears every effect tail on every chain (lane, track,
   * monitor, output) while keeping their settings; the snapshot's
   * tail_reset_rev advances. Monitors keep their preferences: new live
   * input sounds again at once. Perf-logged. */
  LE_CMD_CUT_SOUND = 73,
  LE_CMD_SET_LANE_COUNT = 74, /* internal structural activation; callback-owned */
  /* All tracks recorded-mix chain entry type / active length (slice 3e): the
   * fx / fxcount arms with channel = 0 (there is one such chain). One shared
   * config; the audio thread runs it once per output bus over the recorded
   * contribution to that bus. */
  LE_CMD_SET_ALL_TRACKS_FX = 75,
  LE_CMD_SET_ALL_TRACKS_FX_COUNT = 76,

  /* Event codes (audio thread -> control thread, on the engine's evt_ring —
   * the reverse SPSC direction; numbered apart from the commands for clarity). */
  LE_EVT_LAYER_RETIRED = 100, /* a completed overdub-pass snapshot. evt arm:
                               * channel, slot, generation. */
  LE_EVT_TAKE_CANCELLED = 101, /* LE_CMD_CANCEL_TAKE landed: lanei arm —
                                * channel, value = the finalized length the
                                * emptied track holds for redo (0: nothing
                                * was captured, nothing to redo). */
  LE_CMD_SET_FX_RECIPE = 77,
  LE_CMD_SET_RECORD_TIMING = 78, /* one complete timing vector and receipt */
  LE_CMD_STOP_RECORD_CONTROL = 79, /* cohort cancel or non-acquiring capture finish */
  LE_CMD_CANCEL_COUNT_IN = 80, /* only the shared launch cohort/grace */
  LE_CMD_FADE = 81, /* checked internal Fade request; never raw-posted */
  LE_CMD_RESET_TRANSFORMS = 82, /* internal material-import transform reset
                                 * (Fade and direction); never raw-posted */
  LE_CMD_REVERSE = 83, /* checked internal Reverse request; never raw-posted */

  /* Silence the live monitors of the inputs in the mask while the tuner is
   * armed (#1229). arg_i = the mask, bit c = input c. Owned by the tuner arm:
   * refused (stored as 0) while the tuner is disarmed, and cleared by every
   * LE_CMD_SET_TUNER_INPUT, so it can never outlive or follow a tuning. Not
   * perf-logged: it changes no recorded material, and a captured monitor stem
   * already records the silence that was heard. 84-131 belong to other
   * epics (the numbering ledger); 133-135 stay reserved for #1229. */
  LE_CMD_SET_TUNER_MUTE = 132,
  LE_CMD_SET_LENGTH = 84, /* checked internal length edit (#1168); never
                           * raw-posted */
  LE_CMD_SET_SPEED = 85, /* checked internal Speed request (#1179); never
                          * raw-posted */
  LE_CMD_TRANSPOSE = 86,        /* checked internal Transpose request (#1179) */
  LE_CMD_TRANSPOSE_BYPASS = 87, /* checked internal Transpose bypass */
  /* ---- backing player (#1200; 88-95 reserved for it, 93-95 unused). Typed
   * producers only (le_engine_backing_*): LOAD and STAGE_NEXT carry an owned
   * buffer pointer, so raw posts of any of these are refused. None is
   * perf-logged: the backing never reaches stems or the offline master. */
  LE_CMD_BACKING_LOAD = 88,       /* buffer + item token + play flag */
  LE_CMD_BACKING_STAGE_NEXT = 89, /* buffer (NULL clears) + item token */
  LE_CMD_BACKING_CLEAR = 90,      /* unload current and staged */
  LE_CMD_BACKING_TRANSPORT = 91,  /* arg_i = le_backing_transport_op */
  LE_CMD_BACKING_SEEK = 92,       /* arg_i = frame of the loaded buffer */
  /* ---- Library audition voice (#1178; 136-137 in the numbering ledger).
   * Typed producers only (le_engine_audition_*): START carries an owned
   * buffer pointer, so raw posts are refused. Never perf-logged. */
  LE_CMD_AUDITION_START = 136, /* buffer + output pair */
  LE_CMD_AUDITION_STOP = 137,
  LE_CMD_RENDER_FREEZE = 112, /* render recipe (#1202): the callback records
                               * every source's read law; never raw-posted */
  LE_CMD_BOUNCE = 113,         /* Bounce (#1202): installs a rendered result on
                                * the destination in one drain; checked,
                                * never raw-posted */
  LE_CMD_BOUNCE_RECOVER = 114, /* Bounce Undo/Redo (#1202): reinstalls the
                                * other side of a bounce; never raw-posted */
  /* MIDI clock sync (#1228; codes 124-131 are this epic's): one complete
   * vector {source port or -1, follow transport, loss policy} with a receipt
   * sequence. Rechecked by the callback (LE_ERR_SYNC_LOCKED). */
  LE_CMD_SET_CLOCK_SYNC = 124,
  LE_CMD_SET_FOLLOW_TEMPO = 120, /* checked internal Follow tempo setting
                                  * (#1179 Part 4a) */
  LE_CMD_SET_PITCH_MODE = 121, /* checked internal Pitch setting (#1179 Part
                                * 4a-ii); 122-123 are held for #1179 */

  /* Instruments (#1197; the ledger assigns 96-111). Patch changes are not
   * commands: they ride the ordered note ring (le_engine_set_instrument). */
  LE_CMD_SET_VOICE_LIMIT = 96, /* arg_i = sounding-voice limit */
  LE_CMD_INSTRUMENT_RESET = 97, /* arg_i = slot: fade its voices out */
} le_command_code;

/* Per-lane / per-monitor-input effects: each lane (and each live monitor input)
 * carries an ordered chain of up to LE_FX_MAX entries, each with a type and
 * LE_FX_PARAMS normalized (0..1) parameters. The chain is non-destructive (the
 * recording is ALWAYS dry; effects color playback only) and every active entry
 * applies in chain order. The cap exists only so the audio thread reads a
 * fixed-size, allocation-free array — it is not a CPU limit: the audio path
 * iterates the ACTIVE count, and the per-slot DSP heap (delay rings, the
 * octaver's vocoder buffers) is allocated lazily on first use, so an unused
 * slot costs nothing but its place in the struct.
 *
 * Raised from 8 to 64 in slice 3f. The accepted FX design builds a chain out
 * of RACKS — named groups of pedals — and one factory rack is about six, so
 * eight slots held roughly one rack where the design shows ten. Sixty-four
 * holds ten full racks.
 *
 * The per-buffer snapshots live in engine-owned scratch rather than growing
 * the callback stack. Recipe commands carry retained prepared pointers, so
 * raising this ceiling does not enlarge each command-ring entry. */
#define LE_FX_MAX 64
#define LE_FX_PARAMS 4

/* Built-in effect types. Designed so a hosted VST3/CLAP plugin can later slot
 * in as just another type. Each type reads its entry's LE_FX_PARAMS normalized
 * values:
 *   DRIVE:   p0 = drive amount, p1 = output level
 *   FILTER:  p0 = cutoff, p1 = resonance        (resonant low-pass)
 *   DELAY:   p0 = time, p1 = feedback, p2 = wet mix
 *   TREMOLO: p0 = rate, p1 = depth
 *   OCTAVER: p0 = shift (0 = -2 oct, .5 = unison, 1 = +2 oct), p1 = tone,
 *            p2 = mix, p3 = mode (< .5 = phase vocoder, >= .5 = PSOLA; stored
 *            but inert until the formant-preserving rewrite reads it)
 * Every other type leaves its unused trailing params (including p3) at 0; no
 * non-octaver effect reads p3.
 *   ECHO:    p0 = time, p1 = feedback, p2 = mix  (tape-style, damped repeats)
 *   REVERB:  p0 = size, p1 = damping, p2 = mix   (Schroeder room tail; a mono
 *            input yields a decorrelated stereo tail spread across the first two
 *            output channels of the lane/monitor mask) */
typedef enum le_fx_type {
  LE_FX_NONE = 0,
  LE_FX_DRIVE = 1,
  LE_FX_FILTER = 2,
  LE_FX_DELAY = 3,
  LE_FX_TREMOLO = 4,
  LE_FX_OCTAVER = 5,
  LE_FX_ECHO = 6,
  LE_FX_REVERB = 7,
  /* A hosted VST3/CLAP plugin. Unlike the built-ins this row carries no fixed
   * params and no DSP state in le_fx_state — its `process` forwards to a plugin
   * host owned by an le_plugin_slot, loaded on the control thread (see
   * le_engine_set_lane_plugin). An LE_FX_PLUGIN entry whose slot is not yet
   * published (or is being torn down) renders dry passthrough. */
  LE_FX_PLUGIN = 8,
} le_fx_type;

/* Which device backend to open. The default (0) opens miniaudio's default
 * backend for the platform (Core Audio on macOS, the Linux preference list) —
 * the only backend this engine ships. */
typedef enum le_audio_backend {
  LE_BACKEND_MINIAUDIO = 0, /* default: miniaudio's default platform backend */
  /* Reserved. Was Windows ASIO; the backend went with the desktop targets, but
   * the value stays claimed so a persisted setting written by an older build
   * still parses instead of being reinterpreted as another backend. */
  LE_BACKEND_ASIO = 1,
} le_audio_backend;

/* A hardware audio device discovered by enumeration (le_enumerate_*).
 *
 * `id` is an opaque, backend-specific token suitable for pinning a device via
 * le_config.playback_device_id / capture_device_id. On every string-id backend
 * (CoreAudio, ALSA, PulseAudio, sndio) it is the device's native id string; it
 * round-trips byte-for-byte back into le_config. `name` is the human-readable
 * label; `is_default` marks the system default for that direction. */
typedef struct le_device_info {
  char id[256];
  char name[256];
  int32_t is_default;      /* 0/1 */
  /* The device's channel count in the direction it was enumerated in: a
   * capture device fills input_channels, a playback device output_channels,
   * and the other stays 0 — a playback device reports what it can play and
   * never the other way round. An ASIO driver is duplex and fills both.
   * 0 = UNKNOWN, not "no channels": a device that cannot answer keeps it, and
   * a count is omitted rather than printed as a zero. */
  int32_t input_channels;
  int32_t output_channels;
  /* ASIO-only: the driver's selectable buffer sizes and supported sample rates,
   * probed by le_enumerate_asio_drivers so the UI can offer the driver's real
   * options instead of a generic list. Count 0 for non-ASIO devices (the UI
   * then keeps its default lists). Sizes/rates are ascending; the buffer set
   * always includes the driver's preferred size. */
  int32_t asio_buffer_sizes[8];
  int32_t asio_buffer_count;
  int32_t asio_sample_rates[8];
  int32_t asio_sample_rate_count;
} le_device_info;

/* Requested device configuration. Any channel field set to 0 uses the device
 * default; counts are clamped to LE_MAX_CHANNELS. */
typedef struct le_config {
  int32_t sample_rate;
  int32_t buffer_frames;
  int32_t max_loop_frames; /* per-track buffer cap; 0 => default (8 min @ sr) */
  int32_t use_loopback_capture; /* 1 = capture from a detected loopback device */
  int32_t input_channels;  /* hardware capture channels (0 => device default) */
  int32_t output_channels; /* hardware playback channels (0 => device default) */
  /* Pin a specific device by id (an `id` from le_enumerate_*). An empty string
   * opens the system default (the unchanged behaviour). use_loopback_capture
   * overrides capture_device_id when a loopback device is detected. */
  char playback_device_id[256];
  char capture_device_id[256];
  /* le_audio_backend to open. Every value resolves to miniaudio via
   * le_select_backend; the field stays so persisted configs still round-trip. */
  int32_t backend;
  /* Reserved, alongside LE_BACKEND_ASIO. Always empty and ignored. */
  char asio_driver[256];
} le_config;

/* Maximum number of simultaneous looper tracks (two banks of four). */
#define LE_MAX_TRACKS 8
/* Instrument slots (#1197): each a synthesized mono source. */
#define LE_MAX_INSTRUMENTS 8
/* The source index space every input-keyed route, monitor and mix entry uses
 * (#1197): sources [0, LE_MAX_CHANNELS) are device input channels, and
 * LE_INSTRUMENT_SOURCE_BASE + k is instrument slot k. The index never depends
 * on the interface's channel count. Physical-only stages (loopback exclusion,
 * clip detection, conditioning, capture trim, the tuner) cover device
 * channels only. */
#define LE_INSTRUMENT_SOURCE_BASE LE_MAX_CHANNELS
#define LE_MAX_SOURCES (LE_MAX_CHANNELS + LE_MAX_INSTRUMENTS)

/* Default and fixed-track recording choices: 0 immediately, 1 loop start,
 * 2 bar, 3 half, 4 quarter, 5 eighth, 6 sixteenth. Track -1 inherits. */
typedef struct le_record_timing_settings {
  int32_t default_timing;
  int32_t remembered_division;
  int32_t track_timing[LE_MAX_TRACKS];
  uint32_t edit_mask; /* bit 0 default, bits 1..8 track intentions */
} le_record_timing_settings;



/* Lanes a single track may own: one lane per hardware input it records. A lane
 * is the fundamental recordable unit — one clean mono buffer fed by one input —
 * and a track owns up to this many, all sharing one transport and undo span.
 * Lane buffers are allocated lazily (only recorded/counted lanes), so the
 * worst-case LE_MAX_TRACKS * LE_MAX_LANES does not inflate idle memory. */
#define LE_MAX_LANES 8

/* Sources the live-monitor path covers, [0, LE_MAX_MONITORED_INPUTS).
 * Bounds the per-input monitor array (le_engine_set_monitor_input and friends)
 * and the per-input capture rings beside it.
 *
 * Every hardware input the engine can open can be monitored (accepted
 * design, slice 3: an 18-input interface monitors channel 18 exactly as
 * well as channel 1), and so can every instrument source (#1197), so this
 * is LE_MAX_SOURCES. It stays a distinct name from LE_MAX_LANES, which
 * bounds a different thing (lanes per track), and the monitor arrays are
 * sized by it, never by the lane ceiling. Each le_monitor_input is about
 * 3.3 KB, so 40 of them cost ~132 KB. */
#define LE_MAX_MONITORED_INPUTS LE_MAX_SOURCES

/* Output destinations (accepted design, slice 3b): output bus k is the
 * hardware pair (2k, 2k + 1); the last bus of an odd-count device is its one
 * channel. Every source's output mask still says which channels it reaches;
 * a bus is what those channels share downstream: one effect chain over the
 * sum of everything routed there (live inputs, loops, click), then its
 * level, Stereo/Mono, balance and mute. See le_engine_set_output_level. */
#define LE_MAX_OUTPUT_BUSES (LE_MAX_CHANNELS / 2)

typedef struct le_output_fx_snapshot {
  int32_t count, chain_enabled;
  int32_t type[LE_FX_MAX], enabled[LE_FX_MAX];
  float params[LE_FX_MAX][LE_FX_PARAMS];
} le_output_fx_snapshot;

/* ---- Input clip ("HOT") detector (input clip, S2) ---- *
 * Always on, no parameters, RAW path: LE_CLIP_RUN or more CONSECUTIVE samples
 * at |s| >= LE_CLIP_LEVEL on a non-loopback input latch that input's bit in
 * le_snapshot.input_clip_mask, held for LE_CLIP_HOLD_MS past the last detected
 * run (a persisting rail keeps refreshing the hold). The run requirement is
 * the point: a one-or-two-sample full-scale transient is music, while a flat
 * run at the rail is the clamp signature of an overdriven ADC. Detection reads
 * the RAW device buffer — upstream of the conditioning stage — so a clipped
 * input flags HOT even when the expander/HPF has reshaped what records. */
#define LE_CLIP_LEVEL 0.999f
#define LE_CLIP_RUN 4
#define LE_CLIP_HOLD_MS 1500

/* Ceiling for a per-lane / per-monitor channel volume. 2.0 is +6.02 dB, so the
 * UI can boost a quiet take/input up to +6 dB rather than only attenuate from
 * unity (1.0 = 0 dB). The output limiter downstream still guards the bus. */
#define LE_MAX_GAIN 2.0f

/* Ceiling of le_engine_set_input_trim's linear capture gain: +12 dB. The
 * accepted range is -24..+12 dB in half-decibel steps; the floor is 0. */
#define LE_MAX_INPUT_TRIM 3.98107170553f

/* One user-visible mix edit. Masks address only the supplied entries; all
 * values are finite and bounded. Lane index = track * LE_MAX_LANES + lane.
 * The caller supplies a nonzero revision, published only after the entire
 * edit applies. The engine copies this POD into one command, never retains
 * the caller's pointer. No state changes on validation/queue refusal. */
typedef struct le_mix_settings {
  uint32_t revision;
  uint32_t track_gain_mask;
  float track_gain[LE_MAX_TRACKS]; /* after whole-track Pre, before Post */
  uint64_t lane_mask, image_mask;
  uint64_t monitor_mask; /* bit s: source s (#1197: instruments are 32-39) */
  uint32_t trim_mask, solo_mask, solo_values; /* trim: device channels only */
  float lane_gain[LE_MAX_TRACKS * LE_MAX_LANES];
  float lane_pan[LE_MAX_TRACKS * LE_MAX_LANES];
  /* Source image is separate from live lane gain and track pan offset. */
  float image_gain[LE_MAX_TRACKS * LE_MAX_LANES];
  float image_pan[LE_MAX_TRACKS * LE_MAX_LANES];
  float monitor_gain[LE_MAX_SOURCES], monitor_pan[LE_MAX_SOURCES];
  float input_trim[LE_MAX_CHANNELS];
  uint32_t output_mask, output_muted, output_mono;
  float output_level[LE_MAX_OUTPUT_BUSES], output_balance[LE_MAX_OUTPUT_BUSES];
  /* Future capture assignments and playback routes share this publication.
   * Source guards include pair edits even when no assignment changes. */
  uint64_t routing_input_mask, routing_output_mask;
  uint32_t lane_count_mask, source_track_mask;
  int32_t lane_input[LE_MAX_TRACKS * LE_MAX_LANES];
  uint32_t lane_output[LE_MAX_TRACKS * LE_MAX_LANES];
  int32_t lane_count[LE_MAX_TRACKS];
} le_mix_settings;

typedef struct le_engine le_engine;

/* One bounded command; enqueue is not application. The full snapshot carries
 * the coherent applied tuple and its even receipt revision/result. */
LE_EXPORT int32_t le_engine_set_record_timing_settings(
    le_engine* engine, const le_record_timing_settings* settings);

typedef struct le_plugin_slot le_plugin_slot;

/* Complete structural recipe, copied before admission. Hosted pointers must
 * belong to this chain or have been prepared by this engine. */
typedef struct le_fx_recipe {
  int32_t count, pre_count, enabled;
  int32_t type[LE_FX_MAX], slot_enabled[LE_FX_MAX];
  float params[LE_FX_MAX][LE_FX_PARAMS];
  int32_t input_mode[LE_FX_MAX], output_mode[LE_FX_MAX];
  float placement[LE_FX_MAX], level[LE_FX_MAX];
  le_plugin_slot* plugin[LE_FX_MAX];
} le_fx_recipe;

typedef enum le_fx_owner {
  LE_FX_OWNER_LANE = 0,
  LE_FX_OWNER_TRACK = 1,
  LE_FX_OWNER_MONITOR = 2,
  LE_FX_OWNER_ALL_TRACKS = 3,
  LE_FX_OWNER_OUTPUT = 4,
} le_fx_owner;

/* Structural changes publish in one callback command. A pending structural
 * edit fences granular writes to that chain until publication. Refusal leaves
 * the active recipe and prepared-plugin ownership unchanged. */
LE_EXPORT int32_t le_engine_set_fx_recipe(le_engine* engine, int32_t owner,
    int32_t channel, int32_t lane, uint32_t revision, const le_fx_recipe* recipe);
LE_EXPORT uint32_t le_engine_fx_recipe_revision(le_engine* engine, int32_t owner,
    int32_t channel, int32_t lane);
LE_EXPORT int32_t le_engine_prepare_plugin(le_engine* engine,
    const char* plugin_id, le_plugin_slot** out_slot);
LE_EXPORT int32_t le_engine_discard_prepared_plugin(le_engine* engine,
    le_plugin_slot* slot);
LE_EXPORT int32_t le_engine_prepare_plugin_param(le_engine* engine,
    le_plugin_slot* slot, uint32_t param_id, double value);

/* Source context frozen at the accepted record/arm gesture. The image is
 * applied only when capture starts, including count-in/signal/grid starts.
 * Cancelling an arm drops it without changing existing lane playback.
 * gain is source balance (0..1); pan is source position (-1..1). Live lane
 * level and track pan offset remain independent throughout an arm.
 * image_revision survives short takes and finalization until reconfigure. */
typedef struct le_record_image {
  uint32_t revision, lane_mask;
  float gain[LE_MAX_LANES], pan[LE_MAX_LANES];
  /* Optional per-lane recipes frozen with this arm. The producer copies the
   * array during this call; the caller retains its own memory. */
  uint32_t fx_lane_mask;
  const le_fx_recipe* lane_fx;
} le_record_image;



/* Number of points in the loop visualization buffer (le_engine_read_visual):
 * one peak per loop position, spanning exactly one master loop. */
#define LE_VIZ_POINTS 512

/* Per-lane state published via le_engine_get_lane: one recordable input lane of
 * a track. A lane records exactly one hardware input (input_channel, -1 = none)
 * into its own clean mono buffer and plays back to the outputs in output_mask,
 * scaled by volume and gated by muted. length_frames is the lane's recorded
 * length (all lanes of a track share the same length via the one transport). */
typedef struct le_lane_snapshot {
  int32_t input_channel; /* hardware input this lane records (-1 = none) */
  uint32_t output_mask;  /* bitmask of output channels this lane plays to */
  float volume;          /* 0..LE_MAX_GAIN */
  int32_t muted;         /* 0/1 */
  int32_t length_frames; /* frames captured into this lane's buffer */
  float rms;             /* 0..1 */
  float peak;            /* 0..1 */
  /* Trailing (#595): 0/1 — this lane captured audio that is still live or
   * restorable (clear-restore shadow / redo stack). THE per-lane "holds
   * content" signal: length_frames is track-shared (the write head publishes
   * the same growing length onto every active lane), so it cannot answer
   * whether a specific lane's slot is safe to reclaim. Drops to 0 only once
   * nothing on the lane can come back. */
  int32_t recoverable;
  /* Trailing (accepted design, slice 3): the lane's pan, -1 (left) .. 1
   * (right), 0 centre — see le_engine_set_lane_pan. */
  float pan;
} le_lane_snapshot;

/* Per-track state published in le_snapshot.tracks.
 *
 * A track is a multi-lane container: it owns the transport (state, multiple,
 * undo/redo depth) and up to lane_count lanes. The volume/muted/length/
 * input_mask/output_mask/rms/peak fields mirror lane 0 for backward
 * compatibility (a track always has at least one lane); per-lane state is read
 * with le_engine_get_lane. */
/* One coherent Fade image. Lifetime/generation bind an install to the engine
 * configuration and recorded material that were observed by the caller. */
typedef struct le_fade_image {
  float amount, target, full_travel_seconds;
  uint64_t lifetime, generation;
} le_fade_image;

typedef struct le_track_snapshot {
  le_fade_image fade;
  uint64_t fade_revision;
  int32_t state;         /* le_track_state */
  float volume;          /* lane 0 volume, 0..LE_MAX_GAIN */
  int32_t muted;         /* lane 0 mute, 0/1 */
  int32_t length_frames; /* frames captured (== multiple * master length) */
  int32_t multiple;      /* track length in whole base loops (>= 1) */
  int32_t undo_depth;    /* available undo steps (overdub layers). A track
                          * cleared via le_engine_clear_undoable reads 0 here
                          * even though its erased take's layers are still held:
                          * they are not peelable until the restore point above
                          * them is undone. See clear_restore. */
  int32_t clear_restore; /* 1 when the next le_engine_undo restores a cleared
                          * take rather than peeling a layer — i.e. "undo would
                          * do something" on a track whose undo_depth is 0. */
  int32_t redo_depth;    /* available redo steps */
  float rms;             /* lane 0 RMS, 0..1 */
  float peak;            /* lane 0 peak, 0..1 */
  uint32_t input_mask;   /* lane 0 input as a bitmask (1 << input_channel, or 0
                          * when lane 0 records no input) */
  uint32_t output_mask;  /* lane 0 output mask */
  int32_t lane_count;    /* number of active lanes (1..LE_MAX_LANES) */
  int32_t layer_in_flight; /* 0/1: an overdub undo layer is still being
                            * captured/drained (punch tail window). Session
                            * capture waits this out before exporting. */
  int32_t pending;         /* 0/1: a quantized/signal arm is waiting to fire */
  /* Trailing (A6, D17): the DEFINING-recording length preset — 0 = AUTO,
   * 1..LE_LENGTH_PRESET_MAX_BARS = fixed N bars. Inert on a track that
   * already has content; applies to the next defining recording only. See
   * le_engine_set_track_length_preset. */
  int32_t length_preset_bars;
  /* Trailing (B3, D16): 0 = this track's length is an ordinary multiple of
   * the base loop (see `multiple` above — the common case in every mode,
   * including Sync/Band multiples). 2 or 4 = this track is a SYNC DIVISION:
   * it plays a repeating 1/2 or 1/4 slice of the primary track's length,
   * phase-locked to the primary's loop top (`multiple` reads 1, inertly, for
   * a division track). Only ever nonzero in Sync/Band mode on a non-primary
   * track. See le_sync_quantize_active (engine_private.h) for how it's set. */
  int32_t sync_divisor;
  /* Trailing (B4, One Shot): 0/1, default 0. Live in every mode; see
   * le_engine_set_one_shot for playback and relaunch semantics. */
  int32_t one_shot;
  /* Trailing (#819): the monotonic per-track id of the currently-SETTLED take
   * — the take the RECORD_END that last finalized this track logged, published
   * from le_track.a_settled_take_id. 0 means the track never finalized a take
   * in this session (still empty, or only ever held pre-arm content with no id
   * yet). The performance-capture pipeline writes it onto the disarm manifest's
   * lane-0 entry as `takeId`, and the offline renderer (perf_render.c) matches
   * it against the RECORD_END payloads to anchor the settled image by identity
   * rather than by "first RECORD_END on the channel". */
  int32_t settled_take_id;
  /* Trailing (#697 S9, offline loop-close restoration): 0 idle, 1 queued (the
   * enqueue copy is in flight or the job is waiting for the worker), 2 running
   * (the worker's de-clip/denoise DSP is in flight). A completed pass publishes
   * its result as an ordinary undo layer, so undo_depth/clear_restore carry the
   * revert affordance — this field is only the in-progress indicator. See
   * le_engine_restore_track. */
  int32_t restore_state;
  /* Trailing (accepted design, slice 1): this track's OWN playhead in frames
   * within its own length — a multiple's segment offset, a Sync division's
   * folded phase and a Free/Song track's private clock are all already
   * applied, so `position_frames / length_frames` is the track's progress
   * without the reader re-deriving the mode's position rule. It is the read
   * index of the block's LAST frame (so one behind master_position_frames,
   * which is advanced after each frame); while RECORDING it is the write
   * head instead (frames captured so far). 0 for an empty or never-played
   * track. Published once per block beside the level. */
  int32_t position_frames;
  /* Trailing (accepted design, slice 1): what the arm reported by `pending`
   * waits for — 0 = the quantize grid (next loop top / subdivision), 1 = a
   * signal at the recording input (Sound start), 2 = a Band section toggle
   * at the primary's loop top; -1 while nothing is pending. The stage names
   * the boundary from this rather than guessing from the settings. */
  int32_t pending_trigger;
  /* ---- per-track record timing and decay overrides (accepted design,
   * slice 2b; trailing). What the engine holds, so a surface and a session
   * capture read the setting back rather than what was last sent. */
  int32_t quantize_override; /* -1 inherit, 0 forced off, 1 forced on
                              * (record timing vector) */
  int32_t quantize_div_override; /* -1 inherit, else le_grid_div
                                  * (record timing vector) */
  float overdub_feedback_override; /* negative = inherit, else 0..1
                                    * (le_engine_set_track_overdub_feedback) */
  /* Trailing (accepted design, slice 3): the Mixer's per-track facts. */
  int32_t solo; /* 0/1 — le_engine_set_track_solo; independent of muted */
  /* Absolute stereo peaks AFTER volume, pan and track FX, BEFORE output
   * routing/downmix and the master bus. Values may exceed unity (clipping
   * headroom); never clamped to 1. A mono destination folds the pair later
   * and need not equal either meter. 0 when no enabled route is audible. */
  float peak_l;
  float peak_r;
  uint32_t image_revision; /* last image applied at capture start */
  int32_t pending_launch; /* 0 none, 1 Record, 2 Play, 3 Overdub: shared Count-in */
  /* A just-committed member can still be canceled in the next command drain.
   * This is cancellation authority, not pending membership or fresh admission. */
  int32_t count_in_cancel_grace;
  /* Trailing (#1162, Reverse): 0 forward, 1 reversed — the callback-owned
   * read direction of the track's recorded material, published with every
   * accepted le_engine_toggle_reverse / le_engine_install_reverse and reset to
   * forward with the material (Clear, Undo to empty, a new capture, import).
   * A performance transform, not an audio edit: never in the undo history. */
  int32_t reversed;
  /* Trailing (#1164): how many overdub layers le_engine_peel can still remove
   * — the LAYER entries above the newest history entry that is neither an
   * overdub nor a peel. Published under undo_depth's gates, so an EMPTY track
   * reads 0 here too. The host derives its layer count from this: PEEL
   * entries keep undo_depth constant while a layer disappears. */
  int32_t peel_depth;
  /* Trailing (#1179): the track's effective read rate x1000 (source frames
   * per song frame; 500 at 1/2x Speed, 8000 at 8x), so the host shows the
   * derived pitch and progress without re-deriving them. position_frames
   * moves at this rate. */
  int32_t head_rate_milli;
  /* Trailing (#1179 Part 3a): the stored Transpose pitch (-12..12) and the
   * pitch actually sounding — 0 while its render is pending, refused or
   * bypassed, so a host never claims a pitch the mix is not playing. */
  int32_t transpose_st;
  int32_t transpose_effective_st;
  /* Trailing (#1168): how many Undo or Redo taps on this track's length edits
   * did nothing where the tap's own result could not say so, counted since
   * the engine was created and never reset: a tap posted as LE_OK that the
   * callback then refused (the rig changed in between), or taps queued behind
   * an overdub that stopped at a length edit, which only an explicit tap
   * undoes. A refusal returned to the tap itself is not counted: its caller
   * reports that result, so one tap raises one notice. The host reports each
   * increase, so a tap that did nothing is never silent. */
  uint32_t length_history_refusals;
  /* Trailing (#1179 Part 4a): this track's Follow tempo override (-1
   * inherits le_snapshot.follow_tempo, 0 keeps its recorded speed, 1 follows
   * the song tempo). */
  int32_t follow_override;
  /* Trailing (#1179 Part 4a-ii): this track's Pitch override (-1 inherits
   * le_snapshot.pitch_follows_speed, 0 Unchanged, 1 Follows speed), and the
   * pitch the tempo retime puts on what it sounds now, in cents: 0 at its
   * own span or once a stretch render plays (within the 0.5 % tolerance,
   * about 9 cents), the varispeed's shift while that render is pending or
   * with Follows speed. Speed and Transpose are not included. */
  int32_t pitch_override;
  int32_t pitch_effective_cents;
  /* Trailing (#1179 Part 4b): the shared-clock length this track's take was
   * laid down against once a retime moved the clock (0: the clock in force).
   * A Session saves it so a recall reads every take at its own ratio. */
  int32_t span_frames;
} le_track_snapshot;

/* ===================== Audio-callback telemetry (#722) =====================
 *
 * The audio callback measuring its OWN lateness. Until this existed nothing on
 * the miniaudio backends (Linux/macOS) counted a missed deadline: xrun_count was
 * fed only by the Windows ASIO overload notification, so the appliance could not
 * tell a callback that ran long from one that ran fine. Observation only — no
 * audio behaviour depends on any of it.
 *
 * WHAT IS MEASURED, and where: the device backend's data callback wraps
 * le_engine_process between two monotonic clock reads (engine_miniaudio.c), so a
 * duration here is what the DEVICE's callback thread actually spent, and an
 * entry-to-entry gap is what the DEVICE actually experienced.
 *
 * THE UNIT IS A PERIOD SERVICE, NOT A CALLBACK. miniaudio's duplex loop does not
 * hand the engine one period per callback: it delivers min(capture, playback)
 * chunks, split further by the converter's stack buffer and by short readi()
 * returns, so one hardware period is typically serviced by k back-to-back
 * callbacks. Neither obvious per-callback deadline survives that:
 *
 *   - judging every callback against a FULL period under-reports badly (a
 *     callback doing a k-th of the work gets k times the deadline it needs, so a
 *     struggling device reads "all clear");
 *   - judging it against its own frames/rate over-reports just as badly, because
 *     le_engine_process has a fixed per-block cost — the command drain, the
 *     per-lane and per-monitor snapshot loops, the metering publish — that does
 *     NOT shrink with the block. A 16-frame tail block would be given 166 us for
 *     overhead a 64-frame block absorbs inside 666 us, and would land in the
 *     over-budget bucket every single time on perfectly healthy hardware.
 *
 * So consecutive callbacks are summed until they cover at least one nominal
 * period, and THAT total is judged against the frames it actually covered. The
 * fixed overhead is amortised over a real period by construction, which is also
 * the true deadline: the work for one period must fit inside one period. calls
 * stays as raw context (how many callbacks made up those services).
 *
 * budget_us is the nominal period deadline, buffer_frames / sample_rate — a
 * constant for the device session, and what the gap detector is measured
 * against.
 *
 * TWO WINDOWS, because the bug being hunted (#722: clicks ONLY while a
 * performance capture is armed) is a comparison, not an absolute: `session`
 * accumulates for the whole device session (reset per configure/start, exactly
 * like xrun_count), `armed` is reset by every le_perf_arm and so covers only
 * the armed window. "Unarmed" is read as the difference of the counts; the two
 * maxima are reported separately because a maximum cannot be subtracted.
 *
 * ON HEALTHY HARDWARE EVERY JUDGED FIELD READS ZERO: late_periods, gap_events,
 * max_gap_us and xruns are all 0, and the histogram sits in the low buckets.
 * That is a deliberate design constraint — an instrument that cries wolf on a
 * working rig is worse than no instrument, because the bench then chases it. */

/* Duration-histogram resolution. Bucket i counts period services whose total
 * duration fell in [i/8, (i+1)/8) of the deadline for the frames they covered;
 * the last bucket is the open-ended ">= 7/8" danger zone and therefore also
 * holds every over-budget service (which `late_periods` counts exactly). A
 * histogram distinguishes "one huge stall" from "many marginal ones" — the two
 * have completely different causes. */
#define LE_CB_BUCKETS 8

/* Dropout classes counted per window. The three ALSA ones come from the direct
 * ALSA duplex path (miniaudio's -EPIPE recoveries and the playback-slip resync);
 * OVERLOAD is the Windows ASIO driver's kAsioOverload notification. */
typedef enum le_xrun_kind {
  LE_XRUN_PLAYBACK_UNDERRUN = 0, /* writei() -EPIPE: the card ran out of audio */
  LE_XRUN_CAPTURE_OVERRUN = 1,   /* readi()  -EPIPE: we did not read in time */
  LE_XRUN_PLAYBACK_RESYNC = 2,   /* the slipped-playback drop+prepare resync */
  LE_XRUN_BACKEND_OVERLOAD = 3,  /* ASIO kAsioOverload */
} le_xrun_kind;

/* How many le_xrun_kind values there are — the per-window tally array width.
 * A macro rather than a trailing enum member so the enum stays free of a
 * sentinel that is not a kind (it crosses the FFI boundary as a Dart enum). */
#define LE_XRUN_KINDS 4

/* One accumulation window of callback telemetry. Every counter is monotonic
 * within its window and is only ever cleared by the event that owns the window
 * (a fresh configure/start for the session window; le_perf_arm for the armed
 * one). Counts are 64-bit throughout — a 32-bit histogram bucket at ~1500
 * callbacks/second wraps inside a month, and this has to stay readable on an
 * appliance that has been up since the last OTA. Durations are microseconds: a
 * nanosecond figure would overflow uint32 after 4.3 s and nothing here is finer
 * than a microsecond anyway. */
typedef struct le_cb_window_snapshot {
  uint64_t calls;   /* device callbacks observed — raw context, never judged */
  uint64_t periods; /* period services completed (see the note above) */
  /* Services whose summed duration exceeded the deadline for the frames they
   * covered: the engine did not finish a period's work inside a period. THE
   * number to read — this is what a dropout is made of. */
  uint64_t late_periods;
  /* Entry-to-entry gaps longer than 1.5 NOMINAL PERIODS: the DERIVED
   * "the callback did not come back on time" signal, and the only one
   * available on CoreAudio, where miniaudio exposes nothing.
   *
   * WHAT IT CAN AND CANNOT DISTINGUISH. An entry-to-entry span contains the
   * previous callback's OWN duration, so a gap event says the callback stream
   * stalled — not whose fault it was. Two different causes reach it:
   *   - the device starved us: we returned promptly and it still came back
   *     late. Then `late_periods` stays flat and this moves alone, which is the
   *     reading the bench table is built on;
   *   - WE ran long: any single callback taking more than 1.5 nominal periods
   *     forces a gap event on the next entry by arithmetic alone. So this is
   *     NOT independent of `late_periods` — a badly overloaded engine moves
   *     both, and the pair moving together means "we were slow", not "two
   *     separate problems". (A merely late period service is not enough: the
   *     threshold is per-callback spacing, and a service is often several
   *     callbacks. It takes one callback past 1.5 periods.)
   * Read the two TOGETHER, never this one alone.
   *
   * Measured against the nominal period and NOT against the last block's
   * budget: on the split duplex loop the callbacks for one period arrive in a
   * burst and are then followed by a normal ~one-period wait, so a threshold
   * scaled to a sub-period block would fire at every single period boundary on
   * completely healthy hardware.
   *
   * NOT double-counted against `xruns`: an ALSA -EPIPE recovery also stalls the
   * loop, so a gap arriving within a few periods of a counted recovery is
   * suppressed. One physical dropout is counted once, under one name, and
   * max_gap_us is never pinned by a recovery stall — while a genuine stall
   * later in the session still registers. The suppressor excuses BACKEND
   * recoveries only; it does not excuse our own overrun, which is why the
   * coupling above is real and documented rather than filtered away. A device
   * reroute or a system audio interruption breaks the timeline instead of
   * producing a gap, so switching the default device mid-session reads 0. */
  uint64_t gap_events;
  uint32_t max_us;     /* worst period-service duration seen */
  uint32_t mean_us;    /* mean period-service duration over `periods` */
  uint32_t max_gap_us; /* worst counted gap (0 when none exceeded) */
  uint64_t buckets[LE_CB_BUCKETS]; /* service histogram; see LE_CB_BUCKETS */
  /* Real backend dropouts, indexed by le_xrun_kind: the per-class breakdown of
   * the flat xrun_count on le_snapshot.
   *
   * Over the session window these sum to xrun_count for every kind THIS BUILD
   * KNOWS — which is every kind any shipping backend produces (ALSA passes
   * 0/1/2, ASIO passes 3), so the sum holds today. It is not an invariant for
   * all time: a dropout reported with a kind outside le_xrun_kind increments
   * xrun_count but lands in no bucket, deliberately, because the headline
   * number's job is "a real dropout happened" and an unclassifiable one still
   * happened. Folding it into an existing bucket instead would corrupt the
   * breakdown; dropping it entirely would under-report reality. */
  uint64_t xruns[LE_XRUN_KINDS];
} le_cb_window_snapshot;

/* The whole instrument, read through le_engine_get_callback_telemetry.
 *
 * Deliberately NOT part of le_snapshot. These counters move on every audio
 * callback, and le_snapshot is projected at render rate into a value object
 * whose equality drives the app's rebuild dedupe — carrying them there would
 * make every projection unequal to the last and rebuild an idle rig
 * continuously, which is CPU pressure invented by the instrument that exists to
 * find CPU pressure. This is a pull for a bench or a diagnostics screen, and it
 * has no side effects (unlike le_engine_get_snapshot, which also drains the
 * engine's event ring). */
typedef struct le_callback_telemetry {
  /* The nominal period deadline in microseconds: buffer_frames / sample_rate.
   * 0 = no device has been opened, which is also the "inert" state in which
   * nothing at all is accumulated. */
  uint32_t budget_us;
  le_cb_window_snapshot session; /* since the device started */
  le_cb_window_snapshot armed;   /* since the most recent le_perf_arm */
} le_callback_telemetry;

/* Lock-free snapshot of engine state, published by the audio thread and read by
 * Dart on a render-rate timer. Fields are individually atomic; readers may see
 * a one-frame-stale mix across fields, which is fine for metering/UI. */
typedef struct le_snapshot {
  int32_t running;            /* 0/1: device is open and the callback is live */
  /* 0/1: the pinned (or default) device is currently present. DISTINCT from
   * `running`: a device can be lost (device_present == 0) while the engine
   * object still "runs" until it is restarted. Set from the RT-adjacent device
   * notification callback; the Dart layer derives a higher-level isConnected
   * from it and drives any reconnection (no reconnection happens in native). */
  int32_t device_present;
  int32_t sample_rate;
  int32_t buffer_frames;
  int32_t input_channels;     /* negotiated hardware capture channels */
  int32_t output_channels;    /* negotiated hardware playback channels */
  /* Bitmask of input channels excluded from recording/monitoring/routing
   * because their hardware (Core Audio) label matches "loopback". Such channels
   * are skipped in the capture average and in monitoring, and are stripped from
   * any track input mask. Always 0 off macOS / when no label matches. */
  uint32_t excluded_input_mask;
  uint64_t frames_processed;  /* total frames seen by the callback */
  /* Device dropouts (xruns) since the device started, as reported by the
   * backend, every class summed. The Windows ASIO backend tallies the driver's
   * kAsioOverload notifications; the direct ALSA path tallies miniaudio's
   * -EPIPE recoveries and its slipped-playback resyncs (#722), so this finally
   * moves on Linux. Still 0 on CoreAudio, which exposes no xrun signal at all —
   * read le_callback_telemetry's gap detector there. The per-class breakdown is
   * le_cb_window_snapshot.xruns; see its note for how the two relate.
   * Monotonic; cleared on each fresh start. */
  uint32_t xrun_count;
  float input_rms;            /* 0..1 */
  float input_peak;           /* 0..1 */
  float output_rms;           /* 0..1 */
  int32_t latency_state;      /* le_latency_state */
  double measured_latency_ms; /* valid when latency_state == LE_LATENCY_DONE */

  /* Looper transport (free mode: the first finalized recording sets the one
   * master loop length; everything else plays/overdubs against it). */
  int32_t master_length_frames;   /* 0 until the first recording is finalized */
  int32_t master_position_frames; /* current loop playhead */

  /* Record-offset latency compensation (frames). Recorded/overdubbed input is
   * written this many frames earlier in the loop so it aligns with what the
   * player heard. Auto-set by a latency measurement; manually overridable. */
  int32_t record_offset_frames;

  /* Added latency (frames) of the highest-latency effect active in any audible
   * or monitored lane chain — the MAXIMUM across active effects, so it stays
   * forward-compatible as effects accrue. Today the formant-preserving octaver
   * is the only contributor (~LE_PV_N frames; both PV and PSOLA modes report the
   * same value); every other effect adds 0, so this reads 0 whenever no octaver
   * is engaged. The Dart layer divides by sample_rate to show milliseconds and
   * warn a performer monitoring through the octaver. PURELY informational: this
   * does NOT feed record_offset_frames or any compensation — it only surfaces
   * the lag so the UI can suggest the lower-latency choice. */
  int32_t fx_added_latency_frames;

  /* Global master output gain (0..1) applied post-mix to the final output, after
   * every track/lane/monitor lane has summed in. 1.0 (unity) by default and on
   * every fresh configure. Set via le_engine_set_master_gain. */
  float master_gain;

  /* le_audio_backend actually running (negotiated). On Windows this is always
   * ASIO; on macOS/Linux it is the miniaudio backend. */
  int32_t active_backend;

  /* Structural output gate, one bit per hardware output channel (bit c => output
   * c is ENABLED). A disabled output is removed as a mix target — skipped in the
   * fan-out regardless of any lane/monitor mask pointing at it — while its stored
   * route masks are preserved (turning it back on restores them). Default: all
   * enabled (every bit in [0, output_channels) set) on a fresh configure, so the
   * absence of any gate is "all outputs on". Outputs beyond the device channel
   * count are reported enabled but never sounded. Set via
   * le_engine_set_output_enabled. */
  uint32_t output_enabled_mask;

  /* Performance-recording capture (le_perf_arm / le_perf_disarm). No separate
   * status ABI — these three atomics are the whole surface for this slice
   * (part 2 adds file-drain progress alongside them). */
  int32_t perf_armed;      /* 0/1: the RT taps are live */
  uint64_t perf_frames;    /* frames processed since the most recent arm */
  uint32_t perf_overruns;  /* dropped capture frames (ring full) since arm */
  /* Frames of digital silence the drain thread SUBSTITUTED into the capture
   * files since arm, because the audio they should have held never reached
   * it, summed over every file it writes (master + each monitored input).
   * A superset of perf_overruns' consequences: every dropped frame is
   * zero-filled, but a zero-fill can also come from audio that was counted
   * (perf_frames) yet never tapped. Read it as zero vs non-zero: non-zero
   * means the take contains silence the performer did not play -- #710's
   * audible flickers -- so the app latches it into the capture's glitch
   * flag exactly like perf_overruns. The per-gap positions stay in the
   * sidecar's `overrun_gaps`; this is the never-saturating total. */
  uint64_t perf_zero_filled_frames;
  /* 0/1: the drain thread stopped ITSELF because a write failed -- disk full,
   * a quota, a read-only remount, an I/O error. Published here because the
   * stop was otherwise invisible to the app: the thread stopped, the capture
   * stayed "armed", its handles stayed open, and finalize never ran, leaving
   * raw .pcm that was not even recoverable (#640, #652). Latches for the life
   * of the capture; cleared by the next arm. */
  int32_t perf_stopped;

  /* ---- Chromatic tuner (le_engine_set_tuner_input) ----
   *
   * Placed with the other metering floats rather than at the struct tail
   * because the trailing block below documents itself as offset-stable for
   * readers built against the older layout, and these are new fields on a
   * struct that is rebuilt from the header on every generation — the Dart
   * binding is generated, so there is no hand-written reader to keep. */
  float tuner_hz;         /* detected fundamental; 0 = no pitch this frame */
  float tuner_confidence; /* 0..1, YIN's voicing score for that frame */
  /* Echo of the armed channel, -1 when disarmed. Earns its place: without it
   * the UI cannot tell "armed and silent" from "not armed yet", and those two
   * need different words on screen. */
  int32_t tuner_input;
  /* Inputs whose live monitors the tuner is silencing (bit c = input c); 0
   * whenever the tuner is disarmed. Persistent monitor mute is separate and
   * unaffected (le_engine_set_monitor_input_mute). */
  uint32_t tuner_mute_mask;

  /* Tracks. */
  int32_t track_count; /* number of usable tracks (<= LE_MAX_TRACKS) */
  le_track_snapshot tracks[LE_MAX_TRACKS];

  /* ---- tempo grid (trailing on purpose: every pre-existing field keeps its
   * offset, so a reader built against the old layout still reads correctly).
   * All default to grid-off values; with no tempo ever set and quantize off,
   * the engine's behavior is identical to the tempo-free build. */
  float tempo_bpm;      /* denominator-note beats per minute; 0 = unset */
  int32_t ts_num;       /* time-signature numerator (default 4) */
  int32_t ts_den;       /* time-signature denominator, 4 or 8 (default 4) */
  int32_t sync_tempo;   /* 0/1: loop<->grid sync on finalize (default 1) */
  int32_t quantize_div; /* le_grid_div granularity (default 0 = off) */
  int32_t tempo_source; /* le_tempo_source (default 0 = none) */
  /* Whole bars in the master loop, or 0 when no grid relationship exists
   * (sync off, no loop, or the loop predates any grid) or the grid's beats
   * do not make whole bars (loop_beats, #1168). The loop's AUDIO length is
   * never altered by the grid — bars is a derived count. */
  int32_t loop_bars;
  int32_t current_beat; /* 0..ts_num-1 within the bar: loop-driven, or driven
                         * by the count-in / free-running click; 0 idle */

  /* ---- click + count-in (A2; trailing for the same offset-stability reason
   * as the tempo block above). All default to click-off values: mode off,
   * mask 0 (unrouted), volume 1, count-in 0 bars — the untouched engine is
   * bit-identical to the click-free build. */
  int32_t click_mode;   /* le_click_mode (default 0 = off) */
  /* Exact command receipt: acquire commands_settled BEFORE a synchronous
   * snapshot read; do not admit another mode write until the read completes.
   * Revision advances on callback acceptance/refusal, including same-value
   * requests. It resets on configure; the actual mode survives configure. */
  uint32_t click_mode_revision;
  int32_t click_mode_result; /* LE_OK or LE_ERR_INVALID; prior mode on refusal */
  uint32_t click_mask;  /* click output bitmask (default 0 = no outputs) */
  float click_volume;   /* 0..LE_MAX_GAIN (default 1); the click's only gain */
  int32_t count_in_bars; /* count-in length in measures; 0 = off (default) */
  uint32_t record_start_revision;
  int32_t record_start_result; /* prior pair remains on callback refusal */
  int32_t counting_in;   /* 0/1: a count-in is currently running */
  /* Beat countdown while counting in: the number of count-in beats still to
   * come, INCLUSIVE of the one currently sounding (a one-bar 4/4 count-in
   * reads 4, 3, 2, 1, then 0 as the recording starts). 0 when idle. */
  int32_t count_in_beats_left;

  /* ---- looper mode (B2a, D4; trailing for the same offset-stability reason
   * as the tempo/click blocks above). Default MULTI (0) — an untouched
   * engine's mode reads MULTI, today's behavior. See le_looper_mode's doc for
   * the content-lock gate and what each value means. */
  int32_t looper_mode; /* le_looper_mode (default 0 = MULTI) */

  /* ---- primary track (B3, D18 as revised by the accepted design; trailing
   * for the same offset-stability reason as the blocks above). -1 = none
   * (default, and again whenever every track is empty). The engine crowns
   * the FIRST COMPLETED TAKE while nothing is crowned; an explicit re-crown
   * (le_engine_crown_primary) is the timing handoff. The designation
   * survives the primary alone being cleared/undone-to-empty while a sibling
   * still holds audio (so its re-record re-establishes it), and dies with
   * the last take. Every mode publishes it; it only GATES timing in
   * Sync/Band (see le_sync_quantize_active). */
  int32_t primary_track;

  /* ---- MIDI clock send (Phase C, D15; trailing for the same
   * offset-stability reason as the blocks above). 0/1; default 0, so an
   * untouched engine emits no clock bytes. See le_engine_set_clock_send. */
  int32_t clock_send;

  /* ---- input clip detector + conditioning activity (input clip, S2;
   * trailing for the same offset-stability reason as the blocks above).
   * Both default to 0 — an untouched engine reports no HOT input and no
   * active conditioning. */
  /* Bit c: HOT — a rail-run (LE_CLIP_RUN consecutive raw samples at
   * |s| >= LE_CLIP_LEVEL) was seen on input c within the last
   * LE_CLIP_HOLD_MS of processed audio. Detected on the RAW device buffer,
   * so the flag reflects the ADC even when the conditioning stage has ducked
   * or notched what records. Loopback-excluded inputs never flag. */
  uint32_t input_clip_mask;
  /* Bit c: input c's conditioning stage is currently ACTIVE — enabled AND
   * not loopback-excluded, i.e. the stage actually runs on the audio path
   * (the UI truth for a "conditioning on" badge; a stage enabled on an
   * excluded channel reads 0 here because it never runs). */
  uint32_t input_cond_mask;
  /* Trailing (accepted design, slice 1): the master bus's absolute peak over
   * the most recent block, 0..1 (1.0 = full scale), read AFTER the master
   * gain and limiter — what actually reaches the outputs. Sums can clip when
   * no single track does, so the stage footer meters this rather than the
   * per-track peaks. Sibling of output_rms above. */
  float output_peak;
  /* ---- record start settings (accepted design, slice 2b; trailing).
   * Quantize is the control-side gate; auto_record and count_in_bars are
   * decoded together from the callback's applied recording-start choice.
   * le_engine_set_record_start publishes the exclusive pair together. */
  int32_t quantize;    /* 0/1: the global loop-grid record quantize gate */
  int32_t auto_record; /* 0/1: sound-activated record start */
  float overdub_feedback; /* the global coefficient, 0..1 (default 1) */
  /* ---- per-channel meters and capture trim (accepted design, slice 3;
   * trailing). Absolute block peaks may exceed unity; they are not clamped.
   * input_peaks[c] is input c's RAW device level (before conditioning and
   * trim, like input_clip_mask, so a hot ADC reads hot however the trim is
   * set); monitor_peaks[c] is its post-chain/gain/pan stereo peak BEFORE
   * output folding (0 while off, muted or without an enabled route).
   * output_peaks[c] follows master gain/limiter but EXCLUDES click.
   * input_trim[c] is the capture gain le_engine_set_input_trim holds
   * (linear, default 1). Indexed by source; device entries past the
   * device's channel count read 0 (trim 1). Instrument sources (#1197,
   * LE_INSTRUMENT_SOURCE_BASE + k) report their bus's block peak as the
   * input peak and a trim of 1. */
  float input_peaks[LE_MAX_SOURCES];
  float monitor_peaks[LE_MAX_SOURCES];
  float output_peaks[LE_MAX_CHANNELS];
  float input_trim[LE_MAX_SOURCES];
  uint32_t mix_revision; /* last wholly applied mix transaction */
  /* ---- output buses (slice 3b; trailing). output_bus_count is how many
   * the device has ((output_channels + 1) / 2); entries past it read the
   * defaults. */
  int32_t output_bus_count;
  float output_level[LE_MAX_OUTPUT_BUSES];   /* 0..1, default 1 */
  int32_t output_muted[LE_MAX_OUTPUT_BUSES]; /* 0/1 */
  int32_t output_mono[LE_MAX_OUTPUT_BUSES];  /* 0/1 */
  float output_balance[LE_MAX_OUTPUT_BUSES]; /* -1..1 */
  /* Advances on every Cut all sound the audio thread applied. */
  uint32_t tail_reset_rev;
  /* The capture policy of the armed take (1 = Follow output volume), or the
   * policy the next arm would freeze while not armed. */
  int32_t perf_follow_output;
  /* The output bus the armed take captures (the first bus with an enabled
   * channel at arm), or the one the next arm would capture; -1 when no
   * output is enabled. The offline render replays this bus's level and
   * mute under Follow output volume. */
  int32_t perf_capture_bus;
  float perf_output_level;
  int32_t perf_output_muted;
  uint32_t perf_capture_mask;
  uint32_t perf_output_enabled_mask;
  /* NOTE: the audio-callback telemetry (#722) is deliberately NOT here — see
   * le_callback_telemetry and le_engine_get_callback_telemetry. */
  /* One coherent applied timing tuple, never producer desired state. */
  uint32_t record_timing_revision;
  int32_t record_timing_result;
  int32_t record_timing_overrides[LE_MAX_TRACKS];
  /* ---- Instruments (#1197; trailing) ----
   * instrument_patch[k]: the patch slot k plays (-1: none), as applied by the
   * callback. instrument_voices[k]: its sounding voices (held or releasing,
   * not fading). instrument_peaks[k]: the block peak of its bus.
   * voice_limit: the sounding-voice limit in force. voices_stolen /
   * voices_stolen_hard: voices taken for new notes with a fade / without
   * one (no room). synth_epoch: bumped whenever the synth is re-initialised
   * (configure, reopen); every voice and latch is gone after a change.
   * instrument_events_refused: note-ons refused because the event ring was
   * full. instrument_fallback_blocks: blocks larger than the bus scratch,
   * which render no instrument audio. */
  int32_t instrument_patch[LE_MAX_INSTRUMENTS];
  int32_t instrument_voices[LE_MAX_INSTRUMENTS];
  float instrument_peaks[LE_MAX_INSTRUMENTS];
  int32_t voice_limit;
  uint32_t voices_stolen;
  uint32_t voices_stolen_hard;
  uint32_t synth_epoch;
  uint32_t instrument_events_refused;
  uint32_t instrument_fallback_blocks;
  /* sustain contributors refused because an instrument already had
   * LE_SYNTH_SUSTAIN_MAX (16) (#1197 Part 2c) */
  uint32_t instrument_sustain_refused;
  /* ---- native MIDI input (#1228 Part 1; trailing). Totals across all
   * LE_MAX_MIDI_PORTS ports since the engine was created: events delivered
   * from the current binding, events dropped as stale (pushed by a binding
   * that has since ended), gaps (places where a full ring or an OS overrun
   * lost messages), ports that went lost, and binding changes (an attach,
   * detach, rebind or close, counted once per drain that sees the
   * generation move). midi_in_attached_mask has bit p set while a capture is
   * attached to p. */
  uint32_t midi_in_events;
  uint32_t midi_in_stale;
  uint32_t midi_in_overflows;
  uint32_t midi_in_lost;
  uint32_t midi_in_attached_mask;
  uint32_t midi_in_rebinds;
  /* Trailing (#1179): the global Speed the callback applies, as
   * numer/denom (1/2, 1/1, 2/1, 4/1 or 8/1; 1/1 before any request). */
  int32_t speed_numer;
  int32_t speed_denom;
  /* Trailing (#1179 Part 3a): 1 while Transpose is bypassed globally. */
  int32_t transpose_bypass;
  /* Seconds each capture ring of the most recent take was granted
   * (le_perf_target.ring_seconds after the memory cap); 0 before any arm. */
  int32_t perf_ring_seconds;
  /* ---- performance take accounting (#1198; trailing) ---- */
  /* Why the most recent take stopped: an le_perf_stop_reason, NONE while it
   * runs. Survives disarm; reset by the next arm. */
  int32_t perf_stop_reason;
  /* Bytes the drain has written for the take: part headers and samples,
   * events.log and layer files. */
  uint64_t perf_bytes_written;
  /* The first capture frame a ring could not take, or UINT64_MAX. A take
   * that drops a frame ends there (LE_PERF_STOP_SLOW_STORAGE). Neither this
   * nor perf_overruns moves once the take has stopped: a full ring after a
   * stop is not part of the take. */
  uint64_t perf_first_drop_frame;
  /* Samples above full scale (|x| > 1.0) across every stream so far. */
  uint64_t perf_overs;
  /* The streams the armed take captures (or the next arm would: the first
   * enabled output pair plus every monitored input the device has), and the
   * bytes one frame of all of them takes, so the app can tell whether a
   * volume holds a minimum take of every stream before it arms. 0 when
   * nothing could be captured. */
  int32_t perf_capture_streams;
  uint32_t perf_capture_frame_bytes;
  /* Checkpoints of the most recent take that could not be written (a failed
   * sync or slot write); each leaves the other slot standing and the take
   * running. Reset by the next arm. */
  uint32_t perf_checkpoint_failures;
  /* Trailing (#1168): whole beats (denominator notes) in the master loop, the
   * grid's own count, or 0 with no grid. loop_bars * ts_num when the loop is
   * whole bars; a Divide of a sole 1- or 3-bar loop keeps the tempo and
   * leaves 2 or 6 beats with loop_bars 0. */
  int32_t loop_beats;
  /* ---- MIDI clock sync (#1228 Part 2; trailing). clock_state is an
   * le_clock_state; clock_source_port is -1 for Internal. clock_bpm is the
   * external tempo for display (0.1 BPM steps with hysteresis, Segno's
   * denominator-note unit; the last value is kept while LOST, 0 before the
   * first acquisition). clock_out_of_range is 1 while a steady clock lies
   * outside 30..300 BPM in the current signature. clock_pulses counts every
   * pulse received or recognised as missed since the source was selected
   * (low 32 bits). clock_receipt is the sequence of the last applied
   * le_engine_set_clock_sync, clock_result its outcome (LE_OK or
   * LE_ERR_SYNC_LOCKED). clock_losses counts Synced -> Lost transitions. */
  int32_t clock_state;
  int32_t clock_source_port;
  int32_t clock_follow_transport;
  int32_t clock_loss_policy;
  float clock_bpm;
  int32_t clock_out_of_range;
  uint32_t clock_pulses;
  uint32_t clock_receipt;
  int32_t clock_result;
  uint32_t clock_losses;
  /* Trailing (#1179 Part 4a): the tempo the takes were recorded at (0 with
   * no master), the Follow tempo default every track inherits (0 = keep the
   * recorded speed), and what a song-tempo change does now
   * (le_tempo_follow_state). */
  float recorded_tempo_bpm;
  int32_t follow_tempo;
  int32_t tempo_follow;
  /* Trailing (#1179 Part 4a-ii): the Pitch default every track inherits
   * (0 Unchanged, the default; 1 Follows speed). */
  int32_t pitch_follows_speed;
  /* Trailing (#1179 Part 4b): the master length recorded_tempo_bpm
   * measured (0 with none). A Session saves the pair, so a recall commits
   * the takes at the tempo they were laid down at and retimes from there. */
  int32_t recorded_length_frames;
} le_snapshot;

/* What a song-tempo change does now (le_snapshot.tempo_follow, #1179 Part
 * 4a). With no content the tempo is free. With content it retimes the shared
 * clock only on a bar grid (Multi, Sync or Band with a tempo) with at least
 * one track following, and never while a track records, overdubs, is armed
 * or launching, or a count-in runs. */
typedef enum le_tempo_follow_state {
  LE_TEMPO_FOLLOW_FREE = 0,        /* no content: the tempo changes freely */
  LE_TEMPO_FOLLOW_RETIMES = 1,     /* a change retimes the recorded tracks */
  LE_TEMPO_FOLLOW_NO_GRID = 2,     /* locked: no bar grid to follow */
  LE_TEMPO_FOLLOW_NO_FOLLOWER = 3, /* locked: no track follows the tempo */
  LE_TEMPO_FOLLOW_BUSY = 4,        /* locked while capture, arm or count-in */
} le_tempo_follow_state;

/* ============================ Plugin hosting ==============================
 * Discovery of installed VST3 / CLAP audio-effect plugins. This first slice is
 * SCAN ONLY: no plugin is loaded into the audio graph, no audio thread is
 * touched. The whole surface runs on the control thread and an engine-owned
 * dedicated scan thread (see le_plugin_scan_begin) — never the audio callback.
 *
 * The hosting backends are compiled only in a SEGNO_ENABLE_PLUGINS build (macOS
 * today); other builds link a stub that reports "no plugins" so the symbols
 * always resolve over FFI. */

/* The plugin format a descriptor was discovered in. */
typedef enum le_plugin_format {
  LE_PLUGIN_VST3 = 0,
  LE_PLUGIN_CLAP = 1,
} le_plugin_format;

/* One discovered plugin class. Fixed-size POD so it round-trips over FFI like
 * le_device_info. A *failed* candidate (a file that could not be loaded or
 * described) is reported as an entry with an EMPTY `id` and `name`/`path` set to
 * the offending file, so a single broken plugin surfaces in the list instead of
 * aborting the scan (umbrella D-SCAN). The Dart layer treats `id == ""` as the
 * unavailable/failed marker. */
typedef struct le_plugin_desc {
  char id[256];    /* VST3 TUID as 32 hex chars / CLAP descriptor id — stable
                    * identity. Empty for a failed-to-scan entry. */
  char name[128];
  char vendor[128];
  char path[1024]; /* the .vst3 bundle / .clap file the class lives in */
  int32_t format;  /* le_plugin_format */
  uint32_t version; /* packed major<<16 | minor<<8 | patch, parsed from the
                     * plugin's version string (0 if unknown) */
} le_plugin_desc;

/* Opaque engine handle. */


LE_EXPORT int32_t le_engine_set_mix(le_engine* engine,
                                    const le_mix_settings* settings);
LE_EXPORT int32_t le_engine_record_with_image(le_engine* engine, int32_t channel,
                                              const le_record_image* image);

/* Returns the miniaudio + engine version string (never NULL). */
LE_EXPORT const char* le_version(void);

/* Detects a cable-free loopback capture path (PulseAudio monitor / virtual
 * driver / backend built-in loopback) by enumerating capture devices. Fills
 * *out and returns LE_OK, or LE_ERR_INVALID for a null argument / enumeration
 * failure. */
LE_EXPORT int32_t le_detect_loopback(le_loopback_info* out);

/* Enumerates the host's playback (output) devices into `out`, a caller-allocated
 * array with room for `max` entries, and writes the number filled into *count
 * (clamped to `max`). Returns LE_OK, or LE_ERR_INVALID for a null argument,
 * non-positive `max`, or an enumeration failure. Uses a transient ma_context, so
 * it is safe to call while an engine is already started. */
LE_EXPORT int32_t le_enumerate_playback_devices(le_device_info* out, int32_t max,
                                                int32_t* count);

/* Like le_enumerate_playback_devices but for capture (input) devices. */
LE_EXPORT int32_t le_enumerate_capture_devices(le_device_info* out, int32_t max,
                                               int32_t* count);

/* Reserved: always writes *count = 0 and returns LE_OK. ASIO was the Windows
 * duplex backend and went with the desktop targets; the symbol stays exported so
 * the Dart layer can keep calling it unconditionally. Returns LE_ERR_INVALID for
 * a null argument / non-positive `max`. */
LE_EXPORT int32_t le_enumerate_asio_drivers(le_device_info* out, int32_t max,
                                            int32_t* count);

/* ---- Plugin scanning (control thread; runs on a dedicated scan thread) ----
 *
 * le_plugin_scan_begin spawns ONE dedicated OS scan thread (the engine has no
 * thread pool) that walks the standard VST3 / CLAP install locations and loads
 * each candidate under a per-candidate guard, so one broken plugin yields a
 * "failed" entry rather than aborting the scan (D-SCAN). Dart polls
 * le_plugin_scan_poll on a timer and reads finished entries with
 * le_plugin_scan_get. The scan thread never touches the audio callback, so a
 * scan is safe while the engine is running.
 *
 * Only one scan runs at a time. `rescan != 0` is a hint to ignore any native
 * caching (none in this slice — caching lives in the Dart catalog). */

/* Starts an async scan. Returns LE_OK once the scan thread is launched, or
 * LE_ERR_INVALID for a null engine, LE_ERR_ALREADY_RUNNING if a scan is already
 * in progress. */
LE_EXPORT int32_t le_plugin_scan_begin(le_engine* engine, int32_t rescan);

/* Polls scan progress. Any out-pointer may be NULL. *done is 0 while scanning,
 * 1 once the scan thread has finished (or was cancelled). *found is the number
 * of entries currently retrievable via le_plugin_scan_get (grows as the scan
 * proceeds and includes failed entries). *scanned / *total are candidate files
 * processed / discovered. Returns LE_OK, or LE_ERR_INVALID for a null engine. */
LE_EXPORT int32_t le_plugin_scan_poll(le_engine* engine, int32_t* done,
                                      int32_t* found, int32_t* scanned,
                                      int32_t* total);

/* Copies the descriptor at `index` (0-based, < the last polled *found) into
 * *out. Returns LE_OK, or LE_ERR_INVALID for a null argument / out-of-range
 * index. Safe to call during or after a scan. */
LE_EXPORT int32_t le_plugin_scan_get(le_engine* engine, int32_t index,
                                     le_plugin_desc* out);

/* Requests cancellation and joins the scan thread (blocks briefly until the
 * in-flight candidate finishes). Idempotent; safe when no scan is running.
 * Returns LE_OK, or LE_ERR_INVALID for a null engine. */
LE_EXPORT int32_t le_plugin_scan_cancel(le_engine* engine);

/* ---- Plugin slot lifecycle (control thread; D-LIFE) ----
 *
 * An opaque handle to a plugin loaded into one lane / monitor FX chain slot.
 * Valid from a successful le_engine_set_*_plugin until that slot is cleared or
 * the engine is destroyed. The heavy work — instancing, activation, buffer
 * allocation — runs on the CONTROL thread; the audio thread only ever reads an
 * atomically-published "ready" flag and forwards samples. No plugin is ever
 * created, destroyed, or dylib-loaded on the audio callback. */


/* Loads the plugin identified by `plugin_id` (a scanned le_plugin_desc.id) into
 * FX chain slot `index` of a lane (channel, lane) or a monitor input. The load
 * + activate happen here on the control thread, BYPASSED, then the slot is
 * atomically published so the audio thread begins forwarding to it; until ready
 * the slot renders dry passthrough (no click). On success the chain entry's type
 * becomes LE_FX_PLUGIN and *out_slot receives the handle. The entry is activated
 * in the chain the same way as a built-in, via le_engine_set_lane_fx_count /
 * le_engine_set_monitor_input_fx_count. Returns LE_OK, LE_ERR_INVALID for a bad
 * argument / unknown plugin_id, or LE_ERR_DEVICE on a plugin load/activate
 * failure. (out_slot may be NULL if the caller does not need the handle.) */
LE_EXPORT int32_t le_engine_set_lane_plugin(le_engine* engine, int32_t channel,
                                            int32_t lane, int32_t index,
                                            const char* plugin_id,
                                            le_plugin_slot** out_slot);
LE_EXPORT int32_t le_engine_set_monitor_plugin(le_engine* engine, int32_t input,
                                               int32_t index,
                                               const char* plugin_id,
                                               le_plugin_slot** out_slot);

/* Clears a plugin slot: the audio thread is signalled to stop forwarding to it,
 * and the host is destroyed on the control thread only AFTER a published-
 * quiescent handshake (so there is never a use-after-free or an audio-thread
 * free). The chain entry returns to LE_FX_NONE. Idempotent on an empty slot.
 * Returns LE_OK or LE_ERR_INVALID. */
LE_EXPORT int32_t le_engine_clear_lane_plugin(le_engine* engine, int32_t channel,
                                              int32_t lane, int32_t index);
LE_EXPORT int32_t le_engine_clear_monitor_plugin(le_engine* engine,
                                                 int32_t input, int32_t index);

/* ---- Plugin parameters (control thread; D-PARAM) ----
 *
 * A plugin's parameters are a VARIABLE-LENGTH list sourced live from the plugin
 * — separate from the built-in fixed 4-float LE_FX_PARAMS surface, which is left
 * untouched. Values are PLAIN (not normalized): VST3's normalized params are
 * converted via normalizedParamToPlain; CLAP params are already plain. */

/* Bit flags for le_plugin_param_info.flags. */
typedef enum le_plugin_param_flags {
  LE_PARAM_AUTOMATABLE = 1 << 0,
  LE_PARAM_READONLY = 1 << 1,
  LE_PARAM_BYPASS = 1 << 2,
  LE_PARAM_HIDDEN = 1 << 3,
  LE_PARAM_STEPPED = 1 << 4,
} le_plugin_param_flags;

/* One plugin parameter's metadata. Fixed-size POD for FFI, like le_plugin_desc. */
typedef struct le_plugin_param_info {
  uint32_t id;        /* stable param id (VST3 ParamID / CLAP clap_id) */
  char name[128];
  char unit[32];
  double min;
  double max;
  double def;         /* default plain value */
  int32_t step_count; /* 0 = continuous; >0 = discrete steps */
  uint32_t flags;     /* le_plugin_param_flags bitmask */
} le_plugin_param_info;

/* The number of parameters the plugin in `slot` exposes. Returns LE_OK, or
 * LE_ERR_INVALID for a null argument. */
LE_EXPORT int32_t le_plugin_param_count(le_plugin_slot* slot, int32_t* count);

/* Copies the metadata of the parameter at `index` (0-based, < count) into *out.
 * Returns LE_OK, or LE_ERR_INVALID for a null argument / out-of-range index. */
LE_EXPORT int32_t le_plugin_param_info_at(le_plugin_slot* slot, int32_t index,
                                          le_plugin_param_info* out);

/* Reads the current plain value of parameter `id` into *plain. Returns LE_OK,
 * or LE_ERR_INVALID for a null argument. */
LE_EXPORT int32_t le_plugin_param_get(le_plugin_slot* slot, uint32_t id,
                                      double* plain);

/* Sets parameter `id` to the plain `value`. THREAD-SAFE: enqueues onto the
 * slot's lock-free SPSC ring, drained into the SDK's own event mechanism
 * (VST3 IParameterChanges / CLAP clap_input_events) at the top of the next
 * process() — never a direct store from the audio thread (D-PARAM). Returns
 * LE_OK, or LE_ERR_INVALID for a null slot. */
LE_EXPORT int32_t le_plugin_param_set(le_plugin_slot* slot, uint32_t id,
                                      double value);

/* Formats parameter `id`'s plain `value` to the plugin's own display string
 * (e.g. "-6.0 dB", "Lowpass"), copied NUL-terminated into out[out_size]. Lets
 * the UI label discrete params and read out continuous ones in real units.
 * CONTROL THREAD. Returns LE_OK, LE_ERR_INVALID for a null argument, or
 * LE_ERR_UNSUPPORTED when the plugin offers no text for it. */
LE_EXPORT int32_t le_plugin_param_value_text(le_plugin_slot* slot, uint32_t id,
                                             double value, char* out,
                                             int32_t out_size);

/* ---- Native editor window (MAIN THREAD; macOS only) ---- */

/* Opens the plugin's own native editor in a HOST-OWNED top-level OS window
 * (D-WIN) — not embedded in the Flutter tree. Idempotent: a second call while
 * the editor is already open is a no-op success. Returns LE_OK, LE_ERR_INVALID
 * for a null slot, or LE_ERR_UNSUPPORTED when the plugin has no editor / the
 * platform view type is unsupported (or on a non-macOS build). */
LE_EXPORT int32_t le_plugin_editor_open(le_plugin_slot* slot);

/* Force-closes the editor window and detaches the plugin view (D-WIN teardown).
 * Idempotent: closing an already-closed editor is a no-op success. Returns
 * LE_OK, or LE_ERR_INVALID for a null slot. */
LE_EXPORT int32_t le_plugin_editor_close(le_plugin_slot* slot);

/* Writes 1 into *open if the editor window is currently open, else 0. Returns
 * LE_OK, or LE_ERR_INVALID for a null argument. */
LE_EXPORT int32_t le_plugin_editor_is_open(le_plugin_slot* slot, int32_t* open);

/* ---- Opaque plugin state, for session persistence (MAIN THREAD; D-P1) ---- */

/* Writes the byte size of the plugin's current opaque state into *bytes.
 * Returns LE_OK, LE_ERR_INVALID for a null argument, or LE_ERR_UNSUPPORTED when
 * the plugin exposes no state (then *bytes is 0). */
LE_EXPORT int32_t le_plugin_state_size(le_plugin_slot* slot, int32_t* bytes);

/* Captures the plugin's opaque state into `buf` (capacity `cap`), writing the
 * full byte size into *written. If `cap` is smaller than *written (or `buf` is
 * NULL), nothing is copied — the caller should retry with a buffer of at least
 * *written bytes. Returns LE_OK, LE_ERR_INVALID for a null slot/`written`, or
 * LE_ERR_UNSUPPORTED when the plugin has no state. */
LE_EXPORT int32_t le_plugin_state_get(le_plugin_slot* slot, uint8_t* buf,
                                      int32_t cap, int32_t* written);

/* Restores the plugin from an opaque state blob previously captured with
 * le_plugin_state_get. Returns LE_OK, LE_ERR_INVALID for a null slot (or null
 * `buf` with `bytes` > 0), or LE_ERR_UNSUPPORTED when the plugin rejects it. */
LE_EXPORT int32_t le_plugin_state_set(le_plugin_slot* slot, const uint8_t* buf,
                                      int32_t bytes);

/* Allocates an engine. Returns NULL on allocation failure. */
LE_EXPORT le_engine* le_engine_create(void);

/* Stops (if running) and frees the engine. Safe to call with NULL. */
LE_EXPORT void le_engine_destroy(le_engine* engine);

/* Opens the default duplex device with `config` and starts the audio callback.
 * Allocates the track buffers before the device starts. Returns LE_OK or an
 * le_result error. */
LE_EXPORT int32_t le_engine_start(le_engine* engine, const le_config* config);

/* Stops and closes the device. Returns LE_OK or an le_result error. */
LE_EXPORT int32_t le_engine_stop(le_engine* engine);

/* What le_engine_reopen did with the recorded material (#1140). */
typedef enum le_reopen_outcome {
  LE_REOPEN_RETAINED = 0,     /* loops, history, Fade kept; tracks STOPPED */
  LE_REOPEN_CLEARED_RATE = 1, /* the device negotiated another sample rate */
  LE_REOPEN_CLEARED_CAP = 2,  /* max_loop_frames differs from the buffers */
  LE_REOPEN_RETAINED_PARTIAL = 3, /* retained, except the tracks named in the
                                   * dropped mask: a Clear/Undo/Redo/cancel or
                                   * Session commit on them was still
                                   * unapplied at the loss */
} le_reopen_outcome;

/* Reopens the audio device after a loss WITHOUT discarding the recorded loops
 * (#1140). Requires a stopped (le_engine_stop) engine that was started
 * before: LE_ERR_ALREADY_RUNNING while running, LE_ERR_NOT_RUNNING when never
 * configured (a cold engine goes through le_engine_start). Opens the device
 * like le_engine_start, then — at the same negotiated sample rate and loop
 * cap — keeps every lane's PCM, the undo/redo history, loop multiples, take
 * ids and the crown, and brings each content track back STOPPED at the loop
 * head with its Fade frozen (the ramp resumes toward its target at the
 * original full-travel rate on the next Play). A take still capturing at the
 * loss is dropped: a first recording leaves its track EMPTY, an in-progress
 * overdub pass is reverted sample-exactly (committed layers stay), a take
 * still in its seam crossfade or trailing fold goes with it. Recording never
 * resumes. A track whose Clear/Undo/Redo/cancel or Session commit the audio
 * thread never applied is dropped the same way — EMPTY, its history gone —
 * and named in *dropped_track_mask (bit t = track t, NULL to not ask), with
 * *outcome LE_REOPEN_RETAINED_PARTIAL; every other track is retained. A
 * drop that empties the rig resets the master as a clear does. Only another
 * sample rate or loop cap clears the whole engine, exactly as le_engine_start
 * does, with *outcome LE_REOPEN_CLEARED_RATE / _CAP and a zero mask. A
 * running performance capture ends with DEVICE_CHANGED either way. Every
 * setting the host replays after a start (routing, mix, FX, monitors,
 * conditioning, output gates) is reset here too; routes to inputs or outputs
 * the new device lacks stay silent.
 *
 * Returns LE_OK or an le_result error. A failed open changes nothing (the
 * material is still held, still stopped, *outcome and the mask untouched), so
 * the caller may retry. A failed start returns LE_ERR_DEVICE with the material
 * already settled per *outcome — still retained and stopped on
 * LE_REOPEN_RETAINED / _PARTIAL. */
LE_EXPORT int32_t le_engine_reopen(le_engine* engine, const le_config* config,
                                   int32_t* outcome,
                                   int32_t* dropped_track_mask);

/* ---- device-free test pump ----
 *
 * The two calls a test harness needs to drive the engine deterministically
 * with NO audio device: configure the tracks/buffers, then pump blocks through
 * the same block processor the real device callback runs. Exactly how the
 * native test suite (src/test/test_engine_core.c) exercises the engine; the
 * Dart sequence fuzzer uses these through the generated bindings. NOT part of
 * the app's runtime surface — the app always goes through le_engine_start. */

/* Allocates/resets the track buffers and marks the engine configured, without
 * opening a device. `max_loop_frames <= 0` selects the default (30 s). */
LE_EXPORT int32_t le_engine_configure(le_engine* engine, int32_t sample_rate,
                                      int32_t input_channels,
                                      int32_t output_channels,
                                      int32_t max_loop_frames);

/* le_engine_reopen without the device: the retention decision, the material
 * settle and the runtime reset, on an engine le_engine_configure (or a
 * previous start) already configured. `max_loop_frames <= 0` selects the
 * default, as in le_engine_configure. Same preconditions, results, *outcome
 * values and dropped-track mask as le_engine_reopen. */
LE_EXPORT int32_t le_engine_reopen_configured(le_engine* engine,
                                              int32_t sample_rate,
                                              int32_t input_channels,
                                              int32_t output_channels,
                                              int32_t max_loop_frames,
                                              int32_t* outcome,
                                              int32_t* dropped_track_mask);

/* Flips the published device-present flag to 0 while the engine keeps
 * running — what the backend's device-lost notification does — so a host
 * driving the device-free pump can rehearse its reconnect path (a stop,
 * then le_engine_reopen_configured) without a device to unplug. */
LE_EXPORT void le_engine_mark_device_lost(le_engine* engine);

/* Processes one block exactly like the device callback: drains the command
 * ring, records/mixes `frames` frames from `input` (interleaved f32, may be
 * NULL for silence) into `output`, advances the transport, publishes
 * metering/undo events. frames == 0 still drains rings and advances the
 * per-block maintenance (the test suites' `drain` idiom). */
LE_EXPORT void le_engine_process(le_engine* engine, float* output,
                                 const float* input, uint32_t frames);

/* Copies the current state snapshot into *out. No-op if either pointer is NULL.
 */
LE_EXPORT void le_engine_get_snapshot(le_engine* engine, le_snapshot* out);

/* Copies the audio-callback telemetry (#722) into *out. No-op if either pointer
 * is NULL; a never-started engine fills zeros.
 *
 * Its own entry point rather than a block on le_snapshot, for two reasons. It
 * is a DIAGNOSTIC PULL — a bench readout, a support screen — not render-rate
 * state, and keeping it off le_snapshot is what guarantees a per-callback
 * counter can never leak into the app's projected state and defeat its rebuild
 * dedupe. And it is SIDE-EFFECT FREE: le_engine_get_snapshot also runs
 * le_engine_drain_events (collecting retired undo layers), which a diagnostic
 * read has no business triggering. Pure relaxed atomic loads; safe from the
 * control thread at any time, running or not. */
LE_EXPORT void le_engine_get_callback_telemetry(le_engine* engine,
                                                le_callback_telemetry* out);

/* Copies track `channel`'s snapshot into *out. Out-of-range channels yield an
 * empty track. No-op if either pointer is NULL. */
LE_EXPORT void le_engine_get_track(le_engine* engine, int32_t channel,
                                   le_track_snapshot* out);

/* Copies up to `max_points` of the loop waveform — peaks of the mixed output
 * indexed by position across exactly one master loop (bucket 0 = loop start),
 * each in 0..1 — into `out`; returns the number written. Pair with the
 * snapshot's master_position/master_length for the playhead. Lock-free read of
 * the audio thread's loop-visualization buffer; empty until a loop exists. */
LE_EXPORT int32_t le_engine_read_visual(le_engine* engine, float* out,
                                        int32_t max_points);

/* Copies a single track's waveform over its full recorded length (channel
 * 0..track_count-1). Pair with the track snapshot's position_frames and
 * length_frames. The shape is retained while stopped and cleared when its
 * take is removed; a first recording gains its shape as playback sweeps it. */
LE_EXPORT int32_t le_engine_read_track_visual(le_engine* engine,
                                              int32_t channel, float* out,
                                              int32_t max_points);

/* Name of the active duplex/playback device, or "" if not running. The returned
 * pointer is owned by the engine and valid until the next start/stop. */
LE_EXPORT const char* le_engine_device_name(le_engine* engine);

/* Posts a command into the engine's SPSC ring (drained by the audio thread).
 * Returns LE_OK, LE_ERR_NOT_RUNNING, or LE_ERR_INVALID (ring full / bad args).
 */
LE_EXPORT int32_t le_engine_post_command(le_engine* engine, int32_t code,
                                         int32_t arg_i, float arg_f);

/* Convenience: triggers a single loopback latency measurement. Requires an
 * output->input loopback path. */
LE_EXPORT int32_t le_engine_measure_latency(le_engine* engine);
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
