tomassasovsky/segno/packages/segno_engine/src/core/engine_commands.c

#include <math.h>
/*
 * engine_commands.c — control-thread command producers + record/undo machinery.
 *
 * THREAD OWNERSHIP: control thread (the Dart-facing FFI setters). Almost every
 * function here validates its arguments and posts a command into the SPSC ring
 * (le_push) for the audio thread to apply; the exceptions do control-thread work
 * the audio thread is guaranteed not to race — the O(1) undo/redo buffer-index
 * swaps, the shadow-slot supply + retired-layer collection (le_engine_drain_events),
 * the quantize/auto-record arm bookkeeping, and the lazy effect-buffer / lane
 * allocation in le_fx_prepare_entry / le_engine_set_lane_count.
 *
 * Undo layers are captured PER OVERDUB PASS on the audio thread (backup-on-write
 * into a pre-posted shadow slot — see engine_process.c); completed layers come
 * back through the evt_ring and are pushed onto the control-side stacks here.
 * Control mutations follow push-then-mutate: state is only changed after the
 * matching ring command was accepted, so a full ring never desyncs the two sides.
 *
 * Split verbatim out of engine.c (S1) behind the unchanged ABI. Shared helpers
 * (le_push, valid_channel, le_lanes_active, le_lane_reset)
 * come from engine_core.h; the octaver Hann init + PV sizes from engine_fx.h. The
 * matching audio-thread consumers (apply_command + handlers) are in
 * engine_process.c.
 */
#include <stdint.h>
#include <stdio.h> /* fprintf — the disarm callback-telemetry summary (#722) */
#include <stdlib.h>
#include <string.h>

#include "audio_ring.h"  /* le_audio_ring_alloc/release (capture rings) */
#include "engine_cache.h" /* le_cache_tick (wet-cache scheduler heartbeat) */
#include "engine_render.h" /* le_render_take (Bounce, #1202) */
#include "engine_restore.h" /* le_restore_tick + le_restore_commit_layer (#697) */
#include "engine_core.h" /* le_push, valid_channel, le_lanes_active, le_*_reset */
#include "engine_fx.h"   /* le_fx_ensure_hann, LE_PV_N / LE_PV_BINS */
#include "engine_private.h"
#include "engine_internal.h"
#include "layer_staging_ring.h" /* le_layer_staging_ring_push (retired-layer persistence) */
#include "segno_engine_api.h"
#include "perf_drain.h"     /* le_perf_drain_start/stop (capture-to-disk thread) */
#include "perf_log_ring.h"  /* le_perf_log_ring_push (control-side event log) */
#include "tempo_grid.h"     /* le_grid_signature_valid, le_grid_div bounds */

/* Whether the track's history is entirely erased-take material — i.e. its top
 * entry is a clear restore point, so everything on the stack belongs to a take
 * the user cleared. Such history yields to a fresh recording (it never outranks
 * one), which is what le_grid_still_needed and le_drop_clear_history rely on. */
static int le_history_is_cleared(const le_track* t) {
  return t->undo_count > 0 &&
         t->undo_stack[t->undo_count - 1].kind == LE_HIST_CLEAR;
}

/* Republishes what the host may read off a snapshot: how many overdub layers
 * undo can peel RIGHT NOW, and whether the next undo restores a cleared take.
 *
 * a_undo_depth is not the raw entry count. Its published contract is "available
 * undo steps (overdub layers)" (segno_engine_api.h), and a cleared track's
 * layers are not steps yet — they sit under a restore point and only become
 * peelable once it is undone. Publishing the raw count there would report peel
 * depth on an EMPTY track, breaking both that contract and the host's
 * EMPTY => undoDepth == 0 invariant. The restore point gets its own flag
 * instead, so "undo does something" stays answerable without conflating the two.
 *
 * The pair is stored non-atomically with respect to each other; a host reading
 * between them sees at worst a stale flag on the next poll, the same tolerance
 * every other published depth already carries. */
/* The undo-stack index of the LAYER the next Peel consumes (#1164): the
 * topmost LAYER reachable from the top through PEEL entries only, with
 * *skipped = how many PEEL entries sit above it. -1 when none is reachable —
 * the stack is empty (the live buffer is the original take), or a kind that is
 * not an overdub (CLEAR, PROCESSED) lies above the topmost LAYER. Stopping at
 * the deepest LAYER is what keeps the original take out of Peel's reach: that
 * entry IS the pre-first-overdub image, so swapping it in leaves the original
 * audible with nothing deeper to consume. */
static int le_peel_target(const le_track* t, int32_t* skipped) {
  int n = 0;
  for (int i = t->undo_count - 1; i >= 0; --i) {
    const int32_t kind = t->undo_stack[i].kind;
    if (kind == LE_HIST_LAYER) {
      *skipped = n;
      return i;
    }
    if (kind != LE_HIST_PEEL) break;
    ++n;
  }
  *skipped = 0;
  return -1;
}

static void le_publish_undo_depth(le_track* t) {
  /* A frozen take's restore point is still to be filed: the layers kept
   * beneath it are not peelable yet (the track reads EMPTY), and the restore
   * is not offered until the point lands — so both read 0 for now. */
  if (t->clear_restore_pending) {
    store_i32(&t->a_undo_depth, 0);
    store_i32(&t->a_clear_restore, 0);
    store_i32(&t->a_peel_depth, 0);
    return;
  }
  /* A command that gives the track content is in flight (a clear restore,
   * a resurrect) while the wire still reads EMPTY: hold both at 0 — an EMPTY
   * track never shows peelable layers — and republish once the audio thread
   * has applied it (le_engine_drain_events). */
  if (t->state_cmds_posted >
          atomic_load_explicit(&t->a_state_acks, memory_order_acquire) &&
      t->pending_target != LE_TRACK_EMPTY &&
      load_i32(&t->a_state) == LE_TRACK_EMPTY) {
    store_i32(&t->a_undo_depth, 0);
    store_i32(&t->a_clear_restore, 0);
    store_i32(&t->a_peel_depth, 0);
    t->depth_republish = 1;
    return;
  }
  const int cleared = le_history_is_cleared(t);
  store_i32(&t->a_undo_depth, cleared ? 0 : t->undo_count);
  store_i32(&t->a_clear_restore, cleared ? 1 : 0);
  /* A CLEAR on top already reads 0 (nothing LAYER or PEEL above it). */
  store_i32(&t->a_peel_depth, le_peel_depth(t));
}

/* The pool slot INDEX the next shadow acquisition on [t] selects, given the
 * history it will see: the first index that is neither the (shared) live index
 * nor named by the first `undo_count` / `redo_count` / `outstanding_count`
 * entries of the respective stacks. The same index names the snapshot in every
 * lane — the undo span is lockstep across lanes — so this works on the
 * track-level stacks plus lane 0's live index (all lanes share it). When every
 * index is in use, it names the slot of the oldest evictable undo entry and
 * stores that entry's stack position in *evict (else -1); -1 when nothing can
 * be freed. PURE: it evicts nothing and allocates nothing, so the capture
 * admission check in le_record_impl can preview exactly the slot the real
 * acquisition below will take, from the retained-history view that action
 * leaves behind, without a second selection policy.
 *
 * The LE_HIST_CLEAR skip is belt-and-braces, NOT a live path: a restore point
 * only sits on the undo stack while its track is EMPTY, and an EMPTY track
 * posts no dub shadows, so nothing acquires against a stack holding one. (Once
 * undone it moves to the redo stack, where the `used` scan pins its slot — and
 * a punch-in discards it via le_clear_redo before acquiring anyway.) The
 * invariant is subtle and lives in three places, so this stays: if it ever
 * breaks, degrading peel depth is survivable and recycling the erased take's
 * buffer into a live recording is not. Deliberately untested — the mutation
 * that removes it cannot be caught, because the path cannot be reached.
 *
 * PEEL and PROCESSED entries (#1164) are evictable like LAYERs: losing one
 * costs a recovery step, never audio the track plays. A redo-side PEEL marker
 * names slot -1, which the `used` scan never matches, so it pins nothing. */
static int track_select_slot(le_track* t, int undo_count, int redo_count,
                             int outstanding_count, int* evict) {
  *evict = -1;
  const int live = load_i32(&t->lanes[0].a_live);
  for (int i = 0; i < LE_POOL_SLOTS; ++i) {
    if (i == live) continue;
    /* A Bounce in flight (#1202) holds two slots no stack names yet. */
    if (t->bounce_pin[0] == i + 1 || t->bounce_pin[1] == i + 1) continue;
    int used = 0;
    for (int k = 0; k < undo_count && !used; ++k) {
      if (t->undo_stack[k].slot == i) used = 1;
    }
    for (int k = 0; k < redo_count && !used; ++k) {
      if (t->redo_stack[k].slot == i) used = 1;
    }
    for (int k = 0; k < outstanding_count && !used; ++k) {
      if (t->outstanding_slots[k] == i) used = 1;
    }
    if (!used) {
      /* Handed out for new PCM: no key names it any more (a_src_key). */
      atomic_store_explicit(&t->a_slot_key[i], 0u, memory_order_relaxed);
      return i;
    }
  }
  for (int e = 0; e < undo_count; ++e) {
    if (t->undo_stack[e].kind == LE_HIST_CLEAR) continue;
    *evict = e;
    atomic_store_explicit(&t->a_slot_key[t->undo_stack[e].slot], 0u,
                          memory_order_relaxed);
    return t->undo_stack[e].slot;
  }
  return -1;
}

/* Acquires the slot track_select_slot names for the track's current stacks.
 * If the pool is full, evicts the oldest undo entry and reuses its slot (never
 * an audio-held one) — layers are fair game: losing the deepest one costs peel
 * depth and nothing else. Returns -1 only if nothing can be freed. Allocation
 * of the slot's buffers happens per lane in le_post_dub_shadows. */
static int track_acquire_slot(le_track* t) {
  int evict;
  const int slot = track_select_slot(t, t->undo_count, t->redo_count,
                                     t->outstanding_count, &evict);
  if (evict >= 0) {
    for (int k = evict + 1; k < t->undo_count; ++k) {
      t->undo_stack[k - 1] = t->undo_stack[k];
    }
    t->undo_count--;
    le_publish_undo_depth(t);
  }
  return slot;
}

/* How many shadow slots control keeps posted to the audio thread per capturing
 * track: the armed one plus one spare, so a pass boundary can rotate without
 * waiting a control round-trip. */
#define LE_DUB_SHADOWS 2

/* The track's SETTLED loop length, or 0 when it has none yet. A track still
 * RECORDING publishes a_len as its GROWING record position (the per-block
 * publish in engine_process.c), not the final loop length — so a_len must never
 * be used to size an undo-layer slot mid-capture. The pass that fills such a
 * slot covers the FINAL length (le_dub_session_start latches dub_len at
 * finalize), so a slot sized to a partial length would be written past its end
 * by the audio thread's backup-on-write. Callers read 0 as "not settled": size
 * at the cap, and don't resize. */
static int32_t le_track_settled_len(le_track* t) {
  if (load_i32(&t->a_state) == LE_TRACK_RECORDING) return 0;
  return load_i32(&t->lanes[0].a_len);
}

/* The buffer an undo layer for a settled `len`-frame loop needs: the length
 * rounded up to LE_LAYER_QUANTUM, capped at the recording cap — a 2 s loop's
 * layer costs ~2 s of floats, not the cap. `len <= 0` (not settled — a pre-arm
 * posted while the loop is still being recorded) can only be served by the full
 * cap; le_handle_retired shrinks such a slot back to size once its pass retires
 * and the real length is known. */
static int32_t le_layer_slot_frames(const le_engine* engine, int32_t len) {
  if (len <= 0) return engine->max_loop_frames;
  const int32_t want =
      ((len + LE_LAYER_QUANTUM - 1) / LE_LAYER_QUANTUM) * LE_LAYER_QUANTUM;
  return want > engine->max_loop_frames ? engine->max_loop_frames : want;
}

/* Tops the track's posted shadow slots up to `target` (control thread):
 * acquires a free pool slot, lazily allocates its buffer on every active lane,
 * and posts it via LE_CMD_DUB_SHADOW. Push-then-mutate: the slot only becomes
 * `outstanding` once the ring accepted the command (a lazily allocated buffer
 * stays in the pool either way). The audio thread arms the slot as its next
 * shadow; the ring's release/acquire publishes the fresh buffers, exactly like
 * the fx delay-line pattern.
 *
 * `target` is LE_DUB_SHADOWS (armed + spare) for a running dub session, but 1
 * for a pre-arm during RECORDING: the length is not settled there, so each slot
 * costs the full recording cap, and only the first wrap's pass needs one — its
 * spare arrives from the running session's replenish right after finalize, when
 * the length is settled and the slot is loop-length-quantized. Capped at
 * LE_DUB_SHADOWS. */
static void le_post_dub_shadows(le_engine* engine, int32_t channel,
                                int32_t target) {
  le_track* t = &engine->tracks[channel];
  /* Old callback shadows remain owned until the pending Clear completes. */
  if (t->clear_restore_pending) return;
  const int32_t lanes = le_lanes_active(t);
  const int32_t want = le_layer_slot_frames(engine, le_track_settled_len(t));
  if (target > LE_DUB_SHADOWS) target = LE_DUB_SHADOWS;
  while (t->outstanding_count < target) {
    const int slot = track_acquire_slot(t);
    if (slot < 0) return; /* pool exhausted beyond eviction: skip boundaries */
    int ok = 1;
    for (int32_t l = 0; l < lanes; ++l) {
      if (!le_lane_ensure_slot(&t->lanes[l], slot, want)) {
        ok = 0; /* OOM: do not post a torn slot */
      }
    }
    if (!ok) return;
    if (le_push_cmd(engine, (le_command){.code = LE_CMD_DUB_SHADOW,
                                         .lanei = {channel, 0, slot}}) !=
        LE_OK) {
      return; /* ring full: try again on the next drain/press */
    }
    t->outstanding_slots[t->outstanding_count++] = slot;
  }
}

/* Whether a fresh capture on [channel] is bound to continue straight into
 * overdub, so its shadow slots are worth pre-arming during RECORDING — letting
 * the first wrap's pass back up on write and retire as its own undo layer
 * instead of merging into the base. rec/dub mode continues any second-press
 * finalize into overdub, so any capture qualifies when it is on. With rec/dub
 * off, only a non-defining capture (master already exists) with a fixed loop
 * multiple auto-finalizes into overdub; a defining capture, or one with an auto
 * multiple, finalizes to playback and is skipped so it never strands a pre-armed
 * slot (cap-sized, since the length is unknown until finalize).
 *
 * Known, deliberate exclusion: an auto-multiple capture that records all the
 * way to the buffer cap rolls into overdub (advance_transport_frame's
 * record_pos >= max_loop_frames auto-finalize) with no pre-armed slot, so that
 * first wrap merges into the base — the pre-fix behaviour. Covering it would
 * mean pre-arming every auto-multiple capture, stranding a cap-sized slot on
 * the common record-to-playback flow, to benefit only a capture held for the
 * entire cap (30 s+) without a press.
 *
 * `has_master` comes from the CALLER, never re-read from a_master_len here: a
 * caller that just pushed the internal grid-redefine CLEAR (le_engine_record's
 * fresh-take branch) already knows the capture will be defining, while the
 * atomic stays stale until the audio thread applies that CLEAR — re-reading it
 * would pre-arm exactly the defining capture this gate exists to skip. */
static int le_capture_may_overdub(le_engine* engine, int32_t channel,
                                  int has_master) {
  if (engine->rec_dub) return 1;
  if (!has_master) return 0;
  return le_effective_multiple(engine, channel) > 0;
}

/* Pushes onto the redo stack, refusing rather than running off the end.
 *
 * Most entries name a distinct pool slot, so live + undo + redo + outstanding <=
 * LE_POOL_SLOTS bounds the stacks implicitly. Two pushes escape that bound by
 * naming the ALREADY-live slot and consuming no new one: undo-to-empty's, and
 * the clear restore point's (#219). Today the totals still fit — LE_DUB_SHADOWS
 * keeps 2 slots outstanding while dubbing, so undo tops out at LE_POOL_SLOTS - 3
 * and redo peaks one index short of the end — but that is a one-slot margin
 * resting on a constant that has nothing to do with undo. Bound it explicitly
 * instead of leaving the arrays safe by coincidence. */
static int le_redo_push(le_track* t, le_hist_entry e) {
  if (t->redo_count >= LE_POOL_SLOTS) return 0;
  t->redo_stack[t->redo_count++] = e;
  return 1;
}

/* One undo step on a track that has stacked layers (control thread): swap the
 * live pool index back to the top undo snapshot and push the previous live onto
 * the redo stack — every active lane in lockstep (the one undo span). The
 * caller has verified the track is not capturing and no layer is in flight.
 *
 * The redo push cannot fail here: it moves one entry off the undo stack for the
 * one it adds, so the total is unchanged. Losing the redo step would still beat
 * corrupting the struct, hence the guard rather than an assert.
 *
 * Capture provenance (#1143): the target slot is staged as an immutable image
 * BEFORE it is published, so the callback can name exactly the PCM that became
 * audible at the frame it first mixes it. Staging refusal never refuses the
 * swap (D5); the stem then fails truthfully (323/0). */
static uint32_t le_stage_source_image(le_engine* engine, int32_t channel,
                                      int32_t slot, int32_t len);

static void le_undo_swap(le_engine* engine, le_track* t) {
  const le_hist_entry top = t->undo_stack[--t->undo_count];
  const int32_t live = load_i32(&t->lanes[0].a_live);
  const uint32_t id = le_stage_source_image(
      engine, (int32_t)(t - engine->tracks), top.slot,
      load_i32(&t->lanes[0].a_len));
  if (top.kind == LE_HIST_PEEL) {
    /* Undo of a Peel (#1164): the image Peel removed comes back live, and the
     * LAYER it consumed is re-inserted `skipped` entries below the PEEL's
     * position — beneath the PEEL entries that sat above it at peel time — so
     * the stack is exactly what it was before that peel and history stays
     * chronological across repeated peels and later overdubs. Clamped to the
     * bottom: pool eviction removes the lowest entries first, so the entries
     * between the insertion point and the PEEL can only have vanished once
     * nothing lay below them. The redo marker (slot -1) re-peels. */
    const int p = t->undo_count;
    int insert = p - top.skipped;
    if (insert < 0) insert = 0;
    for (int k = p; k > insert; --k) t->undo_stack[k] = t->undo_stack[k - 1];
    t->undo_stack[insert] = le_hist_layer(live);
    t->undo_count++;
    (void)le_redo_push(t, le_hist_kind_entry(LE_HIST_PEEL, -1, top.skipped));
  } else {
    /* LAYER and PROCESSED: the redo entry keeps the kind, so a redo re-files
     * a restoration swap as PROCESSED rather than as a peelable layer. */
    (void)le_redo_push(t, le_hist_kind_entry(top.kind, live, 0));
  }
  le_publish_live_image(engine, t, top.slot, id, 1); /* [R1] undo swap */
  le_publish_undo_depth(t);
  store_i32(&t->a_redo_depth, t->redo_count);
}

/* The Peel motion (#1164), shared by le_engine_peel and the redo of a PEEL
 * marker: removes the LAYER at `idx` (the `skipped` PEEL entries above it
 * shift down one), pushes PEEL{former live, skipped} on top, and publishes
 * the LAYER's slot live on every lane. The stack count is unchanged and every
 * slot stays referenced exactly once (track_select_slot's uniqueness scan).
 * Never allocates or writes PCM: Peel only moves between images that already
 * exist. The target is staged before it is published (#1143) so a running
 * capture replays the swap exactly. Depths and the redo branch are the
 * callers' to settle. */
static void le_peel_apply(le_engine* engine, le_track* t, int idx,
                          int32_t skipped) {
  const int32_t target = t->undo_stack[idx].slot;
  const int32_t live = load_i32(&t->lanes[0].a_live);
  const uint32_t id = le_stage_source_image(
      engine, (int32_t)(t - engine->tracks), target,
      load_i32(&t->lanes[0].a_len));
  for (int k = idx + 1; k < t->undo_count; ++k) {
    t->undo_stack[k - 1] = t->undo_stack[k];
  }
  t->undo_stack[t->undo_count - 1] =
      le_hist_kind_entry(LE_HIST_PEEL, live, skipped);
  le_publish_live_image(engine, t, target, id, 1); /* [R1] peel swap */
}

/* #595: drops every lane's recoverable flag once NOTHING on this track can
 * come back — no live take (len 0), no undo history (which includes a clear
 * restore point: the shadow that keeps a wiped-looking take one undo away),
 * and no redo. Anything short of all three keeps the flags: a stale 1 only
 * declines a lane trim, a wrong 0 lets the trim eat a restorable take (the
 * #594 failure), so every guard errs toward keeping. Called after the history
 * mutations that can only shrink the ways back (redo invalidation, restore-
 * point drops, the plain clear); per-lane granularity comes from the SET side
 * (only writing lanes ever latch), not from here. */
static void le_track_drop_recoverable_if_dead(le_track* t) {
  if (load_i32(&t->lanes[0].a_len) > 0) return;
  if (t->undo_count > 0 || t->redo_count > 0) return;
  /* A frozen take's restore point is still to be filed (LE_EVT_CLEAR_FROZEN):
   * the live slot it will name must stay allocated. */
  if (t->clear_restore_pending) return;
  for (int l = 0; l < LE_MAX_LANES; ++l) {
    store_i32(&t->lanes[l].a_recoverable, 0);
  }
}

/* Clears a track's redo history (control thread) — a fresh action (punch-in,
 * new recording, session import) invalidates the resurrect path, including the
 * undone-to-empty length. */
static void le_clear_redo(le_track* t) {
  t->redo_count = 0;
  t->empty_len = 0;
  store_i32(&t->a_redo_depth, 0);
  le_track_drop_recoverable_if_dead(t); /* #595: the resurrect path died */
}


/* Drops a track's clear restore point(s) and the erased take beneath them
 * (control thread). A fresh capture on this track is about to record into the
 * live slot a restore point names (le_begin_empty_capture regrows and the audio
 * thread writes pool[live] in place), so the way back is gone whether or not the
 * bookkeeping admits it — and the layers under the mark belong to the erased
 * take, which the new recording replaces wholesale. Dropping both restores the
 * pre-#219 semantic exactly: after clear-then-record, undo depth is 0. */
static void le_drop_clear_history(le_track* t) {
  /* A frozen take still waiting for its Clear completion
   * is about to be recorded over too: the point can never be filed, and the
   * layers kept beneath it belong to the erased take — they go with it. */
  if (t->clear_restore_pending) {
    t->clear_restore_pending = 0;
    t->undo_count = 0;
    le_publish_undo_depth(t);
    le_track_drop_recoverable_if_dead(t);
    return;
  }
  if (!le_history_is_cleared(t)) return;
  t->undo_count = 0;
  le_publish_undo_depth(t);
  le_track_drop_recoverable_if_dead(t); /* #595: the way back is gone */
}

/* le_effective_state — the track's effective state for control-side decisions
 * — moved to engine_core.h (static inline): the wet-cache scheduler's enqueue
 * gate (engine_cache.c) decides from the same predicate and the two must
 * never diverge. */

/* Commits a completed loop-close restoration (#697 S9) as ONE lockstep undo
 * layer — declared in engine_restore.h, defined HERE so it reuses the undo /
 * pool machinery above (track_acquire_slot, le_clear_redo, le_hist_layer,
 * le_publish_undo_depth, le_track_publish_live) rather than duplicating it.
 * Control thread only; the audio thread is untouched (a_live is swapped by a
 * single release store, and no buffer it can hold is freed — the pre-restore
 * live slot lives on as the pushed undo layer). See the header for the full
 * contract. */
int32_t le_restore_commit_layer(le_engine* engine, int32_t channel,
                                uint32_t lane_mask, uint32_t audio_rev,
                                int32_t len,
                                float* const restored[LE_MAX_LANES]) {
  if (engine == NULL || channel < 0 || channel >= engine->track_count) {
    return LE_ERR_INVALID;
  }
  le_track* t = &engine->tracks[channel];
  /* The same gate the enqueue used, re-checked at commit: a capture may have
   * started since. */
  const int32_t est = le_effective_state(t);
  if (est != LE_TRACK_PLAYING && est != LE_TRACK_STOPPED) return LE_ERR_INVALID;
  if (atomic_load_explicit(&t->a_layer_in_flight, memory_order_acquire) ||
      t->length_pending) {
    return LE_ERR_INVALID;
  }
  /* [B5]: the take must not have moved since the worker copied it. */
  if (atomic_load_explicit(&t->a_audio_rev, memory_order_acquire) != audio_rev) {
    return LE_ERR_INVALID;
  }
  const int32_t live = load_i32(&t->lanes[0].a_live);
  if (len <= 0 || load_i32(&t->lanes[0].a_len) != len) return LE_ERR_INVALID;

  const int32_t lanes = le_lanes_active(t);
  const int32_t slot = track_acquire_slot(t);
  if (slot < 0) return LE_ERR_INVALID; /* pool exhausted beyond eviction */

  /* Fill the fresh slot on every active lane: the restored PCM where opted,
   * else a plain copy of the current live buffer (safe to read on this thread
   * — the gate above proves the audio thread is not writing pool[live]). */
  for (int32_t l = 0; l < lanes; ++l) {
    if (!le_lane_ensure_slot(&t->lanes[l], slot, len)) {
      /* OOM: abandon the commit. track_acquire_slot only returns a free slot
       * (never referenced by a_live / undo / redo / outstanding), so leaving
       * it partially allocated in the pool is harmless — nothing names it. */
      return LE_ERR_INVALID;
    }
    float* dst = t->lanes[l].pool[slot];
    const float* src = t->lanes[l].pool[live];
    if ((lane_mask & (1u << l)) && restored[l] != NULL) {
      memcpy(dst, restored[l], (size_t)len * sizeof(float));
    } else if (src != NULL) {
      memcpy(dst, src, (size_t)len * sizeof(float));
    } else {
      memset(dst, 0, (size_t)len * sizeof(float));
    }
  }

  /* A fresh action invalidates any redo path, exactly like a punch-in. */
  le_clear_redo(t);
  /* Push the pre-restoration live slot as one lockstep undo entry so a plain
   * le_engine_undo swaps the restoration back to the raw take (the retention
   * model the plan specifies: in-session undo, no session-bundle change).
   * Filed as PROCESSED, not LAYER (#1164): a conditioning swap is not an
   * overdub, so Peel must never consume it as one — a full-length raw take
   * swapped under a conditioned image would not be "the newest overdub". */
  if (t->undo_count < LE_POOL_SLOTS) {
    t->undo_stack[t->undo_count++] =
        le_hist_kind_entry(LE_HIST_PROCESSED, live, 0);
  }
  le_publish_undo_depth(t);
  /* Swap a_live to the restored slot on every lane + bump a_audio_rev in one
   * motion (invalidating and re-rendering the wet cache). Image 0 (#1143):
   * processed material has no staged copy, so a running capture's stem fails
   * truthfully at this swap (323/0) instead of replaying the raw take. */
  le_publish_live_image(engine, t, slot, 0, 0);
  return LE_OK;
}

/* Marks a successfully posted state-flip command (control thread). */
static void le_mark_state_cmd(le_track* t, int32_t target) {
  t->state_cmds_posted++;
  t->pending_target = target;
  t->pending_len = 0; /* the posters that restore a length set it after */
  t->pending_master_len = 0;
}

/* Marks a successfully posted command that EMPTIES the track: the state flip
 * plus the publication ticket a later fresh capture needs before it may free,
 * regrow or zero this track's PCM (#1146, le_track.empty_command). Called
 * after the push, so commands_posted already counts that command. */
static void le_mark_empty_cmd(le_engine* engine, le_track* t) {
  le_mark_state_cmd(t, LE_TRACK_EMPTY);
  t->empty_command = engine->commands_posted;
}

/* Tickets a successfully posted command that can empty [channel] on the audio
 * thread WITHOUT a state command of its own: a cancellation that reaches a
 * take inside its launch grace (DISARM, STOP_RECORD_CONTROL, CANCEL_COUNT_IN
 * -> handle_record -> apply_undo_to_empty), or a stop/finish that finalizes a
 * RECORDING take which captured nothing (finalize_new_track's void take ->
 * EMPTY). Unconditional on purpose: the control view cannot tell a void take
 * from a kept one (a RECORD posted in the same block still reads EMPTY here),
 * and a ticket on a track that keeps its content is never consulted — the
 * guard reads it only while the track is EMPTY, and the next emptying
 * re-tickets. Called after the push, so commands_posted counts the command. */
static void le_ticket_emptying(le_engine* engine, int32_t channel) {
  if (channel < 0 || channel >= engine->track_count) return;
  engine->tracks[channel].empty_command = engine->commands_posted;
}

/* DISARM empties a track only through its launch: a take inside its grace
 * (handle_record -> apply_undo_to_empty), or a pending launch the count-in may
 * commit before the DISARM applies. An ordinary arm cancellation empties
 * nothing, and must stay re-armable within the same block. */
/* Whether [t] has a launch a press may only cancel: a Count-in deferral
 * pending, or a committed take inside its cancellation grace. Pending first,
 * then grace, both acquire: le_count_in_commit stores the grace (release)
 * before it clears the pending flag (release), so a clear read here implies
 * the grace store is visible — no instant exists where a cancellable launch
 * reads as neither. Every control-side reader of the pair goes through this
 * one helper so none of them re-introduces the relaxed, unordered read. */
static int le_launch_cancellable(le_track* t) {
  return atomic_load_explicit(&t->a_pending_launch, memory_order_acquire) ||
         atomic_load_explicit(&t->a_launch_grace, memory_order_acquire);
}

static void le_ticket_launch_cancel(le_engine* engine, int32_t channel) {
  if (channel < 0 || channel >= engine->track_count) return;
  if (le_launch_cancellable(&engine->tracks[channel])) {
    le_ticket_emptying(engine, channel);
  }
}

/* The master grid a clear on [t] must record for its restore point: what an
 * in-flight restore on this track is about to re-establish, else the wire's
 * — the grid twin of le_effective_len. */
static int32_t le_effective_master_len(le_engine* engine, le_track* t) {
  if (t->state_cmds_posted >
          atomic_load_explicit(&t->a_state_acks, memory_order_acquire) &&
      t->pending_master_len > 0) {
    return t->pending_master_len;
  }
  return load_i32(&engine->a_master_len);
}

/* The master grid the rig runs once every posted restore has landed: the
 * wire's, or the master a clear point being restored on any track is about to
 * re-establish while the wire still reads none — the rig-wide twin of
 * le_effective_master_len, for a press that must know whether it defines the
 * grid or records over one (a record behind a queued restore of the only
 * take). */
static int32_t le_rig_effective_master_len(le_engine* engine) {
  /* A posted re-clock (#1168) moves a nonzero master too: measure behind it. */
  for (int32_t c = 0; c < engine->track_count; ++c) {
    le_track* o = &engine->tracks[c];
    if (o->length_pending && o->pending_master_len > 0 &&
        o->state_cmds_posted >
            atomic_load_explicit(&o->a_state_acks, memory_order_acquire)) {
      return o->pending_master_len;
    }
  }
  const int32_t wire = load_i32(&engine->a_master_len);
  if (wire > 0) return wire;
  for (int32_t c = 0; c < engine->track_count; ++c) {
    le_track* o = &engine->tracks[c];
    if (o->state_cmds_posted >
            atomic_load_explicit(&o->a_state_acks, memory_order_acquire) &&
        o->pending_master_len > 0) {
      return o->pending_master_len;
    }
  }
  return 0;
}

/* The control thread's view of a track's length: what a posted-but-unapplied
 * state command will publish (a restore's take length, an emptying's 0), or
 * the published length once everything posted has been acked — the length
 * twin of le_effective_state, so a decision made in the gap (a clear right
 * behind a restore) measures the take it will find. */
static int32_t le_effective_len(le_track* t) {
  if (t->state_cmds_posted >
      atomic_load_explicit(&t->a_state_acks, memory_order_acquire)) {
    return t->pending_len;
  }
  return load_i32(&t->lanes[0].a_len);
}

/* Defined below with the quantize machinery; needed by the undo-to-empty
 * paths so a pending arm can't fire a surprise recording on an emptied track.
 * Returns the DISARM push result (LE_OK when there was no arm to cancel) —
 * the internal callers discard it, le_engine_cancel_arm reports it. */
static int32_t le_cancel_arm(le_engine* engine, int32_t channel);
static int32_t le_post_clock_command(le_engine* engine, int32_t code,
                                       int32_t value);

/* #595: trailing-lane reclaim, defined below but called from the event drain
 * (le_engine_drain_events) as well as the un-route itself. */
static int le_trim_trailing_lanes(le_engine* engine, int32_t channel,
                                   int32_t unrouted_lane);
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
