tomassasovsky/segno/packages/segno_engine/src/core/engine_process.c

/*
 * engine_process.c — THE AUDIO-THREAD TU.
 *
 * Everything the device callback runs lives here and nowhere else: the real-time
 * contract holds for this whole file — no malloc/free, no locks, no syscalls, no
 * unbounded loops. le_engine_process is the block processor the miniaudio / ASIO
 * data callback pumps; it drains the SPSC command ring (apply_command), advances
 * the transport state machine (the finalize_* / handle_* helpers), records /
 * overdubs / mixes, runs the per-lane effect chains (fx_apply_chain), resolves the
 * loopback latency harness, and publishes metering + visualization atomics.
 *
 * Split verbatim out of engine.c (S1) behind the unchanged ABI. The transport
 * handlers live here rather than in a separate engine_transport.c because they run
 * ON the audio thread (invoked only by apply_command and le_engine_process); the
 * control-thread record/undo entry points (le_engine_record etc.) are in
 * engine_commands.c. Shared low-level helpers (valid_channel, le_track_set_len,
 * comp_pos, le_lanes_active) come from engine_core.h; the chain runner from
 * engine_fx.h.
 */
#include <math.h>
#include <stdint.h>
#include <string.h>
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
